ProGenEDA/ProGenEDA-DEV/proteus/experiments/runs/2026-07-17_executable_gate_overlay_trial/current_app_gate_bridge/ss/H02_8/H02_8_G_cold_open_2.png

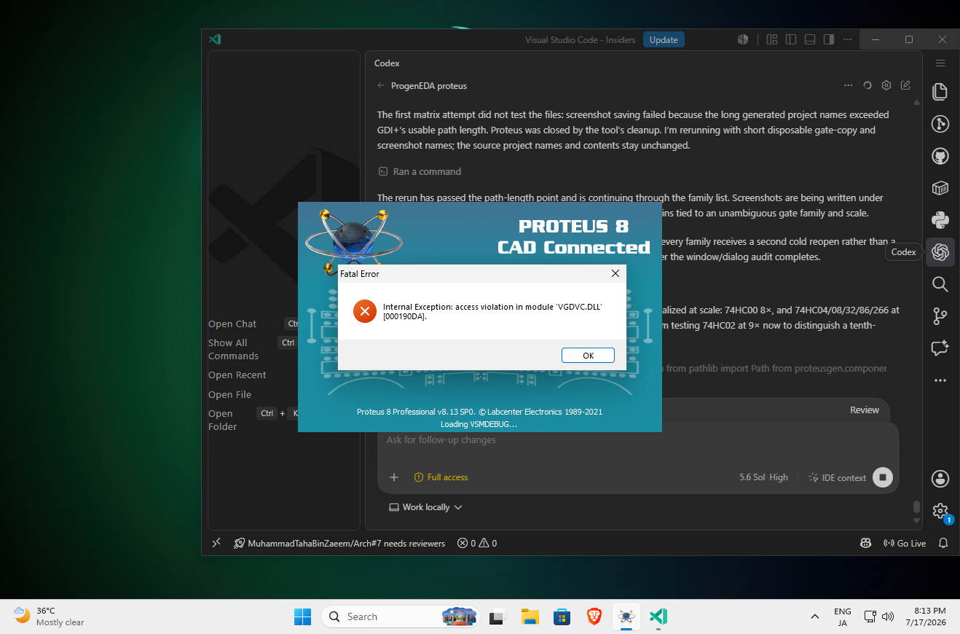
proteus/experiments/runs/2026-07-17_executable_gate_overlay_trial/current_app_gate_bridge/ss/H02_8/H02_8_G_cold_open_2.png
