ProGenEDA/ProGenEDA-DEV/showcase/EasyEDA_10_Most_Complex_2026_07_19/README.md

# EasyEDA Top 10 Complex Showcase

These are ten distinct, highest-complexity named application archetypes freshly
generated on 2026-07-19 through the latest portable `progen-easyeda` executable
from the EasyEDA website handoff, in `combination` routing mode. Every listed
native `.eprj` has a passing pipeline and independent validation report.

Open the linked `.eprj` directly in EasyEDA Pro. Each generated project folder
also keeps the fixed input, donor provenance, placement, routing, PCB decision,
and validation reports.

| Circuit | Components | Nets | Pins | Project |
| --- | ---: | ---: | ---: | --- |
| Multi-MCU Communications Bridge | 23 | 110 | 250 | [`Q11`](generated/2026_07_19_233505_339666_q11_dual_mcu_bridge_validation_v10/q11_dual_mcu_bridge_validation_v10.eprj) |
| Combinational and Sequential Logic Trainer | 23 | 81 | 186 | [`Q30`](generated/2026_07_19_233523_208561_q30_digital_logic_trainer_validation_v10/q30_digital_logic_trainer_validation_v10.eprj) |
| ESP32 Multi-channel PWM Controller | 20 | 80 | 187 | [`Q05`](generated/2026_07_19_233525_353656_q05_esp32_pwm_controller_validation_v10/q05_esp32_pwm_controller_validation_v10.eprj) |
| STM32 Precision Data Acquisition Unit | 19 | 73 | 169 | [`Q10`](generated/2026_07_19_233529_347101_q10_stm32_data_acquisition_validation_v10/q10_stm32_data_acquisition_validation_v10.eprj) |
| ATmega Logic Sequencer | 19 | 63 | 152 | [`Q07`](generated/2026_07_19_233537_870979_q07_atmega_logic_sequencer_validation_v10/q07_atmega_logic_sequencer_validation_v10.eprj) |
| ESP32 Environmental Data Logger | 19 | 63 | 148 | [`Q01`](generated/2026_07_19_233541_072041_q01_esp32_environment_logger_validation_v10/q01_esp32_environment_logger_validation_v10.eprj) |
| Shift Register LED Display Driver | 19 | 52 | 128 | [`Q23`](generated/2026_07_19_233546_585906_q23_shift_register_display_validation_v10/q23_shift_register_display_validation_v10.eprj) |
| ESP32 OLED Control Panel | 18 | 64 | 141 | [`Q04`](generated/2026_07_19_233548_034172_q04_esp32_oled_panel_validation_v10/q04_esp32_oled_panel_validation_v10.eprj) |
| STM32 CAN Control Node | 18 | 57 | 138 | [`Q08`](generated/2026_07_19_233553_642171_q08_stm32_can_controller_validation_v10/q08_stm32_can_controller_validation_v10.eprj) |
| ATmega USB Serial Controller | 17 | 59 | 140 | [`Q06`](generated/2026_07_19_233601_752383_q06_atmega_usb_controller_validation_v10/q06_atmega_usb_controller_validation_v10.eprj) |
