ProGenEDA/ProGenEDA-DEV/showcase/KiCad_10_Most_Complex_2026_07_19/README.md

# KiCad Top 10 Complex Showcase

These are ten distinct, high-complexity production-validation circuits freshly
generated on 2026-07-19 through the final
`progen-kicad-portable-2026_07_17_kq26_clearance_v1` executable in
`combination` routing mode. Each listed project has a passing
`final_validation_report.json`; PCB output is present only where the bounded
physical stage accepted it.

Open the listed `.kicad_pro` project file. Every project also retains its input,
placement/routing data, expected-net report, final report, and internal output
artifacts beside it.

| Circuit | Components | Nets | Pins | Project |
| --- | ---: | ---: | ---: | --- |
| Maker Logic and Display Console | 89 | 56 | 275 | [`KQ34V10`](final_individual_runs/progen_kicad_executable_run_2026_07_19_233002_kq34v10_top10_showcase_v1/generation/projects/kq34v10/OPEN_THIS_PROJECT__kq34v10__COMBINATION.kicad_pro) |
| Maker Audio Instrument | 85 | 48 | 217 | [`KQ33V10`](final_individual_runs/progen_kicad_executable_run_2026_07_19_232851_kq33_top10_showcase_v1/generation/projects/kq33v10/OPEN_THIS_PROJECT__kq33v10__COMBINATION.kicad_pro) |
| IoT Sensor and Display Controller | 80 | 54 | 275 | [`KQ39V10`](final_individual_runs/progen_kicad_executable_run_2026_07_19_233049_kq39v10_top10_showcase_v1/generation/projects/kq39v10/OPEN_THIS_PROJECT__kq39v10__COMBINATION.kicad_pro) |
| Maker CAN and RS485 Field Gateway | 80 | 47 | 217 | [`KQ32V10`](final_individual_runs/progen_kicad_executable_run_2026_07_19_233056_kq32v10_top10_showcase_v1/generation/projects/kq32v10/OPEN_THIS_PROJECT__kq32v10__COMBINATION.kicad_pro) |
| ESP32 Sensor and Actuator Controller | 75 | 45 | 211 | [`KQ35V10`](final_individual_runs/progen_kicad_executable_run_2026_07_19_233220_kq35v10_top10_showcase_v1/generation/projects/kq35v10/OPEN_THIS_PROJECT__kq35v10__COMBINATION.kicad_pro) |
| Powered Maker Development Platform | 69 | 35 | 171 | [`KQ31V10`](final_individual_runs/progen_kicad_executable_run_2026_07_19_233228_kq31v10_top10_showcase_v1/generation/projects/kq31v10/OPEN_THIS_PROJECT__kq31v10__COMBINATION.kicad_pro) |
| Industrial Sensor Communications Gateway | 66 | 41 | 200 | [`KQ37V10`](final_individual_runs/progen_kicad_executable_run_2026_07_19_233311_kq37v10_top10_showcase_v1/generation/projects/kq37v10/OPEN_THIS_PROJECT__kq37v10__COMBINATION.kicad_pro) |
| Arduino Field Motion Controller | 63 | 50 | 182 | [`KQ10V10`](final_individual_runs/progen_kicad_executable_run_2026_07_19_233331_kq10v10_top10_showcase_v1/generation/projects/kq10v10/OPEN_THIS_PROJECT__kq10v10__COMBINATION.kicad_pro) |
| Industrial Power and Motion Controller | 62 | 39 | 161 | [`KQ40V10`](final_individual_runs/progen_kicad_executable_run_2026_07_19_233348_kq40v10_top10_showcase_v1/generation/projects/kq40v10/OPEN_THIS_PROJECT__kq40v10__COMBINATION.kicad_pro) |
| Sensor Hub with Logic Display | 58 | 36 | 202 | [`KQ21V10`](final_individual_runs/progen_kicad_executable_run_2026_07_19_233353_kq21v10_top10_showcase_v1/generation/projects/kq21v10/OPEN_THIS_PROJECT__kq21v10__COMBINATION.kicad_pro) |

`final_individual_runs/` is the curated current set. `generated/` preserves an
earlier partial batch attempt and is not part of the showcase selection.
