ProGenEDA/ProGenEDA-DEV/kicad/examples/schematic_terminal_visual_run_2026_07_12_071500_final_complex20_v19/README.md

# Final JSON To KiCad Terminal Project Run

This folder is an immutable generated record. It takes connected final JSON files, runs the arrangement decider, beautifier, routing/terminal planner, and KiCad backend emitter, then writes openable KiCad projects with real embedded symbols plus wire objects. Terminal/local-label objects are only valid when the run is generated in terminal or combination mode.

The wire planner is fed exact KiCad source-symbol pin points through `routing_inputs/` when those pins can be resolved. The wire maker uses the same source-backed KiCad pin geometry when possible. Any unresolved pin aliases, unroutable nets, strict-wire connectivity violations, local expected-net comparison failures, wire crossings, and wire/component body contacts are recorded in each project manifest.

Each project also has a two-artifact output boundary under `outputs/<circuit_id>/`: `user_project/PROGEN_KICAD_PROJECT.zip` is the only user-downloadable export, while `internal/internal_bundle.zip` is backend-only metadata containing the main input JSON, all generated stage JSON, validation reports, and retained arrangement variants with the accepted variant marked.
