ProGenEDA/ProGenEDA-DEV/proteus/active/docs/README.md

# Proteus Active Documentation

> **Current implementation.** This folder is the active Proteus documentation index
> for the repaired component placer, shared terminal route, grid-attached wire
> contract, automated validation workflow, value/properties editor, and
> portable executable.

Updated: 2026-07-16

Start with [`../README.md`](../README.md) for commands, support boundaries, the
runtime donor policy, release executable, and links to experiments/archive.

## Current operational documents

- [`progen_eda_canonical_pipeline.md`](progen_eda_canonical_pipeline.md) —
  owner-defined stage order and implementation map.
- [`architecture.md`](architecture.md) — replaceable stage contracts, catalogue
  policy, and current architecture decisions.
- [`component_placer_pipeline.md`](component_placer_pipeline.md) — the
  donor-backed placement contract.
- [`beautifier.md`](beautifier.md) — coordinate/arrangement stage contract.
- [`validator_design.md`](validator_design.md) — cumulative validation stages.
- [`generator_design.md`](generator_design.md) — generator responsibilities.
- [`current_limitations_bridges_costs_and_roadmap.md`](current_limitations_bridges_costs_and_roadmap.md)
  — promoted boundaries and next work.
- [`prompts/planner_prompt.md`](prompts/planner_prompt.md) — current prompt
  planning input.

## Active evidence and validation

- [`../knowledge/component_catalog_v0.json`](../knowledge/component_catalog_v0.json)
  — current catalogue/profile source.
- [`../knowledge/terminal_placement_preflight_checklist.md`](../knowledge/terminal_placement_preflight_checklist.md)
  — required donor/loader checklist before terminal changes.
- [`../knowledge/value_and_properties_editor_preflight_2026_07_16.md`](../knowledge/value_and_properties_editor_preflight_2026_07_16.md)
  — value editor evidence.
- [`../evidence/registry/active_donor_closure.json`](../evidence/registry/active_donor_closure.json)
  — deterministic runtime/test donor closure.
- [`../REPOSITORY_MAP.md`](../REPOSITORY_MAP.md) — active/experiment/archive map
  and generated hashes.

Historical reports, older handoffs, and donor-learning notes were deliberately
preserved unchanged under [`../../archive/docs`](../../archive/docs), while
dated generated packs and their runners live under
[`../../experiments`](../../experiments).
