ProGenEDA/ProGenEDA-DEV/proteus/active/release/README.md

# ProgenProteus.exe

> **Current implementation.** The active Proteus system includes repaired component placement, unified terminal placement, grid-attached short-wire behavior, automated local Proteus validation, the value/properties editor, the portable executable, and consolidated active documentation.
>
> **Active-location update — 2026-07-16.** This is current Proteus material. Pre-consolidation root-relative paths translate as follows: `src/`, `knowledge/`, `fixtures/`, `schemas/`, `examples/`, and active `tools/` are below `proteus/active/`; `experiments/` is below `proteus/experiments/runs/`; and `proteus_ic/{donors,registry}` is now `proteus/active/evidence/{donors,registry}`. For current commands, support boundaries, and limitations, start at `proteus/active/README.md`.

`ProgenProteus.exe` is the portable Windows console application for the
implemented Proteus pipeline:

`component placement -> beautification -> shared terminal placement -> optional post-terminal value/properties edit`

It bundles the locked mega donor, terminal templates, and the metadata needed
by the shared placer. It does not bundle or call any KiCad code.

## Run

```powershell
.\ProgenProteus.exe generate ..\examples\progen_proteus_r_c_value_edit.json --output .\r_c_terminalized.pdsprj
```

Other commands:

```powershell
.\ProgenProteus.exe --help
.\ProgenProteus.exe inspect .\r_c_terminalized.pdsprj
.\ProgenProteus.exe edit-values .\r_c_terminalized.pdsprj --edits edits.json --output .\edited.pdsprj
```

The executable refuses physical-net requests because the shared Proteus Wire
Maker has not yet been implemented. It also rejects unsafe zero-length
terminal-to-pin wires and, by default, any request that would silently leave a
family unterminated. Use `--allow-unterminalized` only for an intentional
mixed control project.

`NPN` is included in this build's locked non-IC terminal route. Its fresh
executable evidence covers solo `1x`, `9x`, and `15x`, asymmetric native mixes,
existing catalogue-backed non-IC mixes, and a `15x` NPN/diode/resistor/capacitor
stress mix. Each emitted NPN terminal has a grid-aligned, nonzero short WIRE
to its exact pin. IC/display mixtures remain on their independently verified
routes and are not widened by this NPN promotion.

`PNP` is included in this build's locked non-IC terminal route too. Its
`BASE`/`COLLECTOR`/`EMITTER` pin attachments passed fresh `1x`, `9x`, `15x`,
asymmetric, heterogeneous, and latest-executable `15x` stress gates. The
portable executable also uses a bounded temporary work-directory prefix, so a
descriptive output filename cannot consume the Windows path budget before
placement and terminalization begin.

`NMOSFET` is included in this build's locked non-IC terminal route. Its
donor-proven `DRAIN`/`SOURCE` right-side and `GATE` left-side attachment units
passed the full staged loader proof, `1x`/`9x`/`15x` solo gates, a ratio mix,
a heterogeneous non-IC mix, and a dense 15x stress mix. Every emitted NMOSFET
terminal has a grid-aligned contact and a nonzero short WIRE to its exact pin.

`2N3904` is included in the same locked non-IC terminal route. Its accepted
combined donor proves that its `EMITTER`/`COLLECTOR`/`BASE` attachment tail
must follow the complete placed component stream. Fresh `1x`/`9x`/`15x` solos,
asymmetric and heterogeneous mixes, a dense 15-per-family mix, and a fresh
portable-executable ratio mix all passed normal open and cold reopen with
grid-aligned, nonzero terminal-to-pin WIREs.

`2N4401` is included in this build through the same shared route. Its
independent accepted donor proves its `COLLECTOR`/`EMITTER`/`BASE` tail follows
the whole placed stream. The staged 1x proof, 9x/15x solos, additive and
asymmetric ratios, a heterogeneous 24-component mix, and a dense 15-per-family
mix passed the local two-open Proteus gate. The rebuilt executable itself is
gated below before this release note is finalized.

For a canonical placement control, optional `terminal_label_projection`
metadata assigns source-circuit node names to the exposed terminals before
they are serialized. This changes labels (for example `VIN`, `G0`, `VOUT`),
not physical routing: arbitrary `nets`, `wires`, `connections`, and `netlist`
requests remain rejected until the shared Wire Maker is accepted.

Build: 2026-07-18 (2N4401 terminal-route promotion)

SHA-256: `D32D06E4935EAAC1E8439807472871E1A706F299AE4A1DF7839CBC4E8534FEAD`

## Screenshot-proven gate bridge

The current executable can terminalize one gate family per project through the
current locked-mega component placer and the shared catalogue terminal route;
it does not use the historic E001 IC envelope. Supply
`terminal_label_projection` in the ordinary circuit JSON to name the exposed
pins semantically. Screenshot-backed cold-open and cold-reopen tests prove the
following current ceilings: `74HC00=8`, `74HC02=4`, and
`74HC04/74HC08/74HC32/74HC86/74HC266=10` component groups. Requests above
those ceilings, multiple gate families, or gates mixed with another family are
rejected rather than returning a project whose devices may silently disappear.

The exact executable 74HC08 10x evidence and cold-open screenshots are in
`proteus/experiments/runs/2026-07-17_executable_gate_overlay_trial/`.
