ProGenEDA/ProGenEDA-DEV/kicad/examples/progen_kicad_executable_run_2026_07_13_002708_pcb_near_complete_rescue_2026_07_13_group_a/README.md

# ProGenEDA KiCad Executable Run

This immutable folder was produced by the single executable wrapper. It first validates/fixes input JSON into canonical main JSON, then runs the KiCad combination/terminal/wire project pipeline. The generated project run contains user-project zips and internal-only bundles.
