ProGenEDA/ProGenEDA-DEV/kicad/examples/placer_run_2026_07_02_proteus_style_aliases_v2/README.md

# KiCad Component Placer Run

Run label: `proteus_style_aliases_v2`

This folder was generated by `kicad.pipeline.kicad_component_placer`.
Generated project subfolders are immutable records; create a new run for any changed output.

## Purpose

This is the fixed rerun for the 2026-07-02 Proteus-style alias expansion. It
uses the same input set as v1 and keeps the generated v1 project untouched as a
failed evidence record.

## Change From v1

`74HC266` is mapped to `4xxx:4077`, a real CMOS quad XNOR KiCad symbol with a
separate power unit. This replaced the first substitute, `74xx_IEEE:74LS266`,
which produced placement-only ERC `different_unit_net` violations because of
repeated power pins across gate units.

## Result

- Input: `inputs/proteus_style_component_kind_smoke.json`
- Project: `projects/proteus_style_component_kind_smoke`
- Open: `projects/proteus_style_component_kind_smoke/OPEN_THIS_PROJECT__proteus_style_component_kind_smoke__PLACER.kicad_pro`
- Component count: 55
- Symbol instance count: 92
- Pipeline status: passed
- KiCad quality check: passed
- Netlist export: passed

The symbol instance count is higher than the component count because several
real KiCad logic symbols are multi-unit parts. Generated schematic symbols are
real flattened KiCad library symbols; no `ProgenPlace` placeholder symbols are
expected in this run.

## Validation

Command:

```bash
python -m kicad.automation.quality_check kicad/examples/placer_run_2026_07_02_proteus_style_aliases_v2 --kicad-cli kicad/.local/bin/kicad-cli --export-netlist
```

Result:

- Static schematic check: passed
- KiCad ERC load: passed
- Blocking ERC violations: 0
- Placement-only tolerated ERC violations: 675
- Netlist export: passed, 217564 bytes
