ProGenEDA/ProGenEDA-DEV/kicad/examples/placer_pack/README.md

# Historical Placer Input Pack

This folder is an older active 20-circuit input pack. It is kept as a record and
must not be regenerated in place.

Superseded by:

```text
kicad/examples/placer_run_2026_07_01_baseline_c11_spacing_fix_v2/inputs
```

Reason: the newer run uses the same v0.2 partial CircuitIR input shape, but was
generated through the immutable run-folder workflow and paired with the C11
spacing fix.
