ProGenEDA/ProGenEDA-DEV/kicad/examples/placer_projects/README.md

# Historical Placer Project Pack

This folder is an older active 20-circuit project pack. The user opened these
projects and reported that the real symbols appeared correctly, except C11 had
the Micro USB connector and protection IC too close together.

Do not overwrite this folder. It is kept as the record of that result.

Superseded by:

```text
kicad/examples/placer_run_2026_07_01_baseline_c11_spacing_fix_v2/projects
```

The newer run widens the placer spacing and keeps C11's nearby components apart.
