ProGenEDA/ProGenEDA-DEV/kicad/examples/placer_run_2026_07_01_stress_limit_suite_v2/README.md

# Stress And Limit Suite V2

Date: 2026-07-01

## What Was Tested

Generated the requested stress and limit suite with the widened real-symbol
spacing heuristic:

- Test 1 through Test 10.
- Limit A through Limit D.
- Limit E at 25, 50, 75, 100, 150, 200, 300, and 400 components.

## Outcome

Passed KiCad CLI quality:

- 22 schematics generated.
- 2747 requested components.
- 22 schematics checked.
- 22 passed.
- 0 failed.

ERC still reports tolerated placement-stage unconnected/undriven pins because
this is still placer-only. There are no blocking ERC failures in this run.

## Next

Use this as the current placer stress baseline.
