ProGenEDA/ProGenEDA-DEV/kicad/examples/final_json_wired_project_run_2026_07_05_144934_node_spec_n07_no_unrouted_probe_v1/INTERRUPTED_ATTEMPT.md

# Interrupted Attempt

This folder records an interrupted N07-only routing probe from 2026-07-05.

The run was stopped before `run_manifest.json` and project files were written.
It was superseded by:

- `final_json_wired_project_run_2026_07_05_145925_node_spec_n07_no_unrouted_probe_v2`, which completed N07 with zero unrouted and zero partial wire nets.
- `final_json_wired_project_run_2026_07_05_zeroroute_v8_pin_escape_motion`, which completed all 11 node-spec circuits with zero unrouted and zero partial wire nets.

Keep this folder as a record only; do not use it as a validation source.
