ProGenEDA/ProGenEDA-DEV/kicad/examples/pcb_release_evidence_run_2026_07_11_230157_pcb_600_combination_v4/mj001/drill_report.txt

Drill report for OPEN_THIS_PROJECT__mj001__COMBINATION.kicad_pcb
Created on 2026-07-11T23:01:59

Copper Layer Stackup:
    =============================================================
    L1 :  F.Cu                      front
    L2 :  B.Cu                      back

Drill file 'OPEN_THIS_PROJECT__mj001__COMBINATION.drl' contains
    plated through holes:
    =============================================================
    T1  0.400mm  0.0157"  (23 holes))
    T2  0.800mm  0.0315"  (58 holes))
    T3  0.900mm  0.0354"  (10 holes))
    T4  1.000mm  0.0394"  (42 holes))

    Total plated holes count 133

Not plated through holes are merged with plated holes
    unplated through holes:
    =============================================================

    Total unplated holes count 0
