ProGenEDA/ProGenEDA-DEV/kicad/examples/pcb_release_evidence_run_2026_07_11_230157_pcb_600_combination_v4/mj002/drill_report.txt

Drill report for OPEN_THIS_PROJECT__mj002__COMBINATION.kicad_pcb
Created on 2026-07-11T23:02:02

Copper Layer Stackup:
    =============================================================
    L1 :  F.Cu                      front
    L2 :  B.Cu                      back

Drill file 'OPEN_THIS_PROJECT__mj002__COMBINATION.drl' contains
    plated through holes:
    =============================================================
    T1  0.400mm  0.0157"  (8 holes))
    T2  0.800mm  0.0315"  (84 holes))
    T3  0.900mm  0.0354"  (18 holes))
    T4  1.100mm  0.0433"  (5 holes))
    T5  1.300mm  0.0512"  (2 holes))

    Total plated holes count 117

Not plated through holes are merged with plated holes
    unplated through holes:
    =============================================================

    Total unplated holes count 0
