ProGenEDA/ProGenEDA-DEV/kicad/examples/pcb_release_evidence_run_2026_07_11_230157_pcb_600_combination_v4/n01/drill_report.txt

Drill report for OPEN_THIS_PROJECT__n01__COMBINATION.kicad_pcb
Created on 2026-07-11T23:02:05

Copper Layer Stackup:
    =============================================================
    L1 :  F.Cu                      front
    L2 :  B.Cu                      back

Drill file 'OPEN_THIS_PROJECT__n01__COMBINATION.drl' contains
    plated through holes:
    =============================================================
    T1  0.200mm  0.0079"  (12 holes))
    T2  0.400mm  0.0157"  (26 holes))
    T3  0.800mm  0.0315"  (32 holes))
    T4  0.900mm  0.0354"  (4 holes))
    T5  1.000mm  0.0394"  (4 holes))

    Total plated holes count 78

Not plated through holes are merged with plated holes
    unplated through holes:
    =============================================================

    Total unplated holes count 0
