ProGenEDA/ProGenEDA-DEV/kicad/examples/pcb_release_evidence_run_2026_07_11_230157_pcb_600_combination_v4/n02/drill_report.txt

Drill report for OPEN_THIS_PROJECT__n02__COMBINATION.kicad_pcb
Created on 2026-07-11T23:02:09

Copper Layer Stackup:
    =============================================================
    L1 :  F.Cu                      front
    L2 :  B.Cu                      back

Drill file 'OPEN_THIS_PROJECT__n02__COMBINATION.drl' contains
    plated through holes:
    =============================================================
    T1  0.400mm  0.0157"  (20 holes))
    T2  0.750mm  0.0295"  (9 holes))
    T3  0.800mm  0.0315"  (34 holes))
    T4  0.900mm  0.0354"  (2 holes))
    T5  1.000mm  0.0394"  (41 holes))
    T6  1.100mm  0.0433"  (11 holes))
    T7  1.300mm  0.0512"  (12 holes))

    Total plated holes count 129

Not plated through holes are merged with plated holes
    unplated through holes:
    =============================================================

    Total unplated holes count 0
