ProGenEDA/ProGenEDA-DEV/proteus/experiments/runs/mixed_ic_catalogue_compatible_1x_v1_temp_2026_07_15/diagnostics/mixed_tail_hypothesis/04_local_proteus_gate/M04_7447_PLUS_RC_MIXED_TAIL_DISPATCH_NORMAL.png

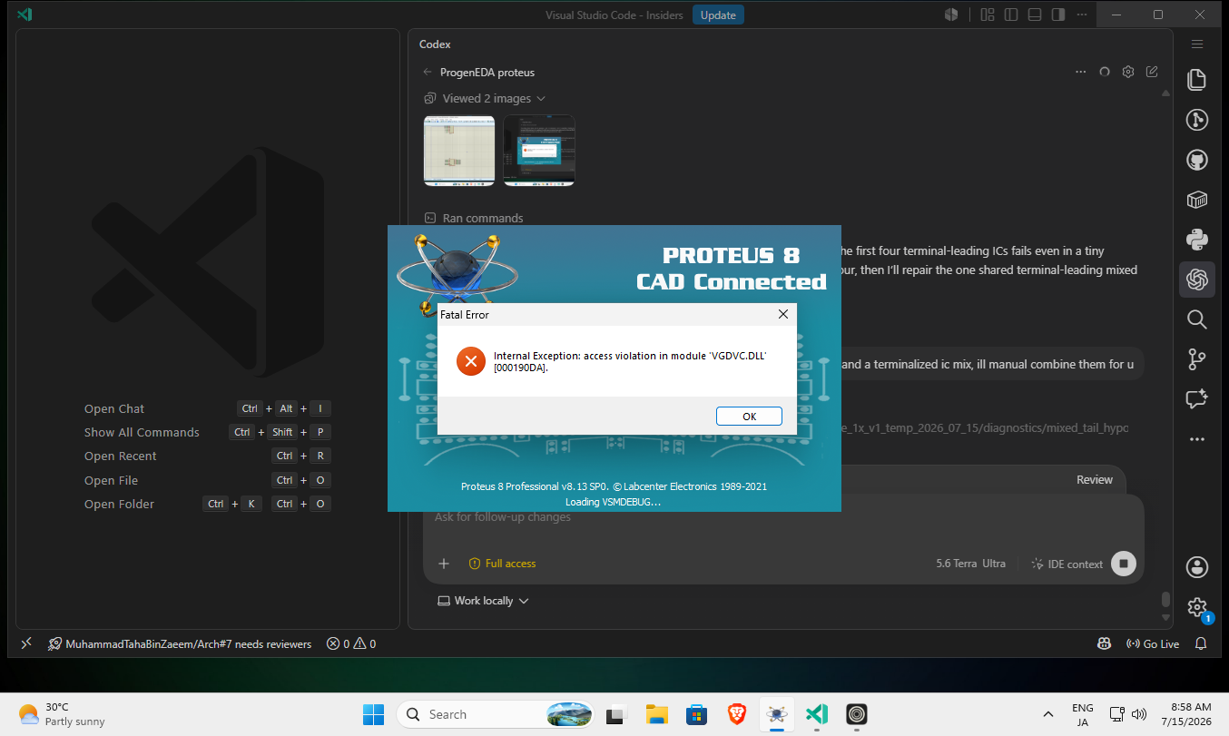
proteus/experiments/runs/mixed_ic_catalogue_compatible_1x_v1_temp_2026_07_15/diagnostics/mixed_tail_hypothesis/04_local_proteus_gate/M04_7447_PLUS_RC_MIXED_TAIL_DISPATCH_NORMAL.png
