ProGenEDA/ProGenEDA-DEV/artifacts/proteus_v9_recovery/files/R21_E001_B02_ORDER_FIXED_GENERATION__README_TEST_FIRST.txt

B02-order fixed generation pack.

E001 is the project base. B02 is used as schema/reference for terminal-resistor-wire ordering and 2-character terminal label records.

Test order:
1 CONTROL_E001_EMPTY_BASE.pdsprj
2 TEST_B02_ORDER_R1_TERMINAL_RESISTOR_TERMINAL.pdsprj
3 TEST_B02_ORDER_R2_SERIES_TERMINALS.pdsprj
4 FINAL_B02_ORDER_R21_7PAR7_PLUS_7SERIES_TERMINALS.pdsprj
