ProGenEDA/ProGenEDA-DEV/artifacts/proteus_v9_recovery/files/R21_E001_E019_GROUP_ORDER_GENERATION__README_TEST_FIRST.txt

E019 group-order generation pack.

These are E001-based projects. E019 is used only as the one-resistor terminal--resistor--terminal record schema donor.

Test order:
1. CONTROL_E001_EMPTY_BASE.pdsprj
2. TEST_E019_ORDER_R1_TERMINAL_RESISTOR_TERMINAL.pdsprj
3. TEST_E019_ORDER_R2_SERIES_TERMINALS.pdsprj
4. FINAL_E019_ORDER_R21_7PAR7_PLUS_7SERIES_TERMINALS.pdsprj

The final topology is two 7-resistor series branches in parallel, followed by seven more resistors in series.
