ProGenEDA/ProGenEDA-DEV/proteus/experiments/runs/bidirectional_v3_prelock_temp_2026_06_07/README_TEST_ORDER.txt

BIDIRECTIONAL V3 PRE-LOCK REGRESSION PACK

T01 20-resistor mesh with power/ground
T02 six-component resistor/capacitor network
T03 four-branch capacitor network
T04 four-branch inductor network
T05 mixed RCL Wheatstone bridge
T06 corrected 21-component RCL topology
T07 DC-current source with parallel RCL/RC loads
T08 AC-voltage source with RC/LC/R branches
T09 one clean DCV source driving an RCL bridge
T10 two clean DCV sources driving a larger shared-return network
T11 three clean DCV sources sharing D0

Report for each case: opens without warnings, visual direction, and simulation result.
