ProGenEDA/ProGenEDA-DEV/proteus/experiments/runs/bidirectional_v2_orientation_dcv_temp_2026_06_07/README_TEST_ORDER.txt

BIDIRECTIONAL V2 ORIENTATION + CLEAN DCV TEST PACK

T00A: exact manual 1DCV donor control
T00B: exact manual 2DCV donor control
T01: resistor with a true 180-degree bidirectional input and 0-degree output
T02: one donor-native DCV source plus RCL load; corrected source CDB pin map
T03: two donor-native DCV sources on disconnected negative nets (diagnostic)
T04: two donor-native DCV sources sharing negative net D0 (expected simulation-safe topology)

For every case report: opens without bad-object warning, visual direction, and simulation result.
T03 may still report a singular matrix because it intentionally contains two disconnected islands.
