ProGenEDA/ProGenEDA-DEV/proteus/experiments/runs/beautifier_v1_temp_2026_06_06/README_TEST_ORDER.txt

BEAUTIFIER V1 REPRESENTATIVE TEST PACK

For each T01-T11 folder, open LEGACY first and then BEAUTIFY.
Confirm both projects open and simulate the same circuit.
Judge only placement: branch separation, source proximity, component overlap, and sheet fit.
This pack does not add standalone buses, junctions, or routed wires.

Recommended order:
T01 multi-step divider
T02 parallel/current divider
T03 series-parallel
T04 delta
T05 star
T06 Wheatstone
T07 R-2R ladder
T08 corrected 21-component circuit
T09 single DC voltage source
T10 mixed DC voltage/current sources
T11 single AC voltage source
