ProGenEDA/ProGenEDA-DEV/proteus/experiments/runs/capacitor_v11_networks_temp_2026_05_31/README_TEST_ORDER.txt

Capacitor V11 network diagnostics.

Open in order:

1. CAP_V11_T01_6C_SAME_TOPOLOGY_AS_6R/CAP_V11_T01_6C_SAME_TOPOLOGY_AS_6R.pdsprj
2. CAP_V11_T02_21C_SAME_TOPOLOGY_AS_R21/CAP_V11_T02_21C_SAME_TOPOLOGY_AS_R21.pdsprj

Report whether each opens, whether all capacitors are visible, and any exact Proteus error text.
