ProGenEDA/ProGenEDA-DEV/proteus/experiments/runs/capacitor_v12_requested15_temp_2026_05_31/README_TEST_ORDER.txt

Capacitor V12 requested 15 network diagnostics.

Open in order:

01. 01_SIMPLE_LOOP/01_SIMPLE_LOOP.pdsprj
02. 02_SERIES_CIRCUIT/02_SERIES_CIRCUIT.pdsprj
03. 03_PARALLEL_CIRCUIT/03_PARALLEL_CIRCUIT.pdsprj
04. 04_SERIES_PARALLEL_COMBO/04_SERIES_PARALLEL_COMBO.pdsprj
05. 05_BASIC_VOLTAGE_DIVIDER/05_BASIC_VOLTAGE_DIVIDER.pdsprj
06. 06_MULTI_STEP_VOLTAGE_DIVIDER/06_MULTI_STEP_VOLTAGE_DIVIDER.pdsprj
07. 07_CURRENT_DIVIDER/07_CURRENT_DIVIDER.pdsprj
08. 08_DELTA_NETWORK/08_DELTA_NETWORK.pdsprj
09. 09_STAR_Y_NETWORK/09_STAR_Y_NETWORK.pdsprj
10. 10_DELTA_TO_STAR_SETUP/10_DELTA_TO_STAR_SETUP.pdsprj
11. 11_WHEATSTONE_BRIDGE/11_WHEATSTONE_BRIDGE.pdsprj
12. 12_BALANCED_WHEATSTONE_BRIDGE/12_BALANCED_WHEATSTONE_BRIDGE.pdsprj
13. 13_UNBALANCED_WHEATSTONE_BRIDGE/13_UNBALANCED_WHEATSTONE_BRIDGE.pdsprj
14. 14_H_BRIDGE_RESISTOR_VERSION/14_H_BRIDGE_RESISTOR_VERSION.pdsprj
15. 15_R_2R_LADDER_NETWORK/15_R_2R_LADDER_NETWORK.pdsprj

Report the first failure, any exact Proteus error text, and whether the visible capacitor count matches each case.
