ProGenEDA/ProGenEDA-DEV/proteus/experiments/runs/capacitor_v4_temp_2026_05_30/README_TEST_ORDER.txt

Capacitor V4 temporary diagnostics.

Open in this order and stop at the first failure:

1. CAP_V4_T01_EXACT_T01_SINGLE_CAP/CAP_V4_T01_EXACT_T01_SINGLE_CAP.pdsprj
2. CAP_V4_T02_EXACT_T02_TERMINAL_CAP_TERMINAL/CAP_V4_T02_EXACT_T02_TERMINAL_CAP_TERMINAL.pdsprj
3. CAP_V4_T03_PATCHED_C2_SAME_POSITION/CAP_V4_T03_PATCHED_C2_SAME_POSITION.pdsprj
4. CAP_V4_T04_TRANSLATED_T02_GROUP/CAP_V4_T04_TRANSLATED_T02_GROUP.pdsprj
5. CAP_V4_T05_TWO_ISOLATED_CAPS/CAP_V4_T05_TWO_ISOLATED_CAPS.pdsprj

Report the first failing case and the exact Proteus error.
