ProGenEDA/ProGenEDA-DEV/proteus/experiments/runs/capacitor_v5_cap3_temp_2026_05_30/README_TEST_ORDER.txt

Capacitor V5 cap3 temporary diagnostics.

Open in order. T03/T04 are paired; if T03 fails, still test T04.

1. CAP_V5_T01_EXACT_CAP3_TRANSPLANT/CAP_V5_T01_EXACT_CAP3_TRANSPLANT.pdsprj
2. CAP_V5_T02_REGENERATED_CAP3_EXACT/CAP_V5_T02_REGENERATED_CAP3_EXACT.pdsprj
3. CAP_V5_T03_TWO_FREE_CAPS_ZERO_FLAGS/CAP_V5_T03_TWO_FREE_CAPS_ZERO_FLAGS.pdsprj
4. CAP_V5_T04_TWO_FREE_CAPS_DONOR_FLAG/CAP_V5_T04_TWO_FREE_CAPS_DONOR_FLAG.pdsprj
5. CAP_V5_T05_THREE_FREE_CAPS_TRANSLATED/CAP_V5_T05_THREE_FREE_CAPS_TRANSLATED.pdsprj
6. CAP_V5_T06_THREE_FREE_CAPS_RENAMED/CAP_V5_T06_THREE_FREE_CAPS_RENAMED.pdsprj

Report which cases open, which case first errors, and the exact Proteus error text.
