ProGenEDA/ProGenEDA-DEV/proteus/experiments/runs/capacitor_v8_terminal_order_temp_2026_05_31/README_TEST_ORDER.txt

Capacitor V8 terminal order diagnostics.

Open in order. T01 should reproduce a case you already saw working. For T02-T06, report whether the file opens and whether it shows two capacitors with N1/N2 and N3/N4 terminals.

1. CAP_V8_T01_V7_T05_REPRO_FREE_FIRST_TERMINAL_LAST/CAP_V8_T01_V7_T05_REPRO_FREE_FIRST_TERMINAL_LAST.pdsprj
2. CAP_V8_T02_TWO_TERMINAL_RES_SUFFIX_V9_ORDER_ZERO_FLAGS/CAP_V8_T02_TWO_TERMINAL_RES_SUFFIX_V9_ORDER_ZERO_FLAGS.pdsprj
3. CAP_V8_T03_TWO_TERMINAL_RES_SUFFIX_V9_ORDER_DONOR_FLAG/CAP_V8_T03_TWO_TERMINAL_RES_SUFFIX_V9_ORDER_DONOR_FLAG.pdsprj
4. CAP_V8_T04_TWO_TERMINAL_CAP_SUFFIX_V9_ORDER_ZERO_FLAGS/CAP_V8_T04_TWO_TERMINAL_CAP_SUFFIX_V9_ORDER_ZERO_FLAGS.pdsprj
5. CAP_V8_T05_TWO_TERMINAL_CAP_SUFFIX_V9_ORDER_DONOR_FLAG/CAP_V8_T05_TWO_TERMINAL_CAP_SUFFIX_V9_ORDER_DONOR_FLAG.pdsprj
6. CAP_V8_T06_TWO_TERMINAL_RES_SUFFIX_V9_ORDER_VERTICAL_STAGGER/CAP_V8_T06_TWO_TERMINAL_RES_SUFFIX_V9_ORDER_VERTICAL_STAGGER.pdsprj
