ProGenEDA/ProGenEDA-DEV/proteus/experiments/runs/dc_mixed_sources_v7_all3_records_temp_2026_06_04/README_TEST_ORDER.txt

DC_MIXED_SOURCES_V7_ALL3_RECORDS_TEMP_2026_06_04

Open in order:
1. DCMS_V7_T00_ALL3_DONOR_COPY.pdsprj
2. DCMS_V7_T01_ALL3_TRANSPLANT_E001.pdsprj
3. DCMS_V7_T02_SOURCE_ONLY_PASSIVE_CDB.pdsprj
4. DCMS_V7_T03_SOURCE_ONLY_SOURCEPIN_CDB.pdsprj
5. DCMS_V7_T04_REQUESTED1_PASSIVE_CDB.pdsprj
6. DCMS_V7_T05_REQUESTED1_SOURCEPIN_CDB.pdsprj
7. DCMS_V7_T06_REQUESTED2_SOURCEPIN_CDB.pdsprj
8. DCMS_V7_T07_REQUESTED3_SOURCEPIN_CDB.pdsprj
9. DCMS_V7_T08_REQUESTED4_SOURCEPIN_CDB.pdsprj
10. DCMS_V7_T09_REQUESTED5_SOURCEPIN_CDB.pdsprj

T02/T03 isolate all-source donor VSOURCE/CSOURCE records without R/C/L. T04/T05 test requested circuit 1 with passive vs source-pin CDB rows. T06-T09 are requested circuits 2-5 using source-pin CDB rows.
