ProGenEDA/ProGenEDA-DEV/proteus/experiments/runs/inductor_v4_power_ground_temp_2026_05_31/README_TEST_ORDER.txt

Inductor V4 power/ground lock-candidate diagnostic pack.

Open in this order:

1. IND_V4_T01_SINGLE_V0_G0_GENERATED/IND_V4_T01_SINGLE_V0_G0_GENERATED.pdsprj
2. IND_V4_T02_SERIES2_V0_G0_GENERATED/IND_V4_T02_SERIES2_V0_G0_GENERATED.pdsprj
3. IND_V4_T03_SERIES3_V0_G0_GENERATED/IND_V4_T03_SERIES3_V0_G0_GENERATED.pdsprj
4. IND_V4_T04_PARALLEL3_V0_G0_GENERATED/IND_V4_T04_PARALLEL3_V0_G0_GENERATED.pdsprj
5. IND_V4_T05_T_NETWORK_POWER_GROUND_GENERATED/IND_V4_T05_T_NETWORK_POWER_GROUND_GENERATED.pdsprj
