ProGenEDA/ProGenEDA-DEV/proteus/experiments/runs/mixed_rcl_v19_correct_21_temp_2026_06_02/README_TEST_ORDER.txt

Mixed R/C/L V19 corrected 21-circuit test pack.

Open and run netlist/simulation:
1. RCL_V19_T01_CORRECT_21_RULE_TOPOLOGY/RCL_V19_T01_CORRECT_21_RULE_TOPOLOGY.pdsprj

This is only the corrected 21 case. Do not lock the full R/C/L generator until the user confirms this case.
