ProGenEDA/ProGenEDA-DEV/proteus/experiments/runs/mixed_rcl_v4_resistor_boundary_temp_2026_06_01/README_TEST_ORDER.txt

Mixed R/C/L V4 resistor-boundary pack.

Open in order:
1. RCL_V4_T01_RL_INTERNAL_NO_POWER_FULL_CDB/RCL_V4_T01_RL_INTERNAL_NO_POWER_FULL_CDB.pdsprj
2. RCL_V4_T02_RL_POWER_NO_BRIDGE_FULL_CDB/RCL_V4_T02_RL_POWER_NO_BRIDGE_FULL_CDB.pdsprj
3. RCL_V4_T03_RL_POWER_FULL_CDB/RCL_V4_T03_RL_POWER_FULL_CDB.pdsprj
4. RCL_V4_T04_RL_POWER_E001_CDB/RCL_V4_T04_RL_POWER_E001_CDB.pdsprj
5. RCL_V4_T05_RL_POWER_RES_ONLY_CDB/RCL_V4_T05_RL_POWER_RES_ONLY_CDB.pdsprj
6. RCL_V4_T06_RL_POWER_IND_ONLY_CDB/RCL_V4_T06_RL_POWER_IND_ONLY_CDB.pdsprj
7. RCL_V4_T07_RL_POWER_IND_THEN_RES_E001_CDB/RCL_V4_T07_RL_POWER_IND_THEN_RES_E001_CDB.pdsprj
8. RCL_V4_T08_RCL_RES_THEN_CAPIND_JOINED_FULL_CDB/RCL_V4_T08_RCL_RES_THEN_CAPIND_JOINED_FULL_CDB.pdsprj
9. RCL_V4_T09_RCL_RES_THEN_CAPIND_JOINED_CAP_IND_CDB/RCL_V4_T09_RCL_RES_THEN_CAPIND_JOINED_CAP_IND_CDB.pdsprj
10. RCL_V4_T10_RCL_RESCAP_THEN_IND_RESCAP_CDB/RCL_V4_T10_RCL_RESCAP_THEN_IND_RESCAP_CDB.pdsprj

Report which cases work. T01-T07 are the most important resistor/inductor boundary probes.
