ProGenEDA/ProGenEDA-DEV/proteus/experiments/runs/mixed_rcl_v6_terminal_boundary_temp_2026_06_01/README_TEST_ORDER.txt

MIXED_RCL_V6_TERMINAL_BOUNDARY_TEMP_2026_06_01

Test in order:
1. T01 first; it should behave like the worked donor controls.
2. T02-T04: one terminal-attached family at a time with the other two as exact free donor records.
3. T05-T07: two terminal-attached families with the third as exact free donor record.
4. T08-T09: all terminal-attached with disconnected vs connected labels, resistor header.
5. T13-T14 only if T08/T09 fail; they repeat all-terminal cases with the RLC donor header.
