ProGenEDA/ProGenEDA-DEV/proteus/experiments/runs/mixed_rcl_v8_r_last_terminal_power_temp_2026_06_01/README_TEST_ORDER.txt

MIXED_RCL_V8_R_LAST_TERMINAL_POWER_TEMP_2026_06_01

Open in order:
1. T01 should reproduce the V7 passing control.
2. T02-T04 test all-terminal no-power C/L-before-R-final variants.
3. T05-T06 add the V0 power bridge and G0 endpoint to the small series case.
4. T07-T08 are the 6-component and 21-component mixed R/C/L cycle candidates.

Report the first failing case, exact error text, and whether any opened file has missing components or wrong labels.
