ProGenEDA/ProGenEDA-DEV/proteus/experiments/runs/mixed_res_cap_v1_6r_21r_temp_2026_05_31/README_TEST_ORDER.txt

Mixed resistor/capacitor V1 diagnostics.

Odd-numbered components are resistors; even-numbered components are capacitors. Both use one $TERPOWER -> $TEROUTPUT(V0) bridge and $TERGROUND(G0) right endpoints.

Open in order:

1. MIXED_V1_T01_6_COMPONENTS_ODD_R_EVEN_C/MIXED_V1_T01_6_COMPONENTS_ODD_R_EVEN_C.pdsprj
2. MIXED_V1_T02_21_COMPONENTS_ODD_R_EVEN_C/MIXED_V1_T02_21_COMPONENTS_ODD_R_EVEN_C.pdsprj

Report the first failure, any exact Proteus error text, and whether the visible odd/even R/C counts match each case.
