ProGenEDA/ProGenEDA-DEV/proteus/experiments/runs/dc_mixed_sources_v13_v0_source_geometry_temp_2026_06_05/README_TEST_ORDER.txt

DC_MIXED_SOURCES_V13_V0_SOURCE_GEOMETRY_TEMP_2026_06_05

Open in order:
1. DCMS_V13_T00_DONOR_COPY.pdsprj
2. DCMS_V13_T01_DONOR_OBJECT_GENERATED_CDB/DCMS_V13_T01_DONOR_OBJECT_GENERATED_CDB.pdsprj
3. DCMS_V13_T02_GROUP9_SUFFIXMAP_SAFE_CONTROL/DCMS_V13_T02_GROUP9_SUFFIXMAP_SAFE_CONTROL.pdsprj
4. DCMS_V13_T03_GROUP9_SOURCES_AND_V0_LOCAL/DCMS_V13_T03_GROUP9_SOURCES_AND_V0_LOCAL.pdsprj
5. DCMS_V13_T04_GROUP7_SOURCES_AND_V0_LOCAL/DCMS_V13_T04_GROUP7_SOURCES_AND_V0_LOCAL.pdsprj
6. DCMS_V13_T05_GROUP4_SOURCES_AND_V0_LOCAL/DCMS_V13_T05_GROUP4_SOURCES_AND_V0_LOCAL.pdsprj

T00/T01 are controls. T02 repeats the suffix-map boundary with WIRE-safe suffix replacement but no coordinate relocation. T03/T04/T05 move both source blocks and place the leading V0 terminal beside the voltage source.
