ProGenEDA/ProGenEDA-DEV/proteus/experiments/runs/dc_mixed_sources_v8_spliced_devices_temp_2026_06_04/README_TEST_ORDER.txt

DC_MIXED_SOURCES_V8_SPLICED_DEVICES_TEMP_2026_06_04

Open in order:
1. DCMS_V8_T00_RCL_ONLY_SPLICED_DEVICES_A/DCMS_V8_T00_RCL_ONLY_SPLICED_DEVICES_A.pdsprj
2. DCMS_V8_T01_SOURCE_ONLY_ACTUAL_SPLICED_DEVICES_A/DCMS_V8_T01_SOURCE_ONLY_ACTUAL_SPLICED_DEVICES_A.pdsprj
3. DCMS_V8_T02_SOURCE_ONLY_STRICT_SPLICED_DEVICES_A/DCMS_V8_T02_SOURCE_ONLY_STRICT_SPLICED_DEVICES_A.pdsprj
4. DCMS_V8_T03_REQUESTED1_ACTUAL_CDB_LAST_DEVICES_A/DCMS_V8_T03_REQUESTED1_ACTUAL_CDB_LAST_DEVICES_A.pdsprj
5. DCMS_V8_T04_REQUESTED1_STRICT_CDB_LAST_DEVICES_A/DCMS_V8_T04_REQUESTED1_STRICT_CDB_LAST_DEVICES_A.pdsprj
6. DCMS_V8_T05_REQUESTED1_STRICT_CDB_FIRST_DEVICES_A/DCMS_V8_T05_REQUESTED1_STRICT_CDB_FIRST_DEVICES_A.pdsprj
7. DCMS_V8_T06_REQUESTED1_STRICT_CDB_LAST_DEVICES_B/DCMS_V8_T06_REQUESTED1_STRICT_CDB_LAST_DEVICES_B.pdsprj
8. DCMS_V8_T07_REQUESTED2_STRICT_CDB_LAST_DEVICES_A/DCMS_V8_T07_REQUESTED2_STRICT_CDB_LAST_DEVICES_A.pdsprj
9. DCMS_V8_T08_REQUESTED3_STRICT_CDB_LAST_DEVICES_A/DCMS_V8_T08_REQUESTED3_STRICT_CDB_LAST_DEVICES_A.pdsprj
10. DCMS_V8_T09_REQUESTED4_STRICT_CDB_LAST_DEVICES_A/DCMS_V8_T09_REQUESTED4_STRICT_CDB_LAST_DEVICES_A.pdsprj
11. DCMS_V8_T10_REQUESTED5_STRICT_CDB_LAST_DEVICES_A/DCMS_V8_T10_REQUESTED5_STRICT_CDB_LAST_DEVICES_A.pdsprj

T00 isolates the spliced device section with only R/C/L records. T01/T02 isolate source-only records. T03-T06 compare current identity, CDB order, and device-entry order on requested circuit 1. T07-T10 are requested circuits 2-5 using the strict current identity if T04/T06 open.
