ProGenEDA/ProGenEDA-DEV/proteus/experiments/runs/ac_voltage_v1_source_diagnostics_temp_2026_06_04/ACV_V1_SOURCE_DIAGNOSTICS_TEST_BATCH/README_TEST_ORDER.txt

AC voltage V1 source diagnostics.

Open in order:
1. ACV_V1_T00_EXACT_DEFAULT_COPY/ACV_V1_T00_EXACT_DEFAULT_COPY.pdsprj
2. ACV_V1_T01_DEFAULT_TRANSPLANT_E001/ACV_V1_T01_DEFAULT_TRANSPLANT_E001.pdsprj
3. ACV_V1_T02_VARIANT_TRANSPLANT_E001/ACV_V1_T02_VARIANT_TRANSPLANT_E001.pdsprj
4. ACV_V1_T03_TWO_SOURCE_TRANSPLANT_E001/ACV_V1_T03_TWO_SOURCE_TRANSPLANT_E001.pdsprj
5. ACV_V1_T04_RCL_AV_A0_NO_SOURCE_CONTROL/ACV_V1_T04_RCL_AV_A0_NO_SOURCE_CONTROL.pdsprj
6. ACV_V1_T05_SIMPLE_LOOP_SOURCE_FIRST/ACV_V1_T05_SIMPLE_LOOP_SOURCE_FIRST.pdsprj
7. ACV_V1_T06_SIX_COMPONENT_SOURCE_FIRST/ACV_V1_T06_SIX_COMPONENT_SOURCE_FIRST.pdsprj
8. ACV_V1_T07_SIX_COMPONENT_SOURCE_LAST_LOAD_BLOCK/ACV_V1_T07_SIX_COMPONENT_SOURCE_LAST_LOAD_BLOCK.pdsprj
9. ACV_V1_T08_21_RULE_SOURCE_FIRST/ACV_V1_T08_21_RULE_SOURCE_FIRST.pdsprj
10. ACV_V1_T09_21_RULE_SOURCE_LAST_LOAD_BLOCK/ACV_V1_T09_21_RULE_SOURCE_LAST_LOAD_BLOCK.pdsprj

T05/T06/T08 test source-first VSINE insertion. T07/T09 test source-last insertion from the load donor.
