ProGenEDA/ProGenEDA-DEV/proteus/experiments/runs/beautifier_v2_source_node_temp_2026_06_07/README_TEST_ORDER.txt

BEAUTIFIER V2 SOURCE AND NODE TEST PACK

Open LEGACY first and then BEAUTIFY in each folder.
T01: confirm the two DC sources no longer overlap.
T02: confirm the AC source body, terminals, and short wires stay together.
T03: confirm repeated series node labels follow one horizontal lane.
T04: confirm the delta closure uses a separate understandable lane.
T05: confirm Wheatstone branches and shared labels are easy to follow.
All projects must still open and simulate as before.
