ProGenEDA/ProGenEDA-DEV/proteus/experiments/runs/capacitor_v10_manual_donor_temp_2026_05_31/README_TEST_ORDER.txt

Capacitor V10 manual-donor diagnostics.

Open in order:

1. CAP_V10_T01_EXACT_MANUAL_DONOR_TRANSPLANT/CAP_V10_T01_EXACT_MANUAL_DONOR_TRANSPLANT.pdsprj
2. CAP_V10_T02_REBUILT_MANUAL_EXACT/CAP_V10_T02_REBUILT_MANUAL_EXACT.pdsprj
3. CAP_V10_T03_TRANSLATED_MANUAL_ORDER/CAP_V10_T03_TRANSLATED_MANUAL_ORDER.pdsprj
4. CAP_V10_T04_RENAMED_VALUE_MANUAL_ORDER/CAP_V10_T04_RENAMED_VALUE_MANUAL_ORDER.pdsprj
5. CAP_V10_T05_THREE_TERMINAL_CAPS_MANUAL_ORDER/CAP_V10_T05_THREE_TERMINAL_CAPS_MANUAL_ORDER.pdsprj

Report which cases open and any exact Proteus error text.
