ProGenEDA/ProGenEDA-DEV/proteus/experiments/runs/capacitor_v6_terminal_reintro_temp_2026_05_30/README_TEST_ORDER.txt

Capacitor V6 terminal reintroduction diagnostics.

Open in order. If T01/T02 fail, stop and report. For T03-T06, report each case that opens or errors.

1. CAP_V6_T01_ONE_TERMINAL_CAP_PLUS_FREE_CAP/CAP_V6_T01_ONE_TERMINAL_CAP_PLUS_FREE_CAP.pdsprj
2. CAP_V6_T02_ONE_TERMINAL_CAP_PLUS_TWO_FREE_CAPS/CAP_V6_T02_ONE_TERMINAL_CAP_PLUS_TWO_FREE_CAPS.pdsprj
3. CAP_V6_T03_TWO_TERMINAL_CAPS_RES_SUFFIX_SEQUENTIAL/CAP_V6_T03_TWO_TERMINAL_CAPS_RES_SUFFIX_SEQUENTIAL.pdsprj
4. CAP_V6_T04_TWO_TERMINAL_CAPS_CAP_SUFFIX_TERMS_FIRST/CAP_V6_T04_TWO_TERMINAL_CAPS_CAP_SUFFIX_TERMS_FIRST.pdsprj
5. CAP_V6_T05_TWO_TERMINAL_CAPS_RES_SUFFIX_TERMS_FIRST/CAP_V6_T05_TWO_TERMINAL_CAPS_RES_SUFFIX_TERMS_FIRST.pdsprj
6. CAP_V6_T06_TWO_TERMINAL_CAPS_RES_SUFFIX_CAPS_FIRST/CAP_V6_T06_TWO_TERMINAL_CAPS_RES_SUFFIX_CAPS_FIRST.pdsprj
