ProGenEDA/ProGenEDA-DEV/proteus/experiments/runs/capacitor_v7_terminal_isolation_temp_2026_05_31/README_TEST_ORDER.txt

Capacitor V7 terminal isolation diagnostics.

Open in order and stop at the first failure through T05. If T06 fails, still test T07.

1. CAP_V7_T01_V4_T04_REPRO_SANITY/CAP_V7_T01_V4_T04_REPRO_SANITY.pdsprj
2. CAP_V7_T02_SINGLE_TERMINAL_CAP_1NF/CAP_V7_T02_SINGLE_TERMINAL_CAP_1NF.pdsprj
3. CAP_V7_T03_SINGLE_TERMINAL_CAP_PLUS_EXTRA_CDB_ONLY/CAP_V7_T03_SINGLE_TERMINAL_CAP_PLUS_EXTRA_CDB_ONLY.pdsprj
4. CAP_V7_T04_SINGLE_TERMINAL_CAP_PLUS_FREE_1UF/CAP_V7_T04_SINGLE_TERMINAL_CAP_PLUS_FREE_1UF.pdsprj
5. CAP_V7_T05_FREE_1UF_BEFORE_SINGLE_TERMINAL_CAP/CAP_V7_T05_FREE_1UF_BEFORE_SINGLE_TERMINAL_CAP.pdsprj
6. CAP_V7_T06_TWO_TERMINAL_CAPS_1UF_CAP_SUFFIX/CAP_V7_T06_TWO_TERMINAL_CAPS_1UF_CAP_SUFFIX.pdsprj
7. CAP_V7_T07_TWO_TERMINAL_CAPS_1UF_RES_SUFFIX_TERMS_FIRST/CAP_V7_T07_TWO_TERMINAL_CAPS_1UF_RES_SUFFIX_TERMS_FIRST.pdsprj
