ProGenEDA/ProGenEDA-DEV/proteus/experiments/runs/capacitor_v9_unique_index_temp_2026_05_31/README_TEST_ORDER.txt

Capacitor V9 unique-index diagnostics.

Open in order. T01 should reproduce a working guard. If T02 works, still test T05. If T02 fails, test T03 and T04. T05 is only useful after T02 works.

1. CAP_V9_T01_V8_T01_REPRO_GUARD/CAP_V9_T01_V8_T01_REPRO_GUARD.pdsprj
2. CAP_V9_T02_TWO_TERMINAL_CAP_SUFFIX_SEQ_UNIQUE_INDEX/CAP_V9_T02_TWO_TERMINAL_CAP_SUFFIX_SEQ_UNIQUE_INDEX.pdsprj
3. CAP_V9_T03_TWO_TERMINAL_RES_SUFFIX_TERMS_FIRST_UNIQUE_INDEX/CAP_V9_T03_TWO_TERMINAL_RES_SUFFIX_TERMS_FIRST_UNIQUE_INDEX.pdsprj
4. CAP_V9_T04_TWO_TERMINAL_RES_SUFFIX_V9_ORDER_UNIQUE_INDEX/CAP_V9_T04_TWO_TERMINAL_RES_SUFFIX_V9_ORDER_UNIQUE_INDEX.pdsprj
5. CAP_V9_T05_THREE_TERMINAL_CAP_SUFFIX_SEQ_UNIQUE_INDEX/CAP_V9_T05_THREE_TERMINAL_CAP_SUFFIX_SEQ_UNIQUE_INDEX.pdsprj
