ProGenEDA/ProGenEDA-DEV/proteus/experiments/runs/inductor_v1_terminal_temp_2026_05_31/README_TEST_ORDER.txt

Inductor V1 terminal diagnostic pack.

Open in this order:

1. IND_V1_T01_SINGLE_N1_N2/IND_V1_T01_SINGLE_N1_N2.pdsprj
2. IND_V1_T02_RENAMED_TRANSLATED/IND_V1_T02_RENAMED_TRANSLATED.pdsprj
3. IND_V1_T03_THREE_TERMINAL_INDUCTORS/IND_V1_T03_THREE_TERMINAL_INDUCTORS.pdsprj
4. IND_V1_T04_POWER_GROUND_LOCKED_V0_G0/IND_V1_T04_POWER_GROUND_LOCKED_V0_G0.pdsprj
5. IND_V1_T05_SERIES_POWER_GROUND_TWO_L/IND_V1_T05_SERIES_POWER_GROUND_TWO_L.pdsprj
