ProGenEDA/ProGenEDA-DEV/proteus/experiments/runs/inductor_v2_suffix_temp_2026_05_31/README_TEST_ORDER.txt

Inductor V2 suffix-preservation diagnostic pack.

Open in this order:

1. IND_V2_T01_DONOR02_REPACK_EXACT/IND_V2_T01_DONOR02_REPACK_EXACT.pdsprj
2. IND_V2_T02_E001_DONOR02_EXACT_CHUNK/IND_V2_T02_E001_DONOR02_EXACT_CHUNK.pdsprj
3. IND_V2_T03_SUFFIX_PRESERVED_SINGLE/IND_V2_T03_SUFFIX_PRESERVED_SINGLE.pdsprj
4. IND_V2_T04_SUFFIX_PRESERVED_RENAMED/IND_V2_T04_SUFFIX_PRESERVED_RENAMED.pdsprj
5. IND_V2_T05_DONOR03_REPACK_EXACT/IND_V2_T05_DONOR03_REPACK_EXACT.pdsprj
6. IND_V2_T06_E001_DONOR03_EXACT_CHUNK/IND_V2_T06_E001_DONOR03_EXACT_CHUNK.pdsprj
7. IND_V2_T07_SUFFIX_PRESERVED_THREE/IND_V2_T07_SUFFIX_PRESERVED_THREE.pdsprj
8. IND_V2_T08_DONOR04_REPACK_EXACT/IND_V2_T08_DONOR04_REPACK_EXACT.pdsprj
9. IND_V2_T09_E001_DONOR04_EXACT_CHUNK/IND_V2_T09_E001_DONOR04_EXACT_CHUNK.pdsprj
