ProGenEDA/ProGenEDA-DEV/proteus/experiments/runs/inductor_v3_multi_temp_2026_05_31/README_TEST_ORDER.txt

Inductor V3 multi-inductor diagnostic pack.

Open in this order:

1. IND_V3_T01_REBUILD_DONOR03_PER_INDEX_EXACT/IND_V3_T01_REBUILD_DONOR03_PER_INDEX_EXACT.pdsprj
2. IND_V3_T02_THREE_RENAMED_DONOR_GEOMETRY/IND_V3_T02_THREE_RENAMED_DONOR_GEOMETRY.pdsprj
3. IND_V3_T03_THREE_RIGID_TRANSLATED_DONOR_GEOMETRY/IND_V3_T03_THREE_RIGID_TRANSLATED_DONOR_GEOMETRY.pdsprj
4. IND_V3_T04_THREE_RENAMED_RIGID_TRANSLATED/IND_V3_T04_THREE_RENAMED_RIGID_TRANSLATED.pdsprj
5. IND_V3_T05_FORMULA_COORDS_FIXED_INDEX_SUFFIX/IND_V3_T05_FORMULA_COORDS_FIXED_INDEX_SUFFIX.pdsprj
