ProGenEDA/ProGenEDA-DEV/proteus/experiments/runs/inductor_v5_donor04_order_temp_2026_05_31/README_TEST_ORDER.txt

Inductor V5 donor04-order diagnostic pack.

Open in this order:

1. IND_V5_T01_E001_DONOR04_EXACT_CHUNK_CONTROL/IND_V5_T01_E001_DONOR04_EXACT_CHUNK_CONTROL.pdsprj
2. IND_V5_T02_REBUILD_DONOR04_SLICES_EXACT/IND_V5_T02_REBUILD_DONOR04_SLICES_EXACT.pdsprj
3. IND_V5_T03_GENERATED_SAME_DONOR04_ORDER/IND_V5_T03_GENERATED_SAME_DONOR04_ORDER.pdsprj
4. IND_V5_T04_RENAMED_REF_DONOR04_ORDER/IND_V5_T04_RENAMED_REF_DONOR04_ORDER.pdsprj
5. IND_V5_T05_RENAMED_VALUE_DONOR04_ORDER/IND_V5_T05_RENAMED_VALUE_DONOR04_ORDER.pdsprj
