ProGenEDA/ProGenEDA-DEV/proteus/experiments/runs/inductor_v6_6_21_temp_2026_06_01/README_TEST_ORDER.txt

Inductor V6 6/21 diagnostic pack.

Open in this exact order and stop at the first fatal Proteus error unless you want to continue diagnostics:

1. IND_V6_T01_6L_TERMINAL_ONLY_REPEAT_SUFFIX/IND_V6_T01_6L_TERMINAL_ONLY_REPEAT_SUFFIX.pdsprj
2. IND_V6_T02_6L_TERMINAL_ONLY_EXTENDED_SUFFIX/IND_V6_T02_6L_TERMINAL_ONLY_EXTENDED_SUFFIX.pdsprj
3. IND_V6_T03_21L_TERMINAL_ONLY_EXTENDED_SUFFIX/IND_V6_T03_21L_TERMINAL_ONLY_EXTENDED_SUFFIX.pdsprj
4. IND_V6_T04_6L_POWER_GROUND_DONOR04_BRIDGE_HEADER/IND_V6_T04_6L_POWER_GROUND_DONOR04_BRIDGE_HEADER.pdsprj
5. IND_V6_T05_6L_POWER_GROUND_DONOR04_AFTER_FIRST_LEFT_WIRE/IND_V6_T05_6L_POWER_GROUND_DONOR04_AFTER_FIRST_LEFT_WIRE.pdsprj
6. IND_V6_T06_21L_POWER_GROUND_DONOR04_AFTER_FIRST_LEFT_WIRE/IND_V6_T06_21L_POWER_GROUND_DONOR04_AFTER_FIRST_LEFT_WIRE.pdsprj

Report which files open, exact error text, and whether component count/labels look correct.
