ProGenEDA/ProGenEDA-DEV/proteus/experiments/runs/inductor_v7_requested15_temp_2026_06_01/README_TEST_ORDER.txt

Inductor V7 requested-15 topology pack.

Test this only after V6 T05 and T06 open correctly.

Open in order:
1. IND_V7_01_SIMPLE_LOOP/IND_V7_01_SIMPLE_LOOP.pdsprj
2. IND_V7_02_SERIES_CIRCUIT/IND_V7_02_SERIES_CIRCUIT.pdsprj
3. IND_V7_03_PARALLEL_CIRCUIT/IND_V7_03_PARALLEL_CIRCUIT.pdsprj
4. IND_V7_04_SERIES_PARALLEL_COMBO/IND_V7_04_SERIES_PARALLEL_COMBO.pdsprj
5. IND_V7_05_BASIC_VOLTAGE_DIVIDER/IND_V7_05_BASIC_VOLTAGE_DIVIDER.pdsprj
6. IND_V7_06_MULTI_STEP_VOLTAGE_DIVIDER/IND_V7_06_MULTI_STEP_VOLTAGE_DIVIDER.pdsprj
7. IND_V7_07_CURRENT_DIVIDER/IND_V7_07_CURRENT_DIVIDER.pdsprj
8. IND_V7_08_DELTA_NETWORK/IND_V7_08_DELTA_NETWORK.pdsprj
9. IND_V7_09_STAR_Y_NETWORK/IND_V7_09_STAR_Y_NETWORK.pdsprj
10. IND_V7_10_DELTA_TO_STAR_SETUP/IND_V7_10_DELTA_TO_STAR_SETUP.pdsprj
11. IND_V7_11_WHEATSTONE_BRIDGE/IND_V7_11_WHEATSTONE_BRIDGE.pdsprj
12. IND_V7_12_BALANCED_WHEATSTONE_BRIDGE/IND_V7_12_BALANCED_WHEATSTONE_BRIDGE.pdsprj
13. IND_V7_13_UNBALANCED_WHEATSTONE_BRIDGE/IND_V7_13_UNBALANCED_WHEATSTONE_BRIDGE.pdsprj
14. IND_V7_14_H_BRIDGE_RESISTOR_VERSION/IND_V7_14_H_BRIDGE_RESISTOR_VERSION.pdsprj
15. IND_V7_15_R_2R_LADDER_NETWORK/IND_V7_15_R_2R_LADDER_NETWORK.pdsprj

Report open errors, bad-object records, missing labels, overlap, or wrong component count.
