ProGenEDA/ProGenEDA-DEV/proteus/experiments/runs/inductor_v8_six_donor_temp_2026_06_01/README_TEST_ORDER.txt

Inductor V8 six-donor diagnostic pack.

Open in this exact order and stop at the first fatal Proteus error unless collecting diagnostics:

1. IND_V8_T01_E001_DONOR05_EXACT_CHUNK/IND_V8_T01_E001_DONOR05_EXACT_CHUNK.pdsprj
2. IND_V8_T02_REBUILD_DONOR05_SEQUENTIAL_EXACT/IND_V8_T02_REBUILD_DONOR05_SEQUENTIAL_EXACT.pdsprj
3. IND_V8_T03_6L_SEQUENTIAL_EXTENDED_SUFFIX/IND_V8_T03_6L_SEQUENTIAL_EXTENDED_SUFFIX.pdsprj
4. IND_V8_T04_21L_SEQUENTIAL_EXTENDED_SUFFIX/IND_V8_T04_21L_SEQUENTIAL_EXTENDED_SUFFIX.pdsprj
5. IND_V8_T05_6L_CAP_STYLE_OUTPUTS_FIRST/IND_V8_T05_6L_CAP_STYLE_OUTPUTS_FIRST.pdsprj
6. IND_V8_T06_6L_POWER_GROUND_CAP_BRIDGE_SEQUENTIAL/IND_V8_T06_6L_POWER_GROUND_CAP_BRIDGE_SEQUENTIAL.pdsprj

Report which files open, exact error text, and whether component count/labels look correct.
