ProGenEDA/ProGenEDA-DEV/proteus/experiments/runs/inductor_v9_requested15_power_ground_temp_2026_06_01/README_TEST_ORDER.txt

Inductor V9 requested-15 power/ground pack.

Open in order:
1. IND_V9_01_SIMPLE_LOOP/IND_V9_01_SIMPLE_LOOP.pdsprj
2. IND_V9_02_SERIES_CIRCUIT/IND_V9_02_SERIES_CIRCUIT.pdsprj
3. IND_V9_03_PARALLEL_CIRCUIT/IND_V9_03_PARALLEL_CIRCUIT.pdsprj
4. IND_V9_04_SERIES_PARALLEL_COMBO/IND_V9_04_SERIES_PARALLEL_COMBO.pdsprj
5. IND_V9_05_BASIC_VOLTAGE_DIVIDER/IND_V9_05_BASIC_VOLTAGE_DIVIDER.pdsprj
6. IND_V9_06_MULTI_STEP_VOLTAGE_DIVIDER/IND_V9_06_MULTI_STEP_VOLTAGE_DIVIDER.pdsprj
7. IND_V9_07_CURRENT_DIVIDER/IND_V9_07_CURRENT_DIVIDER.pdsprj
8. IND_V9_08_DELTA_NETWORK/IND_V9_08_DELTA_NETWORK.pdsprj
9. IND_V9_09_STAR_Y_NETWORK/IND_V9_09_STAR_Y_NETWORK.pdsprj
10. IND_V9_10_DELTA_TO_STAR_SETUP/IND_V9_10_DELTA_TO_STAR_SETUP.pdsprj
11. IND_V9_11_WHEATSTONE_BRIDGE/IND_V9_11_WHEATSTONE_BRIDGE.pdsprj
12. IND_V9_12_BALANCED_WHEATSTONE_BRIDGE/IND_V9_12_BALANCED_WHEATSTONE_BRIDGE.pdsprj
13. IND_V9_13_UNBALANCED_WHEATSTONE_BRIDGE/IND_V9_13_UNBALANCED_WHEATSTONE_BRIDGE.pdsprj
14. IND_V9_14_H_BRIDGE_RESISTOR_VERSION/IND_V9_14_H_BRIDGE_RESISTOR_VERSION.pdsprj
15. IND_V9_15_R_2R_LADDER_NETWORK/IND_V9_15_R_2R_LADDER_NETWORK.pdsprj

Report open errors, bad-object records, missing labels, overlap, or wrong component count.
