ProGenEDA/ProGenEDA-DEV/proteus/experiments/runs/mixed_rcl_v10_terminal_rl_donor_temp_2026_06_01/README_TEST_ORDER.txt

Open in this order and report the first case that errors or renders wrong:

1. RCL_V10_T01_EXACT_DISCONNECTED_REPACK/RCL_V10_T01_EXACT_DISCONNECTED_REPACK.pdsprj
2. RCL_V10_T02_DISCONNECTED_CHUNK_IN_E001/RCL_V10_T02_DISCONNECTED_CHUNK_IN_E001.pdsprj
3. RCL_V10_T03_EXACT_SERIES_REPACK/RCL_V10_T03_EXACT_SERIES_REPACK.pdsprj
4. RCL_V10_T04_SERIES_CHUNK_IN_E001/RCL_V10_T04_SERIES_CHUNK_IN_E001.pdsprj
5. RCL_V10_T05_NATIVE_REBUILD_SAME_LABELS/RCL_V10_T05_NATIVE_REBUILD_SAME_LABELS.pdsprj
6. RCL_V10_T06_NATIVE_CONNECTED_LABELS/RCL_V10_T06_NATIVE_CONNECTED_LABELS.pdsprj
7. RCL_V10_T07_NATIVE_TRANSLATED_DISCONNECTED/RCL_V10_T07_NATIVE_TRANSLATED_DISCONNECTED.pdsprj
8. RCL_V10_T08_NATIVE_POWER_GROUND_SERIES/RCL_V10_T08_NATIVE_POWER_GROUND_SERIES.pdsprj

If T01-T04 fail, the donor/control import is bad. If T05 fails, the donor-native mutation is still wrong. If T05 works, T06-T08 identify connected labels, translation, and V0/G0 behavior.
