ProGenEDA/ProGenEDA-DEV/proteus/experiments/runs/mixed_rcl_v14_repeated_unit_temp_2026_06_02/README_TEST_ORDER.txt

Mixed R/C/L V14 repeated-unit diagnostic pack.

Open and run netlist/simulation in order:
1. RCL_V14_T00_EXACT_4X_DONOR_REPACK/RCL_V14_T00_EXACT_4X_DONOR_REPACK.pdsprj
2. RCL_V14_T00B_4X_DONOR_CHUNK_IN_E001/RCL_V14_T00B_4X_DONOR_CHUNK_IN_E001.pdsprj
3. RCL_V14_T01_1X_UNIT_CONTIGUOUS_IDS/RCL_V14_T01_1X_UNIT_CONTIGUOUS_IDS.pdsprj
4. RCL_V14_T02_2X_UNIT_CONTIGUOUS_IDS/RCL_V14_T02_2X_UNIT_CONTIGUOUS_IDS.pdsprj
5. RCL_V14_T03_3X_UNIT_CONTIGUOUS_IDS/RCL_V14_T03_3X_UNIT_CONTIGUOUS_IDS.pdsprj
6. RCL_V14_T04_4X_UNIT_CONTIGUOUS_IDS/RCL_V14_T04_4X_UNIT_CONTIGUOUS_IDS.pdsprj
7. RCL_V14_T05_4X_UNIT_SUPPLIED_ID_GAPS/RCL_V14_T05_4X_UNIT_SUPPLIED_ID_GAPS.pdsprj
8. RCL_V14_T06_6X_UNIT_CONTIGUOUS_IDS/RCL_V14_T06_6X_UNIT_CONTIGUOUS_IDS.pdsprj
9. RCL_V14_T07_7X_UNIT_CONTIGUOUS_IDS/RCL_V14_T07_7X_UNIT_CONTIGUOUS_IDS.pdsprj
10. RCL_V14_T08_21X_UNIT_CONTIGUOUS_IDS/RCL_V14_T08_21X_UNIT_CONTIGUOUS_IDS.pdsprj

T00 and T00B are controls. If those fail, report that before testing generated cases.
If T01-T05 pass but T06 or later fails, the remaining issue is extrapolation beyond the observed 4x donor.
