ProGenEDA/ProGenEDA-DEV/proteus/experiments/runs/mixed_rcl_v15_mutation_isolation_temp_2026_06_02/README_TEST_ORDER.txt

Mixed R/C/L V15 mutation-isolation diagnostic pack.

Open in order and stop at the first Bad Object Record or corrupt pink-wire render:
1. RCL_V15_T00_4X_DONOR_CHUNK_IN_E001_CONTROL/RCL_V15_T00_4X_DONOR_CHUNK_IN_E001_CONTROL.pdsprj
2. RCL_V15_T01_LABEL_ONLY_UNIT1_A1_B1/RCL_V15_T01_LABEL_ONLY_UNIT1_A1_B1.pdsprj
3. RCL_V15_T02_LABEL_ONLY_ALL_UNIQUE_A_B/RCL_V15_T02_LABEL_ONLY_ALL_UNIQUE_A_B.pdsprj
4. RCL_V15_T03_LABEL_ONLY_ALL_SAME_N1_N2/RCL_V15_T03_LABEL_ONLY_ALL_SAME_N1_N2.pdsprj
5. RCL_V15_T04_V14_T05_WITH_DONOR_LABELS/RCL_V15_T04_V14_T05_WITH_DONOR_LABELS.pdsprj
6. RCL_V15_T05_1X_EXACT_UNIT1_50B_FINAL_3CDB/RCL_V15_T05_1X_EXACT_UNIT1_50B_FINAL_3CDB.pdsprj
7. RCL_V15_T06_1X_EXACT_UNIT1_50B_FINAL_FULL_CDB/RCL_V15_T06_1X_EXACT_UNIT1_50B_FINAL_FULL_CDB.pdsprj
8. RCL_V15_T07_1X_EXACT_UNIT1_51B_FINAL_3CDB/RCL_V15_T07_1X_EXACT_UNIT1_51B_FINAL_3CDB.pdsprj

Report which cases work and which first fails. T01-T03 isolate terminal labels; T04 isolates generated coordinate/component mutation; T05-T07 isolate whether a one-unit subset is valid.
