ProGenEDA/ProGenEDA-DEV/proteus/experiments/runs/mixed_rcl_v16_wire_offset_fix_temp_2026_06_02/README_TEST_ORDER.txt

Mixed R/C/L V16 wire-offset-fix diagnostic pack.

Open and run netlist/simulation in order:
1. RCL_V16_T00_EXACT_4X_DONOR_REPACK/RCL_V16_T00_EXACT_4X_DONOR_REPACK.pdsprj
2. RCL_V16_T00B_4X_DONOR_CHUNK_IN_E001/RCL_V16_T00B_4X_DONOR_CHUNK_IN_E001.pdsprj
3. RCL_V16_T01_1X_UNIT_CONTIGUOUS_IDS/RCL_V16_T01_1X_UNIT_CONTIGUOUS_IDS.pdsprj
4. RCL_V16_T02_2X_UNIT_CONTIGUOUS_IDS/RCL_V16_T02_2X_UNIT_CONTIGUOUS_IDS.pdsprj
5. RCL_V16_T03_3X_UNIT_CONTIGUOUS_IDS/RCL_V16_T03_3X_UNIT_CONTIGUOUS_IDS.pdsprj
6. RCL_V16_T04_4X_UNIT_CONTIGUOUS_IDS/RCL_V16_T04_4X_UNIT_CONTIGUOUS_IDS.pdsprj
7. RCL_V16_T05_4X_UNIT_SUPPLIED_ID_GAPS/RCL_V16_T05_4X_UNIT_SUPPLIED_ID_GAPS.pdsprj
8. RCL_V16_T06_6X_UNIT_CONTIGUOUS_IDS/RCL_V16_T06_6X_UNIT_CONTIGUOUS_IDS.pdsprj
9. RCL_V16_T07_7X_UNIT_CONTIGUOUS_IDS/RCL_V16_T07_7X_UNIT_CONTIGUOUS_IDS.pdsprj
10. RCL_V16_T08_21X_UNIT_CONTIGUOUS_IDS/RCL_V16_T08_21X_UNIT_CONTIGUOUS_IDS.pdsprj

T00 and T00B are controls. If those fail, report that before testing generated cases.
T01-T05 test the corrected wire coordinate offset within the observed 4x donor scale. T06-T08 test extrapolation beyond the observed 4x donor.
