ProGenEDA/ProGenEDA-DEV/proteus/experiments/runs/mixed_rcl_v17_component_removal_temp_2026_06_02/README_TEST_ORDER.txt

Mixed R/C/L V17 component-removal diagnostic pack.

Open and run netlist/simulation in order:
1. RCL_V17_T00_1X_FULL_RCL_CONTROL/RCL_V17_T00_1X_FULL_RCL_CONTROL.pdsprj
2. RCL_V17_T01_1X_RC_REMOVE_L/RCL_V17_T01_1X_RC_REMOVE_L.pdsprj
3. RCL_V17_T02_1X_LC_REMOVE_R/RCL_V17_T02_1X_LC_REMOVE_R.pdsprj
4. RCL_V17_T03_1X_RL_REMOVE_C/RCL_V17_T03_1X_RL_REMOVE_C.pdsprj
5. RCL_V17_T04_1X_C_ONLY_REMOVE_RL/RCL_V17_T04_1X_C_ONLY_REMOVE_RL.pdsprj
6. RCL_V17_T05_REQUESTED_3R_4C_1L/RCL_V17_T05_REQUESTED_3R_4C_1L.pdsprj

T05 is the requested 3R/4C/1L circuit. T01-T04 isolate RC, LC, RL, and C-only removal before that target.
