ProGenEDA/ProGenEDA-DEV/proteus/experiments/runs/mixed_rcl_v1_temp_2026_06_01/README_TEST_ORDER.txt

Mixed R/C/L V1 diagnostic pack.

Open in this order and stop at the first fatal Proteus error unless collecting extra diagnostics:

1. RCL_V1_T01_6_COMPONENTS_GROUPED_ORDER/RCL_V1_T01_6_COMPONENTS_GROUPED_ORDER.pdsprj
2. RCL_V1_T02_6_COMPONENTS_INDUCTOR_V3_FIRST/RCL_V1_T02_6_COMPONENTS_INDUCTOR_V3_FIRST.pdsprj
3. RCL_V1_T03_21_COMPONENTS_INDUCTOR_V3_FIRST/RCL_V1_T03_21_COMPONENTS_INDUCTOR_V3_FIRST.pdsprj
4. RCL_V1_T04_01_SIMPLE_LOOP/RCL_V1_T04_01_SIMPLE_LOOP.pdsprj
5. RCL_V1_T05_02_SERIES_CIRCUIT/RCL_V1_T05_02_SERIES_CIRCUIT.pdsprj
6. RCL_V1_T06_03_PARALLEL_CIRCUIT/RCL_V1_T06_03_PARALLEL_CIRCUIT.pdsprj
7. RCL_V1_T07_04_SERIES_PARALLEL_COMBO/RCL_V1_T07_04_SERIES_PARALLEL_COMBO.pdsprj
8. RCL_V1_T08_05_BASIC_VOLTAGE_DIVIDER/RCL_V1_T08_05_BASIC_VOLTAGE_DIVIDER.pdsprj
9. RCL_V1_T09_06_MULTI_STEP_VOLTAGE_DIVIDER/RCL_V1_T09_06_MULTI_STEP_VOLTAGE_DIVIDER.pdsprj
10. RCL_V1_T10_07_CURRENT_DIVIDER/RCL_V1_T10_07_CURRENT_DIVIDER.pdsprj
11. RCL_V1_T11_08_DELTA_NETWORK/RCL_V1_T11_08_DELTA_NETWORK.pdsprj
12. RCL_V1_T12_09_STAR_Y_NETWORK/RCL_V1_T12_09_STAR_Y_NETWORK.pdsprj
13. RCL_V1_T13_10_DELTA_TO_STAR_SETUP/RCL_V1_T13_10_DELTA_TO_STAR_SETUP.pdsprj
14. RCL_V1_T14_11_WHEATSTONE_BRIDGE/RCL_V1_T14_11_WHEATSTONE_BRIDGE.pdsprj
15. RCL_V1_T15_12_BALANCED_WHEATSTONE_BRIDGE/RCL_V1_T15_12_BALANCED_WHEATSTONE_BRIDGE.pdsprj
16. RCL_V1_T16_13_UNBALANCED_WHEATSTONE_BRIDGE/RCL_V1_T16_13_UNBALANCED_WHEATSTONE_BRIDGE.pdsprj
17. RCL_V1_T17_14_H_BRIDGE_RESISTOR_VERSION/RCL_V1_T17_14_H_BRIDGE_RESISTOR_VERSION.pdsprj
18. RCL_V1_T18_15_R_2R_LADDER_NETWORK/RCL_V1_T18_15_R_2R_LADDER_NETWORK.pdsprj

Report exact errors, missing component types, wrong labels, overlap, or bad-object records.
