ProGenEDA/ProGenEDA-DEV/proteus/experiments/runs/mixed_rcl_v2_v8_temp_2026_06_01/README_TEST_ORDER.txt

Mixed R/C/L V2 diagnostic pack using accepted V8 inductors.

Open in this order:
1. RCL_V2_T01_6_COMPONENTS_RCL_CYCLE/RCL_V2_T01_6_COMPONENTS_RCL_CYCLE.pdsprj
2. RCL_V2_T02_21_COMPONENTS_RCL_CYCLE/RCL_V2_T02_21_COMPONENTS_RCL_CYCLE.pdsprj
3. RCL_V2_T03_01_SIMPLE_LOOP/RCL_V2_T03_01_SIMPLE_LOOP.pdsprj
4. RCL_V2_T04_02_SERIES_CIRCUIT/RCL_V2_T04_02_SERIES_CIRCUIT.pdsprj
5. RCL_V2_T05_03_PARALLEL_CIRCUIT/RCL_V2_T05_03_PARALLEL_CIRCUIT.pdsprj
6. RCL_V2_T06_04_SERIES_PARALLEL_COMBO/RCL_V2_T06_04_SERIES_PARALLEL_COMBO.pdsprj
7. RCL_V2_T07_05_BASIC_VOLTAGE_DIVIDER/RCL_V2_T07_05_BASIC_VOLTAGE_DIVIDER.pdsprj
8. RCL_V2_T08_06_MULTI_STEP_VOLTAGE_DIVIDER/RCL_V2_T08_06_MULTI_STEP_VOLTAGE_DIVIDER.pdsprj
9. RCL_V2_T09_07_CURRENT_DIVIDER/RCL_V2_T09_07_CURRENT_DIVIDER.pdsprj
10. RCL_V2_T10_08_DELTA_NETWORK/RCL_V2_T10_08_DELTA_NETWORK.pdsprj
11. RCL_V2_T11_09_STAR_Y_NETWORK/RCL_V2_T11_09_STAR_Y_NETWORK.pdsprj
12. RCL_V2_T12_10_DELTA_TO_STAR_SETUP/RCL_V2_T12_10_DELTA_TO_STAR_SETUP.pdsprj
13. RCL_V2_T13_11_WHEATSTONE_BRIDGE/RCL_V2_T13_11_WHEATSTONE_BRIDGE.pdsprj
14. RCL_V2_T14_12_BALANCED_WHEATSTONE_BRIDGE/RCL_V2_T14_12_BALANCED_WHEATSTONE_BRIDGE.pdsprj
15. RCL_V2_T15_13_UNBALANCED_WHEATSTONE_BRIDGE/RCL_V2_T15_13_UNBALANCED_WHEATSTONE_BRIDGE.pdsprj
16. RCL_V2_T16_14_H_BRIDGE_RESISTOR_VERSION/RCL_V2_T16_14_H_BRIDGE_RESISTOR_VERSION.pdsprj
17. RCL_V2_T17_15_R_2R_LADDER_NETWORK/RCL_V2_T17_15_R_2R_LADDER_NETWORK.pdsprj

Report exact errors, missing component types, wrong labels, overlap, or bad-object records.
