ProGenEDA/ProGenEDA-DEV/proteus/experiments/runs/mixed_rcl_v3_isolation_temp_2026_06_01/README_TEST_ORDER.txt

Mixed R/C/L V3 isolation pack.

Open in order:
1. RCL_V3_T01_RL_RES_THEN_IND/RCL_V3_T01_RL_RES_THEN_IND.pdsprj
2. RCL_V3_T02_RL_IND_THEN_RES/RCL_V3_T02_RL_IND_THEN_RES.pdsprj
3. RCL_V3_T03_CL_CAP_THEN_IND/RCL_V3_T03_CL_CAP_THEN_IND.pdsprj
4. RCL_V3_T04_CL_IND_THEN_CAP/RCL_V3_T04_CL_IND_THEN_CAP.pdsprj
5. RCL_V3_T05_CL_OUTPUTS_FIRST_JOINED/RCL_V3_T05_CL_OUTPUTS_FIRST_JOINED.pdsprj
6. RCL_V3_T06_RCL_V2_CURRENT_MINIMAL/RCL_V3_T06_RCL_V2_CURRENT_MINIMAL.pdsprj
7. RCL_V3_T07_RCL_IND_FIRST/RCL_V3_T07_RCL_IND_FIRST.pdsprj
8. RCL_V3_T08_RCL_CAP_IND_OUTPUTS_THEN_RES/RCL_V3_T08_RCL_CAP_IND_OUTPUTS_THEN_RES.pdsprj
9. RCL_V3_T09_RCL_ALL_OUTPUTS_THEN_GROUPS/RCL_V3_T09_RCL_ALL_OUTPUTS_THEN_GROUPS.pdsprj

Report which pairwise cases work or fail before testing the full R/C/L cases.
