ProGenEDA/ProGenEDA-DEV/proteus/experiments/runs/mixed_rcl_v7_resistor_suffix_order_temp_2026_06_01/README_TEST_ORDER.txt

MIXED_RCL_V7_RESISTOR_SUFFIX_ORDER_TEMP_2026_06_01

Test in order:
1. T01 is the V6 T03 reproduction control and is expected to fail.
2. T02-T07 keep L and C as exact free donor records and put terminal R last with different ordinal/suffix policies.
3. T08-T10 use the known-good terminal C+L block, then terminal R last with different suffix policies.
4. T11-T12 repeat all-terminal cases with the manual RLC donor header.
