ProGenEDA/ProGenEDA-DEV/proteus/experiments/runs/dc_mixed_sources_v15_requested5_after_v9_acceptance_temp_2026_06_05/README_TEST_ORDER.txt

DC_MIXED_SOURCES_V15_REQUESTED5_AFTER_V9_ACCEPTANCE_TEMP_2026_06_05

Open in order:
1. DCMS_V15_T01_CIRCUIT_1_12V_2A/DCMS_V15_T01_CIRCUIT_1_12V_2A.pdsprj
2. DCMS_V15_T02_CIRCUIT_2_TWO_5V_1A/DCMS_V15_T02_CIRCUIT_2_TWO_5V_1A.pdsprj
3. DCMS_V15_T03_CIRCUIT_3_24V_TWO_0A5/DCMS_V15_T03_CIRCUIT_3_24V_TWO_0A5.pdsprj
4. DCMS_V15_T04_CIRCUIT_4_TWO_15V_TWO_3A/DCMS_V15_T04_CIRCUIT_4_TWO_15V_TWO_3A.pdsprj
5. DCMS_V15_T05_CIRCUIT_5_THREE_9V_1A5/DCMS_V15_T05_CIRCUIT_5_THREE_9V_1A5.pdsprj

These are the five requested mixed DC-source R/C/L circuits only.
