ProGenEDA/ProGenEDA-DEV/proteus/experiments/runs/dc_mixed_sources_v14_requested5_v13_method_temp_2026_06_05/README_TEST_ORDER.txt

DC_MIXED_SOURCES_V14_REQUESTED5_V13_METHOD_TEMP_2026_06_05

Open in order:
1. DCMS_V14_T00_V13_ACCEPTED_CONTROL.pdsprj
2. DCMS_V14_T01_CIRCUIT_1_12V_2A/DCMS_V14_T01_CIRCUIT_1_12V_2A.pdsprj
3. DCMS_V14_T02_CIRCUIT_2_TWO_5V_1A/DCMS_V14_T02_CIRCUIT_2_TWO_5V_1A.pdsprj
4. DCMS_V14_T03_CIRCUIT_3_24V_TWO_0A5/DCMS_V14_T03_CIRCUIT_3_24V_TWO_0A5.pdsprj
5. DCMS_V14_T04_CIRCUIT_4_TWO_15V_TWO_3A/DCMS_V14_T04_CIRCUIT_4_TWO_15V_TWO_3A.pdsprj
6. DCMS_V14_T05_CIRCUIT_5_THREE_9V_1A5/DCMS_V14_T05_CIRCUIT_5_THREE_9V_1A5.pdsprj

T00 is the accepted V13 control. T01-T05 are the five requested mixed DC-source R/C/L circuits.
