ProGenEDA/ProGenEDA-DEV/proteus/experiments/runs/dc_mixed_sources_v12_suffixmap_coords_temp_2026_06_05/README_TEST_ORDER.txt

DC_MIXED_SOURCES_V12_SUFFIXMAP_COORDS_TEMP_2026_06_05

Open in order:
1. DCMS_V12_T00_DONOR_COPY.pdsprj
2. DCMS_V12_T01_DONOR_OBJECT_GENERATED_CDB/DCMS_V12_T01_DONOR_OBJECT_GENERATED_CDB.pdsprj
3. DCMS_V12_T02_GROUP9_SUFFIXMAP_CONTROL/DCMS_V12_T02_GROUP9_SUFFIXMAP_CONTROL.pdsprj
4. DCMS_V12_T03_GROUP9_SUFFIXMAP_VSOURCE_COORDS/DCMS_V12_T03_GROUP9_SUFFIXMAP_VSOURCE_COORDS.pdsprj
5. DCMS_V12_T04_GROUP9_SUFFIXMAP_BOTH_COORDS/DCMS_V12_T04_GROUP9_SUFFIXMAP_BOTH_COORDS.pdsprj
6. DCMS_V12_T05_GROUP7_SUFFIXMAP_BOTH_COORDS/DCMS_V12_T05_GROUP7_SUFFIXMAP_BOTH_COORDS.pdsprj
7. DCMS_V12_T06_GROUP4_SUFFIXMAP_BOTH_COORDS/DCMS_V12_T06_GROUP4_SUFFIXMAP_BOTH_COORDS.pdsprj

T00/T01 are controls. T02 repeats the known-open suffix-map boundary without coordinate changes. T03 moves only the voltage source. T04/T05/T06 keep suffix mapping and move both source blocks closer to their connected terminal clusters.
