ProGenEDA/ProGenEDA-DEV/proteus/experiments/runs/dc_mixed_sources_v11_group_boundary_temp_2026_06_05/README_TEST_ORDER.txt

DC_MIXED_SOURCES_V11_GROUP_BOUNDARY_TEMP_2026_06_05

Open in order:
1. DCMS_V11_T00_DONOR_COPY.pdsprj
2. DCMS_V11_T01_DONOR_OBJECT_GENERATED_CDB/DCMS_V11_T01_DONOR_OBJECT_GENERATED_CDB.pdsprj
3. DCMS_V11_T02_GENERATED_PREFIX_DONOR_GROUP9/DCMS_V11_T02_GENERATED_PREFIX_DONOR_GROUP9.pdsprj
4. DCMS_V11_T03_GENERATED_PREFIX_DONOR_GROUP9_SUFFIXMAP/DCMS_V11_T03_GENERATED_PREFIX_DONOR_GROUP9_SUFFIXMAP.pdsprj
5. DCMS_V11_T04_GENERATED_PREFIX_DONOR_GROUP7_TO_TAIL/DCMS_V11_T04_GENERATED_PREFIX_DONOR_GROUP7_TO_TAIL.pdsprj
6. DCMS_V11_T05_GENERATED_PREFIX_DONOR_GROUP7_SUFFIXMAP/DCMS_V11_T05_GENERATED_PREFIX_DONOR_GROUP7_SUFFIXMAP.pdsprj
7. DCMS_V11_T06_GENERATED_PREFIX_DONOR_GROUP4_TO_TAIL/DCMS_V11_T06_GENERATED_PREFIX_DONOR_GROUP4_TO_TAIL.pdsprj
8. DCMS_V11_T07_GENERATED_LEADING_V0_DONOR_REST/DCMS_V11_T07_GENERATED_LEADING_V0_DONOR_REST.pdsprj

T00/T01 are controls. T02/T03 test a full donor group-9 splice. T04/T05 test donor groups 7-9. T06 tests donor groups 4-9. T07 tests whether even the leading generated V0 output is unsafe.
