ProGenEDA/ProGenEDA-DEV/proteus/experiments/runs/dc_mixed_sources_v10_final_unit_temp_2026_06_05/README_TEST_ORDER.txt

DC_MIXED_SOURCES_V10_FINAL_UNIT_TEMP_2026_06_05

Open in order:
1. DCMS_V10_T00_DONOR_COPY.pdsprj
2. DCMS_V10_T01_DONOR_TRANSPLANT_E001/DCMS_V10_T01_DONOR_TRANSPLANT_E001.pdsprj
3. DCMS_V10_T02_DONOR_LABEL_DVO_TO_D0/DCMS_V10_T02_DONOR_LABEL_DVO_TO_D0.pdsprj
4. DCMS_V10_T03_DONOR_OBJECT_GENERATED_CDB/DCMS_V10_T03_DONOR_OBJECT_GENERATED_CDB.pdsprj
5. DCMS_V10_T04_DONOR_D0_GENERATED_CDB/DCMS_V10_T04_DONOR_D0_GENERATED_CDB.pdsprj
6. DCMS_V10_T05_GENERATED_21_DVO_LABEL/DCMS_V10_T05_GENERATED_21_DVO_LABEL.pdsprj
7. DCMS_V10_T06_GENERATED_PREFIX_DONOR_FINAL_UNIT/DCMS_V10_T06_GENERATED_PREFIX_DONOR_FINAL_UNIT.pdsprj
8. DCMS_V10_T07_GENERATED_PREFIX_DONOR_FINAL_UNIT_D0/DCMS_V10_T07_GENERATED_PREFIX_DONOR_FINAL_UNIT_D0.pdsprj
9. DCMS_V10_T08_GENERATED_PREFIX_DONOR_FINAL_UNIT_D0_GENERATED_CDB/DCMS_V10_T08_GENERATED_PREFIX_DONOR_FINAL_UNIT_D0_GENERATED_CDB.pdsprj

T00-T02 repeat the V9 passing boundary. T03/T04 test the generated CDB on donor-safe objects. T05 tests whether label matching alone fixes generated body failure. T06-T08 test the generated prefix with the donor final RL unit restored.
