ProGenEDA/ProGenEDA-DEV/proteus/experiments/runs/dc_mixed_sources_v9_donor_tail_temp_2026_06_05/README_TEST_ORDER.txt

DC_MIXED_SOURCES_V9_DONOR_TAIL_TEMP_2026_06_05

Open in order:
1. DCMS_V9_T00_DONOR_COPY.pdsprj
2. DCMS_V9_T01_DONOR_TRANSPLANT_E001/DCMS_V9_T01_DONOR_TRANSPLANT_E001.pdsprj
3. DCMS_V9_T02_DONOR_LABEL_DVO_TO_D0/DCMS_V9_T02_DONOR_LABEL_DVO_TO_D0.pdsprj
4. DCMS_V9_T03_GENERATED_21_DONOR_TAIL_EXACT_LABELS/DCMS_V9_T03_GENERATED_21_DONOR_TAIL_EXACT_LABELS.pdsprj
5. DCMS_V9_T04_GENERATED_21_DONOR_TAIL_D0_LABEL/DCMS_V9_T04_GENERATED_21_DONOR_TAIL_D0_LABEL.pdsprj
6. DCMS_V9_T05_GENERATED_21_DONOR_TAIL_D0_GENERATED_CDB/DCMS_V9_T05_GENERATED_21_DONOR_TAIL_D0_GENERATED_CDB.pdsprj

T00/T01 prove the donor and transplant path. T02 tests whether terminal names can be changed safely. T03/T04 test generated 21 R/C/L bodies with the donor source tail. T05 tests the generated CDB writer against the donor-tail object structure.
