ProGenEDA/ProGenEDA-DEV/proteus/experiments/runs/dc_sources_v2_cdb_fix_temp_2026_06_03/DC_SOURCES_V2_CDB_FIX_TEST_BATCH/README_TEST_ORDER.txt

1. DCS_V2_T01_DCV_6_COMPONENTS/DCS_V2_T01_DCV_6_COMPONENTS.pdsprj
2. DCS_V2_T02_DCV_21_COMPONENTS/DCS_V2_T02_DCV_21_COMPONENTS.pdsprj
3. DCS_V2_T03_DCI_6_COMPONENTS/DCS_V2_T03_DCI_6_COMPONENTS.pdsprj
4. DCS_V2_T04_DCI_21_COMPONENTS/DCS_V2_T04_DCI_21_COMPONENTS.pdsprj
5. DCS_V2_T05_COMPLEX_RLC_01/DCS_V2_T05_COMPLEX_RLC_01.pdsprj
6. DCS_V2_T06_COMPLEX_RLC_02/DCS_V2_T06_COMPLEX_RLC_02.pdsprj
7. DCS_V2_T07_COMPLEX_RLC_03/DCS_V2_T07_COMPLEX_RLC_03.pdsprj
8. DCS_V2_T08_COMPLEX_RLC_04/DCS_V2_T08_COMPLEX_RLC_04.pdsprj
9. DCS_V2_T09_COMPLEX_RLC_05/DCS_V2_T09_COMPLEX_RLC_05.pdsprj
