ProGenEDA/ProGenEDA-DEV/proteus/experiments/runs/dc_sources_v3_object_order_temp_2026_06_03/DC_SOURCES_V3_OBJECT_ORDER_TEST_BATCH/README_TEST_ORDER.txt

1. DCS_V3_T00A_DCV_EXACT_DONOR_REPACK/DCS_V3_T00A_DCV_EXACT_DONOR_REPACK.pdsprj
2. DCS_V3_T00B_DCV_DONOR_CHUNK_IN_E001/DCS_V3_T00B_DCV_DONOR_CHUNK_IN_E001.pdsprj
3. DCS_V3_T00C_DCI_EXACT_DONOR_REPACK/DCS_V3_T00C_DCI_EXACT_DONOR_REPACK.pdsprj
4. DCS_V3_T00D_DCI_DONOR_CHUNK_IN_E001/DCS_V3_T00D_DCI_DONOR_CHUNK_IN_E001.pdsprj
5. DCS_V3_T00E_DCV_RLOAD_EXACT_DONOR_REPACK/DCS_V3_T00E_DCV_RLOAD_EXACT_DONOR_REPACK.pdsprj
6. DCS_V3_T00F_DCV_RLOAD_DONOR_CHUNK_IN_E001/DCS_V3_T00F_DCV_RLOAD_DONOR_CHUNK_IN_E001.pdsprj
7. DCS_V3_T00G_DCI_RLOAD_EXACT_DONOR_REPACK/DCS_V3_T00G_DCI_RLOAD_EXACT_DONOR_REPACK.pdsprj
8. DCS_V3_T00H_DCI_RLOAD_DONOR_CHUNK_IN_E001/DCS_V3_T00H_DCI_RLOAD_DONOR_CHUNK_IN_E001.pdsprj
9. DCS_V3_T01_DCV_6_COMPONENTS/DCS_V3_T01_DCV_6_COMPONENTS.pdsprj
10. DCS_V3_T02_DCV_21_COMPONENTS/DCS_V3_T02_DCV_21_COMPONENTS.pdsprj
11. DCS_V3_T03_DCI_6_COMPONENTS/DCS_V3_T03_DCI_6_COMPONENTS.pdsprj
12. DCS_V3_T04_DCI_21_COMPONENTS/DCS_V3_T04_DCI_21_COMPONENTS.pdsprj
13. DCS_V3_T05_COMPLEX_RLC_01/DCS_V3_T05_COMPLEX_RLC_01.pdsprj
14. DCS_V3_T06_COMPLEX_RLC_02/DCS_V3_T06_COMPLEX_RLC_02.pdsprj
15. DCS_V3_T07_COMPLEX_RLC_03/DCS_V3_T07_COMPLEX_RLC_03.pdsprj
16. DCS_V3_T08_COMPLEX_RLC_04/DCS_V3_T08_COMPLEX_RLC_04.pdsprj
17. DCS_V3_T09_COMPLEX_RLC_05/DCS_V3_T09_COMPLEX_RLC_05.pdsprj
