ProGenEDA/ProGenEDA-DEV/proteus/experiments/runs/dc_sources_v4_add_to_normal_rcl_temp_2026_06_03/DC_SOURCES_V4_ADD_TO_NORMAL_RCL_TEST_BATCH/README_TEST_ORDER.txt

1. DCS_V4_T00A_NORMAL_RCL_6_BASELINE/DCS_V4_T00A_NORMAL_RCL_6_BASELINE.pdsprj
2. DCS_V4_T00B_DCV_EXACT_DONOR_REPACK/DCS_V4_T00B_DCV_EXACT_DONOR_REPACK.pdsprj
3. DCS_V4_T00C_DCI_EXACT_DONOR_REPACK/DCS_V4_T00C_DCI_EXACT_DONOR_REPACK.pdsprj
4. DCS_V4_T01_DCV_6_RCL_FIRST_KEEP_POWER_GROUND/DCS_V4_T01_DCV_6_RCL_FIRST_KEEP_POWER_GROUND.pdsprj
5. DCS_V4_T02_DCV_6_SOURCE_FIRST_KEEP_POWER_GROUND/DCS_V4_T02_DCV_6_SOURCE_FIRST_KEEP_POWER_GROUND.pdsprj
6. DCS_V4_T03_DCV_6_RCL_FIRST_REPLACE_POWER/DCS_V4_T03_DCV_6_RCL_FIRST_REPLACE_POWER.pdsprj
7. DCS_V4_T04_DCV_6_SOURCE_FIRST_REPLACE_POWER/DCS_V4_T04_DCV_6_SOURCE_FIRST_REPLACE_POWER.pdsprj
8. DCS_V4_T05_DCI_6_RCL_FIRST_REPLACE_POWER/DCS_V4_T05_DCI_6_RCL_FIRST_REPLACE_POWER.pdsprj
9. DCS_V4_T06_DCI_6_SOURCE_FIRST_REPLACE_POWER/DCS_V4_T06_DCI_6_SOURCE_FIRST_REPLACE_POWER.pdsprj
10. DCS_V4_T07_DCV_21_RCL_FIRST_REPLACE_POWER/DCS_V4_T07_DCV_21_RCL_FIRST_REPLACE_POWER.pdsprj
11. DCS_V4_T08_DCI_21_RCL_FIRST_REPLACE_POWER/DCS_V4_T08_DCI_21_RCL_FIRST_REPLACE_POWER.pdsprj
