ProGenEDA/ProGenEDA-DEV/proteus/experiments/runs/ac_voltage_v2_nonfinal_source_unit_temp_2026_06_04/ACV_V2_NONFINAL_SOURCE_UNIT_TEST_BATCH/README_TEST_ORDER.txt

AC voltage V2 non-final source-unit diagnostics.

Open in order:
1. ACV_V2_T00_TWO_SOURCE_TRANSPLANT_CONTROL/ACV_V2_T00_TWO_SOURCE_TRANSPLANT_CONTROL.pdsprj
2. ACV_V2_T01_RCL_AV_A0_NO_SOURCE_CONTROL/ACV_V2_T01_RCL_AV_A0_NO_SOURCE_CONTROL.pdsprj
3. ACV_V2_T02_SIMPLE_LOOP_TWO_SOURCE_NONFINAL/ACV_V2_T02_SIMPLE_LOOP_TWO_SOURCE_NONFINAL.pdsprj
4. ACV_V2_T03_SIX_COMPONENT_TWO_SOURCE_NONFINAL/ACV_V2_T03_SIX_COMPONENT_TWO_SOURCE_NONFINAL.pdsprj
5. ACV_V2_T04_21_RULE_TWO_SOURCE_NONFINAL/ACV_V2_T04_21_RULE_TWO_SOURCE_NONFINAL.pdsprj
6. ACV_V2_T05_SIMPLE_LOOP_STANDALONE_TRIMMED/ACV_V2_T05_SIMPLE_LOOP_STANDALONE_TRIMMED.pdsprj
7. ACV_V2_T06_SIX_COMPONENT_STANDALONE_TRIMMED/ACV_V2_T06_SIX_COMPONENT_STANDALONE_TRIMMED.pdsprj

T02-T04 are the primary candidates: exact non-final AV/A0 source unit from the two-source donor.
T05-T06 isolate whether length trimming alone is sufficient with standalone suffixes.
