ProGenEDA/ProGenEDA-DEV/proteus/experiments/runs/frozen_43_family_mix_matrix_v1_temp_2026_07_16/02_original_order_full_pointer_3x/diagnostics/ctrl_s_after_error/02_after_ok.png

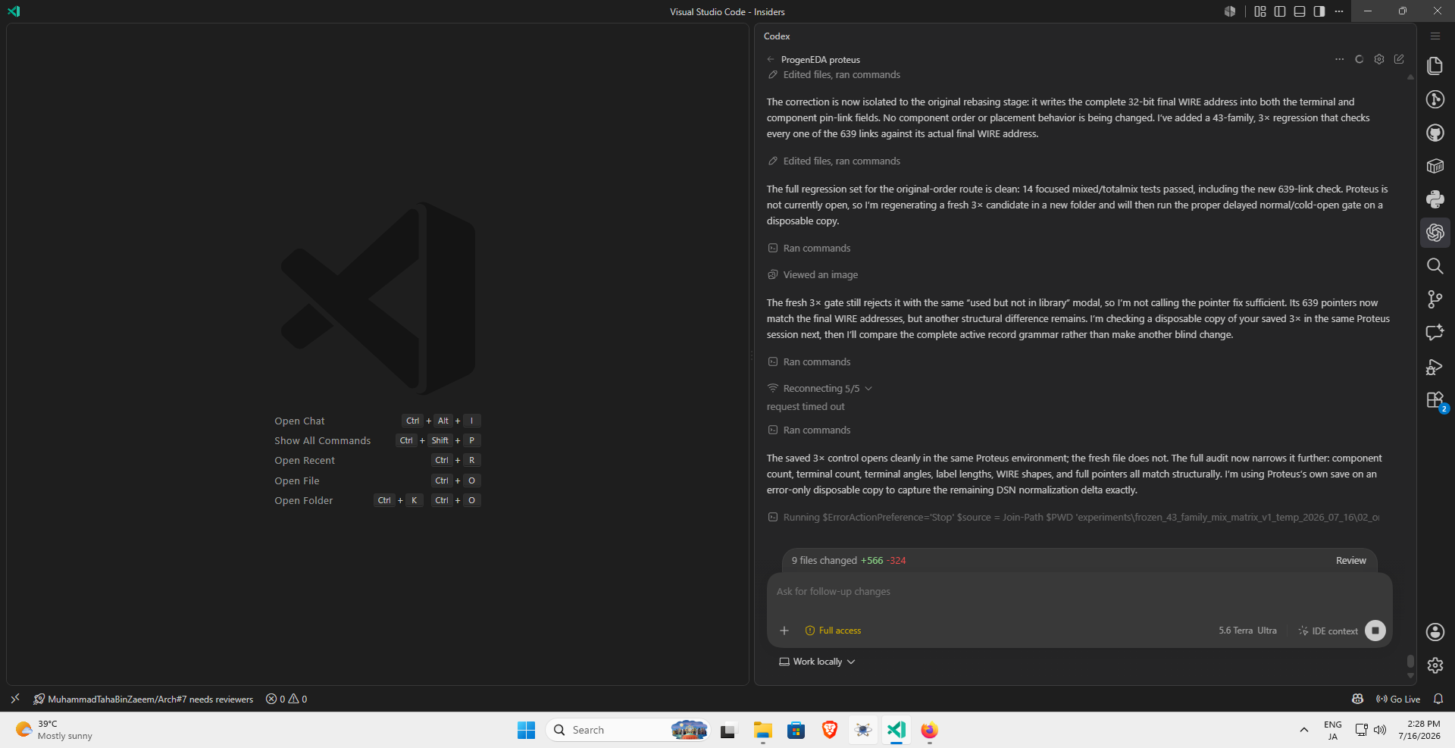
proteus/experiments/runs/frozen_43_family_mix_matrix_v1_temp_2026_07_16/02_original_order_full_pointer_3x/diagnostics/ctrl_s_after_error/02_after_ok.png
