ProGenEDA/ProGenEDA-DEV/proteus/experiments/runs/frozen_43_family_mix_matrix_v1_temp_2026_07_16/02_original_order_full_pointer_3x/diagnostics/family_domain_isolation_v2/local_proteus_gate/D01_native_plus_pot_normal.png

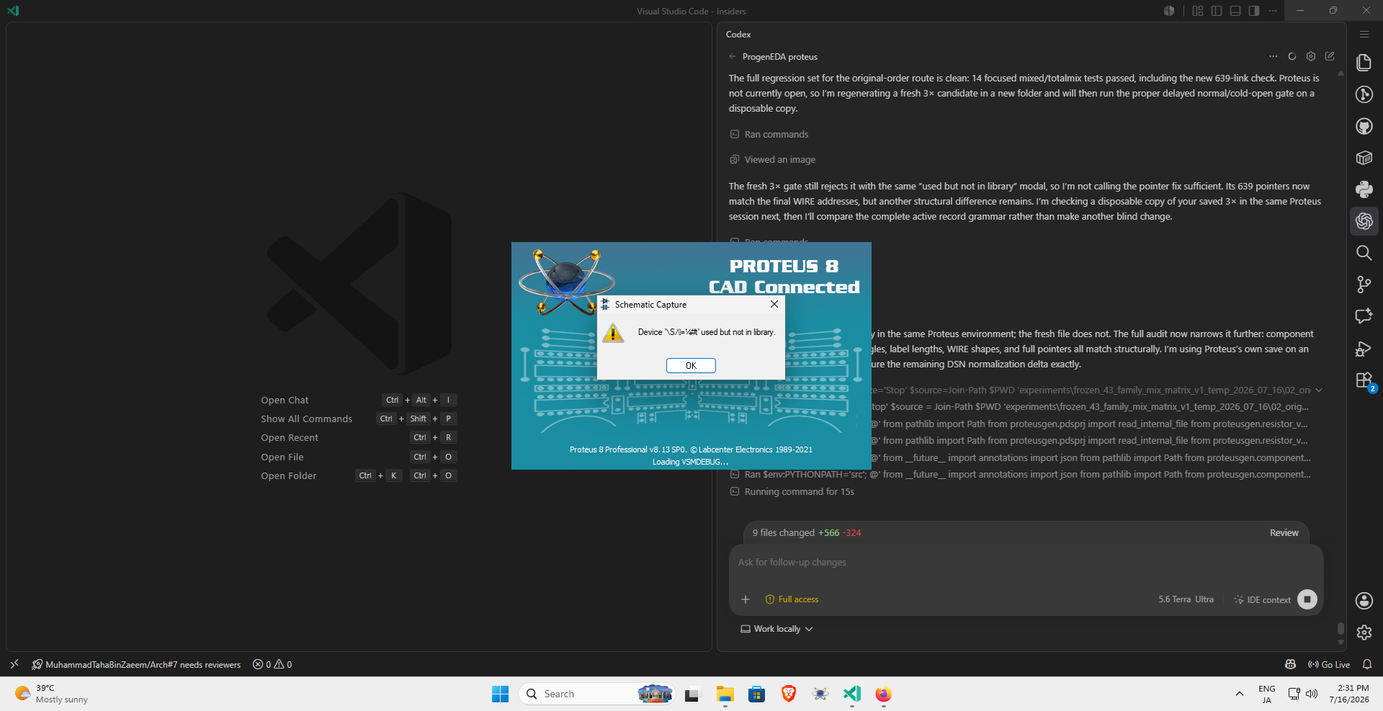
proteus/experiments/runs/frozen_43_family_mix_matrix_v1_temp_2026_07_16/02_original_order_full_pointer_3x/diagnostics/family_domain_isolation_v2/local_proteus_gate/D01_native_plus_pot_normal.png
