ProGenEDA/ProGenEDA-DEV/proteus/experiments/runs/three_pin_bjt_proteus_opened_1x_v41_temp_2026_07_11/03_live_proteus_visual_audit/T001_NPN_printwindow.png

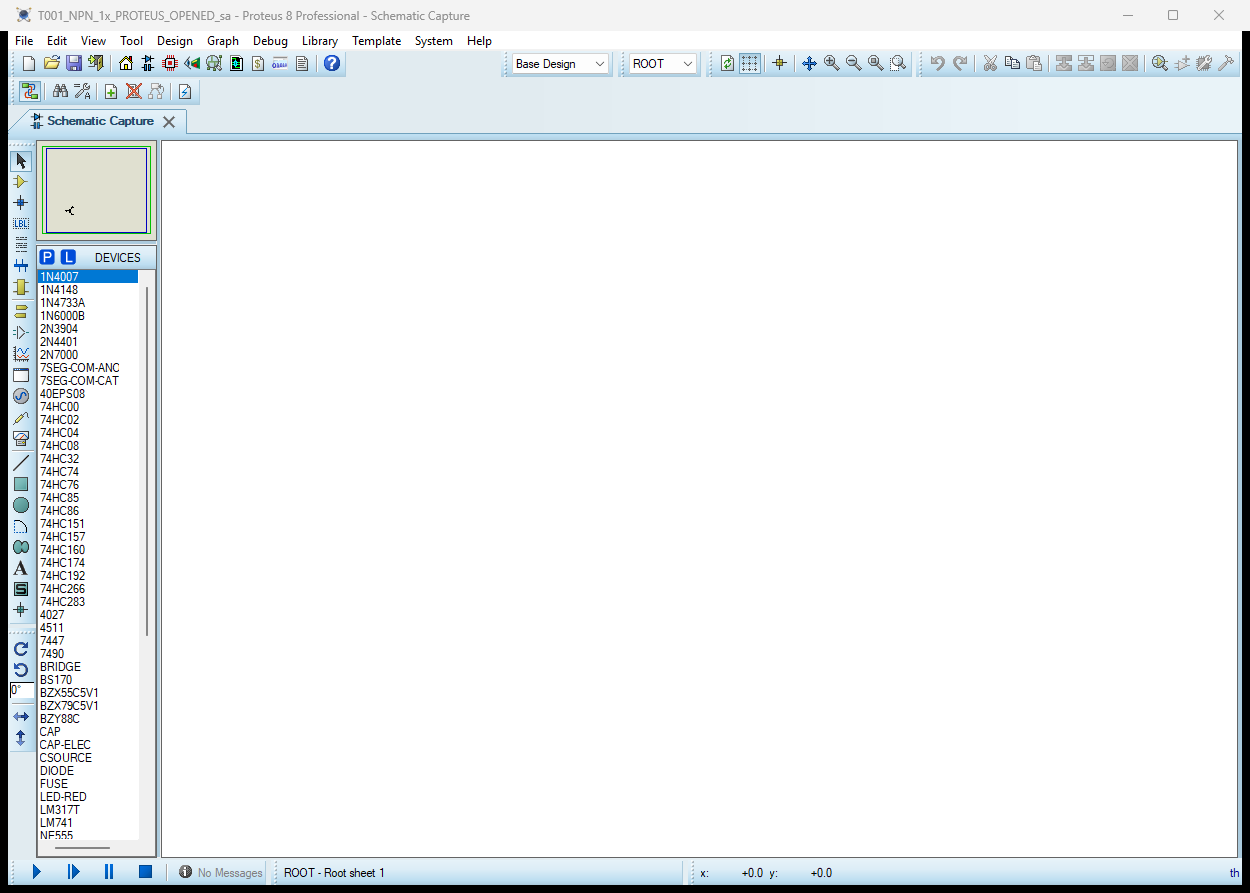
proteus/experiments/runs/three_pin_bjt_proteus_opened_1x_v41_temp_2026_07_11/03_live_proteus_visual_audit/T001_NPN_printwindow.png
