ProGenEDA/ProGenEDA-DEV/proteus/experiments/runs/dil16_decoder_7447_terminal_v3_temp_2026_07_15/README.md

# 7447 terminal revalidation - 2026-07-15

Placement uses the locked mega donor
`proteus_ic/donors/manual_downloads_20260618/new_component_mega/new_components_5x_mega.pdsprj`.
Terminal evidence is
`proteus_ic/donors/terminalized_catalogue_evidence/dil16_decoder_driver/7447/7447_terminalized_primary.pdsprj`.

All files use the shared component/terminal placers. `01_solo_1x` contains the
control, native/grid diagnostics and complete 1x; `03_scale_9x_15x` contains
controls and complete 9x/15x files. The final routes have 14/126/210
grid-aligned nonzero terminal-to-pin WIREs.

Every 1x diagnostic and complete 1x/9x/15x final passed normal/cold local
Proteus gates with unchanged disposable copies. The 15x capture is
`03_scale_9x_15x/S15_7447_15X_COMPLETE_GATE_INITIAL_before_close.png`.
