ProGenEDA/ProGenEDA-DEV/proteus/experiments/runs/dil16_decoder_driver_4511_terminal_v2_temp_2026_07_14/README.md

# 4511 fresh terminal-route revalidation

This evidence pack regenerates the 4511 profile through the locked mega and
the existing unified shared terminal placer. It adds no family-specific script.

- `01_staged_1x/` contains a control and all three 1x stages.
- `03_scale_9x_15x/` contains controls and complete 9x/15x outputs.
- Gate folders contain screenshots; disposable `_COPY.pdsprj` files are not
  source artifacts.

All stages and both scales normal-opened/cold-reopened without a modal error
or save. The active outputs contain 14/126/210 grid-aligned nonzero
terminal/WIRE units at 1x/9x/15x. Full donor evidence is in
`knowledge/dil16_decoder_driver_4511_donor_revalidation_preflight_2026_07_14.md`.
