ProGenEDA/ProGenEDA-DEV/proteus/experiments/runs/dil16_dual_jk_ff_terminal_v2_temp_2026_07_13/README.md

# DIL16 dual JK terminal v2 — 2026-07-13

## S02 4027 1x

`S02_4027_1X_NO_TERMINAL.pdsprj` is a component-placer plus beautifier
control. `S02_4027_1X_CATALOGUE_TERMINAL_sa.pdsprj` is emitted only through
the shared `component_terminal_placer.py` and the 4027 catalogue profile.

The requested `terminal_grid_alignment` layout option keeps native 4027 pin
frames on the Proteus 254000-unit terminal grid before terminal placement. The
terminal stream has 14 donor-labelled bidirectional terminals and 14
donor-shaped zero-length native WIRE units; both physical subparts are present.

Static DSN validation passed. Local Proteus cold-open/cold-reopen remains
pending because the user's existing Proteus window was deliberately not closed
or interrupted. A normal open will not be saved; only a dismissed Bad Object
Record would trigger a disposable-copy save-and-compare check.

## Staged loader proof

`00_staged_loader_diagnostics/` contains the same locked-mega 1× placement
through the required shared-terminal sequence:

1. `S02_4027_STAGE0_NO_TERMINAL.pdsprj` — component-placer/beautifier control.
2. `S02_4027_STAGE1_NATIVE_PIN_CONTACT.pdsprj` — fourteen inactive terminals
   at their native contacts, with no WIRE or active links.
3. `S02_4027_STAGE2_GRID_CONTACT.pdsprj` — the grid-contact loader gate. It is
   byte-identical to stage 1 because the opt-in beautifier already moved the
   native 4027 pin frame by whole grid increments.
4. `S02_4027_STAGE3_ACTIVE_LINK.pdsprj` — fourteen donor-shaped active WIRE and
   link units. Its `ROOT.DSN` is byte-identical to the S02 final candidate.

Stages 1–3 are DSN-only terminal-stream variants: the terminal stage does not
read, normalize, compare, or write `ROOT.CDB`.
