ProGenEDA/ProGenEDA-DEV/proteus/experiments/runs/p2_level1_e001_ics_7seg_big_leap.md

# Project 2 Level 1 - E001 IC + 7SEG Big-Leap Pack

Status: **withdrawn / superseded**.

This file previously documented a speculative post-CEP trial pack. That pack caused repeated ISIS issues and was not reliable enough to remain in active memory.

## Current rule

Do not use this pack or its assumptions as active generation strategy.

## Reason for withdrawal

- The tests still produced the same ISIS issue.
- The source selection likely included an incompatible project family.
- The generator direction was too speculative for the available validated template data.

## Replacement direction

Use the known-good E001 base and build only from validated, isolated template groups.

Future attempts should be staged in smaller verified steps:

1. E001 repack control.
2. One validated template group on E001.
3. Two validated template groups on E001.
4. Full circuit only after the first three pass.

This placeholder remains only to preserve history and prevent broken references.
