ProGenEDA/ProGenEDA-DEV/proteus/experiments/runs/e001_cdb_written_r7_r12_test_results_success.md

# E001 CDB-Written R7/R12 Test Results: Success

## User test result

The user tested the pack:

```text
E001_CDB_WRITTEN_R7_R12_GENERATION_SHOT.zip
```

Reported result:

```text
All 4 tests worked.
All 4 tests simulated as well.
```

This confirms that the E001-based generation attempt succeeded for isolated resistor circuits with generated CDB and rebuilt DSN.

## Important distinction: copied vs generated

This attempt was not a full R4 project copy.

Used from E001:

```text
PROJECT.XML
SCRIPTS/PWRRAILS.DAT
blank/root project shell
```

Generated:

```text
ROOT.CDB for N resistors
ROOT.DSN resistor placement records for N resistors
section offsets/pointers around ISIS CIRCUIT FILE / OBJECT DATA
component refs/values/positions
```

Used from real R4 only as structural donor/reference:

```text
resistor device-definition block in ROOT.DSN
known-good 346-byte visible resistor record schema
R4 CDB as validation target for build_cdb(4)
```

The CDB writer was deterministic and validated by:

```text
build_cdb(4) == real R4 ROOT.CDB
```

So the breakthrough is:

```text
The generator can emit a coherent ROOT.CDB and ROOT.DSN from E001 for isolated resistor banks.
```

## What this proves

1. ROOT.DSN-visible-only extension is enough for visual schematic display but not enough for simulation.
2. ROOT.CDB generation is required for model/netlist recognition.
3. The reconstructed CDBCORE stream order and resistor ELEMENT/PART records are correct enough for Proteus 8.13 to simulate generated resistor banks.
4. The earlier missing-model errors for R5+ were caused by missing/incoherent CDB records, not purely by DSN pointer mistakes.
5. The E001 base can now be used as a clean starting project for resistor generation, avoiding dependence on full R4 as project base.

## Current validated capability

Validated by user:

```text
E001 -> R7 resistor circuit: opens and simulates
E001 -> R12 resistor circuit: opens and simulates
```

The pack included both E0-tail and R4-tail variants. The user stated all four tests worked and simulated.

## Remaining limitations

The current resistor generator is still constrained by:

```text
fixed-width two-character ref/value patches for this phase
R10/R11/R12 represented temporarily as RA/RB/RC and Ak/Bk/Ck in some tests
only isolated unconnected resistors tested
wire/net generation not validated yet
terminal endpoint association not validated yet
other component families not validated yet
```

## Next milestone

The immediate next milestone should be:

```text
Generate a resistor circuit from E001 with wires and terminals, with CDB written coherently.
```

Suggested next tests:

```text
1. E001 -> 4 resistors with both ends connected to terminals.
2. E001 -> 7 resistors in a visually arranged grid, all CDB-backed.
3. E001 -> resistor series chain with wire records and terminals.
4. E001 -> resistor parallel network with wire records and terminals.
```

Do not jump to ICs until wire/net/terminal serialization is validated.
