ProGenEDA/ProGenEDA-DEV/proteus/experiments/runs/multi_pin_catalogue_terminal_solo_v6_temp_2026_07_04/README_TEST_FIRST.md

# Multi-pin catalogue terminal solo V6

Open the listed cases in Proteus. V6 specifically fixes 4027 subpart anchors, 74HC4060 body-marker movement, and 74HC192 pin 5/pin 9 separation.
