ProGenEDA/ProGenEDA-DEV/proteus/experiments/runs/multi_pin_missing_terminal_donor_bases_v1_temp_2026_07_04/README_TEST_FIRST.md

# Missing-terminal donor base pack

These are component-placer outputs with no terminal-placement stage. Add correct terminals/wires manually in Proteus, save, and return the saved projects as donor evidence. Cases marked static-invalid are included for triage, not acceptance.
