ProGenEDA/ProGenEDA-DEV/proteus/experiments/runs/capacitor_network_v3_diagnostic_attempts_2026-05-30/test_result_v3_failed_stop_codex_handoff.md

# Test Result: V3 Capacitor Diagnostic Failed — Stop Assistant Generation

## User test result

The user tested the V3 capacitor diagnostic pack:

```text
CAPACITOR_NETWORK_V3_DIAGNOSTIC_ATTEMPTS_2026_05_30.zip
```

Observed results:

```text
T02 gave a Proteus VGDVC error.
T04 gave a Proteus VGDVC error.
T03 first gave a Proteus loading dialog saying a device was used but not found in the library, then later also produced a VGDVC error.
```

## User decision

Stop further ChatGPT-generated capacitor attempts.

The next stage should be handled by Codex or a local agent with actual repository access, local execution, and repeatable binary diff tooling.

## Why V3 must not be locked

V3 correctly identified that V2 copied the resistor object-order assumption incorrectly, but V3 still failed in Proteus. This means the capacitor generator remains unresolved.

Likely unresolved areas:

```text
1. Capacitor CDB expansion for n greater than 1 may be invalid or incomplete.
2. Capacitor DSN visible object may contain hidden element/part binding keys that were not patched coherently.
3. Device-library fields such as CAP10/CAP may not be replicated correctly for generated multi-cap circuits.
4. The DSN visible component record may require exact per-component keys matching ROOT.CDB ELEMENT/PART entries.
5. Repeating the apparent CAP_T02 object group is not sufficient without understanding the CDBCORE binding layer.
```

## Files/results to treat as negative evidence

```text
experiments/capacitor_network_attempts_2026-05-29/
experiments/capacitor_network_v2_attempts_2026-05-30/
experiments/capacitor_network_v3_diagnostic_attempts_2026-05-30/
```

## Important known-good baseline before capacitor

The following remains locked and working:

```text
Resistor V9 terminal generator
Power terminal donor bridge
Ground terminal short-wire endpoint
Power bridge + ground short-wire combined method
```

Relevant docs:

```text
docs/generator_method/r21_resistor_terminal_generator_v9_canonical_method.md
experiments/v9_no_premature_terminators_note.md
final/power_terminal_output_bridge_method.md
final/ground_terminal_short_wire_method.md
final/power_bridge_ground_shortwire_method.md
```

## Next owner

Codex/local agent should take over and build a real capacitor generator using local binary diff, donor comparison, and Proteus test feedback.
