ProGenEDA/ProGenEDA-DEV/proteus/experiments/runs/power_bridge_ground_input_bridge_corrected_2026-05-29/test_result_only_terminals_no_resistors.md

# Test Result: Only Terminals / No Resistors

## User test result

The user tested:

```text
CORRECTED_T03_6R_GROUND_INPUT_BRIDGE_V9_TEMPLATES
```

Result from Proteus screenshot:

```text
Only the power bridge and ground bridge appeared.
No resistor network appeared.
The ground terminal bridge was also not visually connected correctly.
```

## Interpretation

This means the corrected T03/T04 approach was still wrong.

The likely cause is that the experimental ground bridge was inserted before the normal resistor object stream:

```text
00 + power_bridge + ground_bridge + normal_resistor_stream
```

Proteus displayed the bridge objects but did not continue into the resistor network properly. Therefore, the experimental ground bridge object sequence is still unsafe when placed before the generated resistor objects.

## Corrective action

A new attempt was created that preserves the working object order first:

```text
00 + exact working power bridge + normal resistor stream + experimental ground input bridge
```

This means the resistor network is parsed before the experimental ground bridge.

New experiment folder:

```text
experiments/power_bridge_ground_input_bridge_appended_2026-05-29/
```

## Locked fallback remains valid

The locked working method is still:

```text
Power = exact donor bridge
Ground = short-wire endpoint
```

Recorded at:

```text
final/power_bridge_ground_shortwire_method.md
```

If the appended ground bridge also fails, stop ground bridge work and keep the locked fallback only.
