ProGenEDA/ProGenEDA-DEV/proteus/experiments/runs/json_input_smoke_2026_05_30/README_TEST_FIRST.txt

SINGLE_R_POWER_GROUND

Open this generated project in Proteus 8.13 after checking the E001 base if needed.

Project: SINGLE_R_POWER_GROUND.pdsprj
Static validation issues: []

Current locked endpoint rules:
- V0/power nodes on component.nodes[0] become $TERPOWER endpoints.
- G0/ground nodes on component.nodes[1] become $TERGROUND endpoints.
- Other endpoints use V9 input/output terminal labels.
