ProGenEDA/ProGenEDA-DEV/proteus/experiments/runs/resistor_generator_locked_main_smoke_2026_05_30/generator_version.txt

proteusgen resistor_v9 locked method
base_fixture=e001_empty
donor_fixture=r21_v9_resistor_terminal_donor
power_bridge_fixture=power_terminal_bridge_donor
