ProGenEDA/ProGenEDA-DEV/proteus/experiments/runs/resistor_generator_locked_main_smoke_2026_05_30/README_TEST_FIRST.txt

SINGLE_R_POWER_GROUND

Open this generated project in Proteus 8.13 after checking the E001 base if needed.

Project: SINGLE_R_POWER_GROUND.pdsprj
Static validation issues: []

Current locked endpoint rules:
- V0/power nodes use one donor-derived $TERPOWER -> $TEROUTPUT(V0) bridge.
- Powered resistor endpoints remain normal $TERINPUT(V0) terminals.
- G0/ground nodes on component.nodes[1] become $TERGROUND endpoints.
- Other endpoints use V9 input/output terminal labels.
Production safety rules:
- Dense manual positions may be stretched to the safe V9 grid.
- Standalone layout.visual_wires are skipped until VGDVC-safe records are validated.
