ProGenEDA/ProGenEDA-DEV/proteus/experiments/runs/terminal_placer_grid_wire_v10_temp_2026_07_02/V10_01_RESISTOR_3X_NATIVE_ORACLE/TEST.txt

Case: V10_01_RESISTOR_3X_NATIVE_ORACLE
Components: 4
Terminals: 6
Wires: 6
Method: active terminal + matching component link + adjacent native WIRE
Check Bad Object Record, render, attachment, Ctrl+S persistence, and simulation.
