ProGenEDA/ProGenEDA-DEV/proteus/experiments/runs/terminal_placer_grid_wire_v10_temp_2026_07_02/V10_07_MIXED_ALL_1X_WITH_CONTROLS/TEST.txt

Case: V10_07_MIXED_ALL_1X_WITH_CONTROLS
Components: 10
Terminals: 12
Wires: 12
Method: active terminal + matching component link + adjacent native WIRE
Check Bad Object Record, render, attachment, Ctrl+S persistence, and simulation.
