ProGenEDA/ProGenEDA-DEV/proteus/experiments/runs/terminal_placer_grid_wire_v10_temp_2026_07_02/V10_09_MIXED_ALL_15X_WITH_CONTROLS/TEST.txt

Case: V10_09_MIXED_ALL_15X_WITH_CONTROLS
Components: 94
Terminals: 180
Wires: 180
Method: active terminal + matching component link + adjacent native WIRE
Check Bad Object Record, render, attachment, Ctrl+S persistence, and simulation.
