ProGenEDA/ProGenEDA-DEV/proteus/experiments/runs/terminal_placer_mixed_overlay_v3_temp_2026_07_01/T00_ALL_BARE_SEPARATED_BANDS/TEST.txt

Case: T00_ALL_BARE_SEPARATED_BANDS
Terminal families: NONE
Expected terminals: 0
Expected wires: 0
IC/non-IC clearance: 5080000
Open the project without _BASE in Proteus.
