ProGenEDA/ProGenEDA-DEV/proteus/experiments/runs/terminal_placer_mixed_overlay_v3_temp_2026_07_01/T01_APPENDED_TERMINALS_OPENING_ORDER/TEST.txt

Case: T01_APPENDED_TERMINALS_OPENING_ORDER
Terminal families: RESISTOR, CAP, REALIND, CAP-ELEC, VSOURCE, CSOURCE
Expected terminals: 12
Expected wires: 0
IC/non-IC clearance: 5080000
Open the project without _BASE in Proteus.
