ProGenEDA/ProGenEDA-DEV/proteus/experiments/runs/terminal_placer_mixed_overlay_v3_temp_2026_07_01/T02_FULL_ATTACHMENT_OVERLAY/TEST.txt

Case: T02_FULL_ATTACHMENT_OVERLAY
Terminal families: RESISTOR, CAP, REALIND, CAP-ELEC, VSOURCE, CSOURCE
Expected terminals: 12
Expected wires: 12
IC/non-IC clearance: 5080000
Open the project without _BASE in Proteus.
