ProGenEDA/ProGenEDA-DEV/proteus/experiments/runs/terminal_placer_mixed_overlay_v3_temp_2026_07_01/T03_PASSIVE_ATTACHMENT_OVERLAY/TEST.txt

Case: T03_PASSIVE_ATTACHMENT_OVERLAY
Terminal families: RESISTOR, CAP, REALIND, CAP-ELEC
Expected terminals: 8
Expected wires: 8
IC/non-IC clearance: 5080000
Open the project without _BASE in Proteus.
