ProGenEDA/ProGenEDA-DEV/proteus/experiments/runs/terminal_placer_mixed_overlay_v3_temp_2026_07_01/T04_SOURCE_ATTACHMENT_OVERLAY/TEST.txt

Case: T04_SOURCE_ATTACHMENT_OVERLAY
Terminal families: VSOURCE, CSOURCE
Expected terminals: 4
Expected wires: 4
IC/non-IC clearance: 5080000
Open the project without _BASE in Proteus.
