ProGenEDA/ProGenEDA-DEV/proteus/experiments/runs/terminal_placer_mixed_selective_v1_temp_2026_06_30/T01_ALL_ACCEPTED_1X_WITH_CONTROLS/TEST.txt

Case: T01_ALL_ACCEPTED_1X_WITH_CONTROLS
Accepted components: 6
Negative controls: 3
Expected terminals: 12
Expected short wires: 12
Open the project without _BASE for Proteus testing.
