ProGenEDA/ProGenEDA-DEV/proteus/experiments/runs/terminal_placer_mixed_selective_v1_temp_2026_06_30/T02_ALL_ACCEPTED_3X_WITH_CONTROLS/TEST.txt

Case: T02_ALL_ACCEPTED_3X_WITH_CONTROLS
Accepted components: 18
Negative controls: 7
Expected terminals: 36
Expected short wires: 36
Open the project without _BASE for Proteus testing.
