ProGenEDA/ProGenEDA-DEV/proteus/experiments/runs/terminal_placer_mixed_selective_v1_temp_2026_06_30/T03_NONTERMINAL_CONTROLS_ONLY/TEST.txt

Case: T03_NONTERMINAL_CONTROLS_ONLY
Accepted components: 0
Negative controls: 7
Expected terminals: 0
Expected short wires: 0
Open the project without _BASE for Proteus testing.
