ProGenEDA/ProGenEDA-DEV/proteus/experiments/runs/terminal_placer_short_wire_v6_temp_2026_07_01/T01_GENERATED_CTRL_S_EQUIVALENT/TEST.txt

Case: T01_GENERATED_CTRL_S_EQUIVALENT
Terminals: 2
Wires: 0
Connection method: short WIRE only
Check Bad Object Record, render, orientation, attachment, and simulation.
