ProGenEDA/ProGenEDA-DEV/proteus/experiments/runs/terminal_placer_short_wire_v6_temp_2026_07_01/T02_RESISTOR_1X_SHORT_WIRE/TEST.txt

Case: T02_RESISTOR_1X_SHORT_WIRE
Terminals: 2
Wires: 2
Connection method: short WIRE only
Check Bad Object Record, render, orientation, attachment, and simulation.
