ProGenEDA/ProGenEDA-DEV/proteus/experiments/runs/terminal_placer_short_wire_v6_temp_2026_07_01/T03_RESISTOR_3X_SHORT_WIRE/TEST.txt

Case: T03_RESISTOR_3X_SHORT_WIRE
Terminals: 6
Wires: 6
Connection method: short WIRE only
Check Bad Object Record, render, orientation, attachment, and simulation.
