ProGenEDA/ProGenEDA-DEV/proteus/experiments/runs/terminal_placer_short_wire_v6_temp_2026_07_01/T05_MIXED_1X_SHORT_WIRE/TEST.txt

Case: T05_MIXED_1X_SHORT_WIRE
Terminals: 12
Wires: 12
Connection method: short WIRE only
Check Bad Object Record, render, orientation, attachment, and simulation.
