ProGenEDA/ProGenEDA-DEV/proteus/experiments/runs/terminal_placer_short_wire_v6_temp_2026_07_01/T07_MIXED_15X_SHORT_WIRE/TEST.txt

Case: T07_MIXED_15X_SHORT_WIRE
Terminals: 180
Wires: 180
Connection method: short WIRE only
Check Bad Object Record, render, orientation, attachment, and simulation.
