ProGenEDA/ProGenEDA-DEV/proteus/experiments/runs/handdrawn_6r_2026-05-29/attempt_02_corrected_topology/record.md

# Attempt 02 Corrected Topology

## Status

Generated after user corrected the assistant's first circuit interpretation.

## Source

```text
source_image_filename: WhatsApp Image 2026-05-28 at 11.20.59 PM.jpeg
source_image_sha256: 8f8f1327b8efc71473b541b1f0198e4871e47b30e75059260ad5e8781ff0a0a4
```

## Corrected interpretation

```text
Left side is common node N0.
Top-right node is N1.
Middle-right node is N2.
Lower-middle node is N3.
Bottom-right node is N4.
```

## Generated topology

```text
R1: N0 - N1
R2: N1 - N2
R3: N0 - N2
R4: N2 - N3
R5: N3 - N4
R6: N0 - N4
```

## Loop reading

```text
Top loop:    N0 - R1 - N1 - R2 - N2 - R3 - N0
Bottom loop: N0 - R3 - N2 - R4 - N3 - R5 - N4 - R6 - N0
```

## Output

```text
project_file: HANDDRAWN_6R_CORRECTED_N0_N1_N2_N3_N4.pdsprj
project_file_sha256: 2f5eb8226c825736ca5ff15dd48177c3c5b9c52364f9eeea9f2bf9ba62018476
zip_file: HANDDRAWN_6R_CORRECTED_TOPOLOGY_GENERATION.zip
zip_size_bytes: 39449
zip_sha256: e54b7c0be48798635a6942b08b4237096e96408b57de87c15682451ac9784f7a
static_validation_issues: []
```

## Known limitation

The current validated V9 method emits horizontal linked terminal/resistor/wire groups. This corrected file is topology-correct by node labels, but R2, R4, and R5 are not physically rotated vertical symbols yet.

## Next validation

```text
1. Open the corrected project in Proteus 8.13.
2. Save-as/reopen and compare repaired ROOT.DSN / ROOT.CDB.
3. Record any netlist/simulation warnings.
4. Add real rotated resistor support later.
```
