ProGenEDA/ProGenEDA-DEV/proteus/experiments/runs/capacitor_v10_manual_donor_temp_2026_05_31/CAP_V10_T03_TRANSLATED_MANUAL_ORDER/README_TEST_FIRST.txt

CAP_V10_T03_TRANSLATED_MANUAL_ORDER

Two generated terminal-attached capacitors in manual order, translated to a safer vertical spacing.

Project: CAP_V10_T03_TRANSLATED_MANUAL_ORDER.pdsprj
Static validation issues: []
