ProGenEDA/ProGenEDA-DEV/proteus/experiments/runs/capacitor_v10_manual_donor_temp_2026_05_31/CAP_V10_T04_RENAMED_VALUE_MANUAL_ORDER/README_TEST_FIRST.txt

CAP_V10_T04_RENAMED_VALUE_MANUAL_ORDER

Two generated terminal-attached capacitors in manual order with new refs, terminal labels, and 1uF values.

Project: CAP_V10_T04_RENAMED_VALUE_MANUAL_ORDER.pdsprj
Static validation issues: []
