ProGenEDA/ProGenEDA-DEV/proteus/experiments/runs/capacitor_v10_manual_donor_temp_2026_05_31/CAP_V10_T05_THREE_TERMINAL_CAPS_MANUAL_ORDER/README_TEST_FIRST.txt

CAP_V10_T05_THREE_TERMINAL_CAPS_MANUAL_ORDER

Three generated terminal-attached capacitors using the same outputs-first manual order and extrapolated suffixes.

Project: CAP_V10_T05_THREE_TERMINAL_CAPS_MANUAL_ORDER.pdsprj
Static validation issues: []
