ProGenEDA/ProGenEDA-DEV/proteus/experiments/runs/capacitor_v11_networks_temp_2026_05_31/CAP_V11_T01_6C_SAME_TOPOLOGY_AS_6R/README_TEST_FIRST.txt

CAP_V11_T01_6C_SAME_TOPOLOGY_AS_6R

Six-capacitor version of the corrected hand-drawn 6R topology.

Project: CAP_V11_T01_6C_SAME_TOPOLOGY_AS_6R.pdsprj
Capacitors: 6
Static validation issues: []
