ProGenEDA/ProGenEDA-DEV/proteus/experiments/runs/capacitor_v11_networks_temp_2026_05_31/CAP_V11_T02_21C_SAME_TOPOLOGY_AS_R21/README_TEST_FIRST.txt

CAP_V11_T02_21C_SAME_TOPOLOGY_AS_R21

Twenty-one-capacitor version of the R21 7+7+7 topology.

Project: CAP_V11_T02_21C_SAME_TOPOLOGY_AS_R21.pdsprj
Capacitors: 21
Static validation issues: []
