ProGenEDA/ProGenEDA-DEV/proteus/experiments/runs/capacitor_v12_requested15_temp_2026_05_31/01_SIMPLE_LOOP/README_TEST_FIRST.txt

01_SIMPLE_LOOP

Capacitor version of the matching requested resistor circuit.

Project: 01_SIMPLE_LOOP.pdsprj
Capacitors: 1
Static validation issues: []
