ProGenEDA/ProGenEDA-DEV/proteus/experiments/runs/capacitor_v12_requested15_temp_2026_05_31/02_SERIES_CIRCUIT/README_TEST_FIRST.txt

02_SERIES_CIRCUIT

Capacitor version of the matching requested resistor circuit.

Project: 02_SERIES_CIRCUIT.pdsprj
Capacitors: 4
Static validation issues: []
