ProGenEDA/ProGenEDA-DEV/proteus/experiments/runs/capacitor_v12_requested15_temp_2026_05_31/04_SERIES_PARALLEL_COMBO/README_TEST_FIRST.txt

04_SERIES_PARALLEL_COMBO

Capacitor version of the matching requested resistor circuit.

Project: 04_SERIES_PARALLEL_COMBO.pdsprj
Capacitors: 4
Static validation issues: []
