ProGenEDA/ProGenEDA-DEV/proteus/experiments/runs/capacitor_v12_requested15_temp_2026_05_31/06_MULTI_STEP_VOLTAGE_DIVIDER/README_TEST_FIRST.txt

06_MULTI_STEP_VOLTAGE_DIVIDER

Capacitor version of the matching requested resistor circuit.

Project: 06_MULTI_STEP_VOLTAGE_DIVIDER.pdsprj
Capacitors: 5
Static validation issues: []
