ProGenEDA/ProGenEDA-DEV/proteus/experiments/runs/capacitor_v12_requested15_temp_2026_05_31/07_CURRENT_DIVIDER/README_TEST_FIRST.txt

07_CURRENT_DIVIDER

Capacitor version of the matching requested resistor circuit.

Project: 07_CURRENT_DIVIDER.pdsprj
Capacitors: 5
Static validation issues: []
