ProGenEDA/ProGenEDA-DEV/proteus/experiments/runs/capacitor_v12_requested15_temp_2026_05_31/08_DELTA_NETWORK/README_TEST_FIRST.txt

08_DELTA_NETWORK

Capacitor version of the matching requested resistor circuit.

Project: 08_DELTA_NETWORK.pdsprj
Capacitors: 3
Static validation issues: []
