ProGenEDA/ProGenEDA-DEV/proteus/experiments/runs/capacitor_v12_requested15_temp_2026_05_31/09_STAR_Y_NETWORK/README_TEST_FIRST.txt

09_STAR_Y_NETWORK

Capacitor version of the matching requested resistor circuit.

Project: 09_STAR_Y_NETWORK.pdsprj
Capacitors: 3
Static validation issues: []
