ProGenEDA/ProGenEDA-DEV/proteus/experiments/runs/capacitor_v12_requested15_temp_2026_05_31/10_DELTA_TO_STAR_SETUP/README_TEST_FIRST.txt

10_DELTA_TO_STAR_SETUP

Capacitor version of the matching requested resistor circuit.

Project: 10_DELTA_TO_STAR_SETUP.pdsprj
Capacitors: 6
Static validation issues: []
