ProGenEDA/ProGenEDA-DEV/proteus/experiments/runs/capacitor_v12_requested15_temp_2026_05_31/13_UNBALANCED_WHEATSTONE_BRIDGE/README_TEST_FIRST.txt

13_UNBALANCED_WHEATSTONE_BRIDGE

Capacitor version of the matching requested resistor circuit.

Project: 13_UNBALANCED_WHEATSTONE_BRIDGE.pdsprj
Capacitors: 5
Static validation issues: []
