ProGenEDA/ProGenEDA-DEV/proteus/experiments/runs/capacitor_v12_requested15_temp_2026_05_31/14_H_BRIDGE_RESISTOR_VERSION/README_TEST_FIRST.txt

14_H_BRIDGE_RESISTOR_VERSION

Capacitor version of the matching requested resistor circuit.

Project: 14_H_BRIDGE_RESISTOR_VERSION.pdsprj
Capacitors: 5
Static validation issues: []
