ProGenEDA/ProGenEDA-DEV/proteus/experiments/runs/capacitor_v12_requested15_temp_2026_05_31/15_R_2R_LADDER_NETWORK/README_TEST_FIRST.txt

15_R_2R_LADDER_NETWORK

Capacitor version of the matching requested resistor circuit.

Project: 15_R_2R_LADDER_NETWORK.pdsprj
Capacitors: 9
Static validation issues: []
