ProGenEDA/ProGenEDA-DEV/proteus/experiments/runs/capacitor_v13_power_ground_spacing_temp_2026_05_31/01_SIMPLE_LOOP/README_TEST_FIRST.txt

01_SIMPLE_LOOP

Capacitor version of the matching requested resistor circuit.

This V13 pack uses wider component spacing, one $TERPOWER -> $TEROUTPUT(V0) bridge, and $TERGROUND(G0) right endpoints.

Project: 01_SIMPLE_LOOP.pdsprj
Capacitors: 1
Static validation issues: []
