ProGenEDA/ProGenEDA-DEV/proteus/experiments/runs/capacitor_v4_temp_2026_05_30/CAP_V4_T02_EXACT_T02_TERMINAL_CAP_TERMINAL/README_TEST_FIRST.txt

CAP_V4_T02_EXACT_T02_TERMINAL_CAP_TERMINAL

Exact CAP_T02 terminal-capacitor-terminal object chunk plus exact generated C1 ROOT.CDB, rebuilt from E001.

Open this project in Proteus and stop at the first error in the ordered test list.

Project: CAP_V4_T02_EXACT_T02_TERMINAL_CAP_TERMINAL.pdsprj
Static validation issues: []
