ProGenEDA/ProGenEDA-DEV/proteus/experiments/runs/capacitor_v4_temp_2026_05_30/CAP_V4_T05_TWO_ISOLATED_CAPS/README_TEST_FIRST.txt

CAP_V4_T05_TWO_ISOLATED_CAPS

Two generated CAP_T02-style groups with generated two-cap ROOT.CDB. This is expected to be the first risky case.

Open this project in Proteus and stop at the first error in the ordered test list.

Project: CAP_V4_T05_TWO_ISOLATED_CAPS.pdsprj
Static validation issues: []
