ProGenEDA/ProGenEDA-DEV/proteus/experiments/runs/capacitor_v5_cap3_temp_2026_05_30/CAP_V5_T03_TWO_FREE_CAPS_ZERO_FLAGS/README_TEST_FIRST.txt

CAP_V5_T03_TWO_FREE_CAPS_ZERO_FLAGS

Two generated free capacitor records with all component-table flags set to zero.

Project: CAP_V5_T03_TWO_FREE_CAPS_ZERO_FLAGS.pdsprj
Static validation issues: []
