ProGenEDA/ProGenEDA-DEV/proteus/experiments/runs/capacitor_v5_cap3_temp_2026_05_30/CAP_V5_T04_TWO_FREE_CAPS_DONOR_FLAG/README_TEST_FIRST.txt

CAP_V5_T04_TWO_FREE_CAPS_DONOR_FLAG

Two generated free capacitor records with the second component-table flag matching cap3's FFFFFFFF value.

Project: CAP_V5_T04_TWO_FREE_CAPS_DONOR_FLAG.pdsprj
Static validation issues: []
