ProGenEDA/ProGenEDA-DEV/proteus/experiments/runs/capacitor_v5_cap3_temp_2026_05_30/CAP_V5_T05_THREE_FREE_CAPS_TRANSLATED/README_TEST_FIRST.txt

CAP_V5_T05_THREE_FREE_CAPS_TRANSLATED

Three generated free capacitor records translated onto one safe horizontal row.

Project: CAP_V5_T05_THREE_FREE_CAPS_TRANSLATED.pdsprj
Static validation issues: []
