ProGenEDA/ProGenEDA-DEV/proteus/experiments/runs/capacitor_v5_cap3_temp_2026_05_30/CAP_V5_T06_THREE_FREE_CAPS_RENAMED/README_TEST_FIRST.txt

CAP_V5_T06_THREE_FREE_CAPS_RENAMED

Three generated free capacitor records translated and renamed C4/C5/C6.

Project: CAP_V5_T06_THREE_FREE_CAPS_RENAMED.pdsprj
Static validation issues: []
