ProGenEDA/ProGenEDA-DEV/proteus/experiments/runs/capacitor_v6_terminal_reintro_temp_2026_05_30/CAP_V6_T01_ONE_TERMINAL_CAP_PLUS_FREE_CAP/README_TEST_FIRST.txt

CAP_V6_T01_ONE_TERMINAL_CAP_PLUS_FREE_CAP

One terminal-attached capacitor plus one free capacitor; tests safe coexistence before duplicated terminal groups.

Project: CAP_V6_T01_ONE_TERMINAL_CAP_PLUS_FREE_CAP.pdsprj
Static validation issues: []
