ProGenEDA/ProGenEDA-DEV/Altium/experiments/README.md

# Altium Experiments

Every native-format, converter, or desktop-open experiment belongs in a new
dated subdirectory. Preserve the normalized input, source provenance,
generated artifacts, validation reports, screenshots where useful, and a
short outcome note. Never overwrite an accepted or rejected prior run.
