ProGenEDA/ProGenEDA-DEV/proteus/experiments/runs/beautifier_mixed_base135_allfamilies_3_15_25_v1_temp_2026_06_24/README.md

# Beautifier Mixed Component Family Counts

Generated on 2026-06-24.

This pack combines every family that passed the 2026-06-24 base135 component-family tests.
It uses the actual component placer plus the shared parsed-coordinate beautifier path.

## Donor

- `proteus_ic\donors\manual_downloads_20260618\new_component_mega\new_components_5x_mega.pdsprj`

## Families

- `REALIND`: donor inventory `100`
- `CAP-ELEC`: donor inventory `105`
- `DIODE`: donor inventory `100`
- `NPN`: donor inventory `100`
- `PNP`: donor inventory `100`
- `FUSE`: donor inventory `145`
- `1N4007`: donor inventory `105`
- `1N4148`: donor inventory `100`
- `1N4733A`: donor inventory `130`
- `1N6000B`: donor inventory `100`
- `40EPS08`: donor inventory `160`
- `BZX55C5V1`: donor inventory `100`
- `BZX79C5V1`: donor inventory `105`
- `BZY88C`: donor inventory `125`
- `LED-RED`: donor inventory `130`
- `2N3904`: donor inventory `95`
- `2N4401`: donor inventory `80`
- `2N7000`: donor inventory `70`
- `BS170`: donor inventory `75`
- `NMOSFET`: donor inventory `120`

## Cases

- `01_MIX_03X/MIX03X_ALL_BASE135.pdsprj`: 3 each, total `60`.
- `02_MIX_15X/MIX15X_ALL_BASE135.pdsprj`: 15 each, total `300`.
- `03_MIX_25X/MIX25X_ALL_BASE135.pdsprj`: 25 each, total `500`.

## User Results

Pending.

## Observation

Static generation and manifest validation passed:

- `MIX03X_ALL_BASE135`: 60 placements, 60 translated, 20 families
- `MIX15X_ALL_BASE135`: 300 placements, 300 translated, 20 families
- `MIX25X_ALL_BASE135`: 500 placements, 500 translated, 20 families
- No donor cap was hit; every case uses the requested count exactly.
