ProGenEDA/ProGenEDA-DEV/proteus/experiments/runs/catalogue_terminal_main_donor_v10_temp_2026_07_07/README.md

# Catalogue terminal main-donor V10 - 2026-07-07

Generated through the shared component placer and `src/proteusgen/component_terminal_placer.py`.

Terminalized cases:

- `S01_4511_1X_CATALOGUE_TERMINAL`: `4511` x1, terminals=14, valid=True
- `S01_4511_9X_CATALOGUE_TERMINAL`: `4511` x9, terminals=126, valid=True
- `S01_4511_15X_CATALOGUE_TERMINAL`: `4511` x15, terminals=210, valid=True
- `S01_4511_23X_CATALOGUE_TERMINAL`: `4511` x23, terminals=322, valid=True
- `S02_74HC00_1X_CATALOGUE_TERMINAL`: `74HC00` x1, terminals=12, valid=True
- `S02_74HC00_9X_CATALOGUE_TERMINAL`: `74HC00` x9, terminals=108, valid=True
- `S02_74HC00_15X_CATALOGUE_TERMINAL`: `74HC00` x15, terminals=180, valid=True
- `S02_74HC00_23X_CATALOGUE_TERMINAL`: `74HC00` x23, terminals=276, valid=True
- `S03_74HC02_1X_CATALOGUE_TERMINAL`: `74HC02` x1, terminals=12, valid=True
- `S03_74HC02_9X_CATALOGUE_TERMINAL`: `74HC02` x9, terminals=108, valid=True
- `S03_74HC02_15X_CATALOGUE_TERMINAL`: `74HC02` x15, terminals=180, valid=True
- `S03_74HC02_23X_CATALOGUE_TERMINAL`: `74HC02` x23, terminals=276, valid=True
- `S04_74HC04_1X_CATALOGUE_TERMINAL`: `74HC04` x1, terminals=12, valid=True
- `S04_74HC04_9X_CATALOGUE_TERMINAL`: `74HC04` x9, terminals=108, valid=True
- `S04_74HC04_15X_CATALOGUE_TERMINAL`: `74HC04` x15, terminals=180, valid=True
- `S04_74HC04_23X_CATALOGUE_TERMINAL`: `74HC04` x23, terminals=276, valid=True
- `S05_74HC08_1X_CATALOGUE_TERMINAL`: `74HC08` x1, terminals=12, valid=True
- `S05_74HC08_9X_CATALOGUE_TERMINAL`: `74HC08` x9, terminals=108, valid=True
- `S05_74HC08_15X_CATALOGUE_TERMINAL`: `74HC08` x15, terminals=180, valid=True
- `S05_74HC08_23X_CATALOGUE_TERMINAL`: `74HC08` x23, terminals=276, valid=True
- `S06_74HC151_1X_CATALOGUE_TERMINAL`: `74HC151` x1, terminals=14, valid=True
- `S06_74HC151_9X_CATALOGUE_TERMINAL`: `74HC151` x9, terminals=126, valid=True
- `S06_74HC151_15X_CATALOGUE_TERMINAL`: `74HC151` x15, terminals=210, valid=True
- `S06_74HC151_23X_CATALOGUE_TERMINAL`: `74HC151` x23, terminals=322, valid=True
- `S07_74HC266_1X_CATALOGUE_TERMINAL`: `74HC266` x1, terminals=12, valid=True
- `S07_74HC266_9X_CATALOGUE_TERMINAL`: `74HC266` x9, terminals=108, valid=True
- `S07_74HC266_15X_CATALOGUE_TERMINAL`: `74HC266` x15, terminals=180, valid=True
- `S07_74HC266_23X_CATALOGUE_TERMINAL`: `74HC266` x23, terminals=276, valid=True
- `S08_74HC32_1X_CATALOGUE_TERMINAL`: `74HC32` x1, terminals=12, valid=True
- `S08_74HC32_9X_CATALOGUE_TERMINAL`: `74HC32` x9, terminals=108, valid=True
- `S08_74HC32_15X_CATALOGUE_TERMINAL`: `74HC32` x15, terminals=180, valid=True
- `S08_74HC32_23X_CATALOGUE_TERMINAL`: `74HC32` x23, terminals=276, valid=True
- `S09_74HC86_1X_CATALOGUE_TERMINAL`: `74HC86` x1, terminals=12, valid=True
- `S09_74HC86_9X_CATALOGUE_TERMINAL`: `74HC86` x9, terminals=108, valid=True
- `S09_74HC86_15X_CATALOGUE_TERMINAL`: `74HC86` x15, terminals=180, valid=True
- `S09_74HC86_23X_CATALOGUE_TERMINAL`: `74HC86` x23, terminals=276, valid=True
- `S10_7SEG-COM-AN-BLUE_1X_CATALOGUE_TERMINAL`: `7SEG-COM-AN-BLUE` x1, terminals=8, valid=True
- `S10_7SEG-COM-AN-BLUE_9X_CATALOGUE_TERMINAL`: `7SEG-COM-AN-BLUE` x9, terminals=72, valid=True
- `S10_7SEG-COM-AN-BLUE_15X_CATALOGUE_TERMINAL`: `7SEG-COM-AN-BLUE` x15, terminals=120, valid=True
- `S10_7SEG-COM-AN-BLUE_23X_CATALOGUE_TERMINAL`: `7SEG-COM-AN-BLUE` x23, terminals=184, valid=True
- `S11_7SEG-COM-CAT-BLUE_1X_CATALOGUE_TERMINAL`: `7SEG-COM-CAT-BLUE` x1, terminals=8, valid=True
- `S11_7SEG-COM-CAT-BLUE_9X_CATALOGUE_TERMINAL`: `7SEG-COM-CAT-BLUE` x9, terminals=72, valid=True
- `S11_7SEG-COM-CAT-BLUE_15X_CATALOGUE_TERMINAL`: `7SEG-COM-CAT-BLUE` x15, terminals=120, valid=True
- `S11_7SEG-COM-CAT-BLUE_23X_CATALOGUE_TERMINAL`: `7SEG-COM-CAT-BLUE` x23, terminals=184, valid=True
- `S12_BRIDGE_1X_CATALOGUE_TERMINAL`: `BRIDGE` x1, terminals=4, valid=True
- `S12_BRIDGE_9X_CATALOGUE_TERMINAL`: `BRIDGE` x9, terminals=36, valid=True
- `S12_BRIDGE_15X_CATALOGUE_TERMINAL`: `BRIDGE` x15, terminals=60, valid=True
- `S12_BRIDGE_23X_CATALOGUE_TERMINAL`: `BRIDGE` x23, terminals=92, valid=True
- `S13_LM317T_1X_CATALOGUE_TERMINAL`: `LM317T` x1, terminals=3, valid=True
- `S13_LM317T_9X_CATALOGUE_TERMINAL`: `LM317T` x9, terminals=27, valid=True
- `S13_LM317T_15X_CATALOGUE_TERMINAL`: `LM317T` x15, terminals=45, valid=True
- `S13_LM317T_23X_CATALOGUE_TERMINAL`: `LM317T` x23, terminals=69, valid=True
- `S14_NMOSFET_1X_CATALOGUE_TERMINAL`: `NMOSFET` x1, terminals=3, valid=True
- `S14_NMOSFET_9X_CATALOGUE_TERMINAL`: `NMOSFET` x9, terminals=27, valid=True
- `S14_NMOSFET_15X_CATALOGUE_TERMINAL`: `NMOSFET` x15, terminals=45, valid=True
- `S14_NMOSFET_23X_CATALOGUE_TERMINAL`: `NMOSFET` x23, terminals=69, valid=True
- `S15_OPAMP_1X_CATALOGUE_TERMINAL`: `OPAMP` x1, terminals=3, valid=True
- `S15_OPAMP_9X_CATALOGUE_TERMINAL`: `OPAMP` x9, terminals=27, valid=True
- `S15_OPAMP_15X_CATALOGUE_TERMINAL`: `OPAMP` x15, terminals=45, valid=True
- `S15_OPAMP_23X_CATALOGUE_TERMINAL`: `OPAMP` x23, terminals=69, valid=True
- `S16_POT-HG_1X_CATALOGUE_TERMINAL`: `POT-HG` x1, terminals=3, valid=True
- `S16_POT-HG_9X_CATALOGUE_TERMINAL`: `POT-HG` x9, terminals=27, valid=True
- `S16_POT-HG_15X_CATALOGUE_TERMINAL`: `POT-HG` x15, terminals=45, valid=True
- `S16_POT-HG_23X_CATALOGUE_TERMINAL`: `POT-HG` x23, terminals=69, valid=True
- `S17_TRAN-2P2S_1X_CATALOGUE_TERMINAL`: `TRAN-2P2S` x1, terminals=4, valid=True
- `S17_TRAN-2P2S_9X_CATALOGUE_TERMINAL`: `TRAN-2P2S` x9, terminals=36, valid=True
- `S17_TRAN-2P2S_15X_CATALOGUE_TERMINAL`: `TRAN-2P2S` x15, terminals=60, valid=True
- `S17_TRAN-2P2S_23X_CATALOGUE_TERMINAL`: `TRAN-2P2S` x23, terminals=92, valid=True

Mixed 3x:

- `MIXED_3X_ALL_PROMOTED_CATALOGUE_TERMINAL`: status=generated, valid=True

No-terminal controls are in the `E##_..._NO_TERMINAL_CONTROL` folders.

Known not promoted:

- `4518`: user requested ignore until better evidence; no accepted terminal catalogue profile
- `74HC4520`: user requested ignore until better evidence; no accepted terminal catalogue profile
