ProGenEDA/ProGenEDA-DEV/proteus/experiments/runs/dil16_arithmetic_74hc283_terminal_v3_temp_2026_07_15/README.md

# 74HC283 terminal revalidation - 2026-07-15

Placement uses the locked mega donor
`proteus_ic/donors/manual_downloads_20260618/new_component_mega/new_components_5x_mega.pdsprj`.
Terminal evidence is
`proteus_ic/donors/terminalized_catalogue_evidence/dil16_arithmetic_compare/74HC283/74HC283_terminalized_primary.pdsprj`.

All files use the shared component placer and
`src/proteusgen/component_terminal_placer.py`. `01_solo_1x` contains the
control, native/grid diagnostics, and complete 1x; `03_scale_9x_15x` contains
controls and complete 9x/15x files. Final routes contain 14/126/210
grid-aligned nonzero terminal-to-exact-pin WIREs respectively.

Every 1x diagnostic and complete 1x/9x/15x final passed normal/cold local
Proteus gates with unchanged disposable copies. The 15x capture is
`03_scale_9x_15x/S15_74HC283_15X_COMPLETE_GATE_INITIAL_before_close.png`.
