ProGenEDA/ProGenEDA-DEV/proteus/experiments/runs/2026-07-17_executable_gate_overlay_trial/current_app_gate_bridge/exact_executable_matrix/screenshots/h04/h04_cold_open_1.png

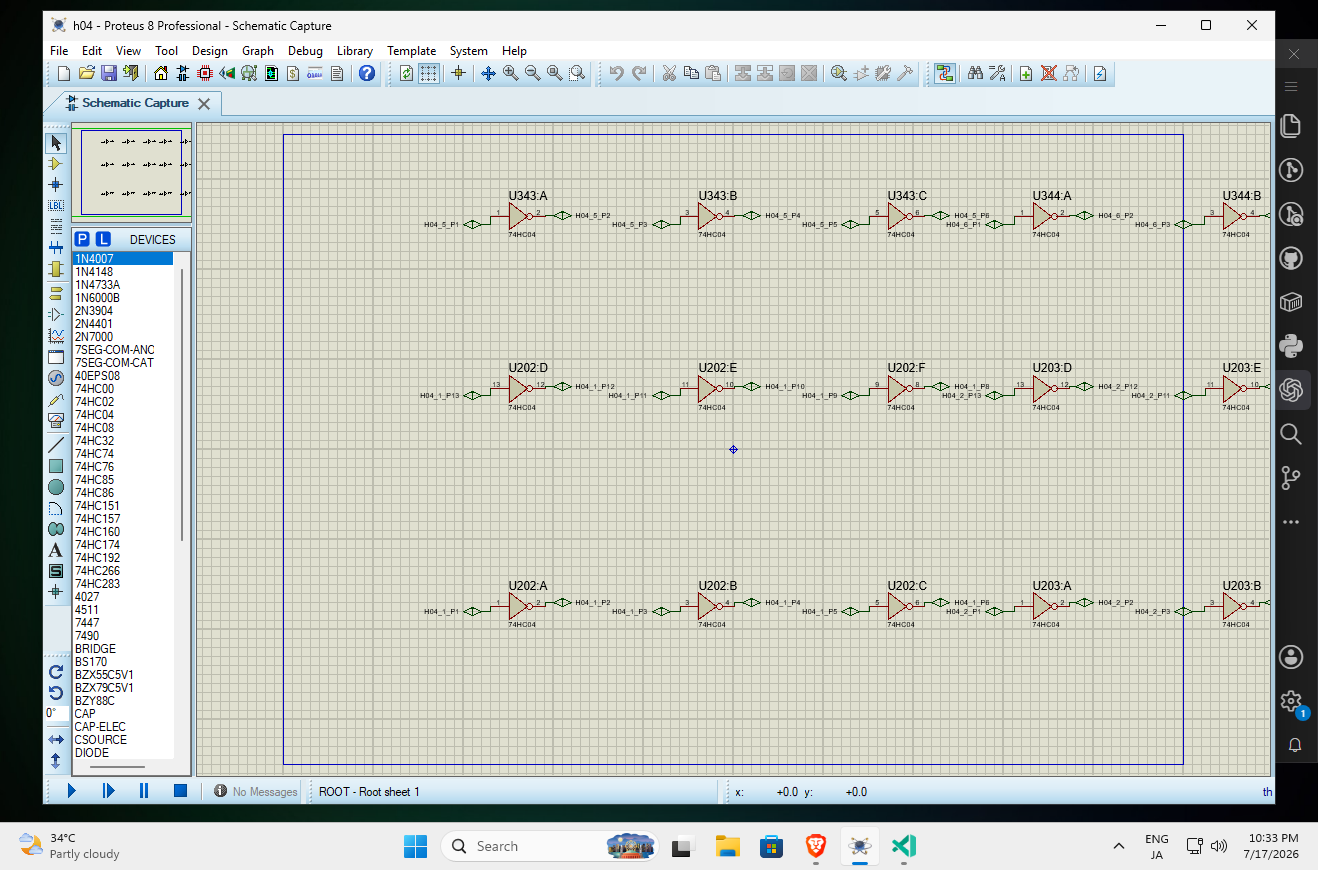
proteus/experiments/runs/2026-07-17_executable_gate_overlay_trial/current_app_gate_bridge/exact_executable_matrix/screenshots/h04/h04_cold_open_1.png
