ProGenEDA/ProGenEDA-DEV/proteus/experiments/runs/2026-07-17_executable_gate_overlay_trial/screenshots/mix_1x_each_compact/GATE_MIX_1X_EACH_COMPACT_GATE_cold_open_2.png

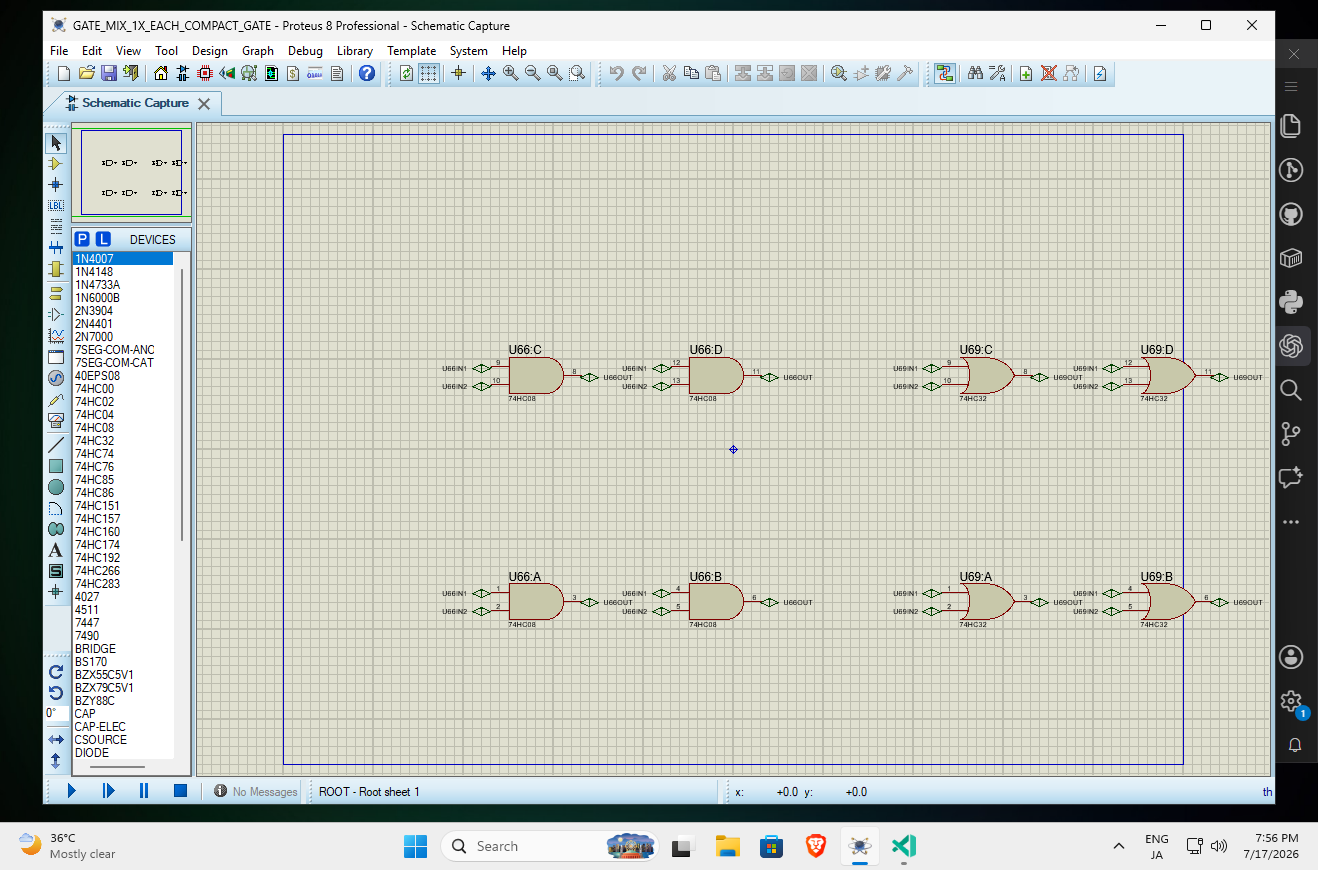
proteus/experiments/runs/2026-07-17_executable_gate_overlay_trial/screenshots/mix_1x_each_compact/GATE_MIX_1X_EACH_COMPACT_GATE_cold_open_2.png
