ProGenEDA/ProGenEDA-DEV/proteus/experiments/runs/2026-07-17_pdf_200_circuit_placement_controls/10_most_impressive_terminalized_current_executable/screenshots/c139/c139_cold_open_1.png

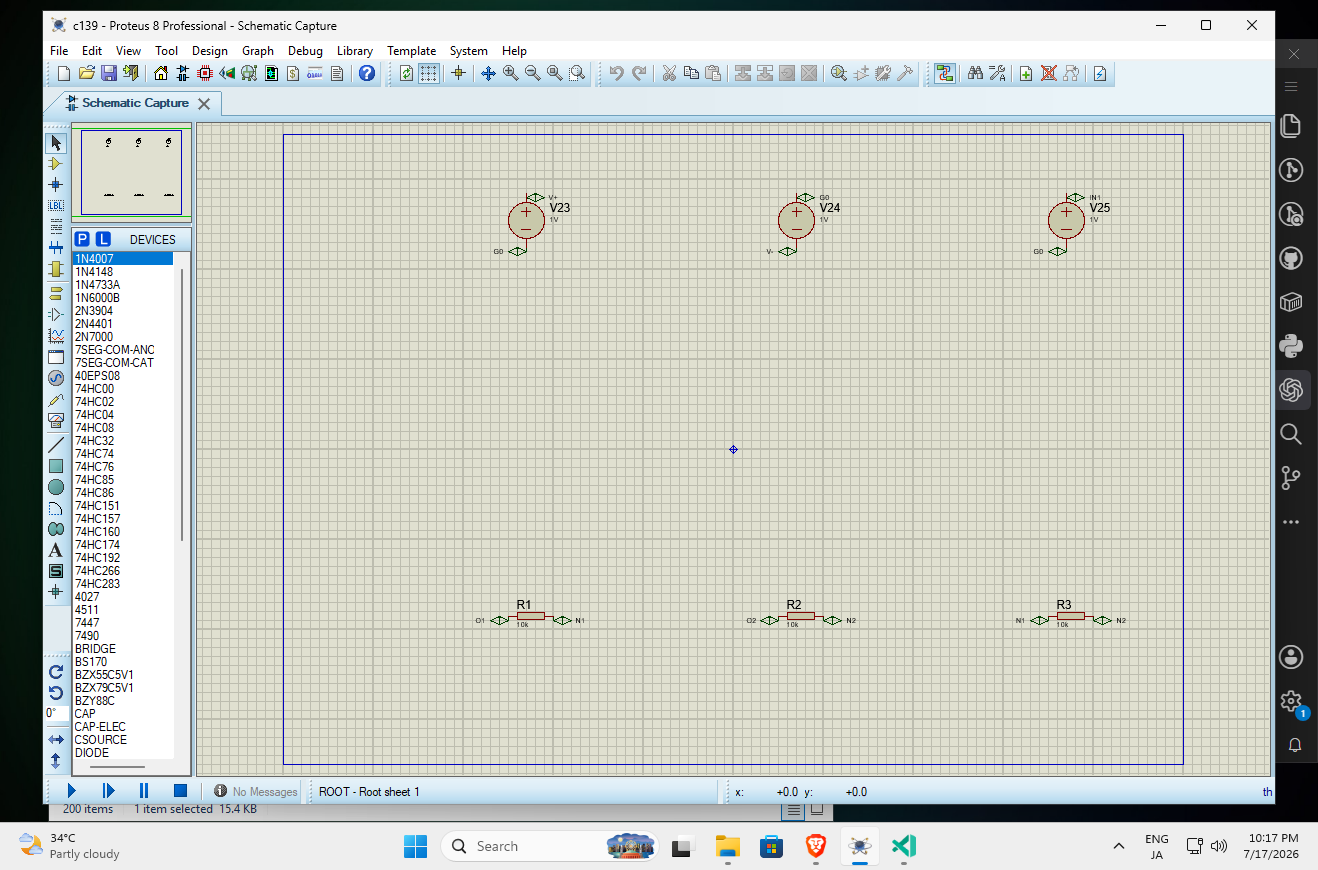
proteus/experiments/runs/2026-07-17_pdf_200_circuit_placement_controls/10_most_impressive_terminalized_current_executable/screenshots/c139/c139_cold_open_1.png
