ProGenEDA/ProGenEDA-DEV/proteus/experiments/runs/2026-07-18_2n3904_terminal_promotion_matrix/D03_beautified_control/screenshots/D03A/D03A_GATE_cold_open_2.png

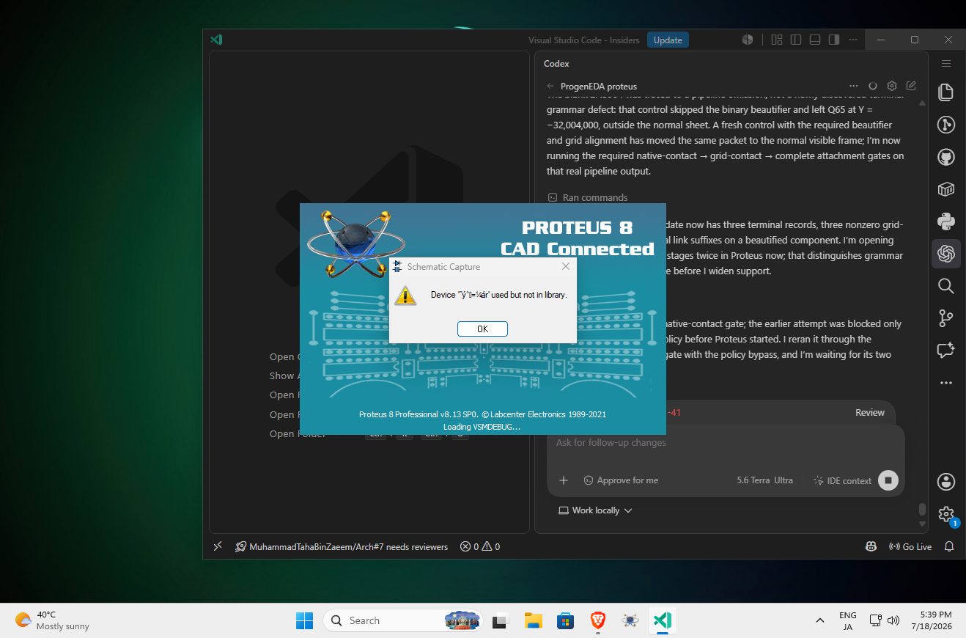
proteus/experiments/runs/2026-07-18_2n3904_terminal_promotion_matrix/D03_beautified_control/screenshots/D03A/D03A_GATE_cold_open_2.png
