ProGenEDA/ProGenEDA-DEV/proteus/experiments/runs/2026-07-18_npn_terminal_promotion_matrix/C01_NATIVE_ASYMMETRIC_NO_NPN/screenshots/C01_NATIVE_ASYMMETRIC_NO_NPN_GATE_cold_open_2.png

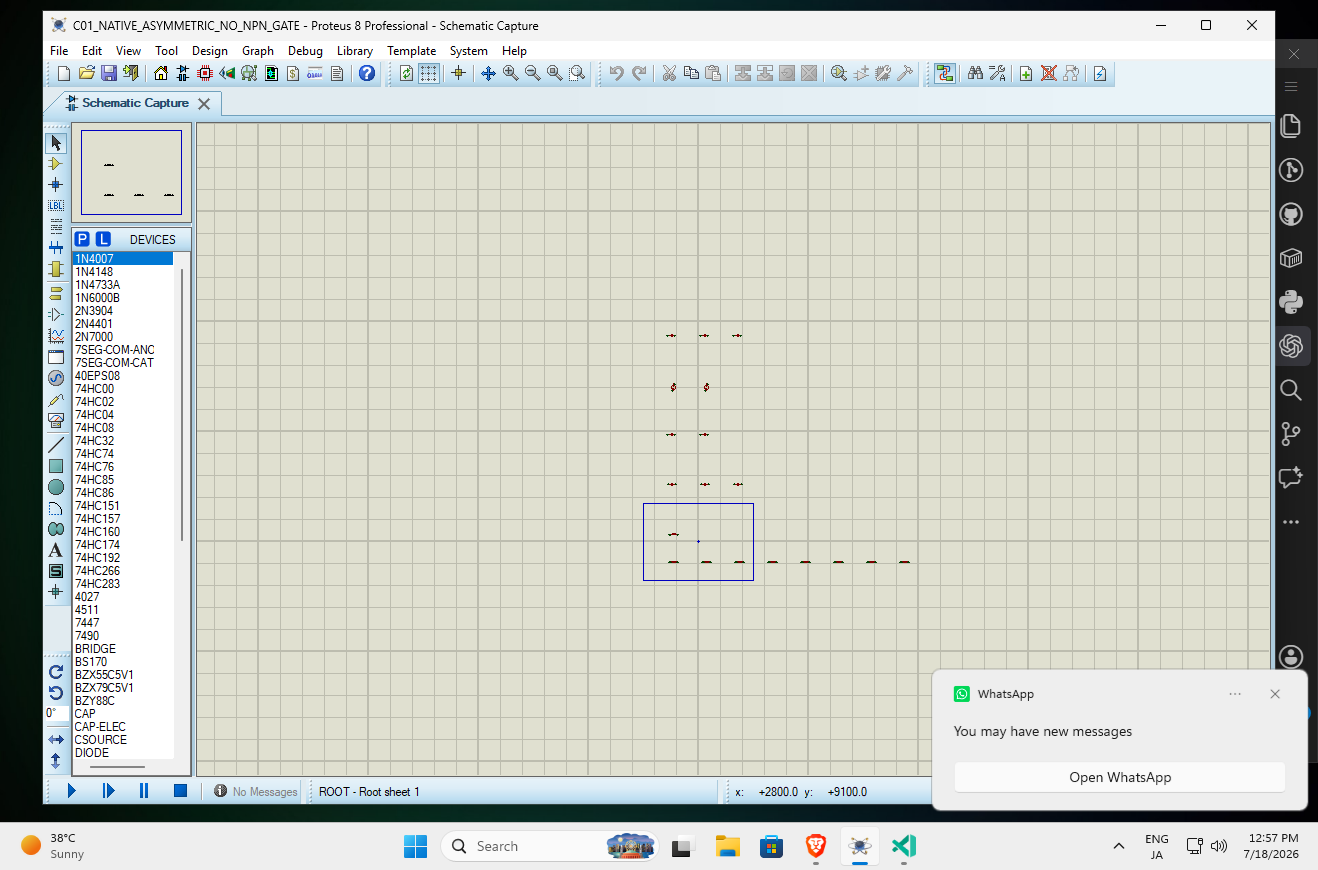
proteus/experiments/runs/2026-07-18_npn_terminal_promotion_matrix/C01_NATIVE_ASYMMETRIC_NO_NPN/screenshots/C01_NATIVE_ASYMMETRIC_NO_NPN_GATE_cold_open_2.png
