ProGenEDA/ProGenEDA-DEV/proteus/experiments/runs/2026-07-18_npn_terminal_promotion_matrix/M03_NPN_CURRENT_CATALOGUE_NATIVE_1X/screenshots/M03_NPN_CURRENT_CATALOGUE_NATIVE_1X_GATE_cold_open_2.png

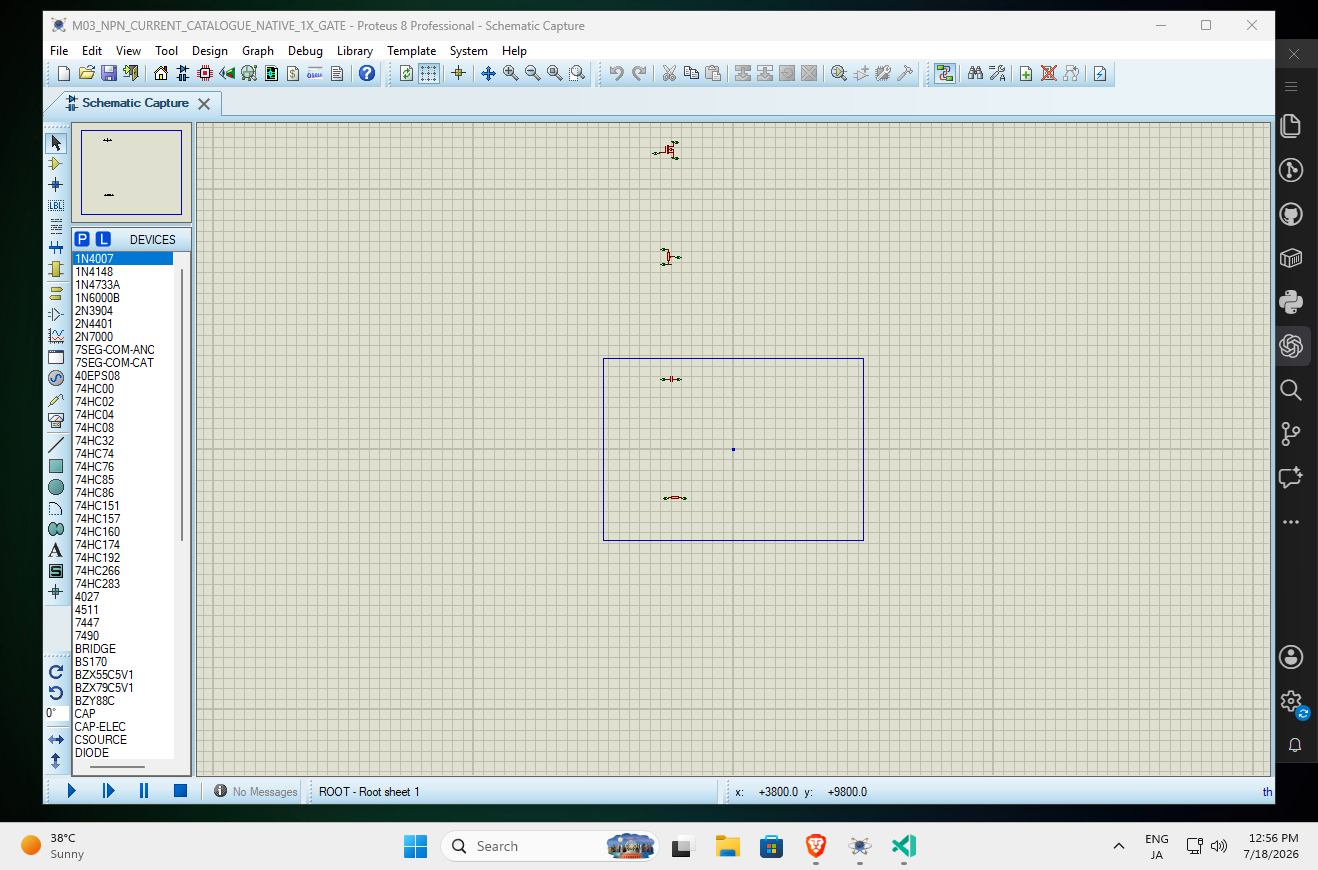
proteus/experiments/runs/2026-07-18_npn_terminal_promotion_matrix/M03_NPN_CURRENT_CATALOGUE_NATIVE_1X/screenshots/M03_NPN_CURRENT_CATALOGUE_NATIVE_1X_GATE_cold_open_2.png
