ProGenEDA/ProGenEDA-DEV/proteus/experiments/runs/2026-07-18_npn_terminal_promotion_matrix_v2/EXE_M05_NPN_DIODE_15X/screenshots/EXE_M05_NPN_DIODE_15X_GATE_cold_open_2.png

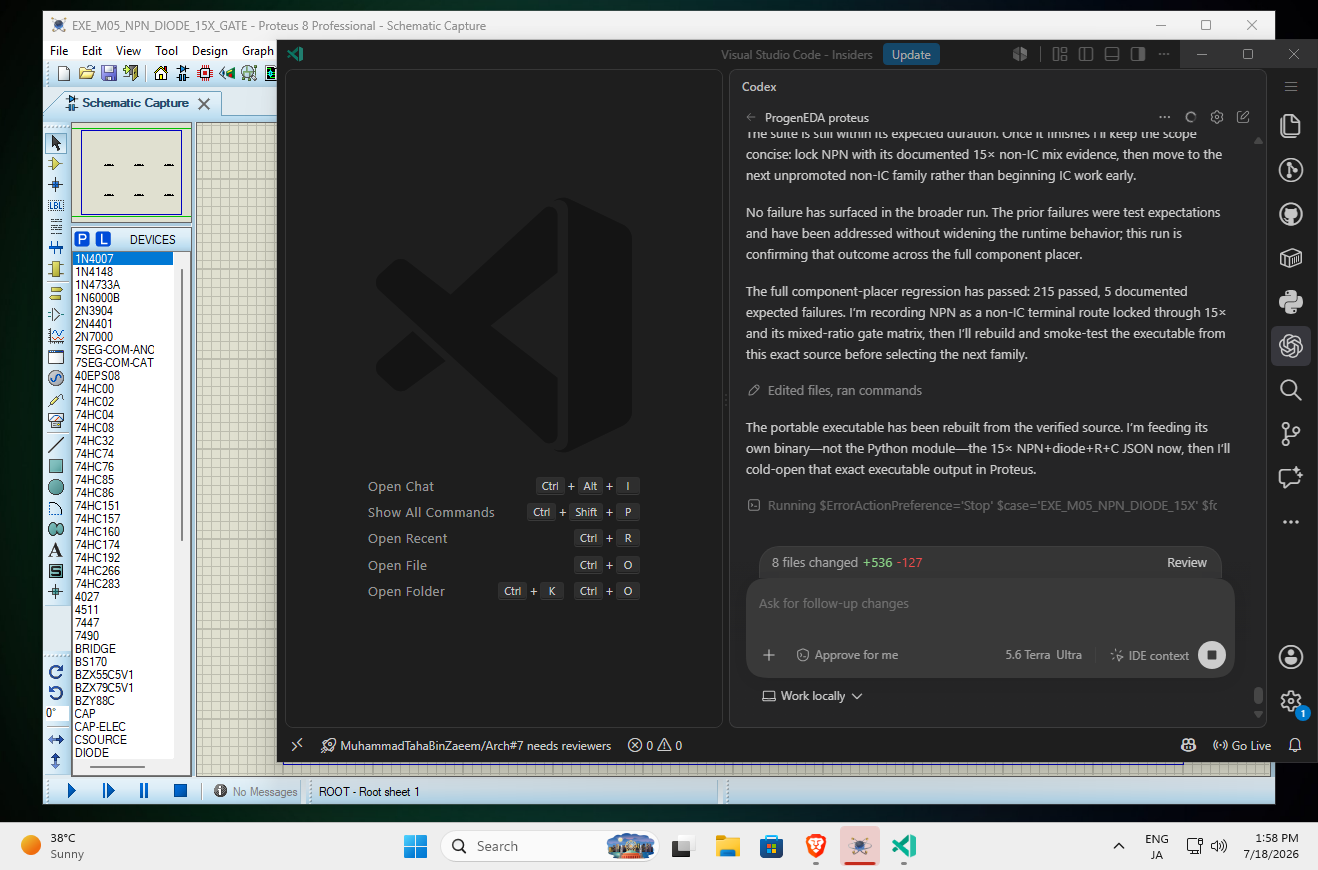
proteus/experiments/runs/2026-07-18_npn_terminal_promotion_matrix_v2/EXE_M05_NPN_DIODE_15X/screenshots/EXE_M05_NPN_DIODE_15X_GATE_cold_open_2.png
