ProGenEDA/ProGenEDA-DEV/proteus/experiments/runs/2026-07-18_pnp_terminal_promotion_matrix/M04_PNP_DIODE_RESISTOR_CAP_15X/screenshots/M04_PNP_DIODE_RESISTOR_CAP_15X_GATE_COPY_cold_open_1.png

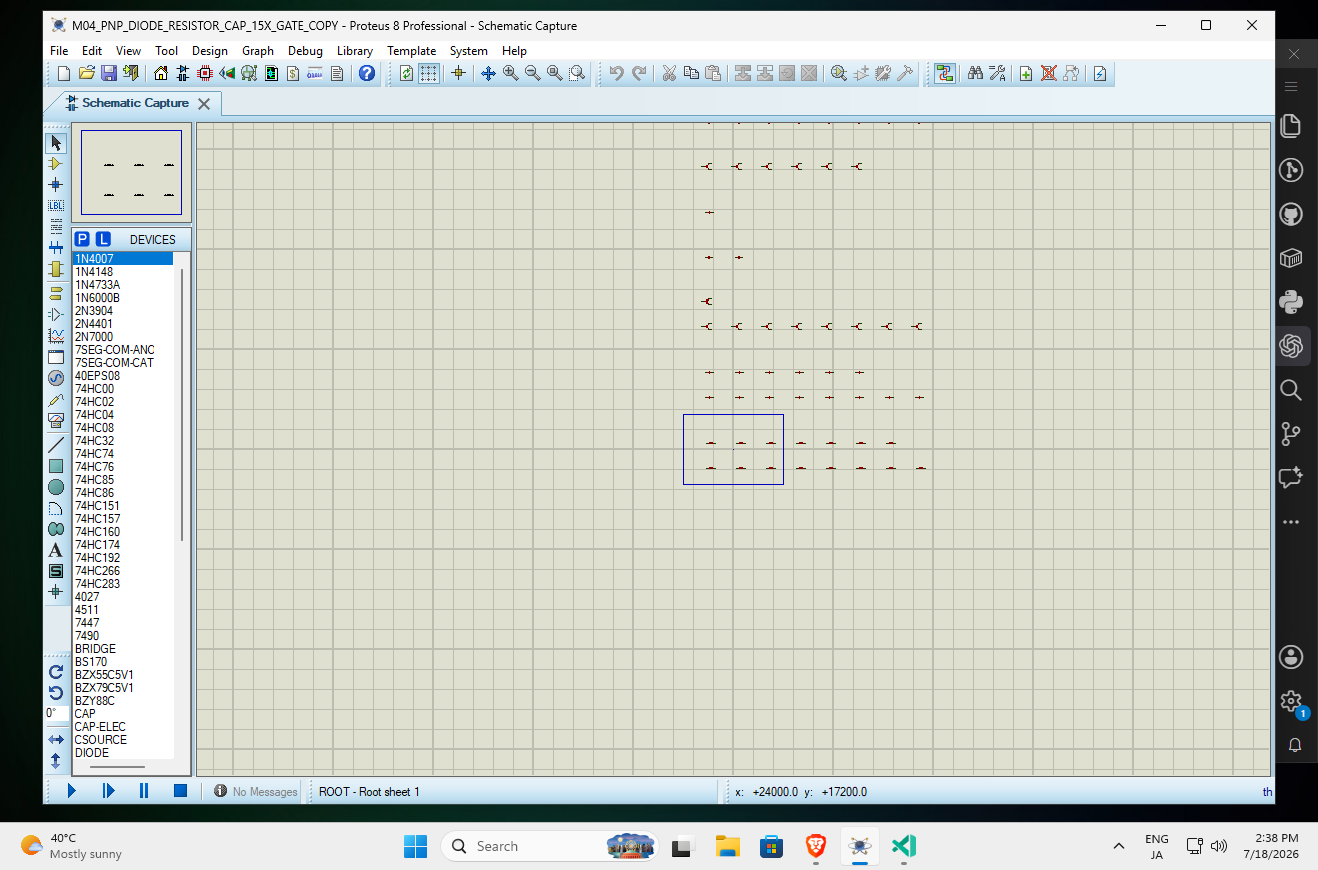
proteus/experiments/runs/2026-07-18_pnp_terminal_promotion_matrix/M04_PNP_DIODE_RESISTOR_CAP_15X/screenshots/M04_PNP_DIODE_RESISTOR_CAP_15X_GATE_COPY_cold_open_1.png
