ProGenEDA/ProGenEDA-DEV/proteus/experiments/runs/dil8_analog_ne555_terminal_v3_temp_2026_07_15/03_scale_9x_15x/S15_NE555_15X_COMPLETE_GATE_INITIAL_before_close.png

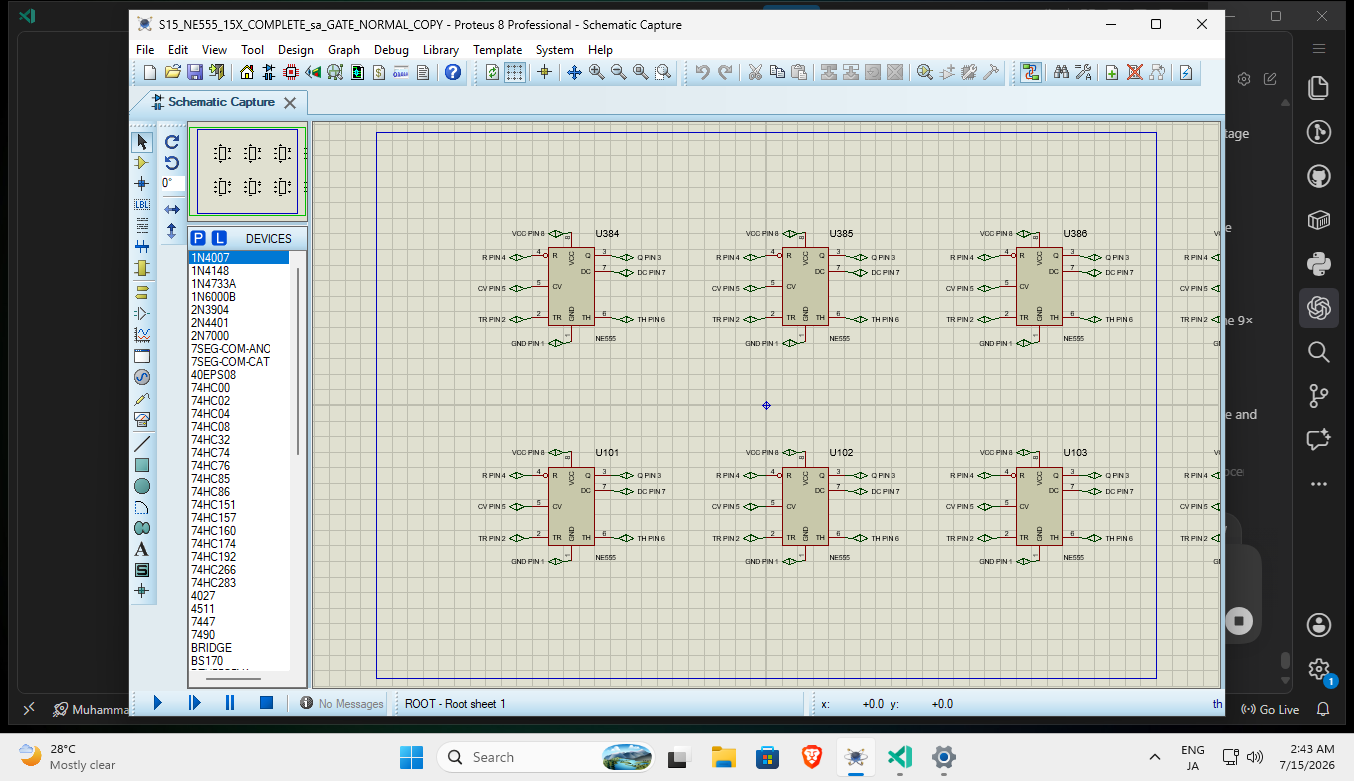
proteus/experiments/runs/dil8_analog_ne555_terminal_v3_temp_2026_07_15/03_scale_9x_15x/S15_NE555_15X_COMPLETE_GATE_INITIAL_before_close.png
