ProGenEDA/ProGenEDA-DEV/proteus/experiments/runs/dil8_analog_terminal_v1_temp_2026_07_14/02_local_proteus_gate/F01_LM741_NATIVE_FATAL_before_close.png

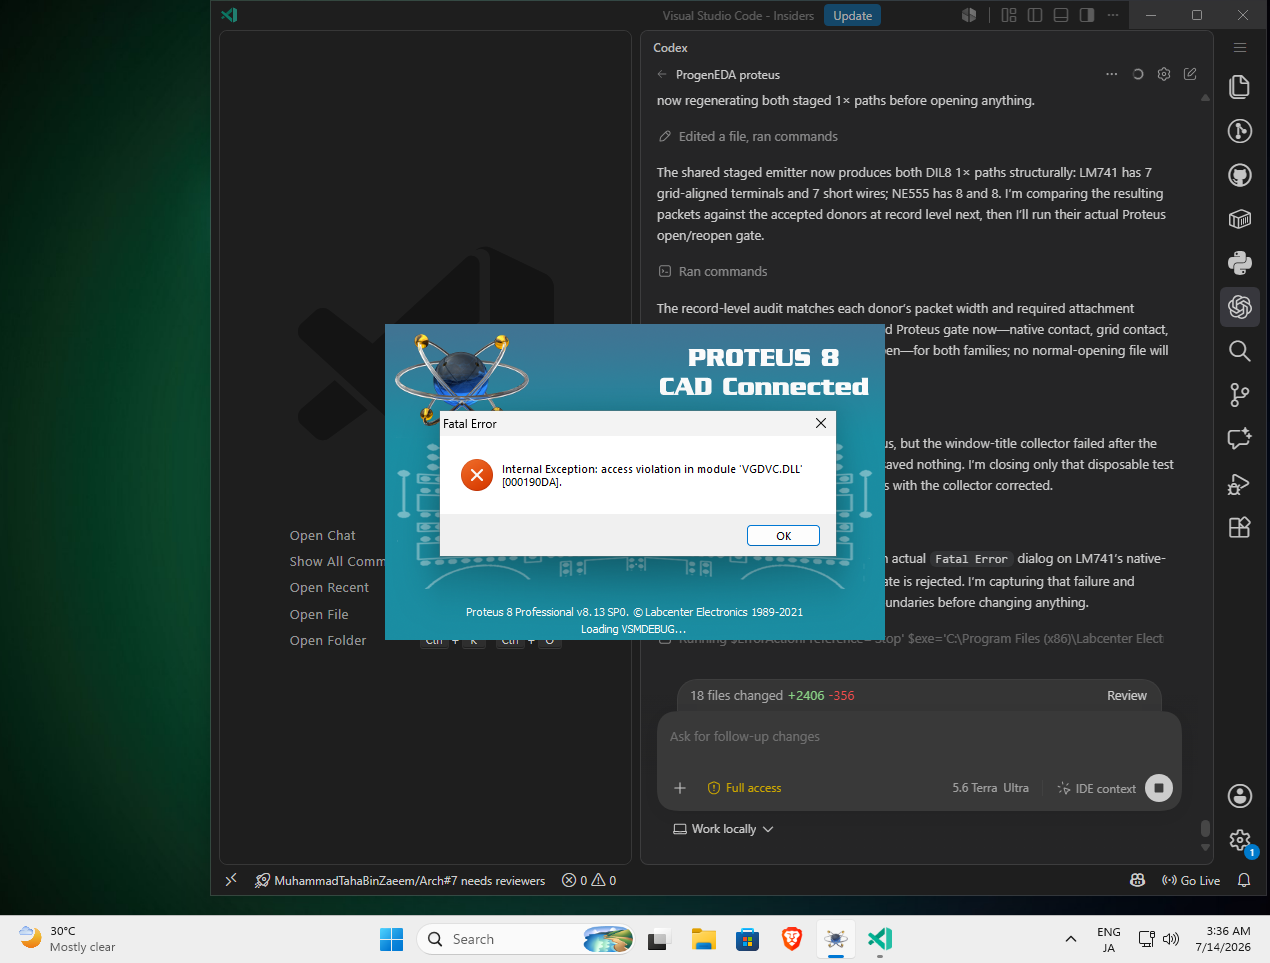
proteus/experiments/runs/dil8_analog_terminal_v1_temp_2026_07_14/02_local_proteus_gate/F01_LM741_NATIVE_FATAL_before_close.png
