ProGenEDA/ProGenEDA-DEV/proteus/experiments/runs/dil8_analog_terminal_v1_temp_2026_07_14/02_local_proteus_gate/G16_NE555_15X_before_close.png

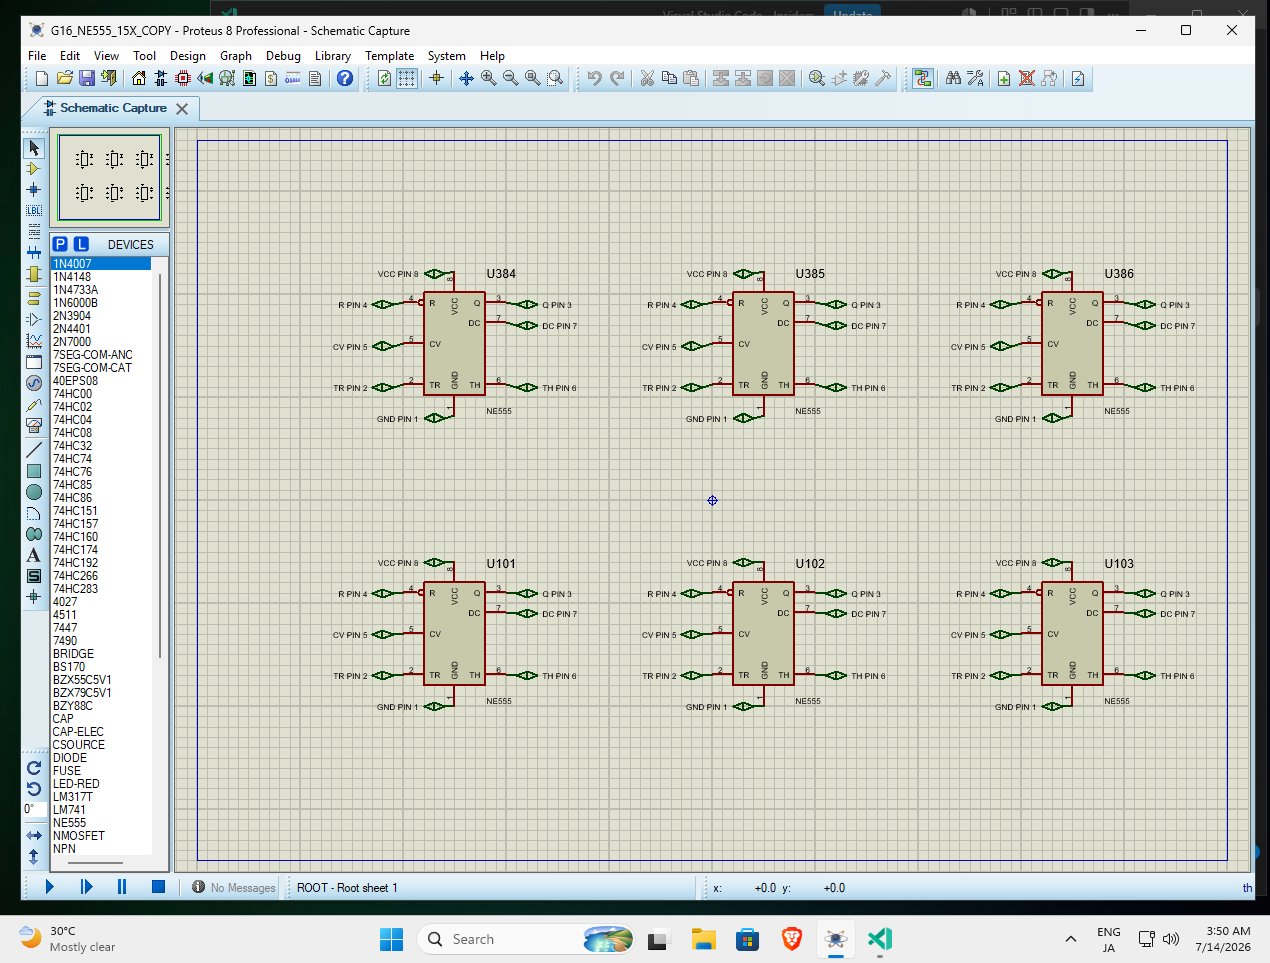
proteus/experiments/runs/dil8_analog_terminal_v1_temp_2026_07_14/02_local_proteus_gate/G16_NE555_15X_before_close.png
