ProGenEDA/ProGenEDA-DEV/proteus/experiments/runs/dil14_hex_inverter_terminal_v1_temp_2026_07_13/05_local_proteus_gate/screenshots/S01_74HC04_15X_12s_loader_check.png

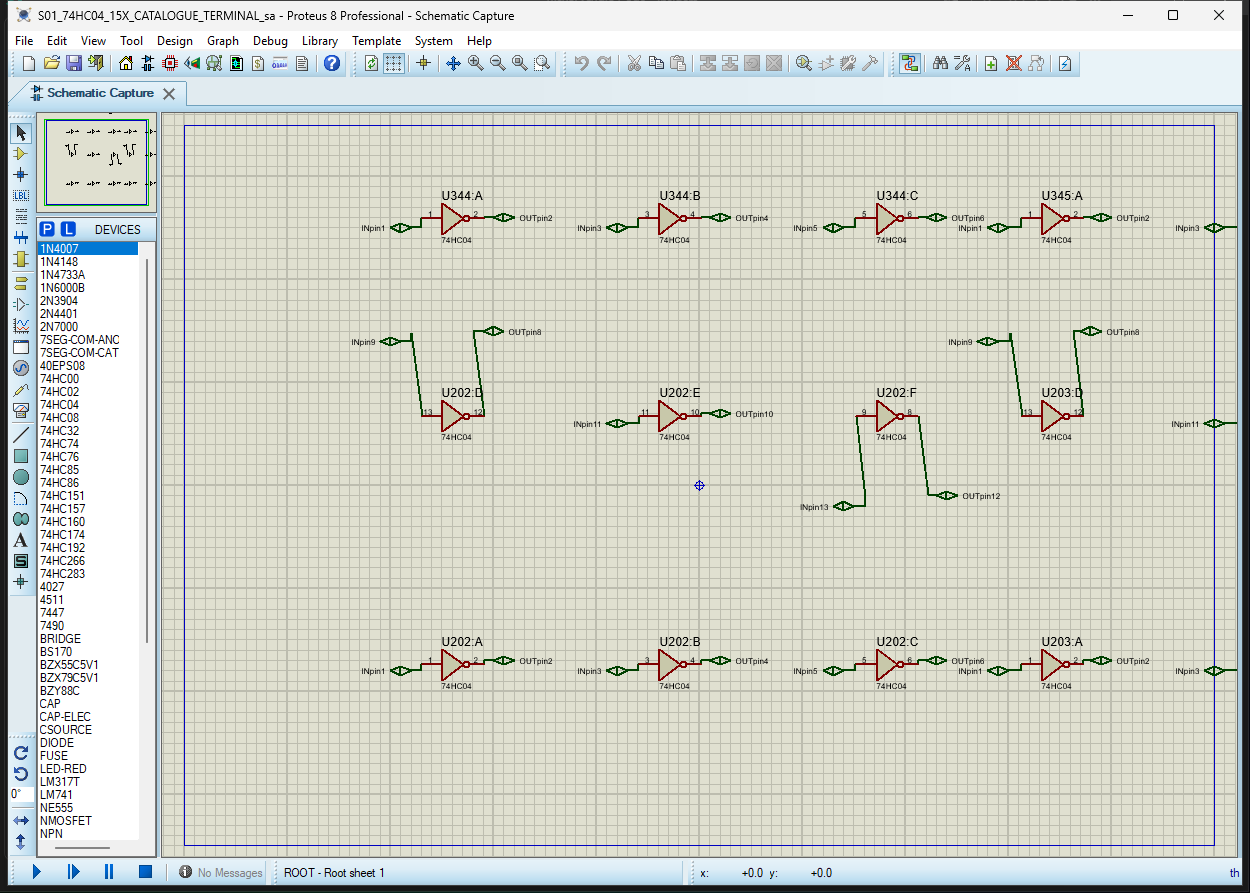
proteus/experiments/runs/dil14_hex_inverter_terminal_v1_temp_2026_07_13/05_local_proteus_gate/screenshots/S01_74HC04_15X_12s_loader_check.png
