ProGenEDA/ProGenEDA-DEV/proteus/experiments/runs/dil14_quad_2input_logic_74hc00_terminal_v2_temp_2026_07_14/02_local_proteus_gate/G03_C03_74HC00_GRID_CONTACT.png

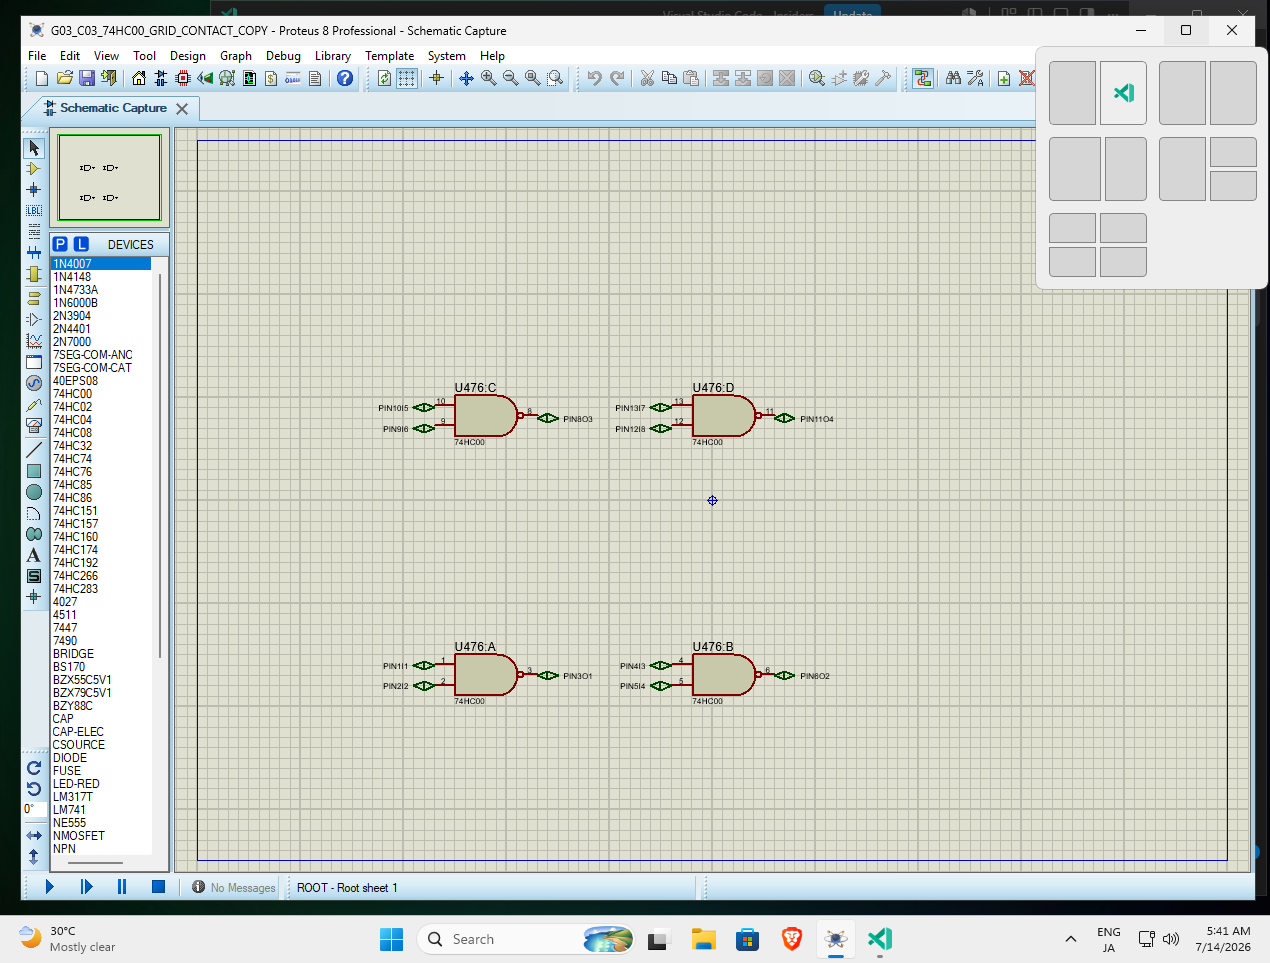
proteus/experiments/runs/dil14_quad_2input_logic_74hc00_terminal_v2_temp_2026_07_14/02_local_proteus_gate/G03_C03_74HC00_GRID_CONTACT.png
