ProGenEDA/ProGenEDA-DEV/proteus/experiments/runs/dil14_quad_2input_logic_74hc02_terminal_v2_temp_2026_07_14/04_local_proteus_scale_gate/G07_S01_74HC02_9X_COMPLETE.png

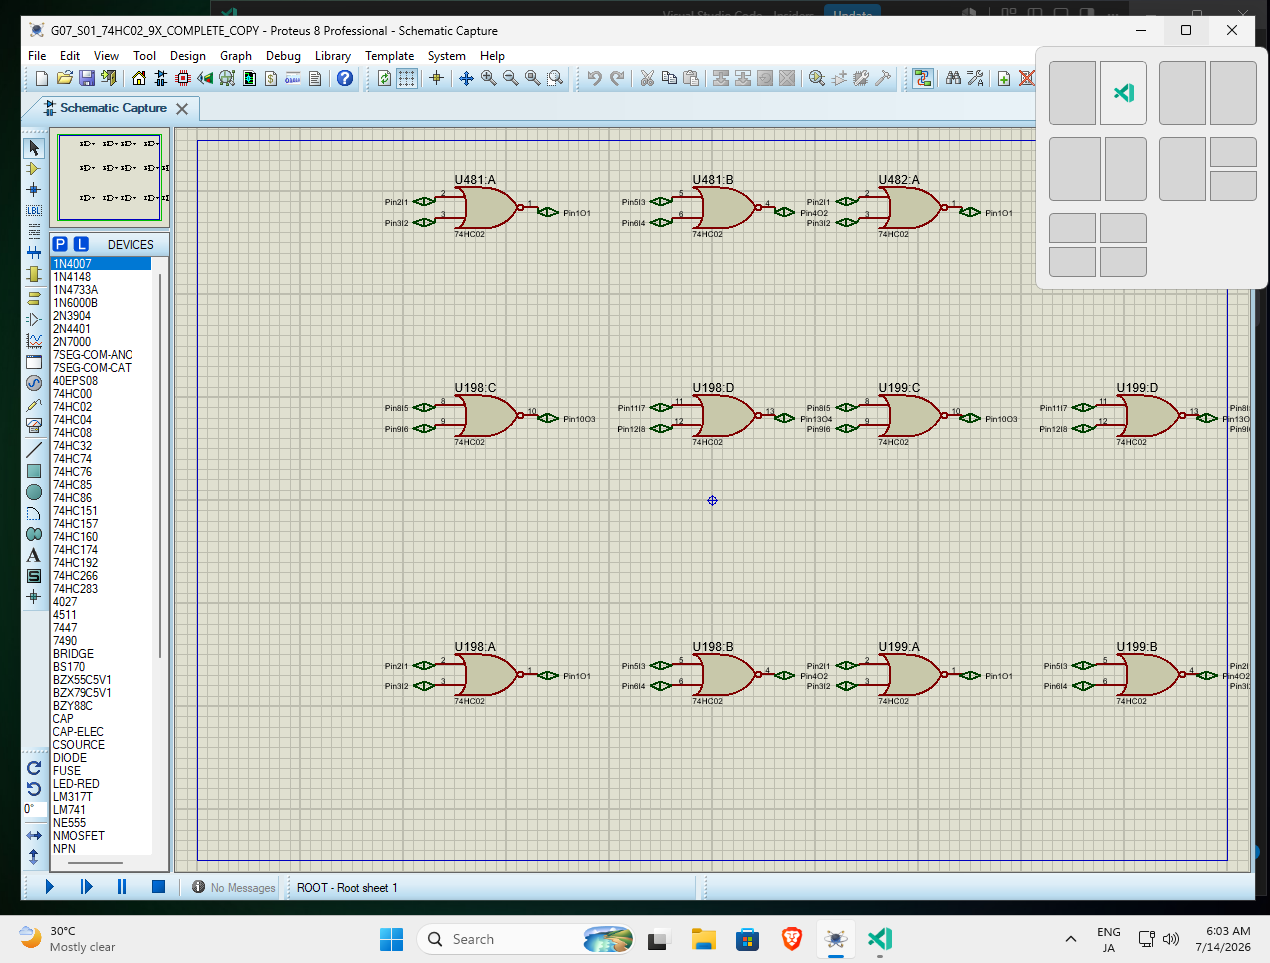
proteus/experiments/runs/dil14_quad_2input_logic_74hc02_terminal_v2_temp_2026_07_14/04_local_proteus_scale_gate/G07_S01_74HC02_9X_COMPLETE.png
