ProGenEDA/ProGenEDA-DEV/proteus/experiments/runs/dil14_quad_2input_logic_74hc08_terminal_v2_temp_2026_07_14/02_local_proteus_gate/G04_C04_74HC08_COMPLETE.png

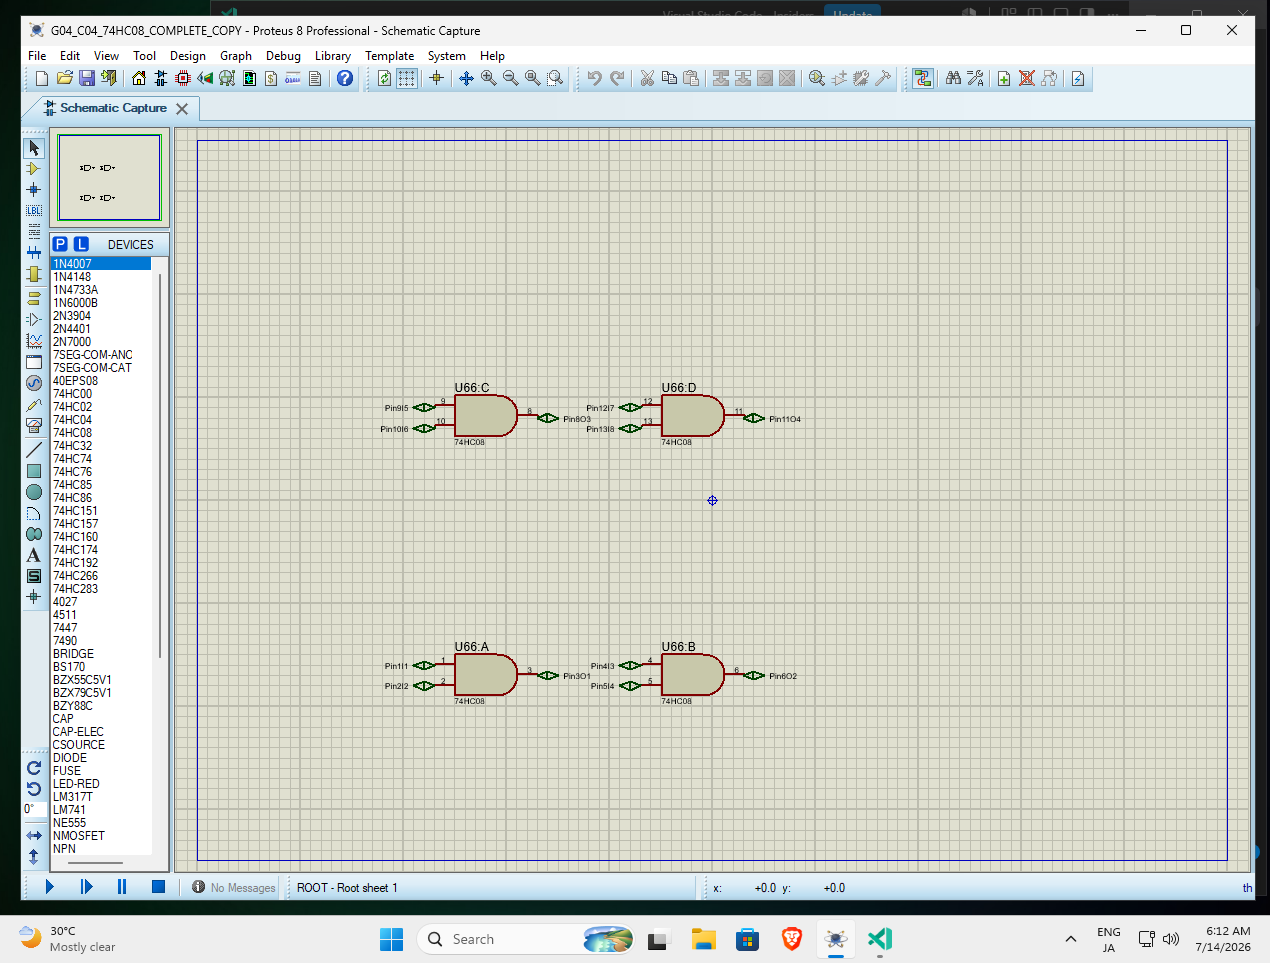
proteus/experiments/runs/dil14_quad_2input_logic_74hc08_terminal_v2_temp_2026_07_14/02_local_proteus_gate/G04_C04_74HC08_COMPLETE.png
