ProGenEDA/ProGenEDA-DEV/proteus/experiments/runs/dil14_quad_2input_logic_74hc266_terminal_v2_temp_2026_07_14/04_local_proteus_scale_gate/G03_S15_74HC266_15X_COMPLETE_before_close.png

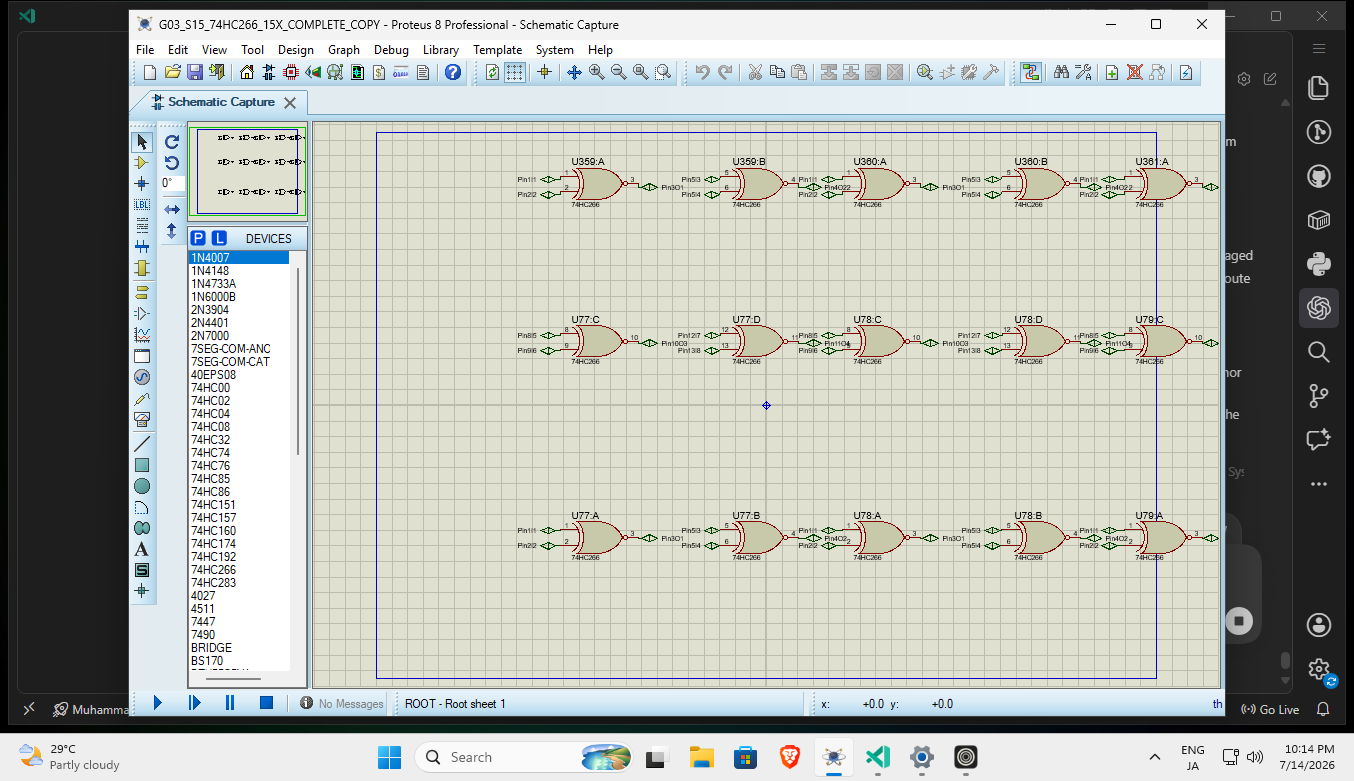
proteus/experiments/runs/dil14_quad_2input_logic_74hc266_terminal_v2_temp_2026_07_14/04_local_proteus_scale_gate/G03_S15_74HC266_15X_COMPLETE_before_close.png
