ProGenEDA/ProGenEDA-DEV/proteus/experiments/runs/dil14_quad_2input_logic_terminal_v1_temp_2026_07_13/05_local_proteus_gate/screenshots/HC266_15X_FULL_before_save.png

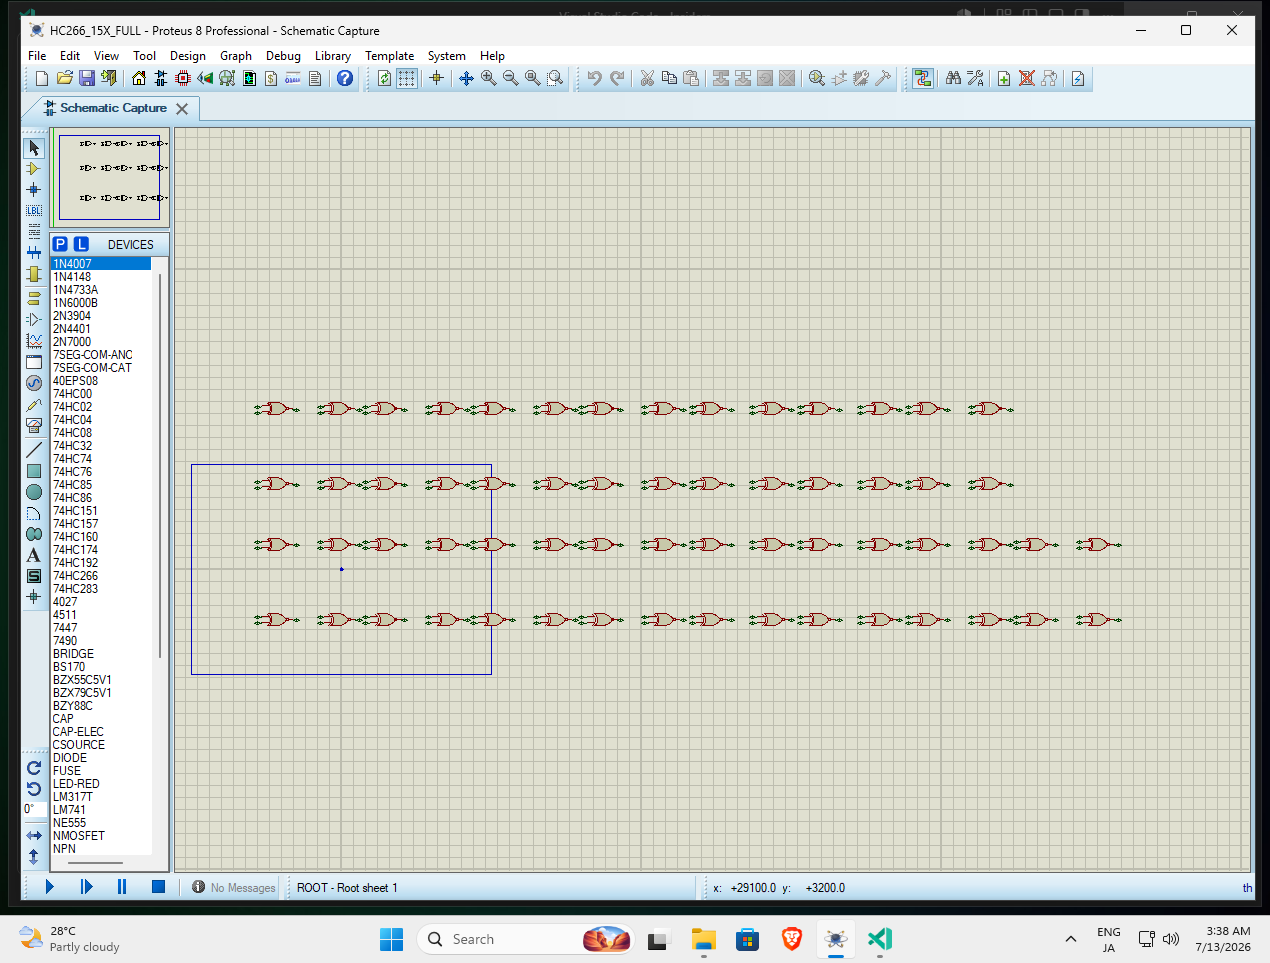
proteus/experiments/runs/dil14_quad_2input_logic_terminal_v1_temp_2026_07_13/05_local_proteus_gate/screenshots/HC266_15X_FULL_before_save.png
