ProGenEDA/ProGenEDA-DEV/proteus/experiments/runs/dil14_quad_2input_logic_terminal_v1_temp_2026_07_13/local_proteus_gate/G09_HC266_PIN6_CORRECTION.png

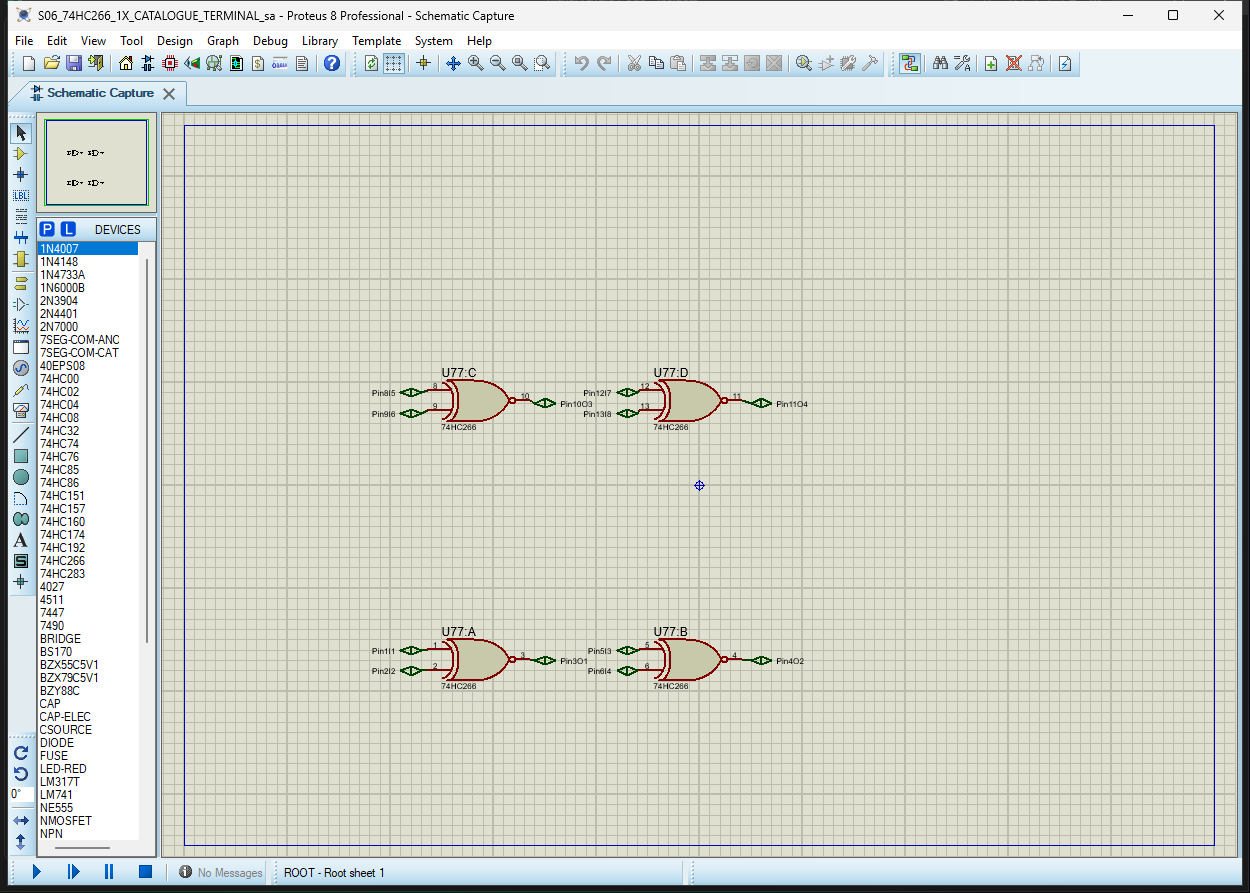
proteus/experiments/runs/dil14_quad_2input_logic_terminal_v1_temp_2026_07_13/local_proteus_gate/G09_HC266_PIN6_CORRECTION.png
