ProGenEDA/ProGenEDA-DEV/proteus/experiments/runs/dil16_counter_74hc192_terminal_v3_temp_2026_07_15/01_solo_1x/C04_74HC192_1X_COMPLETE_GATE_INITIAL_before_close.png

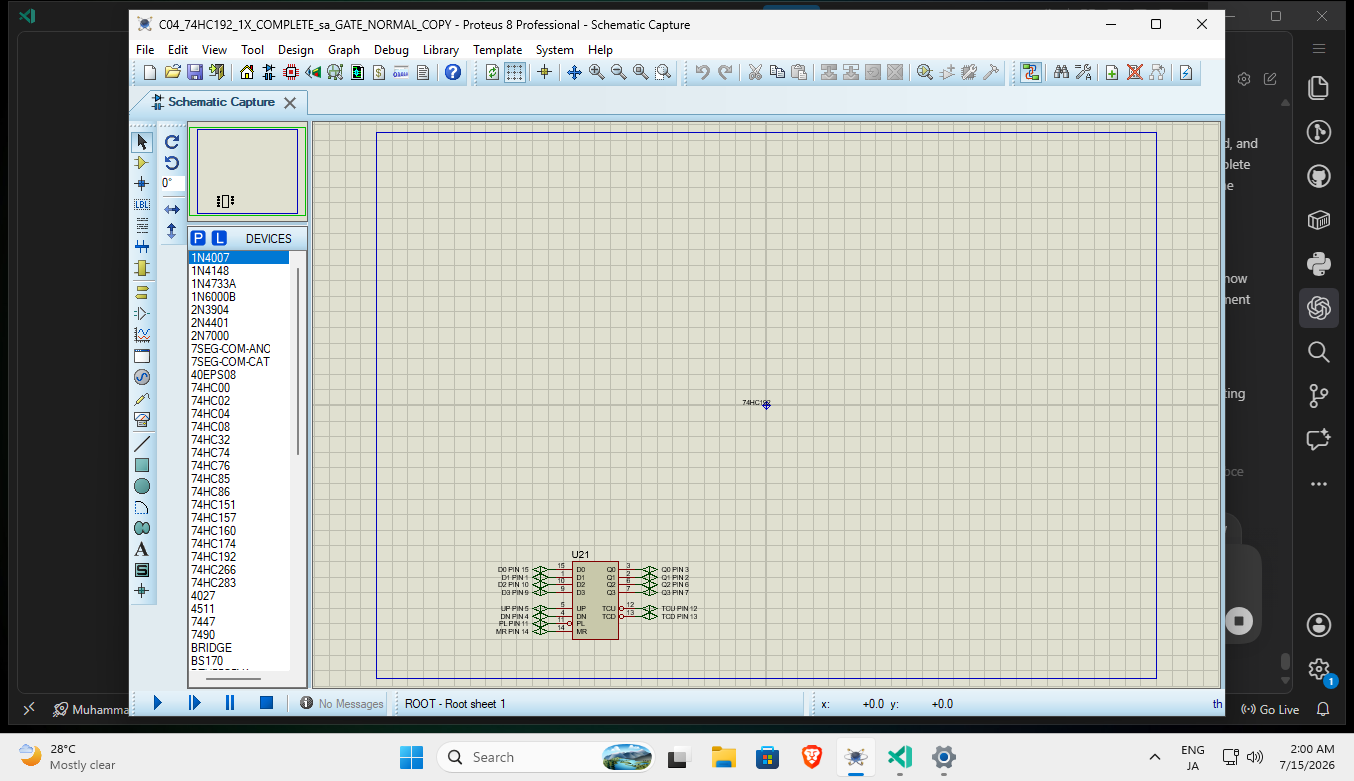
proteus/experiments/runs/dil16_counter_74hc192_terminal_v3_temp_2026_07_15/01_solo_1x/C04_74HC192_1X_COMPLETE_GATE_INITIAL_before_close.png
