ProGenEDA/ProGenEDA-DEV/proteus/experiments/runs/dil16_counter_74hc192_terminal_v3_temp_2026_07_15/03_scale_9x_15x/S15_74HC192_15X_COMPLETE_GATE_INITIAL_before_close.png

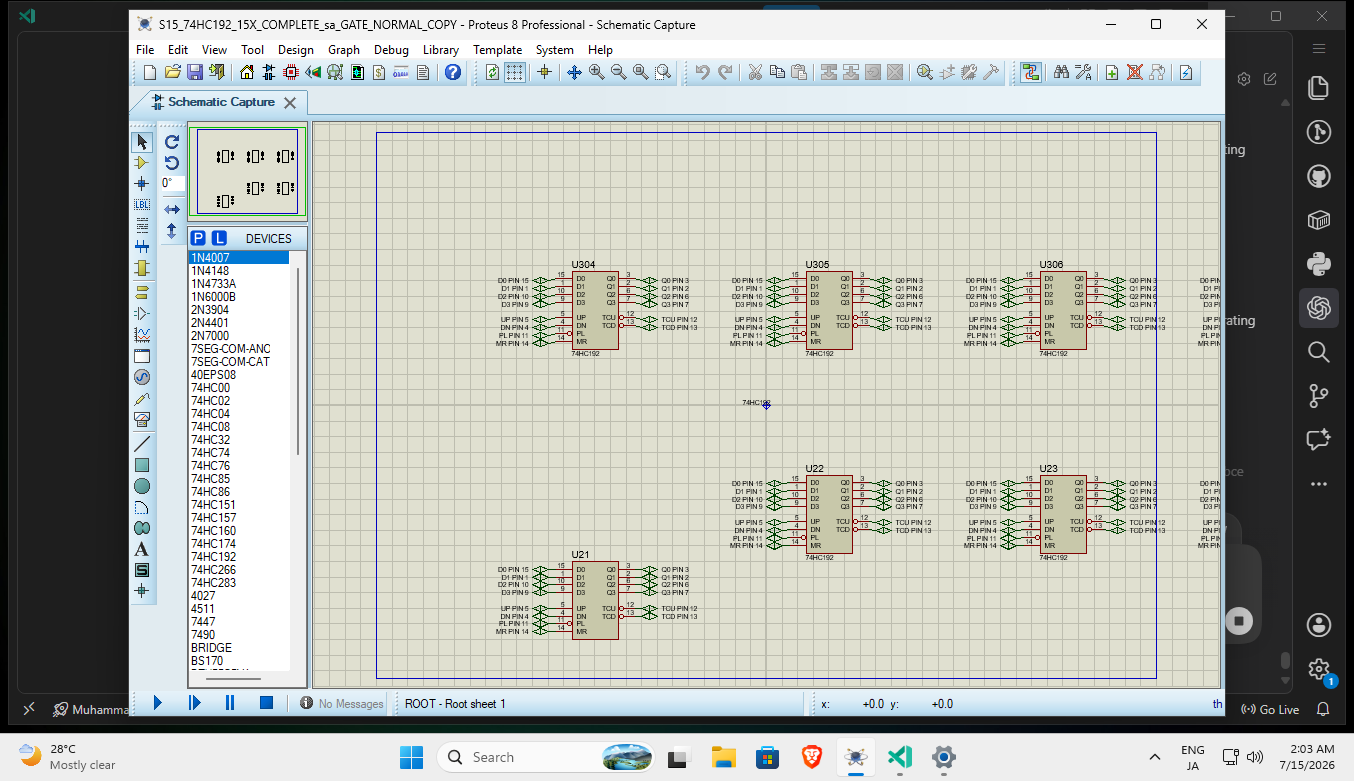
proteus/experiments/runs/dil16_counter_74hc192_terminal_v3_temp_2026_07_15/03_scale_9x_15x/S15_74HC192_15X_COMPLETE_GATE_INITIAL_before_close.png
