ProGenEDA/ProGenEDA-DEV/proteus/experiments/runs/dil16_counter_terminal_v1_temp_2026_07_14/01_staged_1x/S02_74HC192_1X/local_proteus_gate/G03_74HC192_COMPLETE_ACTIVE_before_close.png

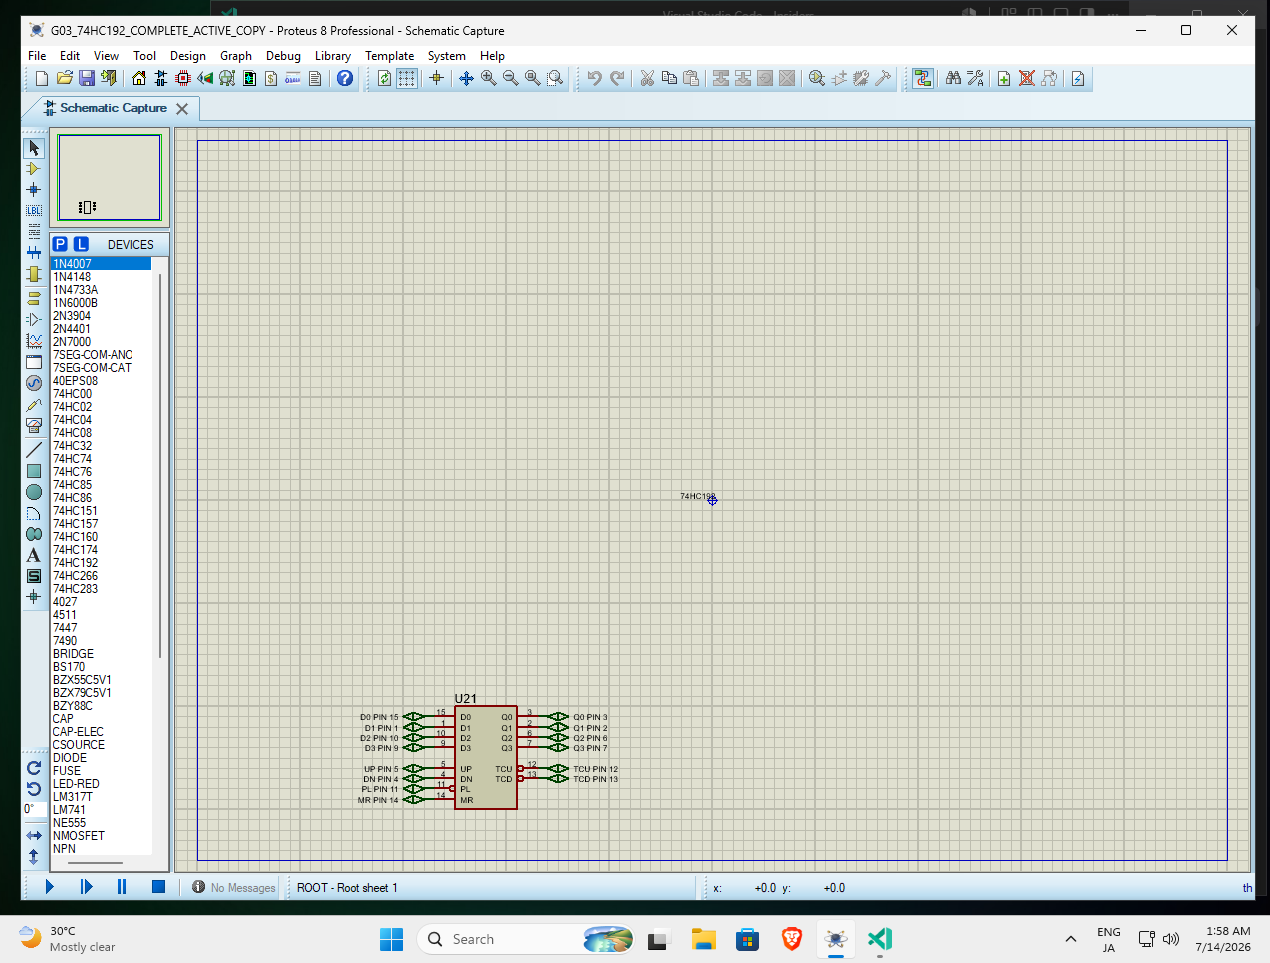
proteus/experiments/runs/dil16_counter_terminal_v1_temp_2026_07_14/01_staged_1x/S02_74HC192_1X/local_proteus_gate/G03_74HC192_COMPLETE_ACTIVE_before_close.png
