ProGenEDA/ProGenEDA-DEV/proteus/experiments/runs/dil16_counter_terminal_v1_temp_2026_07_14/02_scale_9x_15x/local_proteus_gate_74HC192/G07_74HC192_15X_before_close.png

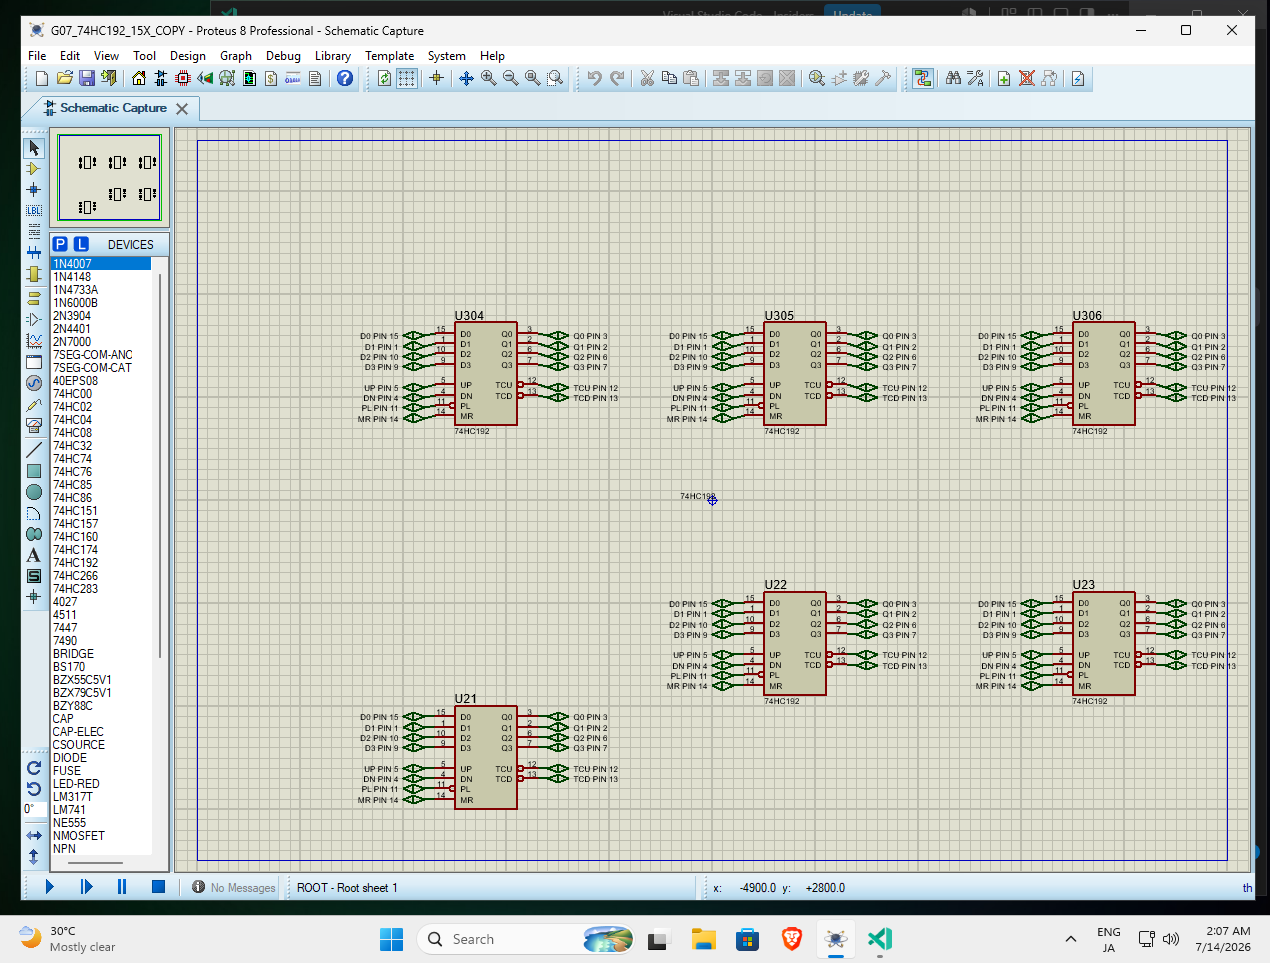
proteus/experiments/runs/dil16_counter_terminal_v1_temp_2026_07_14/02_scale_9x_15x/local_proteus_gate_74HC192/G07_74HC192_15X_before_close.png
