ProGenEDA/ProGenEDA-DEV/proteus/experiments/runs/dil16_decoder_driver_terminal_v1_temp_2026_07_13/03_7447_staged_1x/local_proteus_gate/G01_7447_NATIVE_CONTACT_STAGE_before_close.png

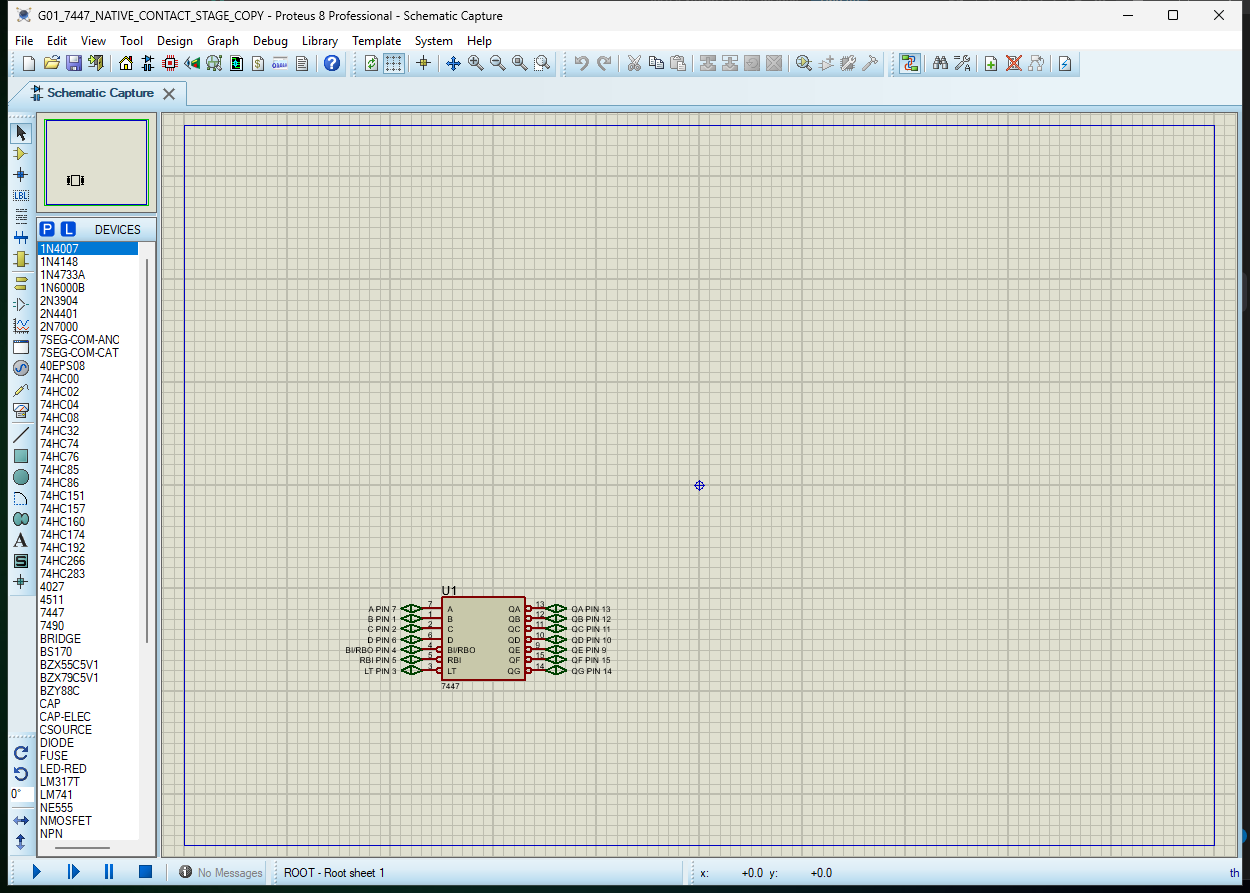
proteus/experiments/runs/dil16_decoder_driver_terminal_v1_temp_2026_07_13/03_7447_staged_1x/local_proteus_gate/G01_7447_NATIVE_CONTACT_STAGE_before_close.png
