ProGenEDA/ProGenEDA-DEV/proteus/experiments/runs/dil16_decoder_driver_terminal_v1_temp_2026_07_13/04_7447_scale_9x_15x/local_proteus_gate/G05_7447_15X_cold_reopen_before_close.png

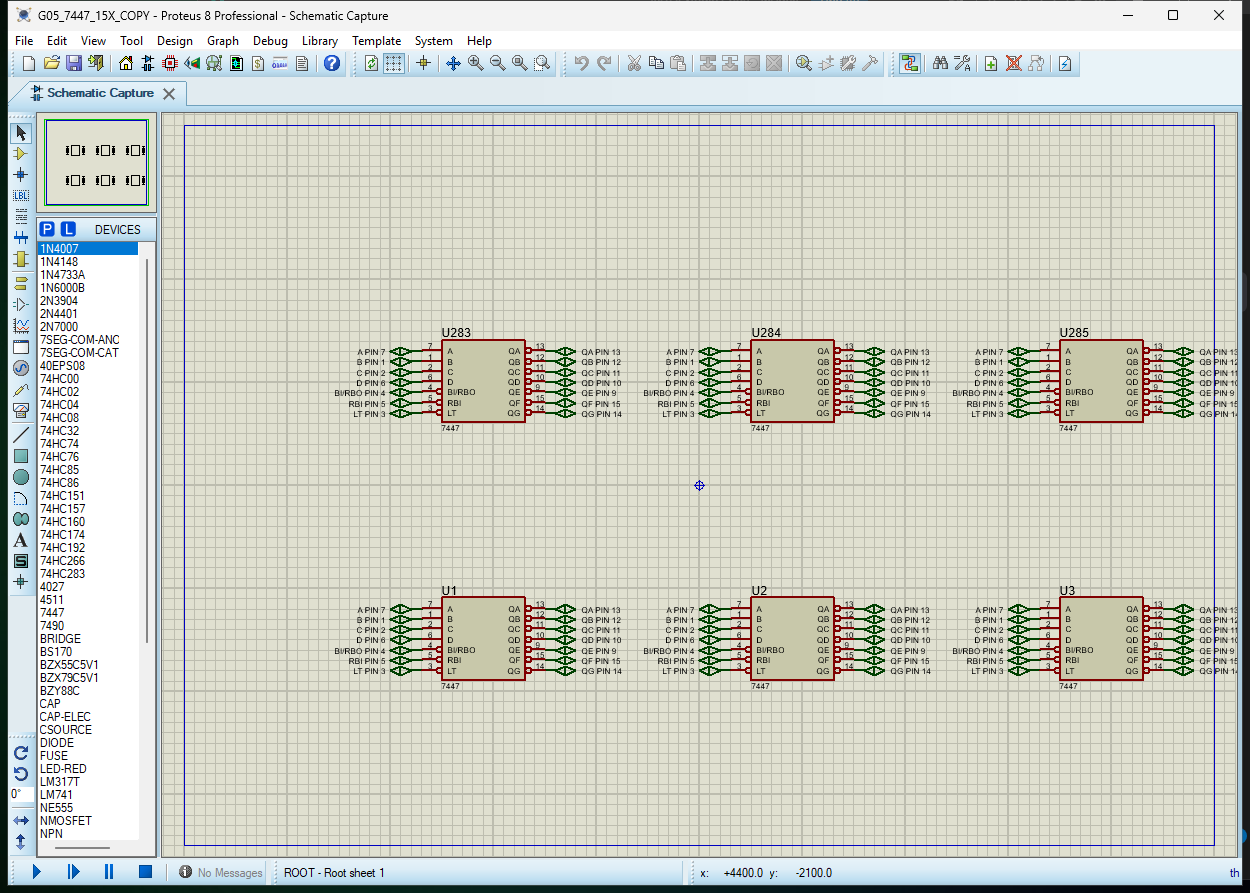
proteus/experiments/runs/dil16_decoder_driver_terminal_v1_temp_2026_07_13/04_7447_scale_9x_15x/local_proteus_gate/G05_7447_15X_cold_reopen_before_close.png
