ProGenEDA/ProGenEDA-DEV/proteus/experiments/runs/dil16_dual_jk_ff_74hc76_terminal_v3_temp_2026_07_14/04_local_proteus_gate/G03_74HC76_15X_before_close.png

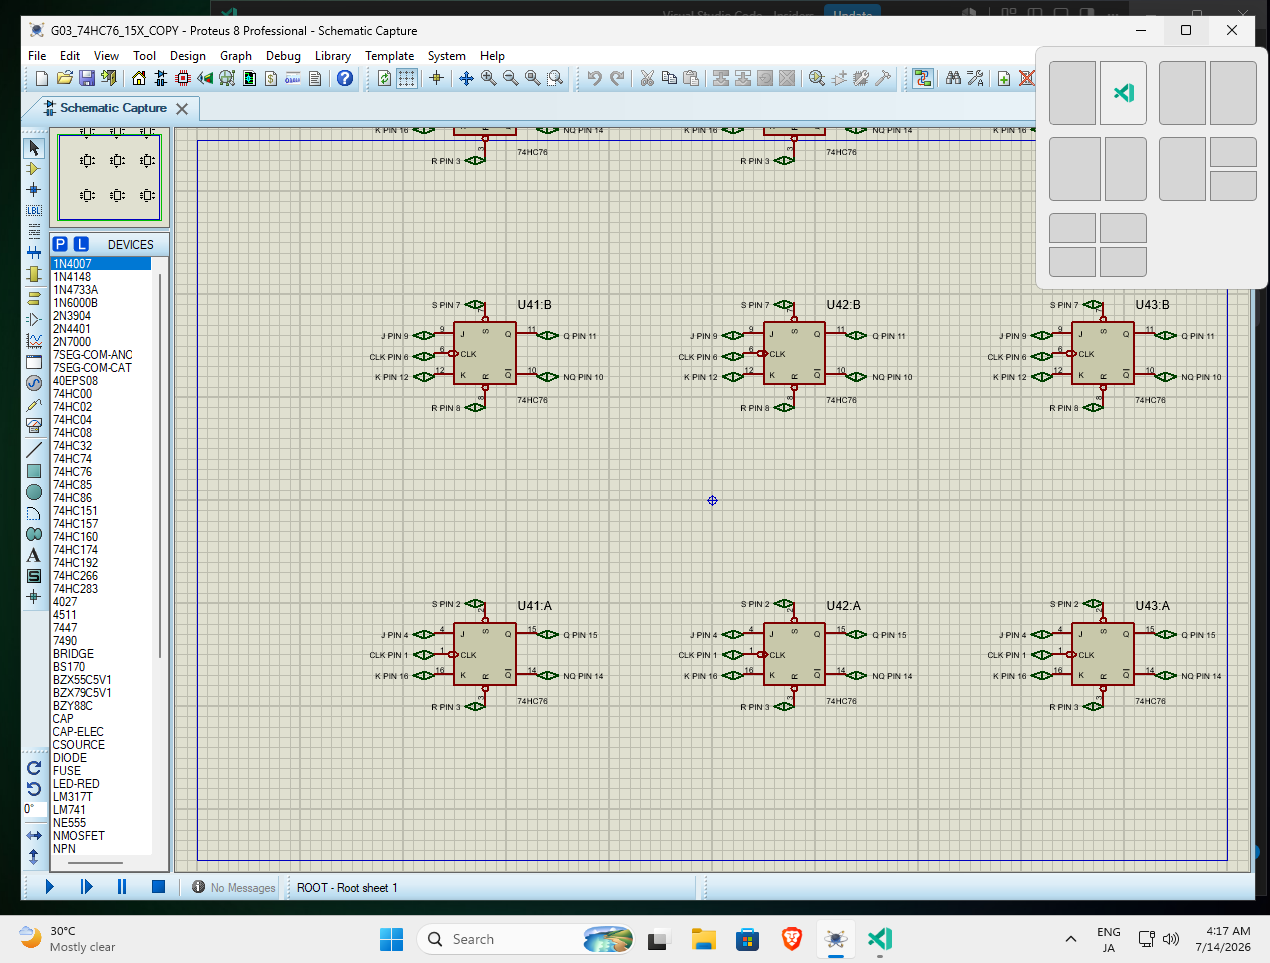
proteus/experiments/runs/dil16_dual_jk_ff_74hc76_terminal_v3_temp_2026_07_14/04_local_proteus_gate/G03_74HC76_15X_before_close.png
