ProGenEDA/ProGenEDA-DEV/proteus/experiments/runs/dil16_dual_jk_ff_terminal_v2_temp_2026_07_13/06_local_proteus_gate/G07_4027_ACCEPTED_DONOR_VISIBLE_BEFORE_CLOSE.png

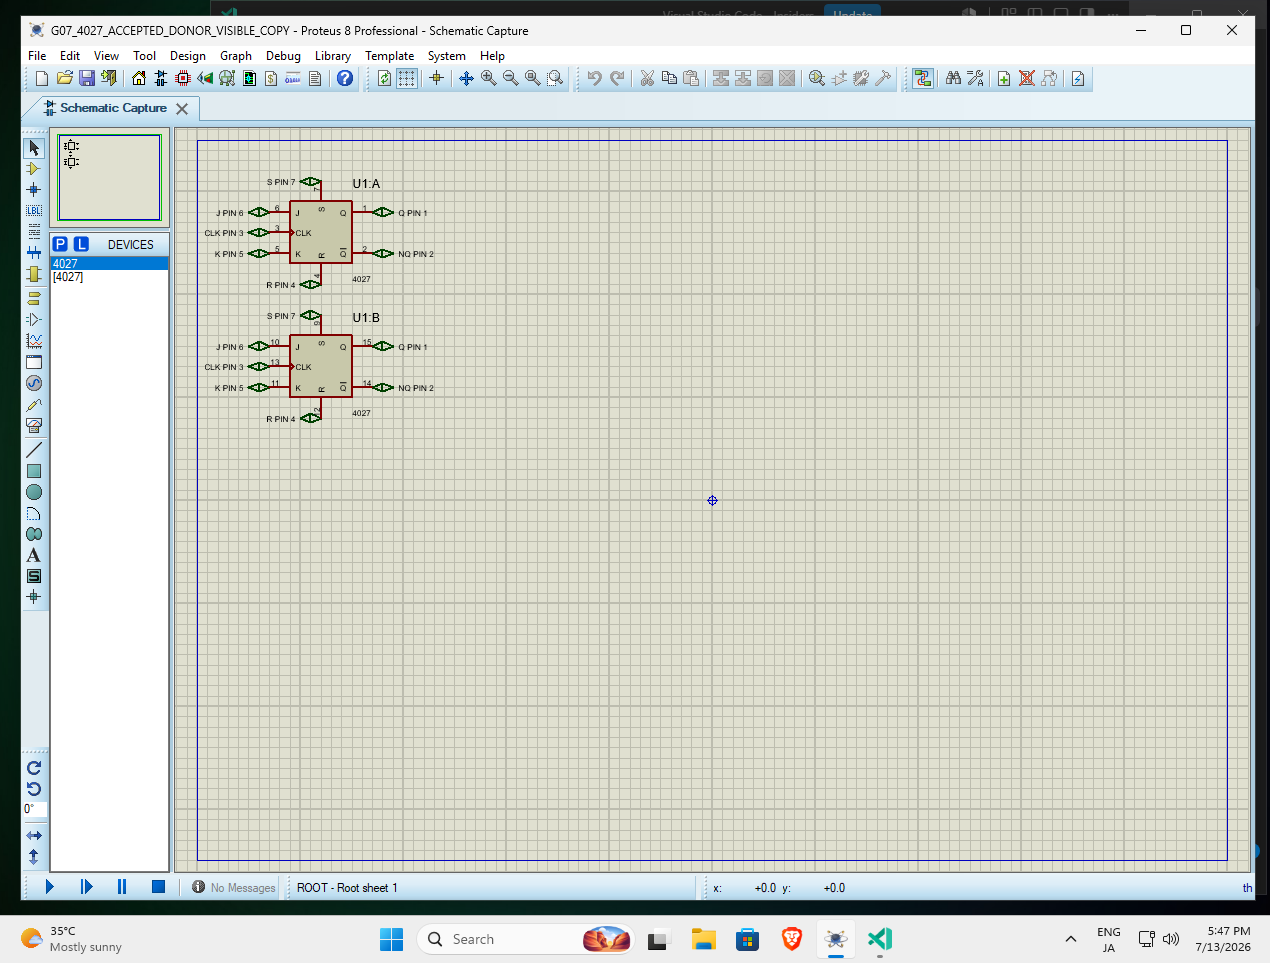
proteus/experiments/runs/dil16_dual_jk_ff_terminal_v2_temp_2026_07_13/06_local_proteus_gate/G07_4027_ACCEPTED_DONOR_VISIBLE_BEFORE_CLOSE.png
