ProGenEDA/ProGenEDA-DEV/proteus/experiments/runs/dil16_mux_74hc151_terminal_v3_temp_2026_07_15/01_solo_1x/C04_74HC151_1X_COMPLETE_INITIAL_before_close.png

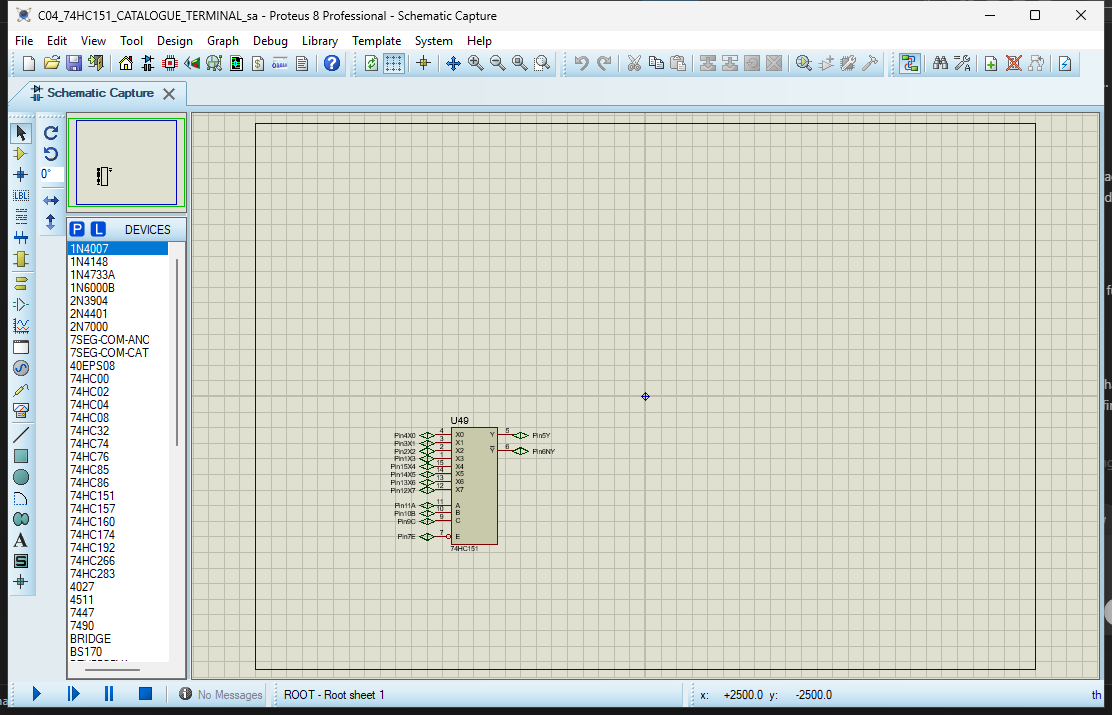
proteus/experiments/runs/dil16_mux_74hc151_terminal_v3_temp_2026_07_15/01_solo_1x/C04_74HC151_1X_COMPLETE_INITIAL_before_close.png
