ProGenEDA/ProGenEDA-DEV/proteus/experiments/runs/frozen_43_family_mix_matrix_v1_temp_2026_07_16/01_uniform_3x/02_proteus_gate.png

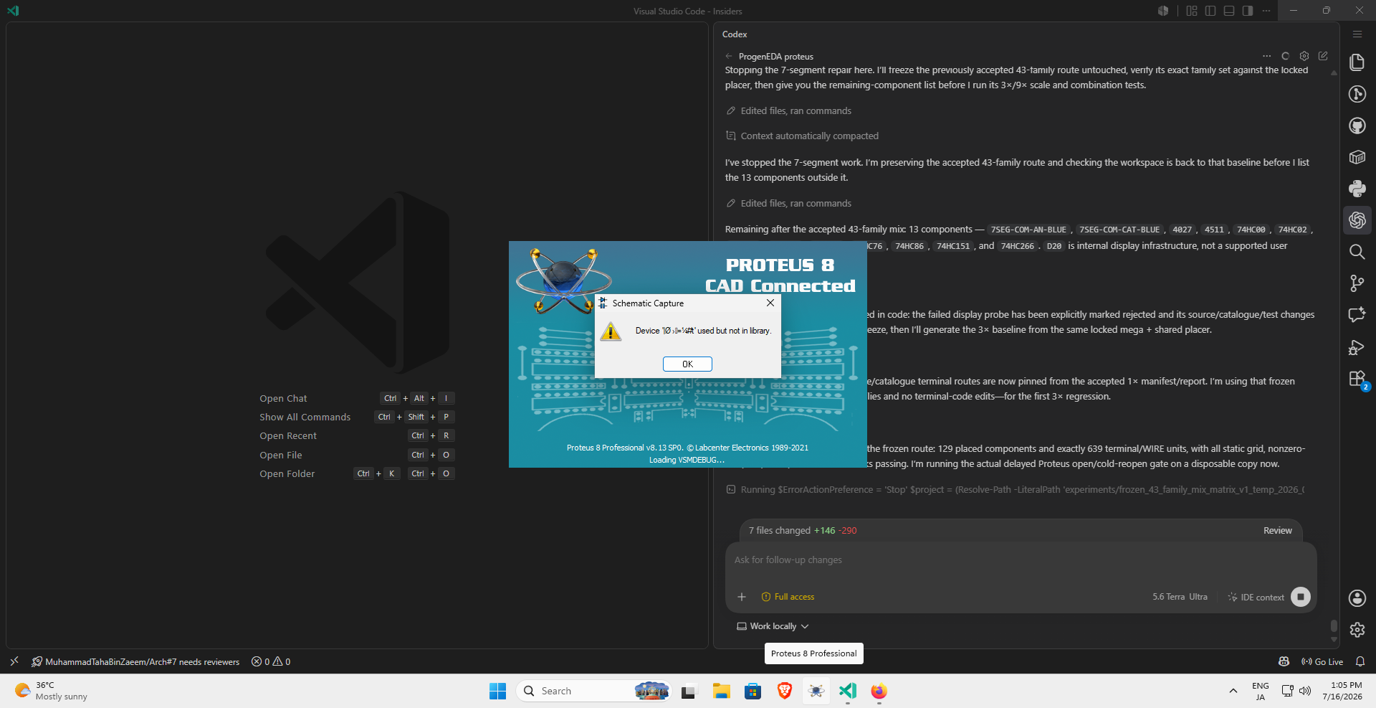
proteus/experiments/runs/frozen_43_family_mix_matrix_v1_temp_2026_07_16/01_uniform_3x/02_proteus_gate.png
