ProGenEDA/ProGenEDA-DEV/proteus/experiments/runs/frozen_43_family_mix_matrix_v1_temp_2026_07_16/17_switch_bare_full_mix/U19_43F_SWITCH_BARE_3X_U107_CANVAS.png

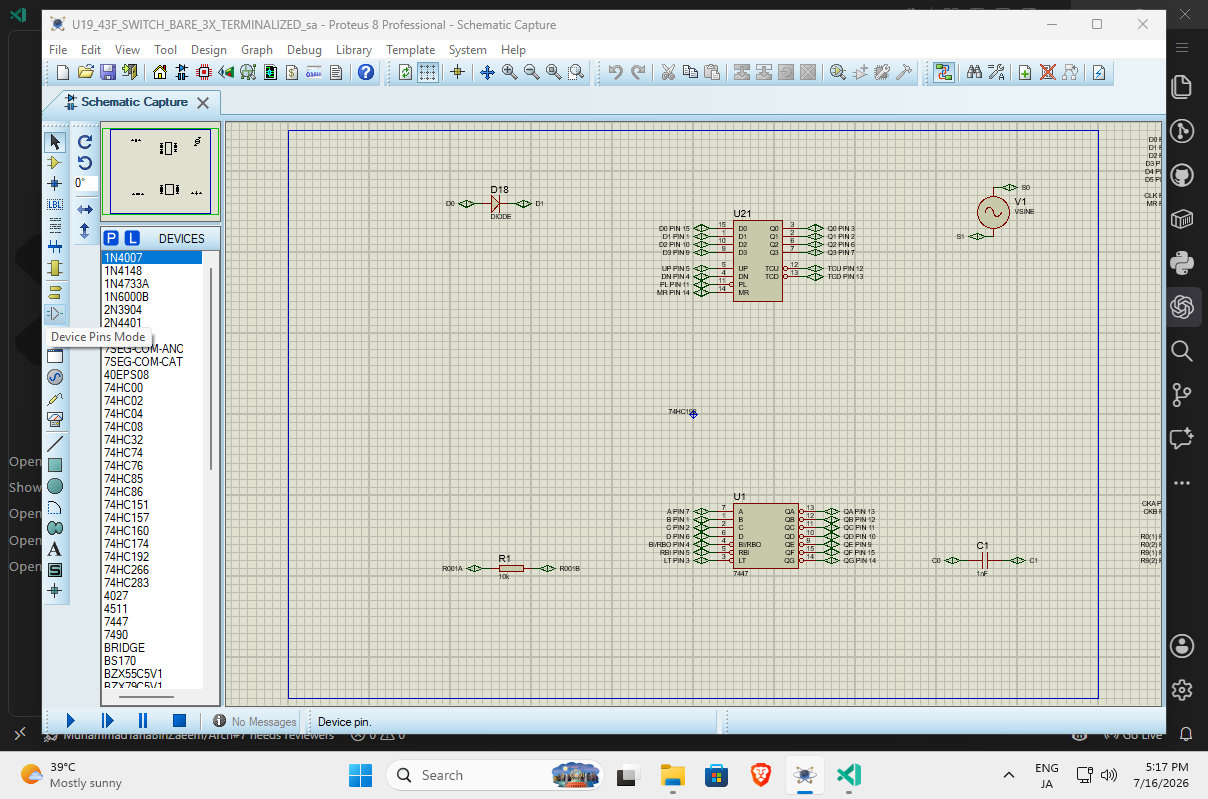
proteus/experiments/runs/frozen_43_family_mix_matrix_v1_temp_2026_07_16/17_switch_bare_full_mix/U19_43F_SWITCH_BARE_3X_U107_CANVAS.png
