ProGenEDA/ProGenEDA-DEV/proteus/experiments/runs/mixed_all_supported_totalmix_v1_temp_2026_07_15/cumulative_ladder_v1/S00_totalmix_fresh/01_S00_BARE_VIEW_ENTIRE_SHEET.png

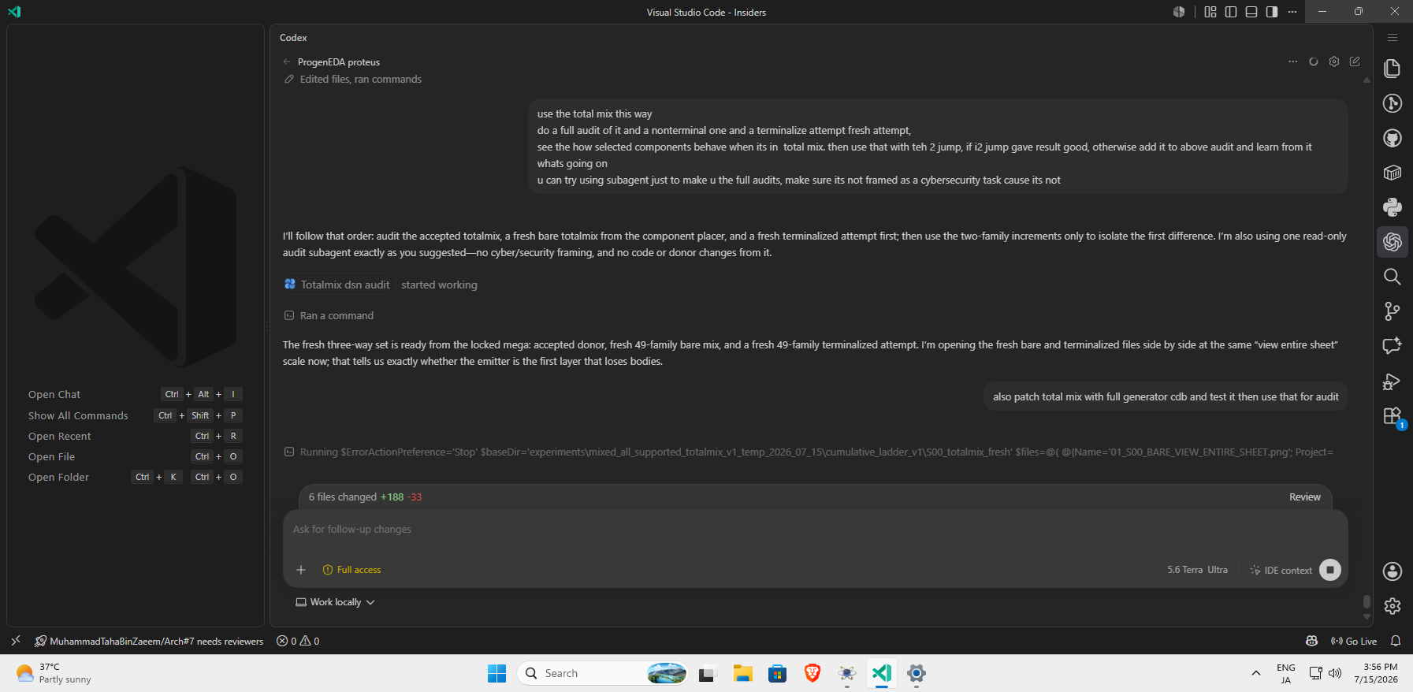
proteus/experiments/runs/mixed_all_supported_totalmix_v1_temp_2026_07_15/cumulative_ladder_v1/S00_totalmix_fresh/01_S00_BARE_VIEW_ENTIRE_SHEET.png
