ProGenEDA/ProGenEDA-DEV/proteus/experiments/runs/mixed_all_supported_totalmix_v1_temp_2026_07_15/cumulative_ladder_v1/S00_totalmix_fresh/06_S00_FRESH_TERMINAL_FULL_GENERATOR_CDB_30S_RETRY.png

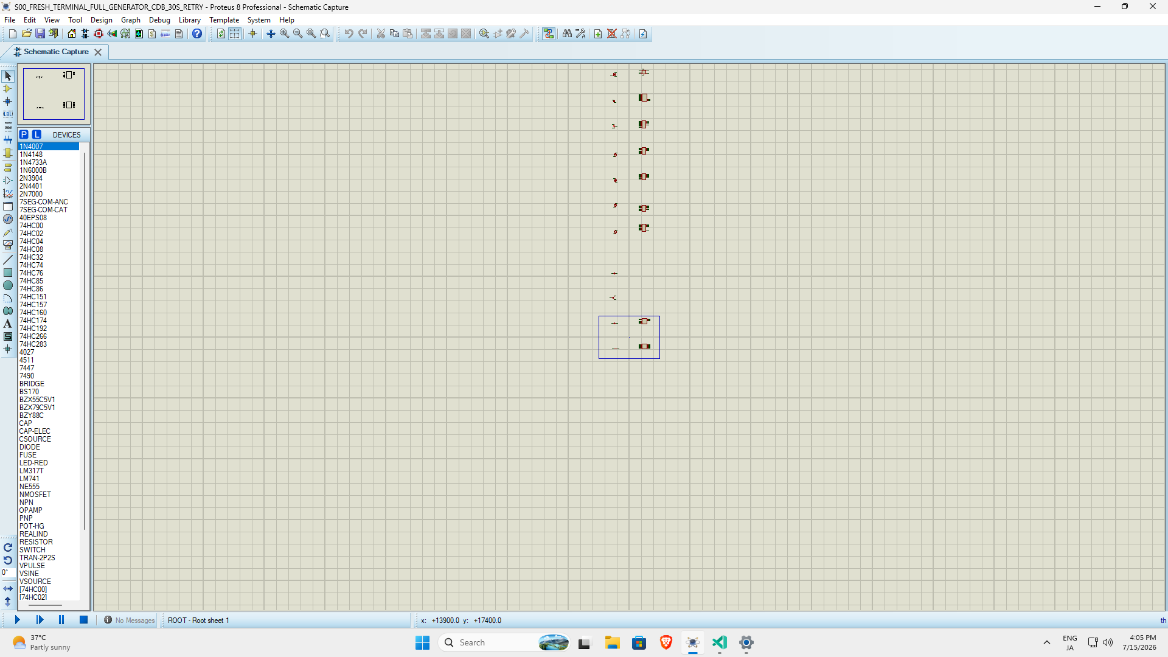
proteus/experiments/runs/mixed_all_supported_totalmix_v1_temp_2026_07_15/cumulative_ladder_v1/S00_totalmix_fresh/06_S00_FRESH_TERMINAL_FULL_GENERATOR_CDB_30S_RETRY.png
