ProGenEDA/ProGenEDA-DEV/proteus/experiments/runs/mixed_all_supported_totalmix_v1_temp_2026_07_15/diagnostic_prefixes/P02_PLUS_TERMINAL_LEADING/P02_CAPTURE.png

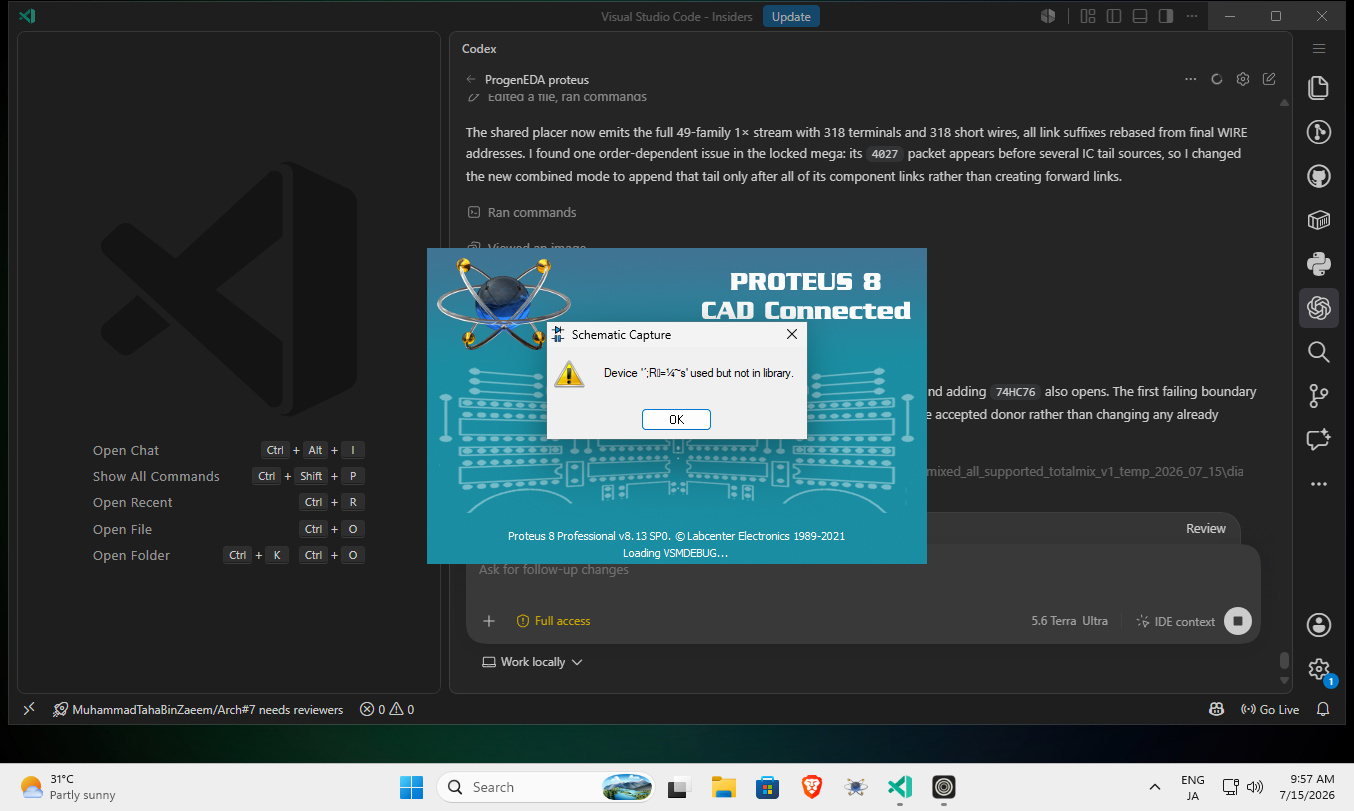
proteus/experiments/runs/mixed_all_supported_totalmix_v1_temp_2026_07_15/diagnostic_prefixes/P02_PLUS_TERMINAL_LEADING/P02_CAPTURE.png
