ProGenEDA/ProGenEDA-DEV/proteus/experiments/runs/mixed_all_supported_totalmix_v1_temp_2026_07_15/MF2/01_MF2_TERMINAL_NORMAL_OPEN.png

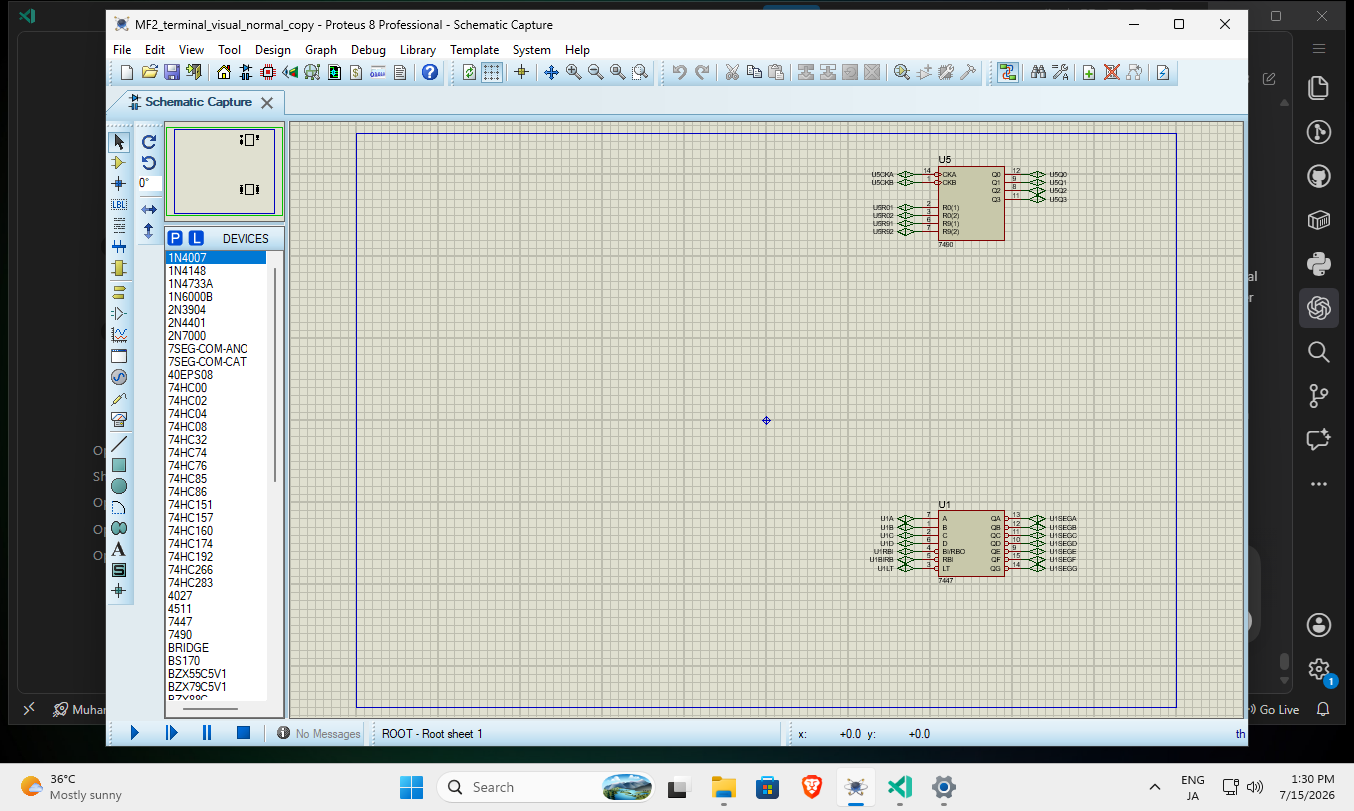
proteus/experiments/runs/mixed_all_supported_totalmix_v1_temp_2026_07_15/MF2/01_MF2_TERMINAL_NORMAL_OPEN.png
