ProGenEDA/ProGenEDA-DEV/proteus/experiments/runs/mixed_all_supported_totalmix_v1_temp_2026_07_15/MF4/04_MF4_VIEW_MENU.png

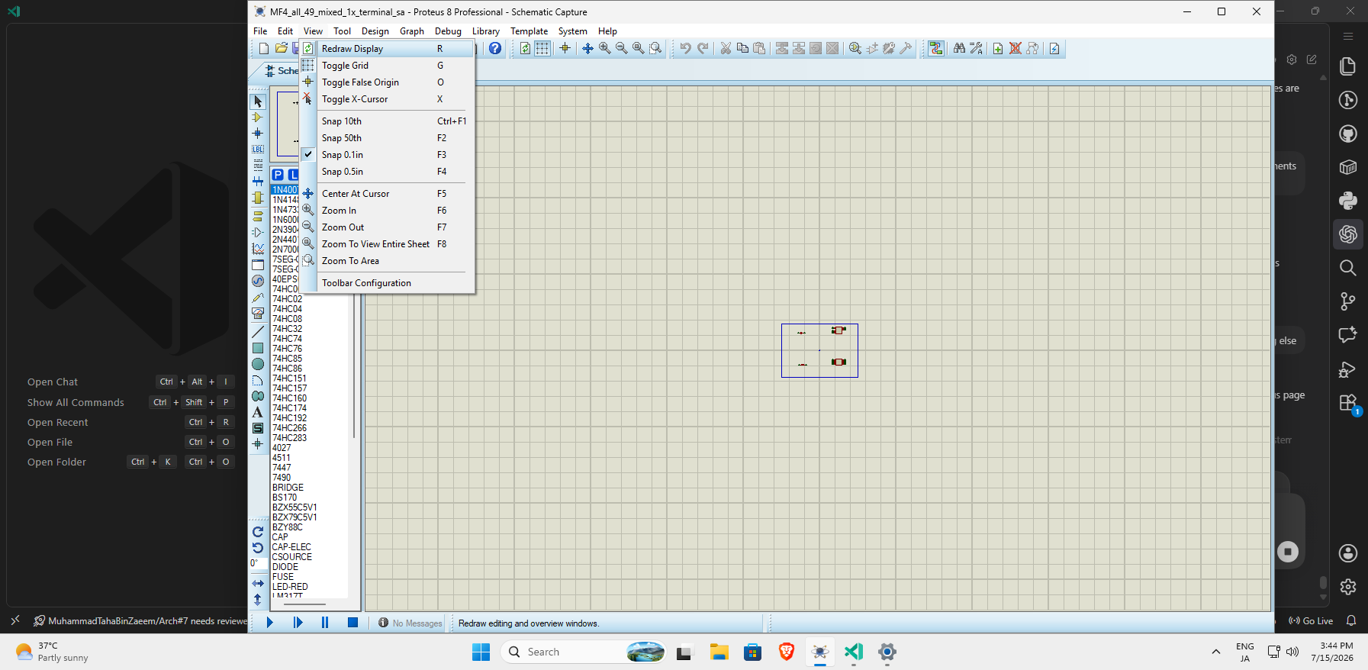
proteus/experiments/runs/mixed_all_supported_totalmix_v1_temp_2026_07_15/MF4/04_MF4_VIEW_MENU.png
