ProGenEDA/ProGenEDA-DEV/proteus/experiments/runs/mixed_all_supported_totalmix_v1_temp_2026_07_15/MF4/05_ACCEPTED_TOTALMIX_VIEW_ENTIRE_SHEET.png

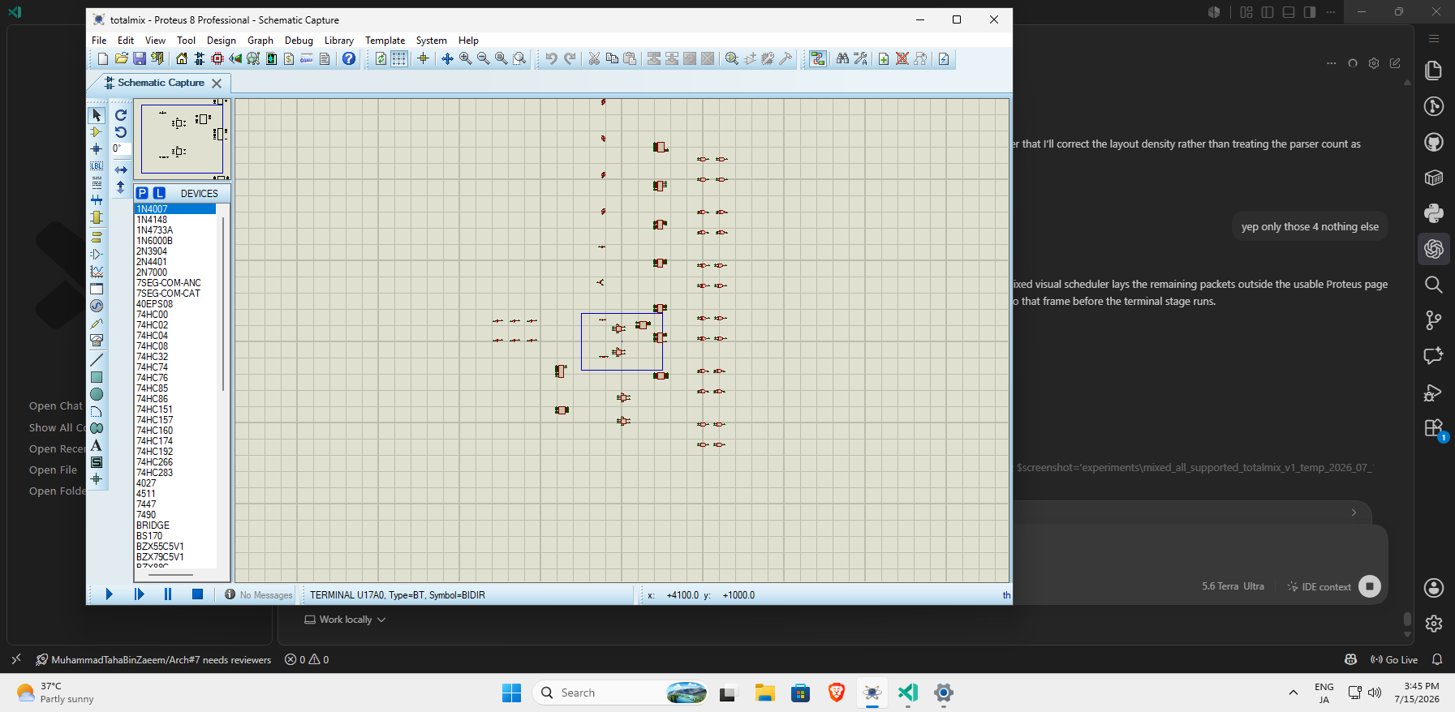
proteus/experiments/runs/mixed_all_supported_totalmix_v1_temp_2026_07_15/MF4/05_ACCEPTED_TOTALMIX_VIEW_ENTIRE_SHEET.png
