ProGenEDA/ProGenEDA-DEV/proteus/experiments/runs/mixed_current_accepted_1x_v2_temp_2026_07_15/04_local_proteus_gate/FIRST_OPEN_before_close.png

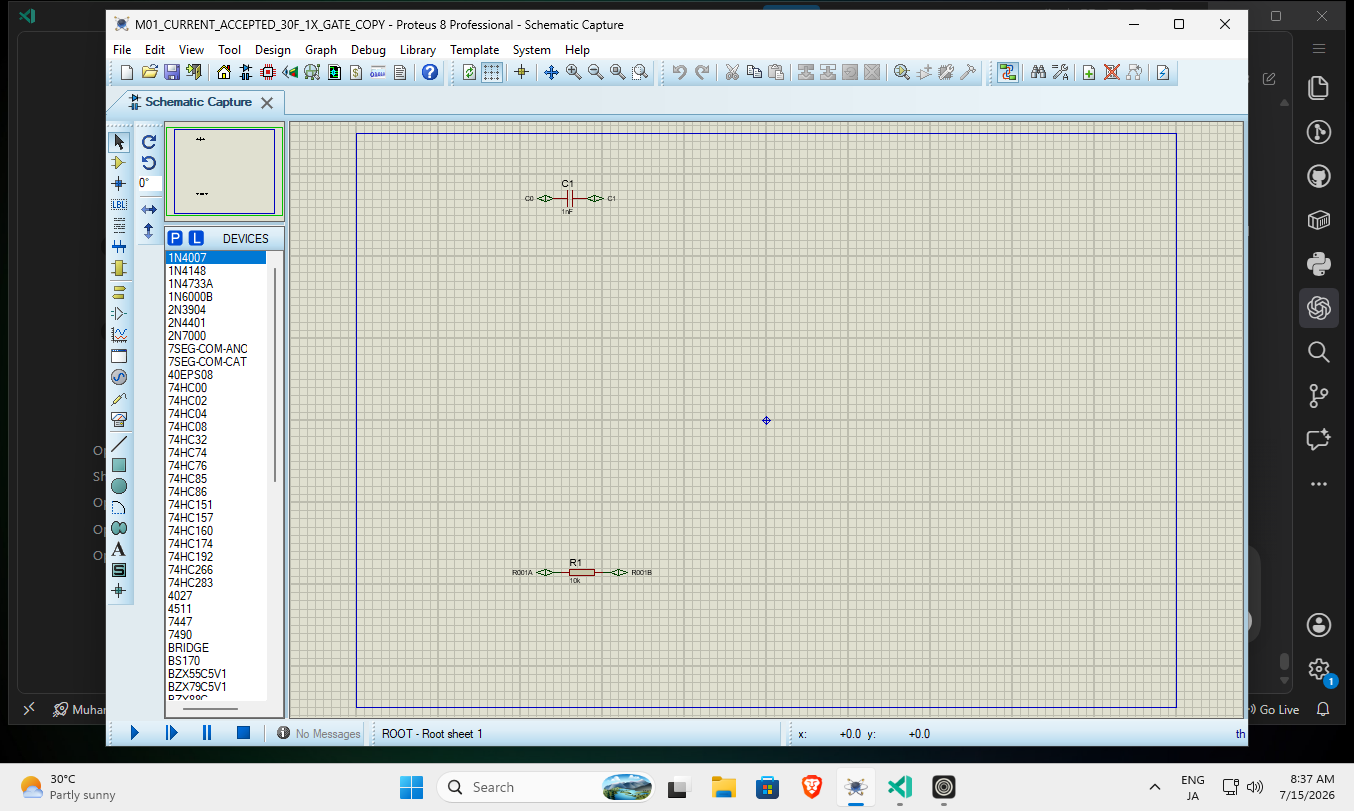
proteus/experiments/runs/mixed_current_accepted_1x_v2_temp_2026_07_15/04_local_proteus_gate/FIRST_OPEN_before_close.png
