ProGenEDA/ProGenEDA-DEV/proteus/experiments/runs/mixed_current_accepted_1x_v2_temp_2026_07_15/totalmix_open_layout_audit.png

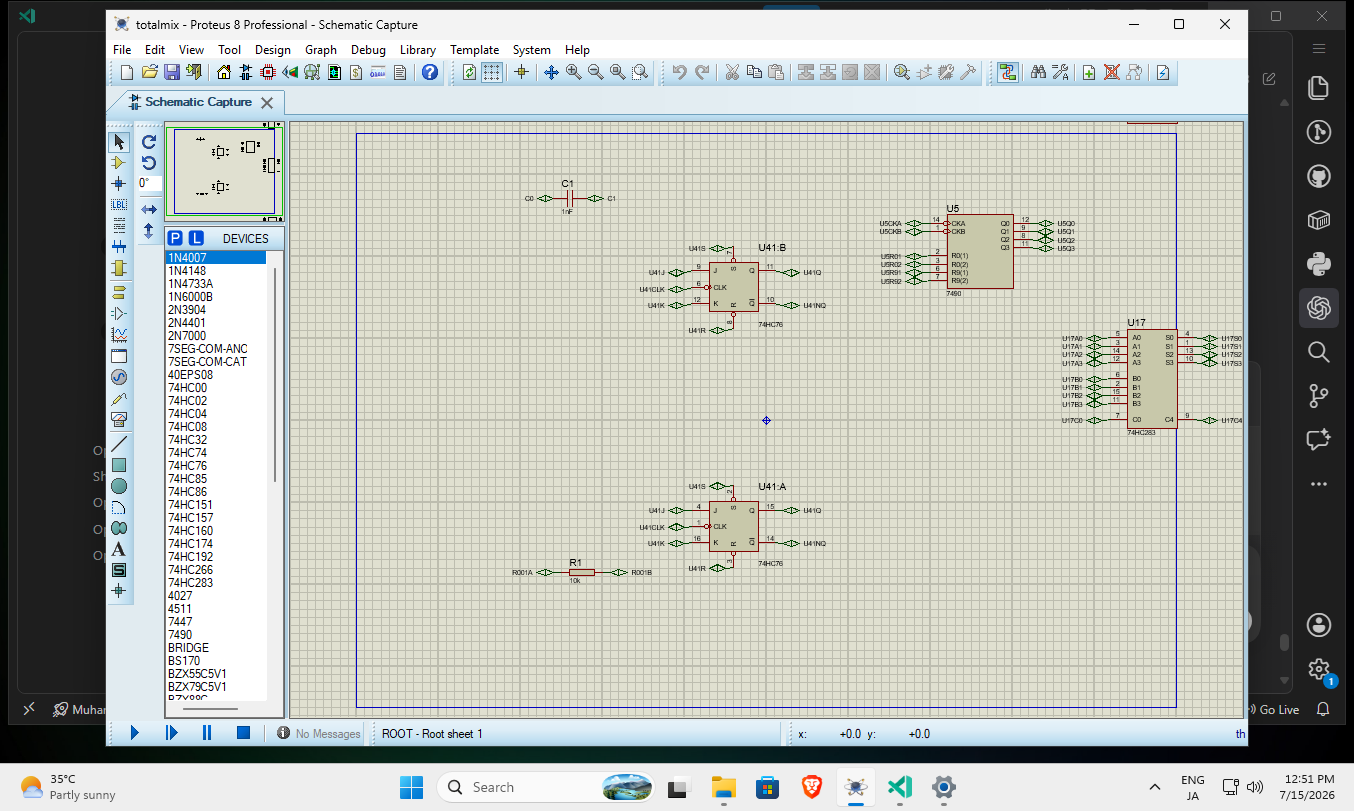
proteus/experiments/runs/mixed_current_accepted_1x_v2_temp_2026_07_15/totalmix_open_layout_audit.png
