ProGenEDA/ProGenEDA-DEV/proteus/experiments/runs/terminal_pending_fast_solo_v1_temp_2026_07_15/S01_IRDIODE_1X/04_local_proteus_gate/FIRST_OPEN_before_close.png

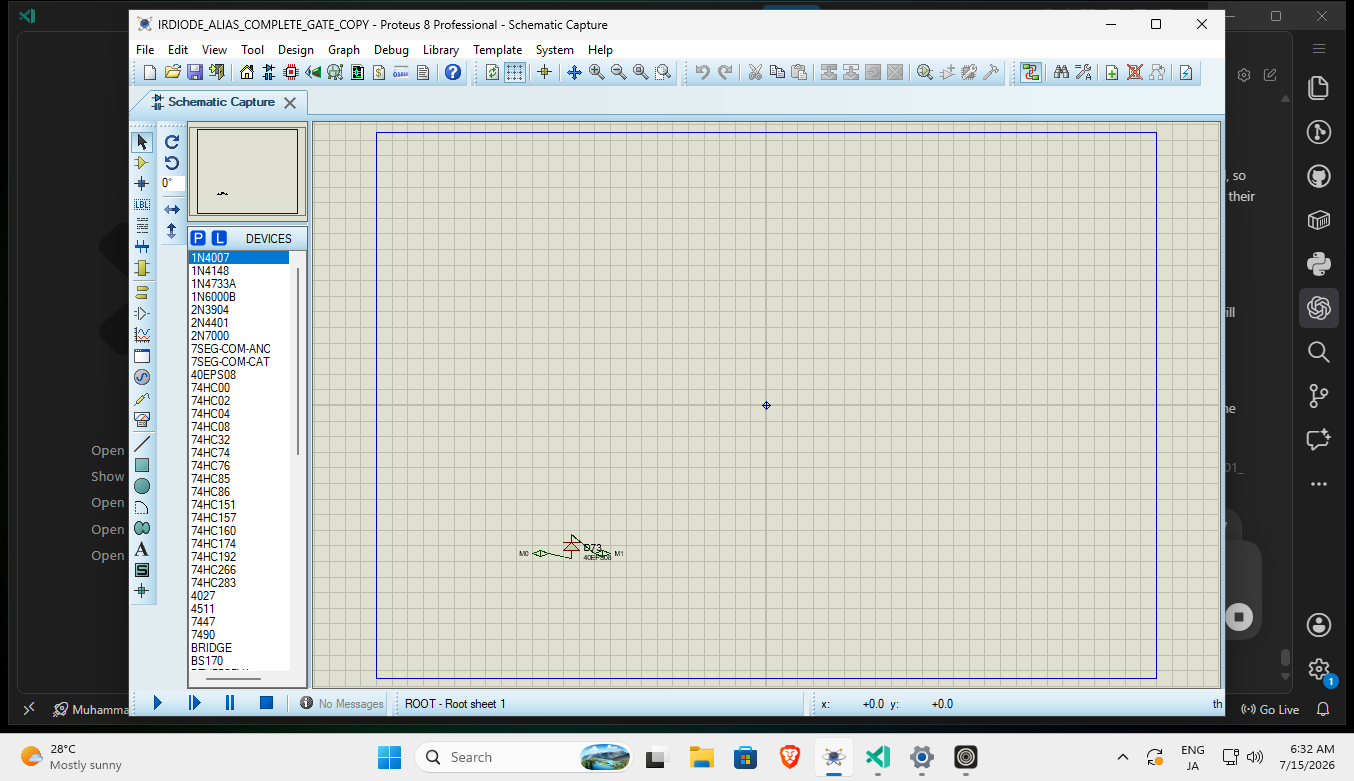
proteus/experiments/runs/terminal_pending_fast_solo_v1_temp_2026_07_15/S01_IRDIODE_1X/04_local_proteus_gate/FIRST_OPEN_before_close.png
