ProGenEDA/ProGenEDA-DEV/proteus/experiments/runs/terminalized_ic_grammar_packs_v1_temp_2026_07_15/04_local_proteus_gate/I01_APPEND_TAIL_4511_74HC151_1X_NORMAL.png

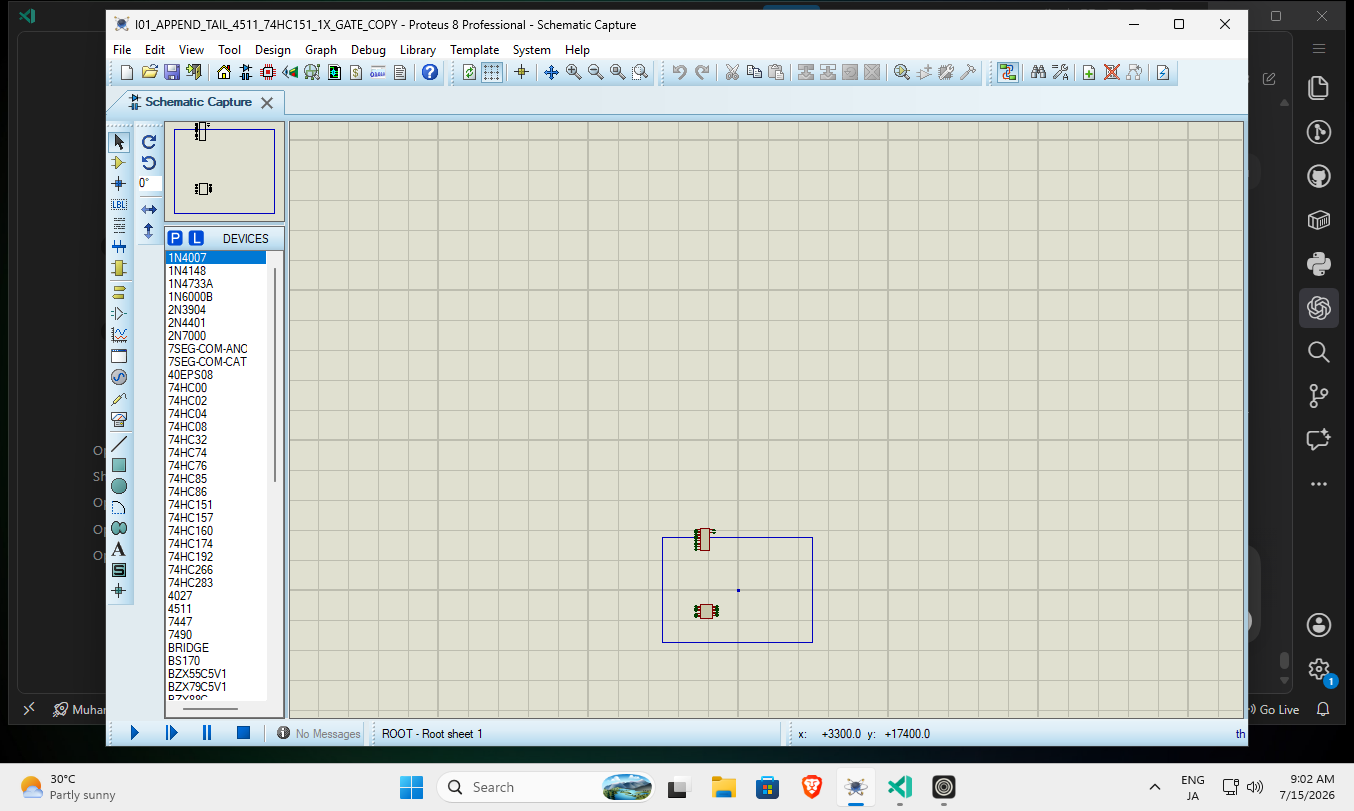
proteus/experiments/runs/terminalized_ic_grammar_packs_v1_temp_2026_07_15/04_local_proteus_gate/I01_APPEND_TAIL_4511_74HC151_1X_NORMAL.png
