ProGenEDA/ProGenEDA-DEV/proteus/experiments/runs/terminalized_ic_grammar_packs_v1_temp_2026_07_15/04_local_proteus_gate/I02B_SINGLE_FF_QUAD_LOGIC_1X_NORMAL.png

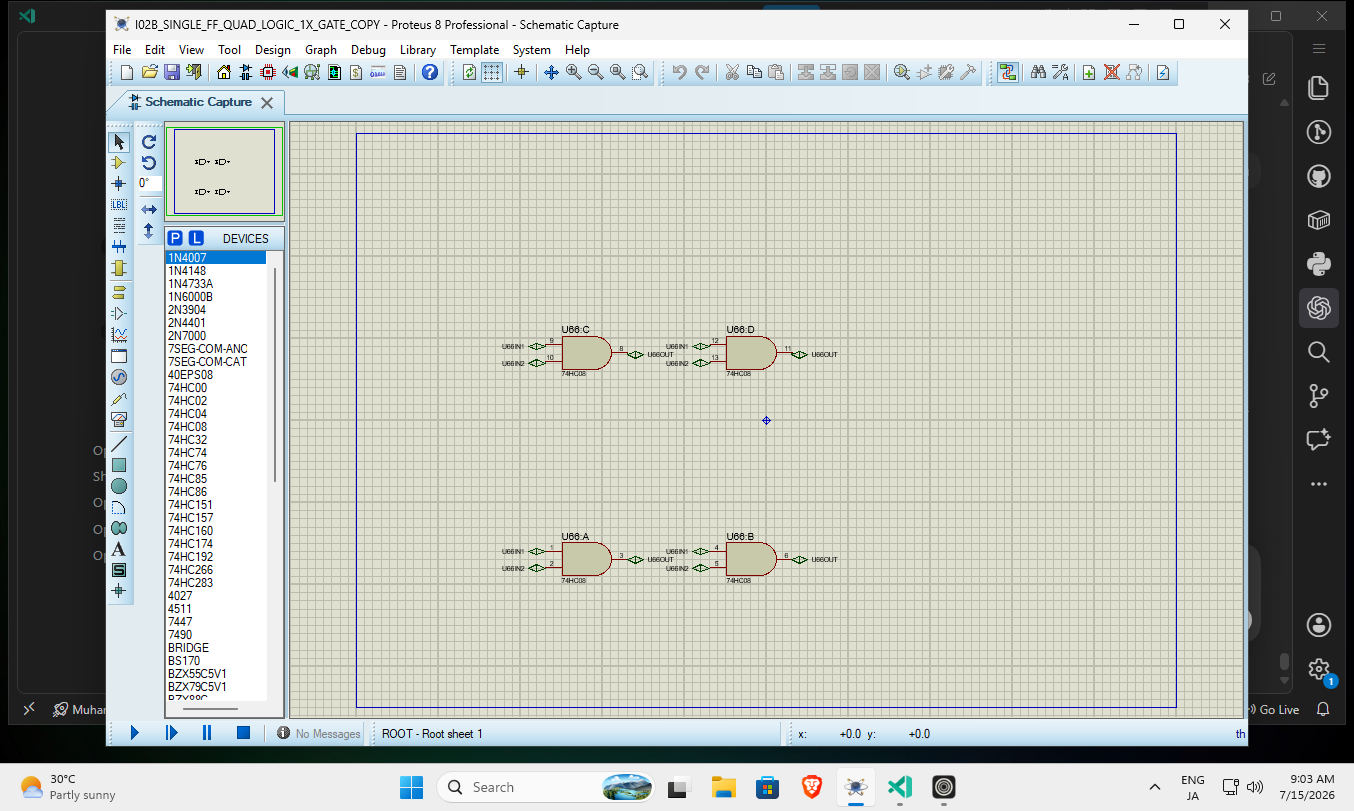
proteus/experiments/runs/terminalized_ic_grammar_packs_v1_temp_2026_07_15/04_local_proteus_gate/I02B_SINGLE_FF_QUAD_LOGIC_1X_NORMAL.png
