ProGenEDA/ProGenEDA-DEV/proteus/experiments/runs/totalmix_38_growth_missing7_v1_temp_2026_07_15/01_ne555_39f/02_local_proteus_gate/02_COLD_REOPEN_15S.png

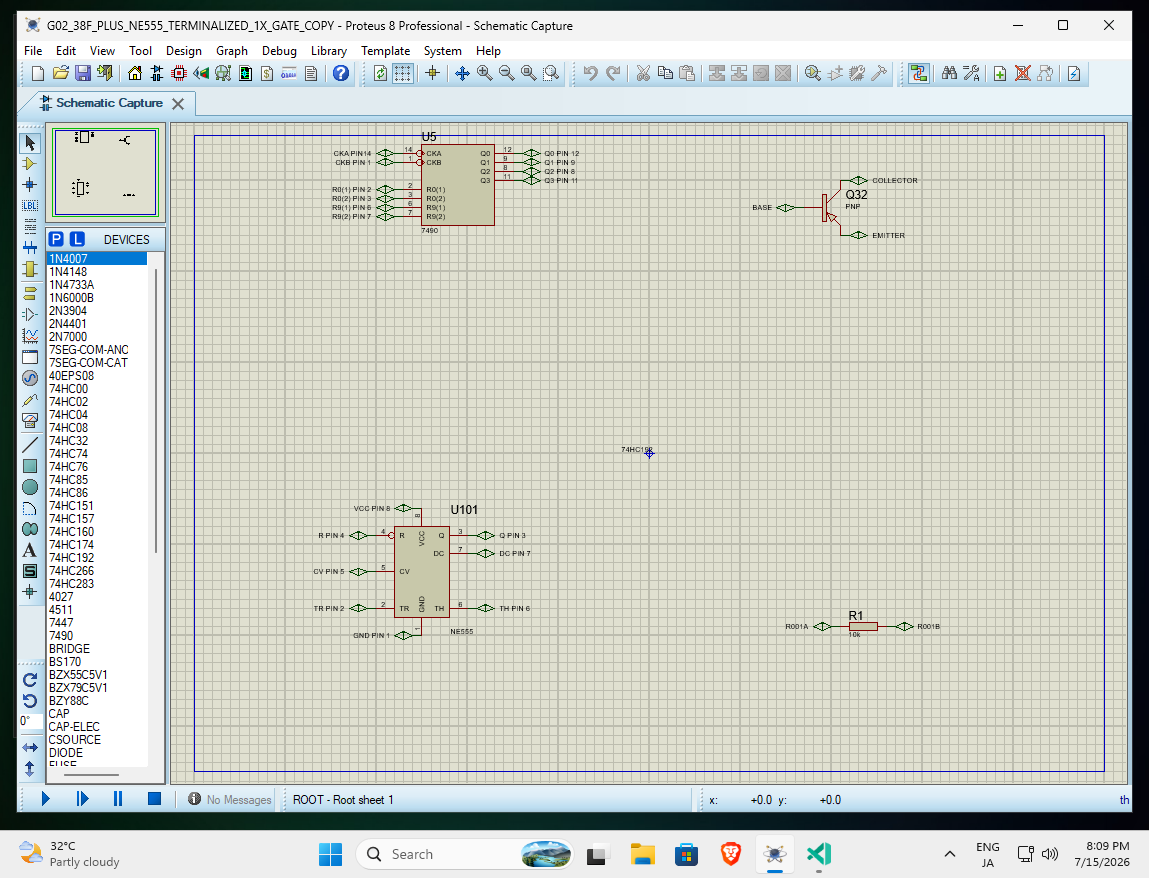
proteus/experiments/runs/totalmix_38_growth_missing7_v1_temp_2026_07_15/01_ne555_39f/02_local_proteus_gate/02_COLD_REOPEN_15S.png
