ProGenEDA/ProGenEDA-DEV/proteus/experiments/runs/totalmix_38_growth_missing7_v1_temp_2026_07_15/02_lm741_40f/02_local_proteus_gate/01_NORMAL_OPEN_15S.png

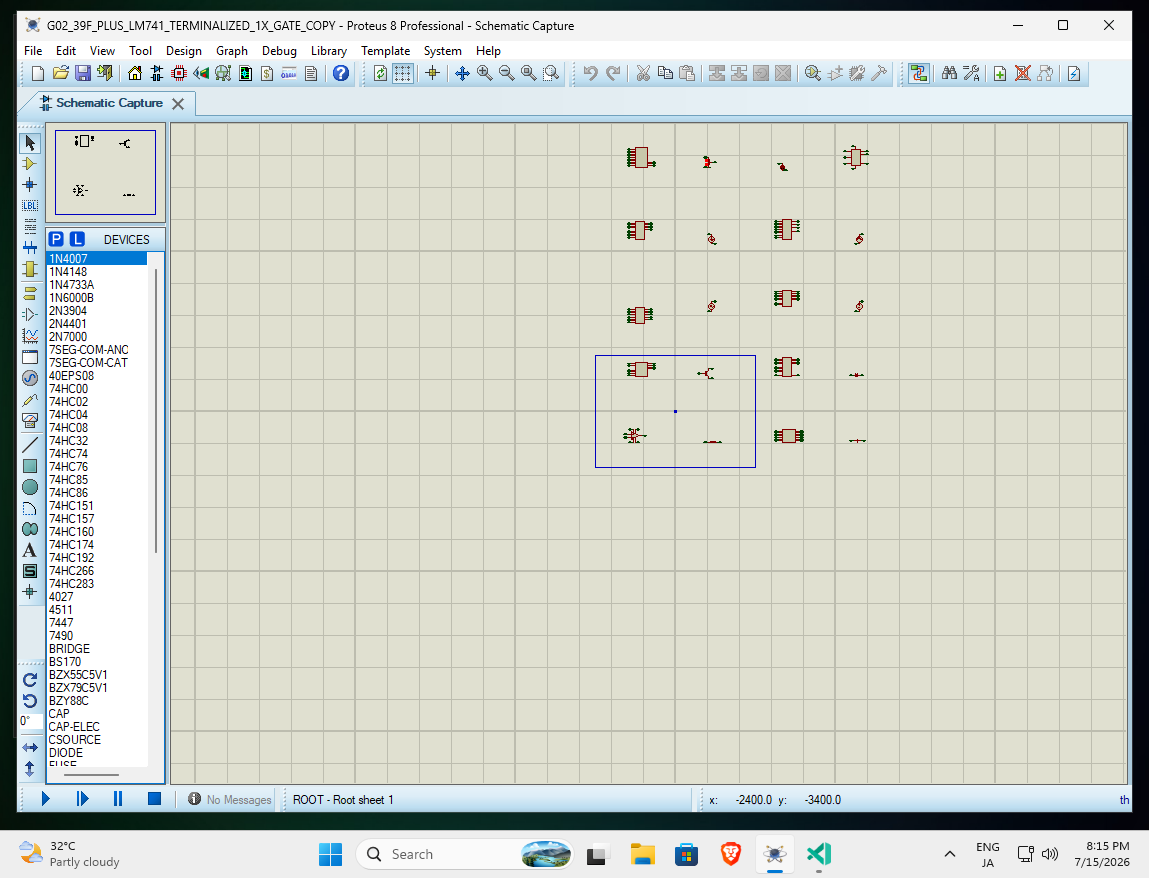
proteus/experiments/runs/totalmix_38_growth_missing7_v1_temp_2026_07_15/02_lm741_40f/02_local_proteus_gate/01_NORMAL_OPEN_15S.png
