ProGenEDA/ProGenEDA-DEV/proteus/experiments/runs/totalmix_38_growth_missing7_v1_temp_2026_07_15/05_tran_2p2s_43f/02_local_proteus_gate/02_cold_reopen_screenshot.png

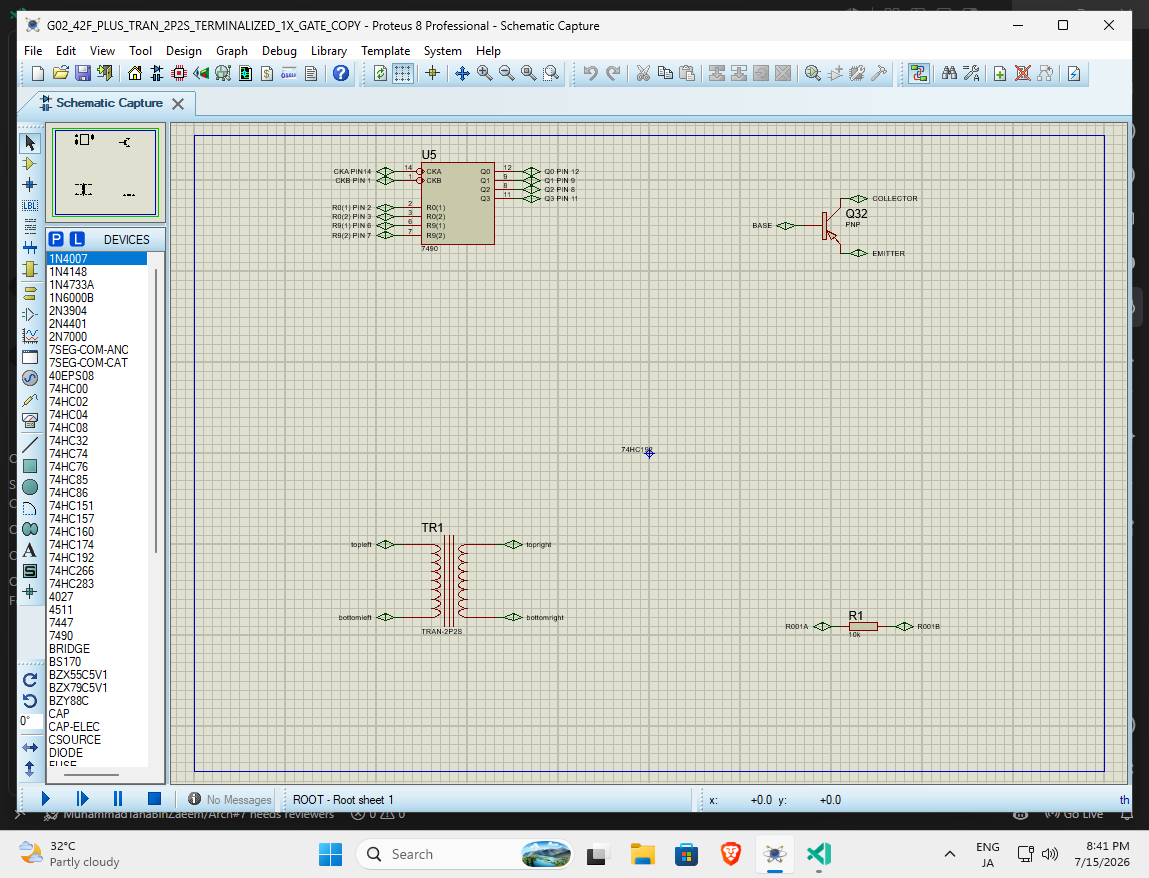
proteus/experiments/runs/totalmix_38_growth_missing7_v1_temp_2026_07_15/05_tran_2p2s_43f/02_local_proteus_gate/02_cold_reopen_screenshot.png
