ProGenEDA/ProGenEDA-DEV/proteus/experiments/runs/totalmix_38_growth_missing7_v1_temp_2026_07_15/06_display_anode_44f/00_solo_stages/01_grid_body_contact_trials/02_local_proteus_gate/S04_NATIVE_COLD.png

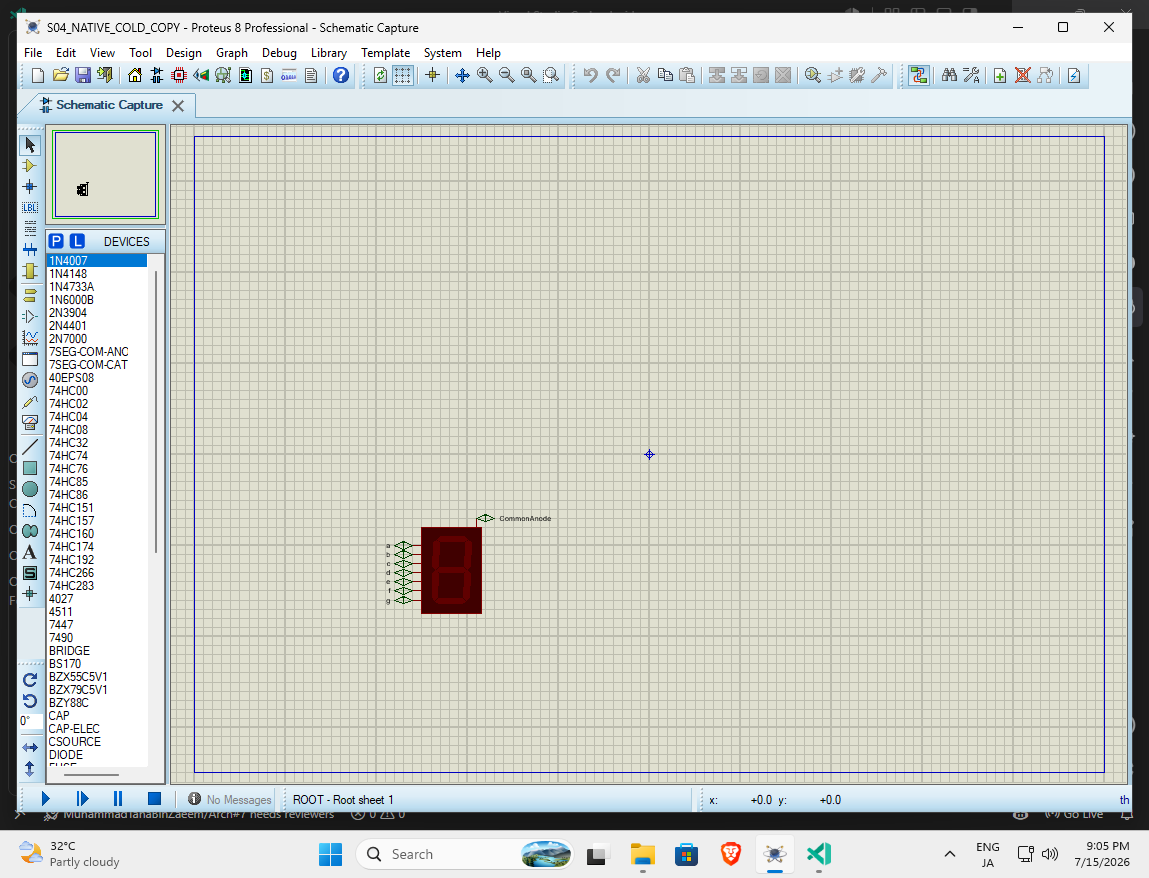
proteus/experiments/runs/totalmix_38_growth_missing7_v1_temp_2026_07_15/06_display_anode_44f/00_solo_stages/01_grid_body_contact_trials/02_local_proteus_gate/S04_NATIVE_COLD.png
