ProGenEDA/ProGenEDA-DEV/proteus/experiments/runs/totalmix_38_growth_missing7_v1_temp_2026_07_15/06_display_anode_44f/03_cumulative_44f/02_local_proteus_gate/G02_NORMAL_OPEN.png

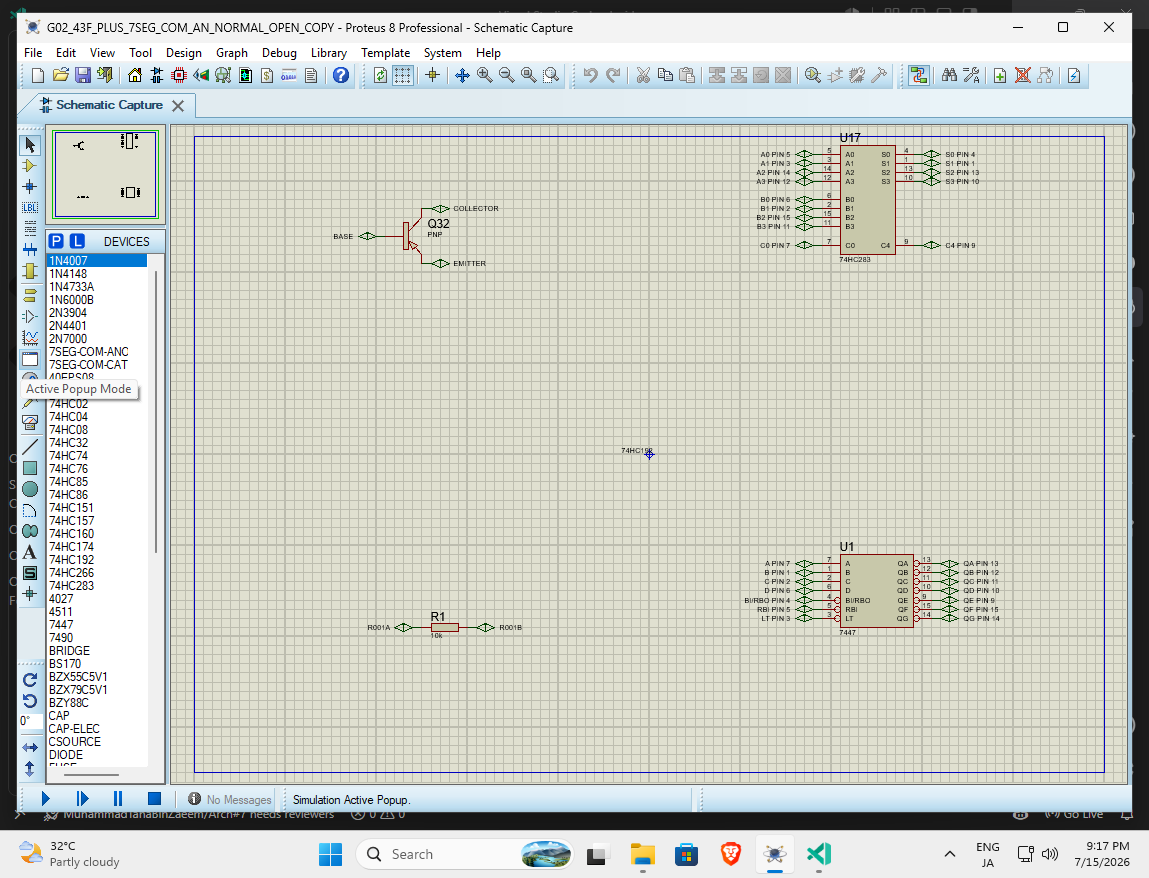
proteus/experiments/runs/totalmix_38_growth_missing7_v1_temp_2026_07_15/06_display_anode_44f/03_cumulative_44f/02_local_proteus_gate/G02_NORMAL_OPEN.png
