ProGenEDA/ProGenEDA-DEV/proteus/experiments/runs/totalmix_all_bare_boundary_isolation_v1_temp_2026_07_15/05_proteus_ctrl_s_diagnostics/B04_ALL49_BODIES_TWO_PIN_ONLY_TERMINALIZED.png

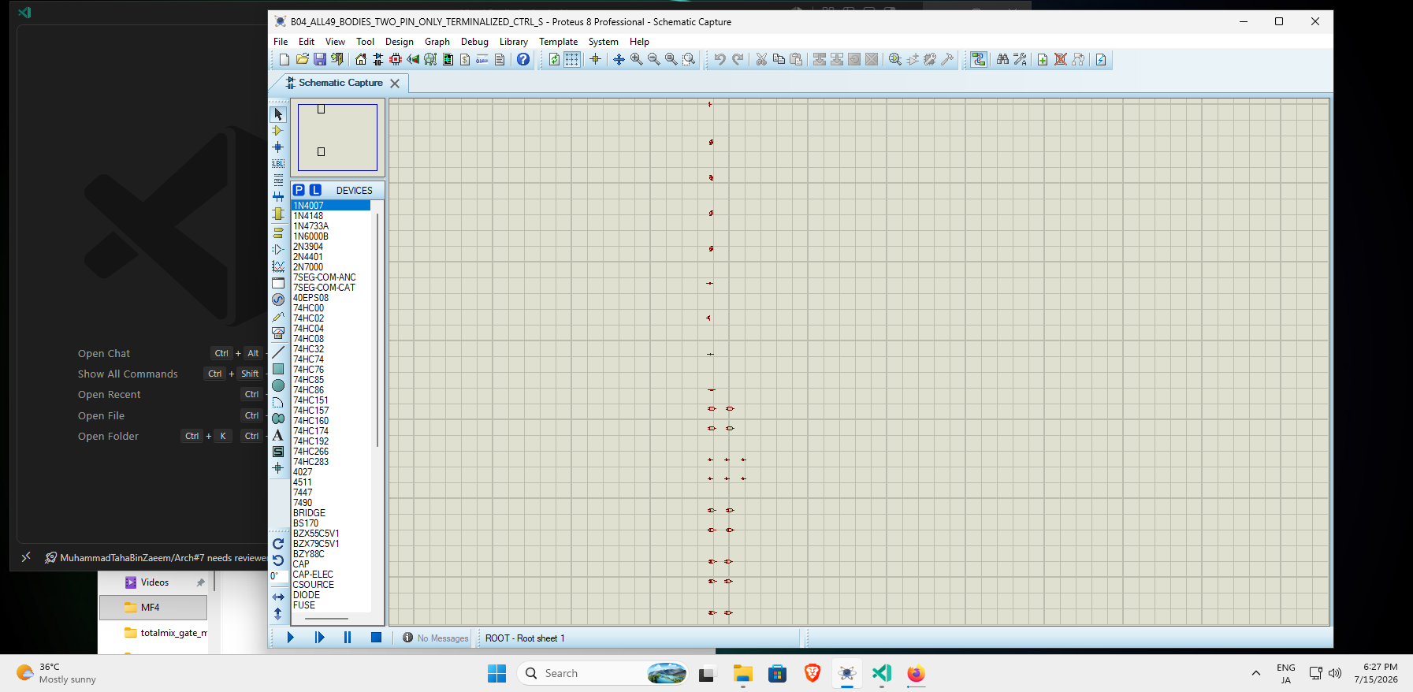
proteus/experiments/runs/totalmix_all_bare_boundary_isolation_v1_temp_2026_07_15/05_proteus_ctrl_s_diagnostics/B04_ALL49_BODIES_TWO_PIN_ONLY_TERMINALIZED.png
