ProGenEDA/ProGenEDA-DEV/proteus/experiments/runs/totalmix_cdb_isolation_v1_temp_2026_07_15/fresh_regeneration_01/SS_02_GENERATED_ALL49_TERMINALIZED_NORMALIZED_CDB.png

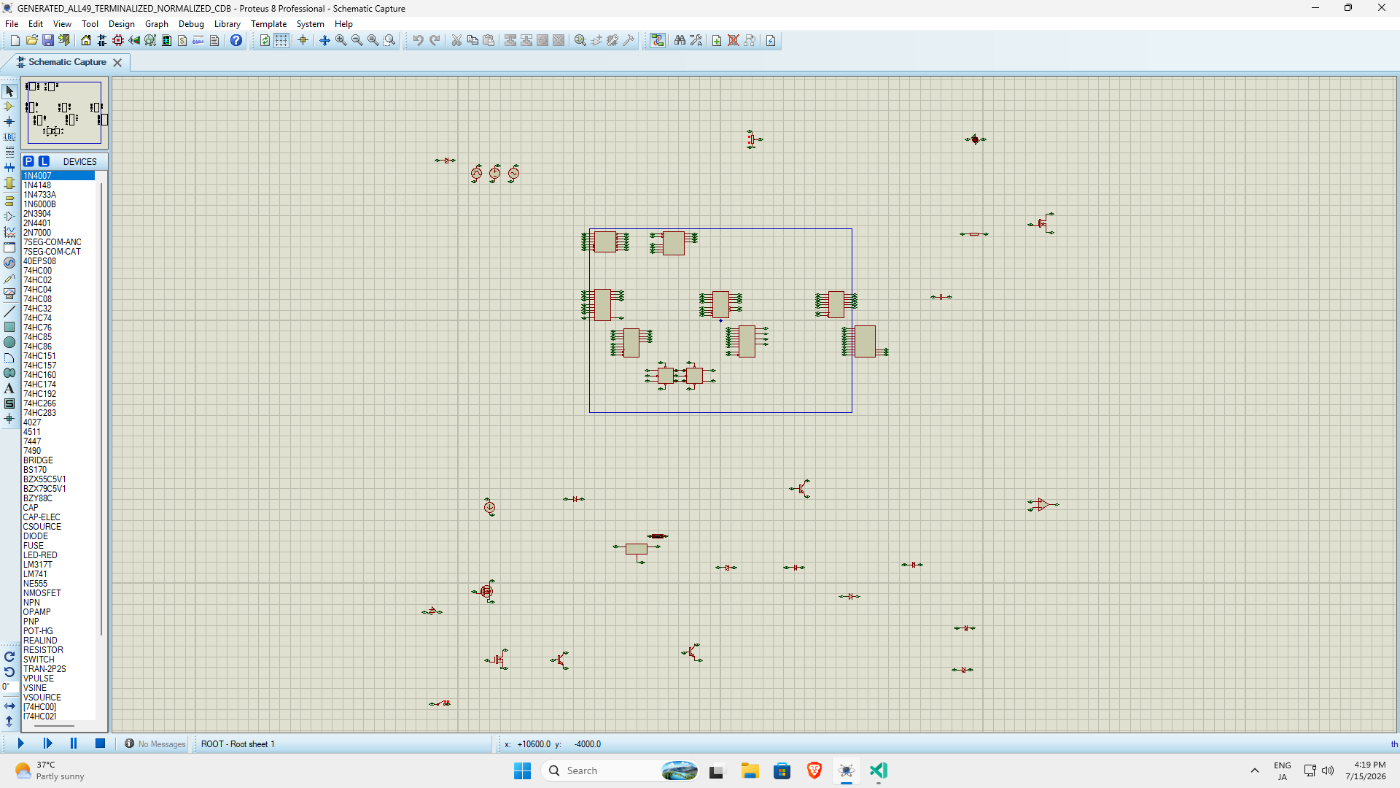
proteus/experiments/runs/totalmix_cdb_isolation_v1_temp_2026_07_15/fresh_regeneration_01/SS_02_GENERATED_ALL49_TERMINALIZED_NORMALIZED_CDB.png
