ProGenEDA/ProGenEDA-DEV/proteus/experiments/runs/totalmix_cdb_isolation_v1_temp_2026_07_15/grid_contact_regeneration_02/SS_02_GENERATED_ALL49_TERMINALIZED_GRID_CONTACTS_NORMALIZED_CDB_FOREGROUND.png

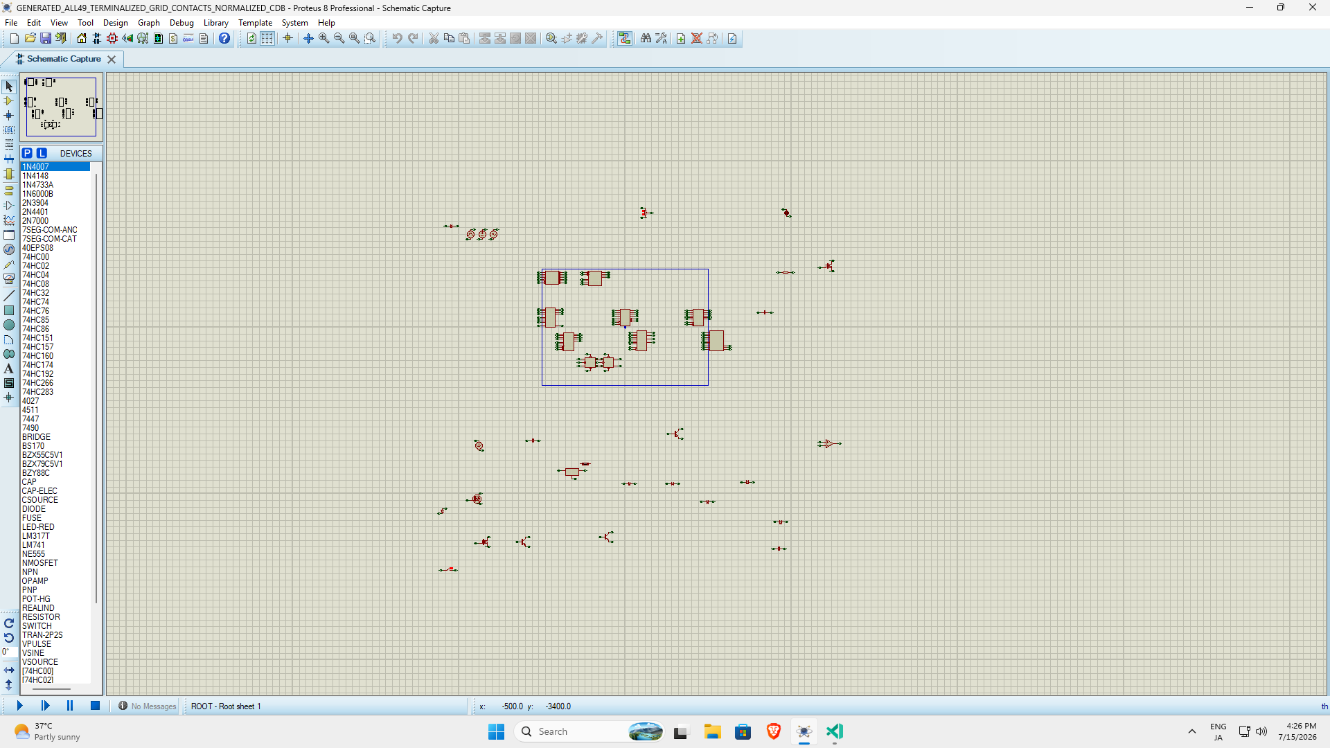
proteus/experiments/runs/totalmix_cdb_isolation_v1_temp_2026_07_15/grid_contact_regeneration_02/SS_02_GENERATED_ALL49_TERMINALIZED_GRID_CONTACTS_NORMALIZED_CDB_FOREGROUND.png
