ProGenEDA/ProGenEDA-DEV/proteus/experiments/runs/totalmix_disappearing_isolation_v2_temp_2026_07_15/01_compact_74hc76_free_baseline/03_bad_object_save_audit/I15_AFTER_BAD_OBJECT_DISMISS_BEFORE_SAVE.png

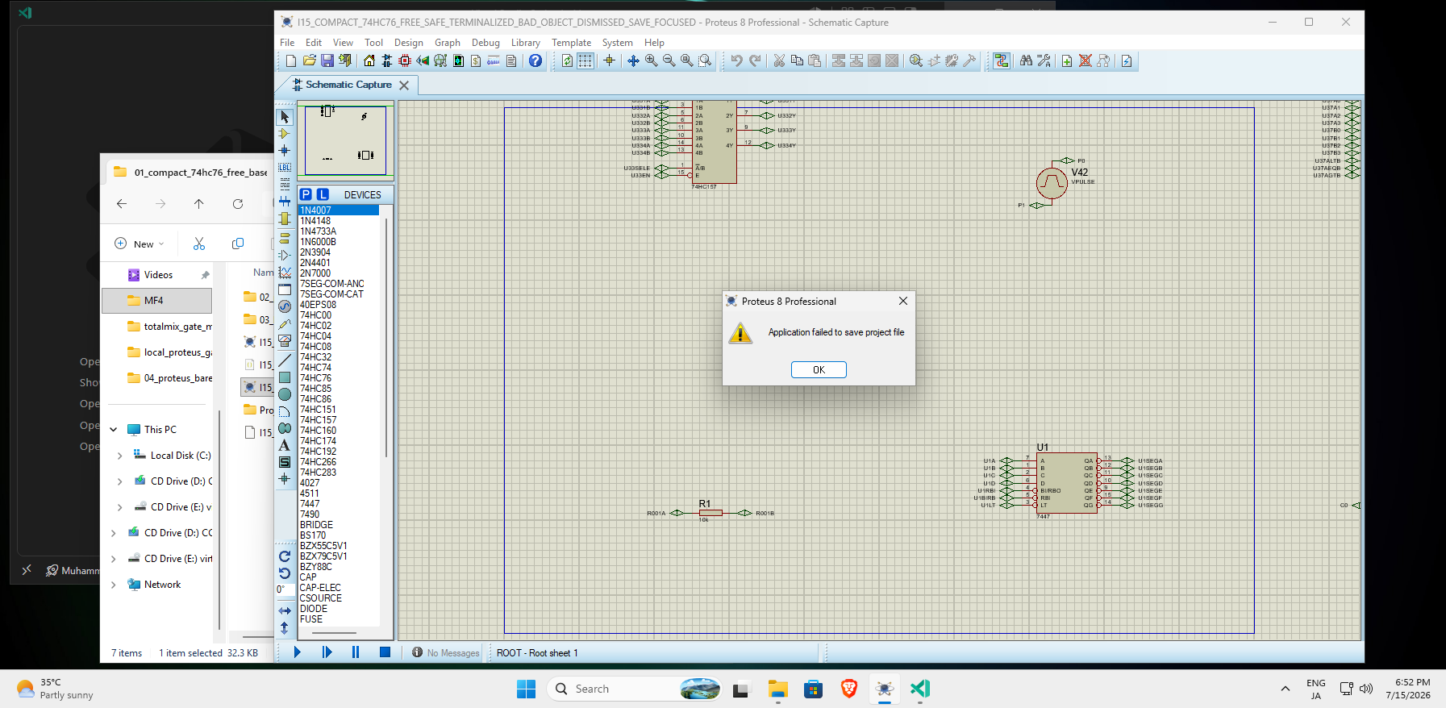
proteus/experiments/runs/totalmix_disappearing_isolation_v2_temp_2026_07_15/01_compact_74hc76_free_baseline/03_bad_object_save_audit/I15_AFTER_BAD_OBJECT_DISMISS_BEFORE_SAVE.png
