ProGenEDA/ProGenEDA-DEV/proteus/experiments/runs/totalmix_disappearing_isolation_v2_temp_2026_07_15/01_compact_74hc76_free_baseline/04_bare_proteus_gate/I15_COMPACT_74HC76_FREE_SAFE_BARE_1X_OPEN_15S.png

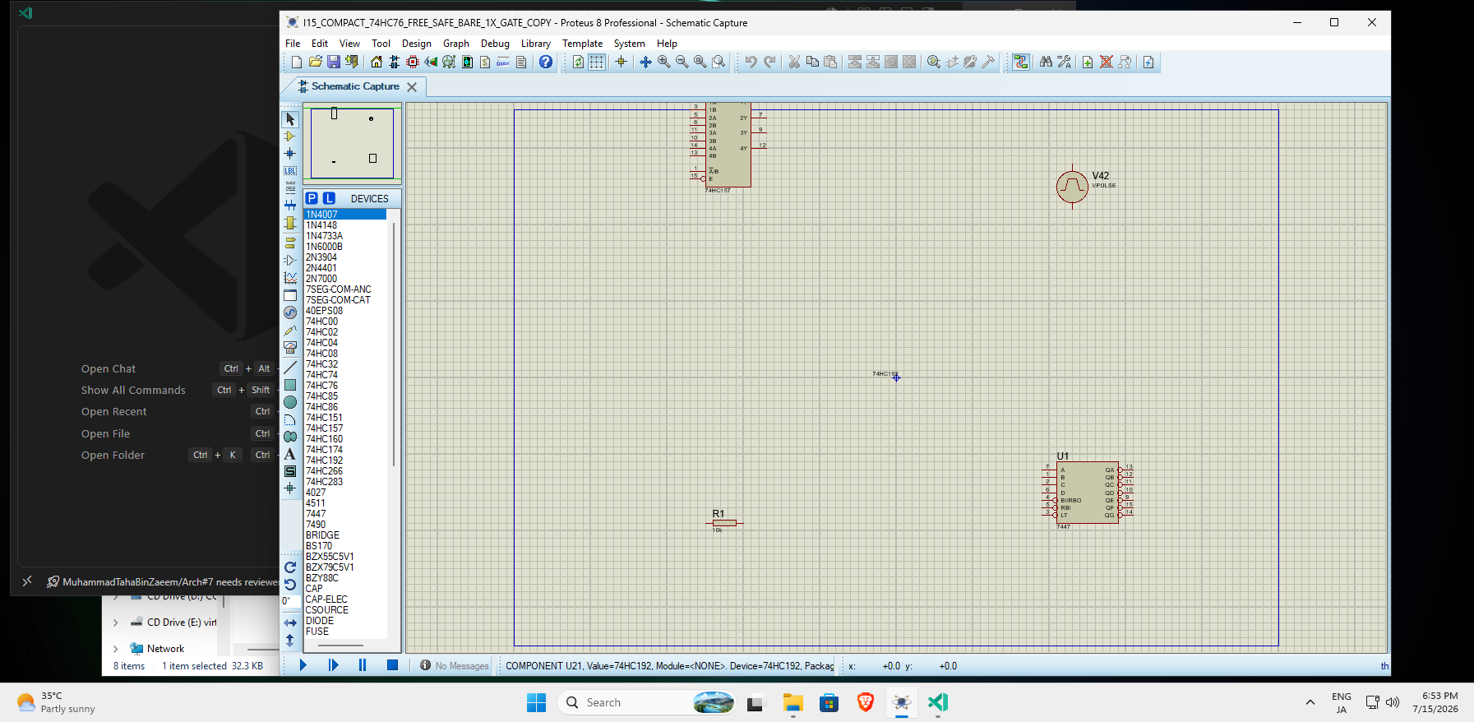
proteus/experiments/runs/totalmix_disappearing_isolation_v2_temp_2026_07_15/01_compact_74hc76_free_baseline/04_bare_proteus_gate/I15_COMPACT_74HC76_FREE_SAFE_BARE_1X_OPEN_15S.png
