ProGenEDA/ProGenEDA-DEV/proteus/experiments/runs/totalmix_disappearing_isolation_v2_temp_2026_07_15/05_native_terminalized_catalogue_bare_control/06_proteus_gate/I16_COMPACT_NATIVE_TERMINALIZED_CATALOGUE_BARE_1X_OPEN_15S.png

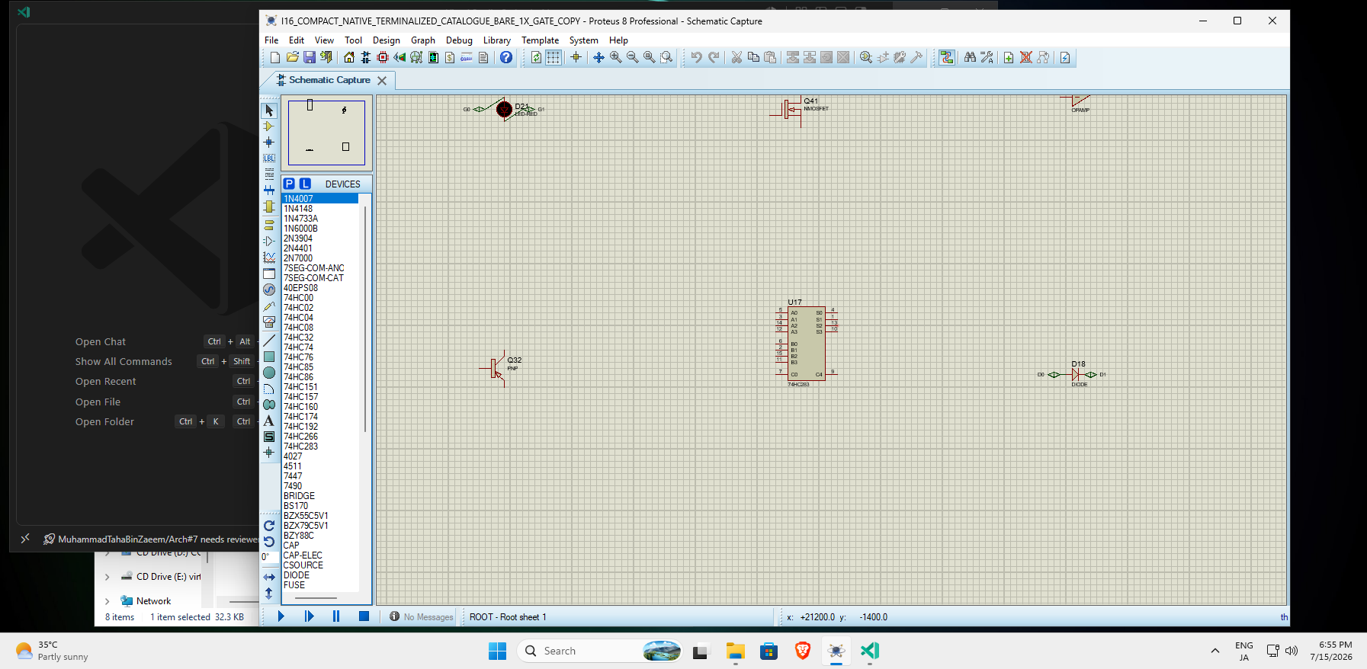
proteus/experiments/runs/totalmix_disappearing_isolation_v2_temp_2026_07_15/05_native_terminalized_catalogue_bare_control/06_proteus_gate/I16_COMPACT_NATIVE_TERMINALIZED_CATALOGUE_BARE_1X_OPEN_15S.png
