ProGenEDA/ProGenEDA-DEV/proteus/experiments/runs/totalmix_disappearing_isolation_v2_temp_2026_07_15/11_local_proteus_gate/I18_POST_CTRL_S_PROFILE_TERMINALIZED_1X_NORMAL_OPEN_15S.png

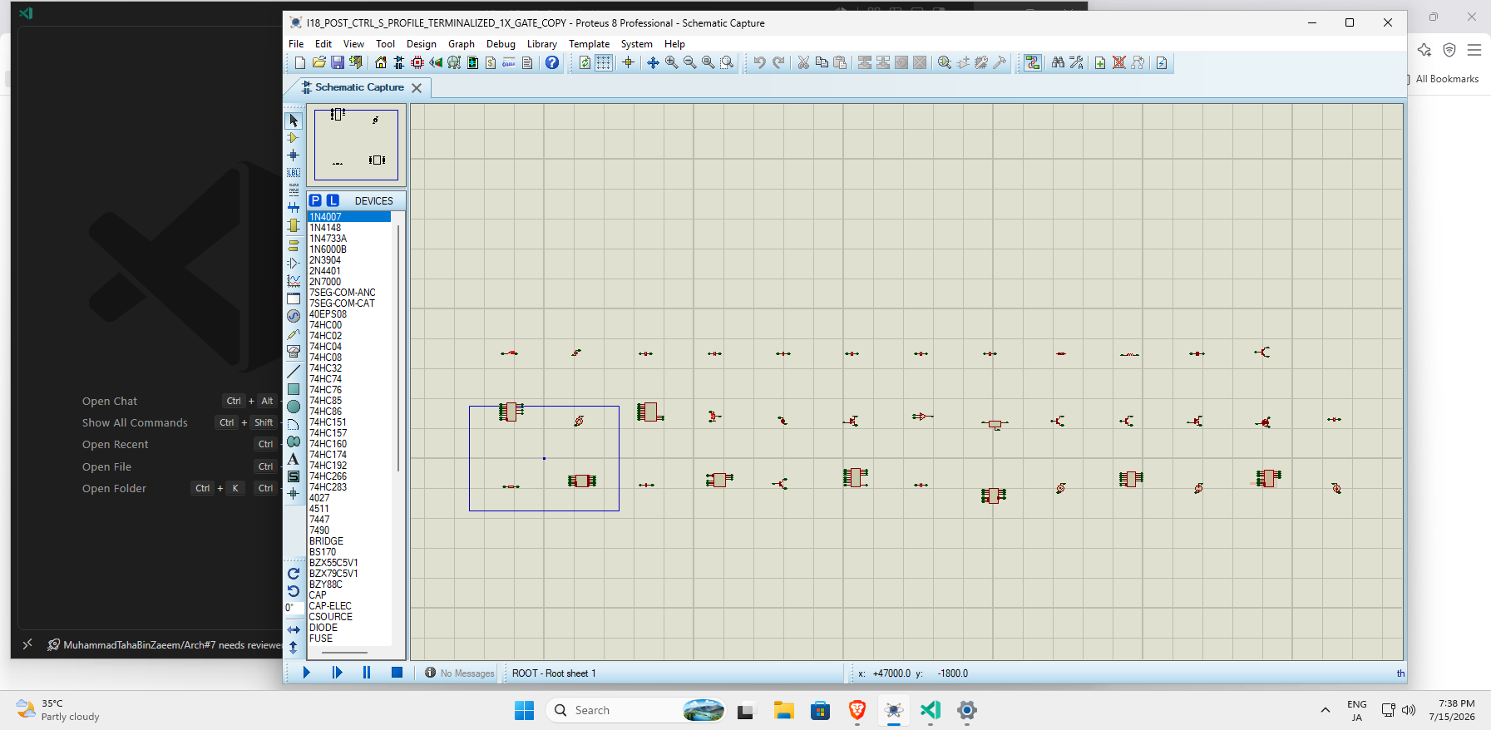
proteus/experiments/runs/totalmix_disappearing_isolation_v2_temp_2026_07_15/11_local_proteus_gate/I18_POST_CTRL_S_PROFILE_TERMINALIZED_1X_NORMAL_OPEN_15S.png
