ProGenEDA/ProGenEDA-DEV/proteus/experiments/runs/dil16_dual_jk_ff_terminal_v2_temp_2026_07_13/07_reference_width_repair/G09_4027_1X_REFERENCE_WIDTH_BEFORE_CLOSE.png

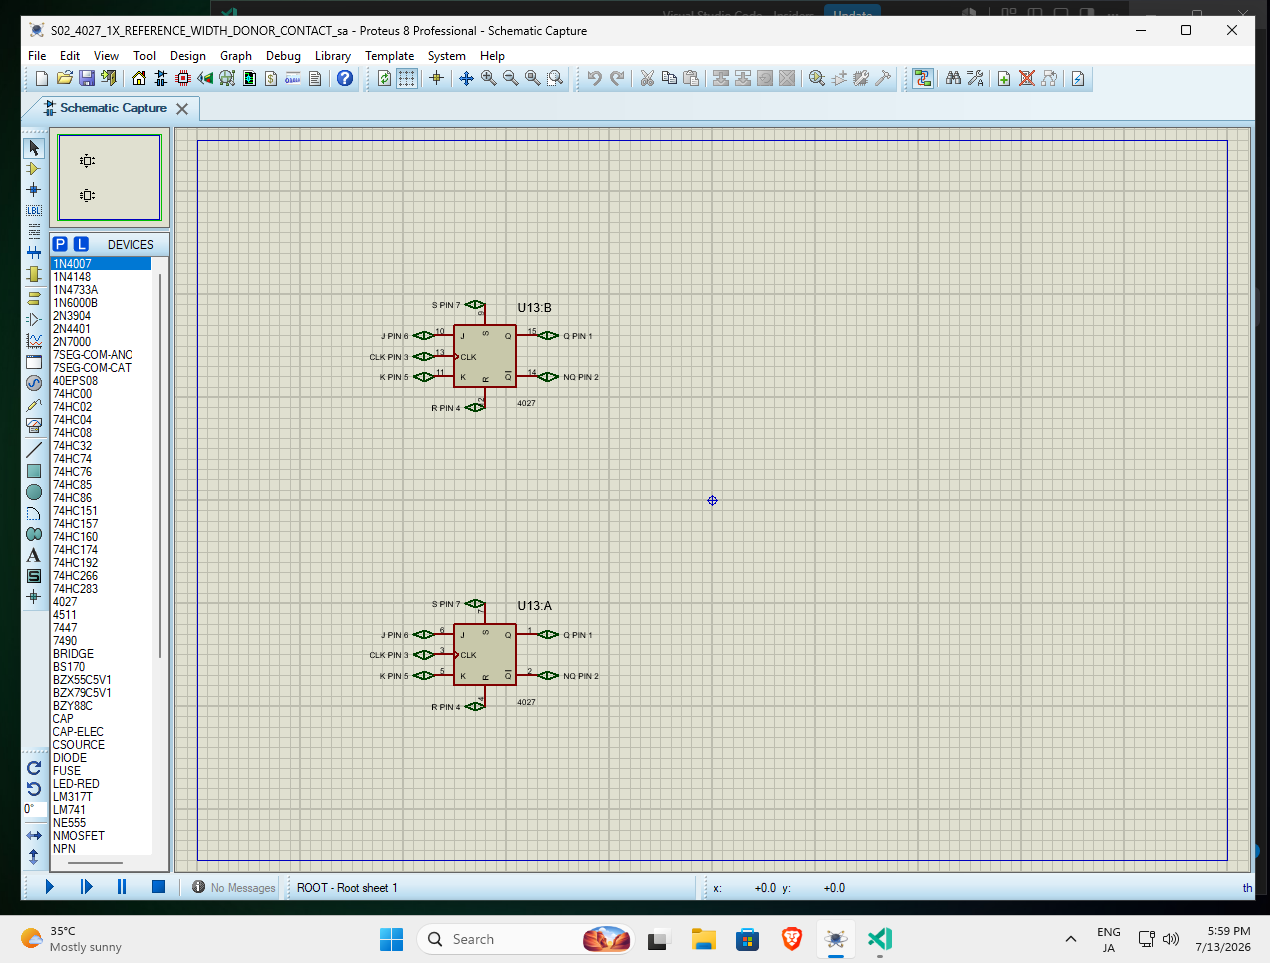
proteus/experiments/runs/dil16_dual_jk_ff_terminal_v2_temp_2026_07_13/07_reference_width_repair/G09_4027_1X_REFERENCE_WIDTH_BEFORE_CLOSE.png
