ProGenEDA/ProGenEDA-DEV/proteus/experiments/runs/mixed_all_supported_totalmix_v1_temp_2026_07_15/dsn_audit_repair_scales/03_all_49_mixed_9x_hc00_8x/local_proteus_gate/01_NORMAL_OPEN_SCREEN.png

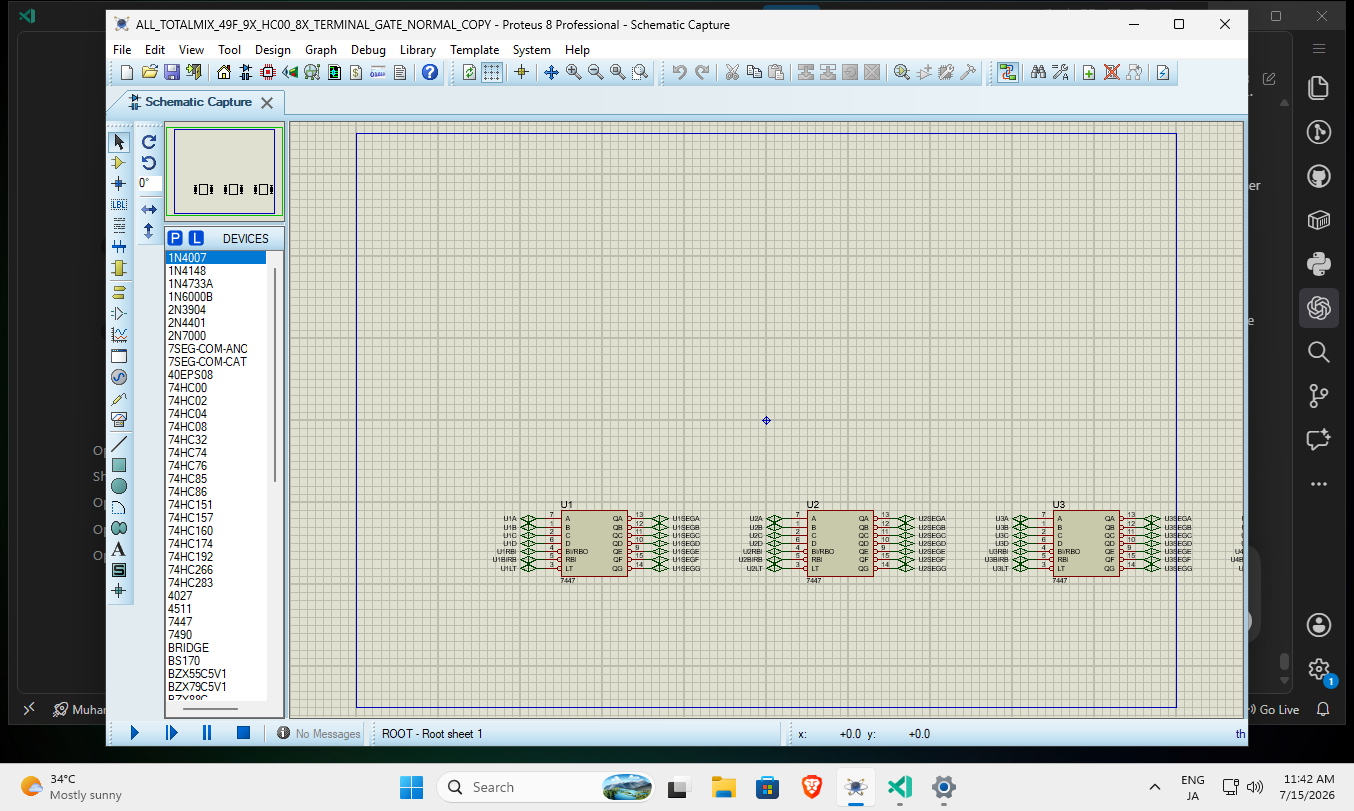
proteus/experiments/runs/mixed_all_supported_totalmix_v1_temp_2026_07_15/dsn_audit_repair_scales/03_all_49_mixed_9x_hc00_8x/local_proteus_gate/01_NORMAL_OPEN_SCREEN.png
