ProGenEDA/ProGenEDA-DEV/proteus/experiments/runs/mixed_all_supported_totalmix_v1_temp_2026_07_15/interleaved_layout_repair_1x_temp_2026_07_15/local_proteus_visual_gate/01_NORMAL_OPEN_LAYOUT.png

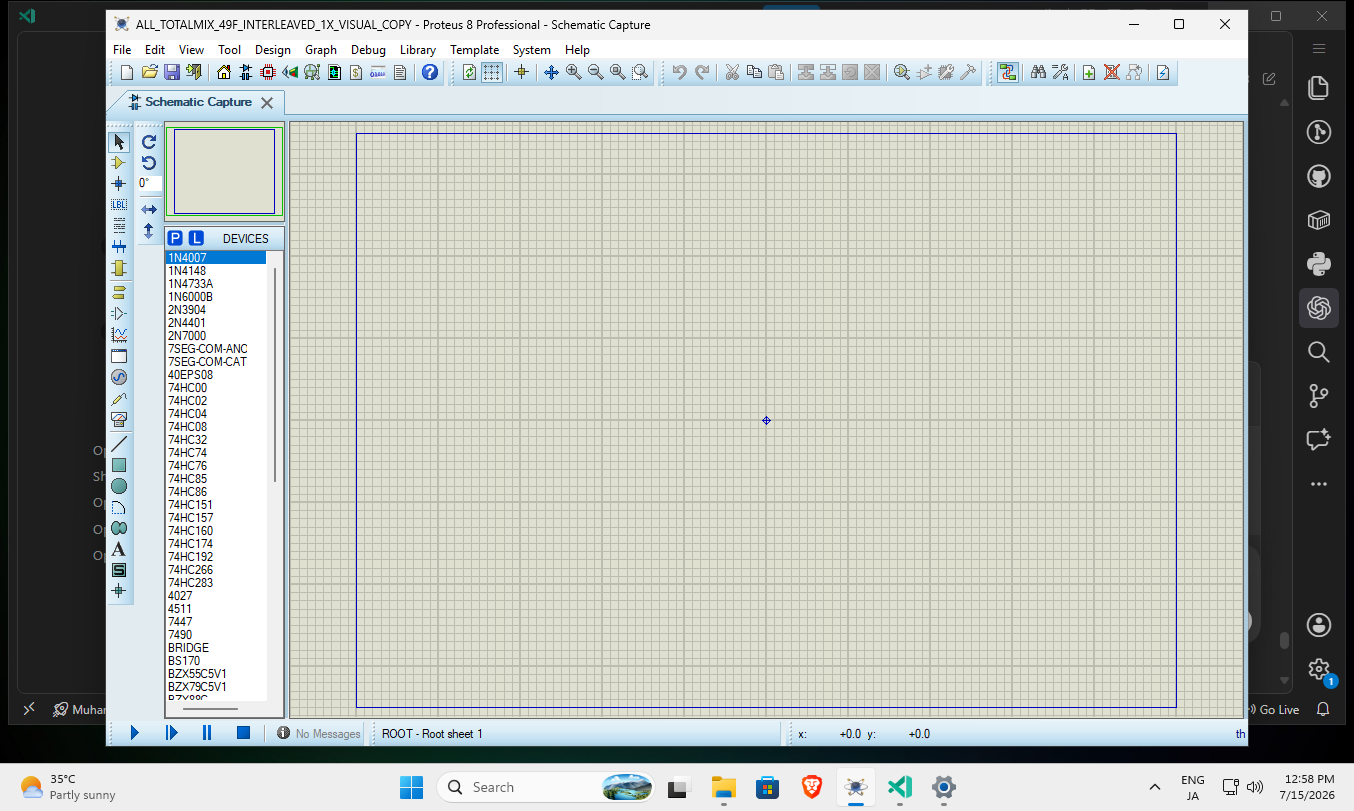
proteus/experiments/runs/mixed_all_supported_totalmix_v1_temp_2026_07_15/interleaved_layout_repair_1x_temp_2026_07_15/local_proteus_visual_gate/01_NORMAL_OPEN_LAYOUT.png
