ProGenEDA/ProGenEDA-DEV/proteus/experiments/runs/totalmix_38_growth_missing7_v1_temp_2026_07_15/07_display_cathode_45f/04_visual_layout_repair/USER_TOTALMIX_ZOOMOUT.png

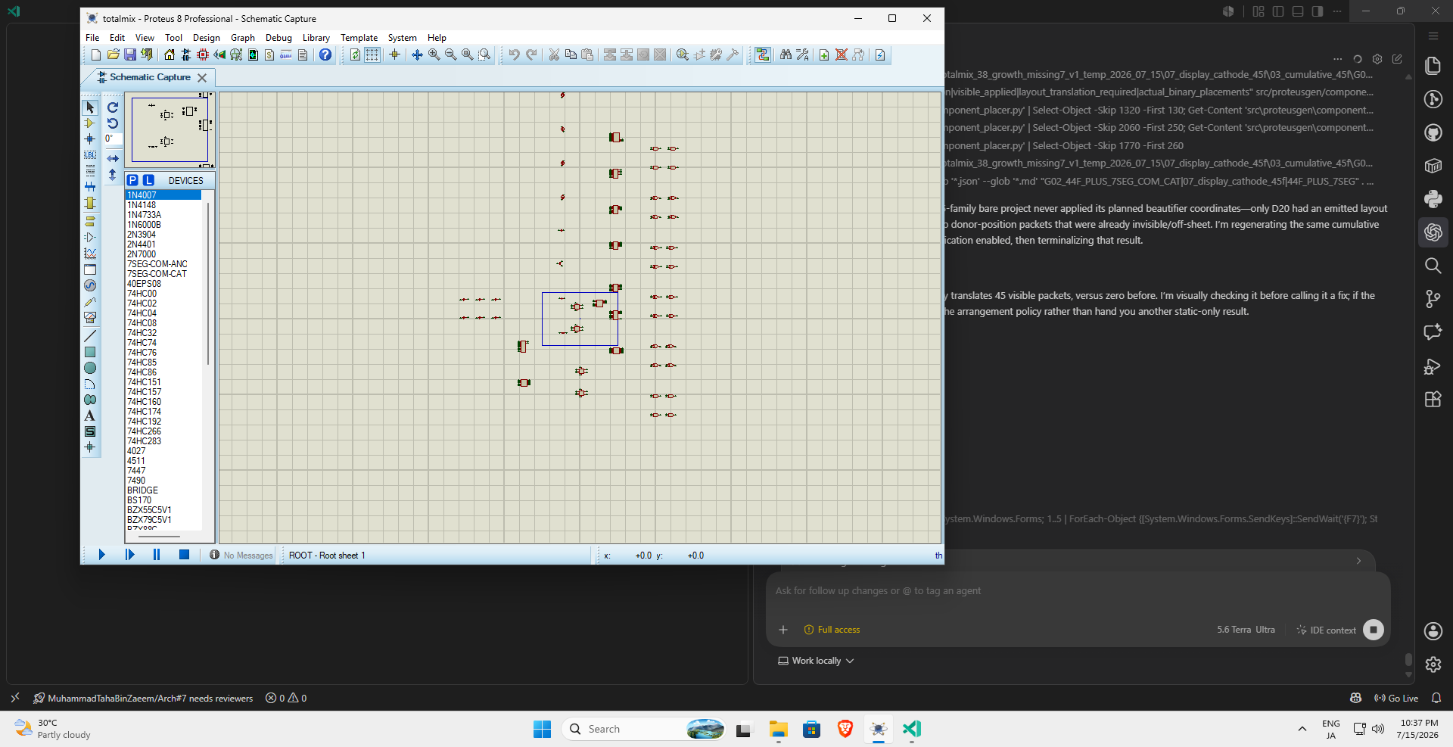
proteus/experiments/runs/totalmix_38_growth_missing7_v1_temp_2026_07_15/07_display_cathode_45f/04_visual_layout_repair/USER_TOTALMIX_ZOOMOUT.png
