ProGenEDA/ProGenEDA-DEV/proteus/experiments/runs/totalmix_38_growth_missing7_v1_temp_2026_07_15/07_display_cathode_45f/05_interleaved_slot_margin_fix/G07_CLICK_CANDIDATE_FUSE_SCREEN.png

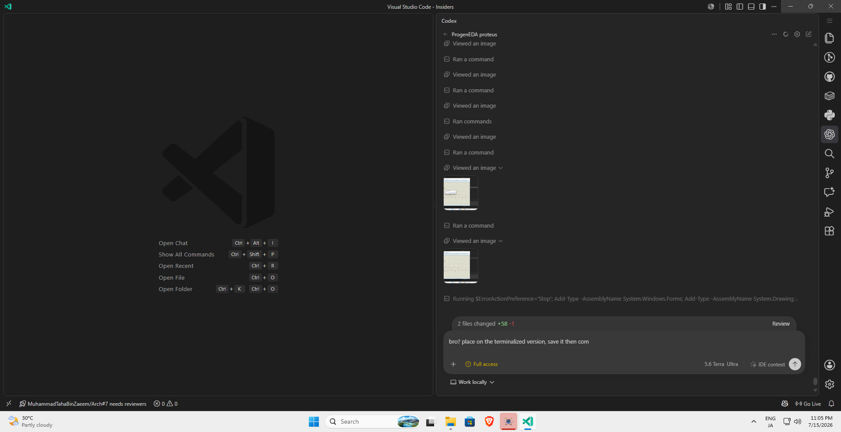
proteus/experiments/runs/totalmix_38_growth_missing7_v1_temp_2026_07_15/07_display_cathode_45f/05_interleaved_slot_margin_fix/G07_CLICK_CANDIDATE_FUSE_SCREEN.png
