ProGenEDA/ProGenEDA-DEV/proteus/experiments/runs/totalmix_38_growth_missing7_v1_temp_2026_07_15/07_display_cathode_45f/05_interleaved_slot_margin_fix/G07_LEFT_TOOLBAR_3X.png

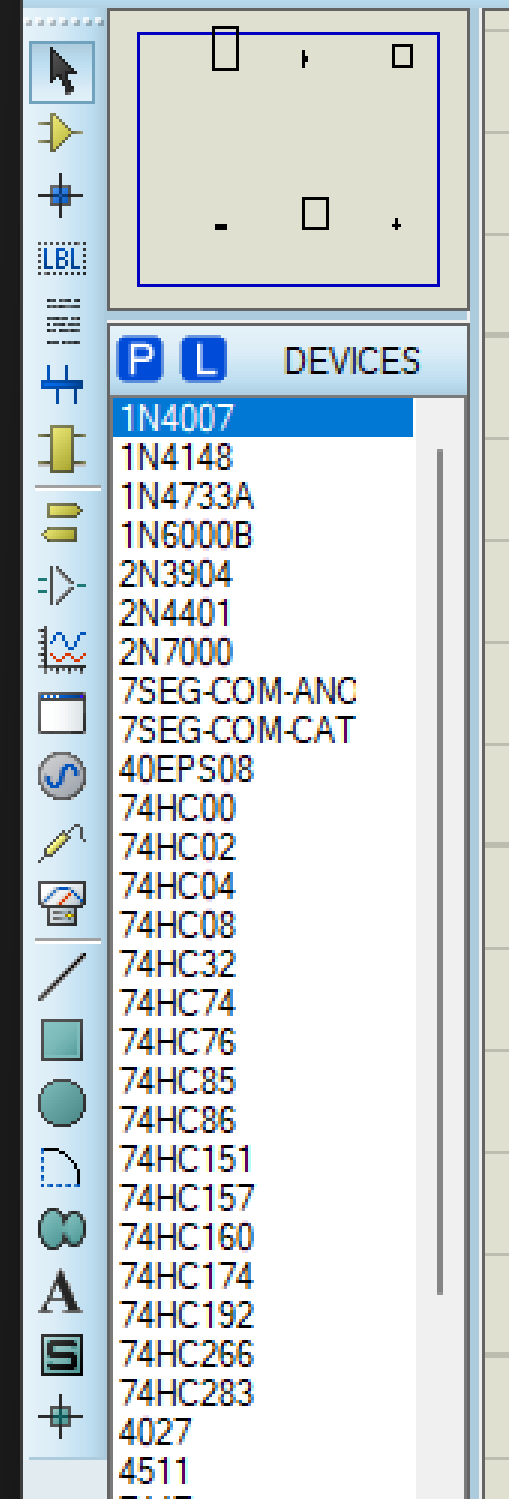
proteus/experiments/runs/totalmix_38_growth_missing7_v1_temp_2026_07_15/07_display_cathode_45f/05_interleaved_slot_margin_fix/G07_LEFT_TOOLBAR_3X.png
