ProGenEDA/ProGenEDA-DEV/proteus/experiments/runs/totalmix_38_growth_missing7_v1_temp_2026_07_15/07_display_cathode_45f/05_interleaved_slot_margin_fix/G08_45F_OPEN_REGION_3X.png

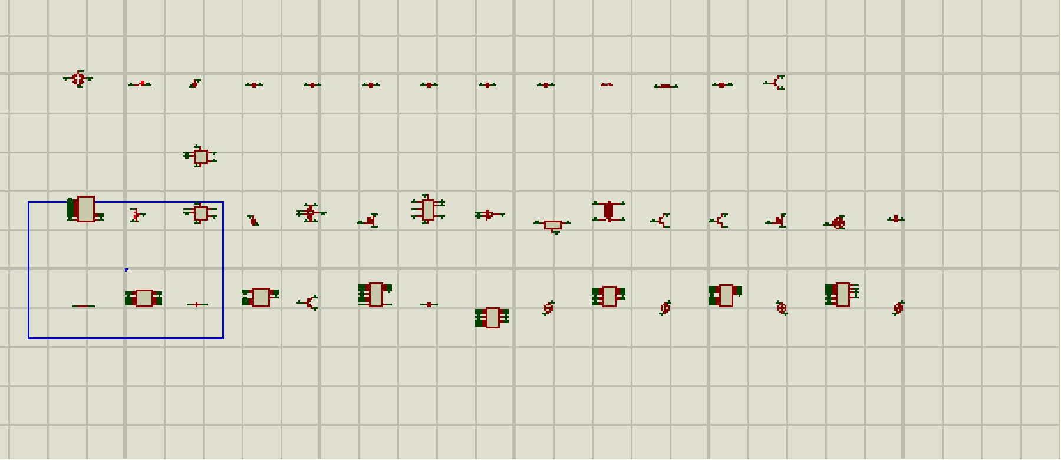
proteus/experiments/runs/totalmix_38_growth_missing7_v1_temp_2026_07_15/07_display_cathode_45f/05_interleaved_slot_margin_fix/G08_45F_OPEN_REGION_3X.png
