ProGenEDA/ProGenEDA-DEV/kicad/pipeline/kicad_wire_maker.py

"""KiCad-specific wire maker stage.

The wire planner stays EDA-agnostic and emits JSON. This module consumes that
JSON plus a KiCad placement plan and writes actual KiCad schematic wire/label
objects. It uses source-backed KiCad symbol pin geometry when the final JSON pin
names can be resolved, and records every fallback in the project manifest.
"""

from __future__ import annotations

import argparse
import datetime as dt
import json
import math
import re
import shutil
from copy import deepcopy
from dataclasses import dataclass
from pathlib import Path
from typing import Any

from kicad.generator.kicad_json_to_project import junction_obj, num, slugify, text_obj, uid, validate_schematic, wire_obj
from kicad.generator.orthogonal_router import Obstacle

from .arrangement_decider import decide_arrangement, extract_connection_nets
from .beautifier import apply_coordinate_edits
from .final_circuit_builder import STAGE_REPORT_WIRE_CONFIG, _final_json_files, placer_ready_circuit
from .kicad_symbol_library import KiCadSymbolLibrary, _balanced_block, _child_head, _direct_child_blocks
from .output_packager import package_generated_project
from .placement_catalog import CatalogPlacementPlan, PlacedCatalogComponent, resolve_placement_spec
from .placement_project_writer import MULTI_UNIT_VERTICAL_PITCH_MM, write_placement_project
from .placer_pipeline import run_placer_pipeline
from .wire_geometry_validator import AllowedTouch, ComponentBody, WireGeometrySegment, validate_wire_geometry
from .wire_planner import (
    LABEL_STRATEGIES,
    WIRE_MODE_TERMINAL_LABEL_STRATEGY,
    normalize_routing_mode,
    plan_partial_route_component_moves,
    plan_wire_routes,
    plan_wiring,
)


WIRE_MAKER_VERSION = "progen-kicad-wire-maker/v0.1"
POWER_LABEL_NETS = {"GND", "0", "VSS", "+5V", "5V", "+3V3", "3V3", "VCC", "VDD", "VIN", "VBUS"}
UNROUTED_STRATEGY_PREFIXES = ("unroutable", "deferred")
MAX_ACTUAL_PATH_CANDIDATES = 160
TERMINAL_LABEL_PIN_OFFSET_MM = 10.16
VISIBLE_TEXT_FONT_MM = 1.27
VISIBLE_TEXT_CLEARANCE_MM = 0.8
TERMINAL_LABEL_FONT_MM = 0.8
PIN_TO_FOREIGN_BODY_CLEARANCE_MM = 2.54
VARIATION_ARRANGEMENT_PROFILES: dict[str, dict[str, float]] = {
    "square_compact": {"column_gap": 0.9, "row_gap": 1.1, "component_clearance": 1.0},
    "square_loose": {"column_gap": 1.2, "row_gap": 1.2, "component_clearance": 1.25},
    "wide_bus": {"column_gap": 1.55, "row_gap": 0.95, "component_clearance": 1.15},
    "tall_bus": {"column_gap": 0.95, "row_gap": 1.55, "component_clearance": 1.15},
    "loose_channels": {"column_gap": 1.35, "row_gap": 1.7, "component_clearance": 1.45},
}


@dataclass(frozen=True)
class PinGeometry:
    unit: int
    number: str
    name: str
    x: float
    y: float
    rotation: float


@dataclass(frozen=True)
class BodyBounds:
    left: float
    top: float
    right: float
    bottom: float


@dataclass(frozen=True)
class WireMakerResult:
    schematic_objects: str
    report: dict[str, Any]


PIN_ALIAS_BY_KIND: dict[str, dict[str, tuple[str, ...]]] = {
    "LM7805": {"IN": ("VI", "1"), "OUT": ("VO", "3"), "GND": ("GND", "2")},
    "CP_100UF": {"POS": ("1",), "NEG": ("2",)},
    "OUTPUT_CAPACITOR_BUCK": {"POS": ("1",), "NEG": ("2",)},
    "INPUT_CAPACITOR_BUCK": {"POS": ("1",), "NEG": ("2",)},
    "BME280": {"VCC": ("VDD", "VDDIO", "8", "6"), "SDA": ("SDI", "3"), "SCL": ("SCK", "4")},
    "SSD1306_OLED": {"VCC": ("VCC", "VDD", "28", "9"), "SDA": ("D1", "19"), "SCL": ("D0", "18"), "GND": ("GND", "VSS", "1", "8")},
    "ESP32_WROOM": {"3V3": ("VDD", "2"), "U0RXD": ("RXD0", "IO3", "34"), "U0TXD": ("TXD0", "IO1", "35")},
    "ARDUINO_NANO": {
        "5V": ("+5V", "27"),
        "ADC1": ("A1", "20"),
        "ADC2": ("A2", "21"),
        "ADC3": ("A3", "22"),
        "ADC4": ("A4", "23"),
        "GPIO_BTN_1": ("D4", "7"),
        "GPIO_BTN_2": ("D5", "8"),
        "GPIO_BTN_3": ("D6", "9"),
        "GPIO_BTN_4": ("D7", "10"),
        "GPIO_BTN_5": ("D8", "11"),
        "GPIO_BTN_6": ("D9", "12"),
        "GPIO_PWM_1": ("D6", "9"),
        "GPIO_PWM_2": ("D7", "10"),
        "GPIO_PWM_3": ("D8", "11"),
        "GPIO_PWM_4": ("D9", "12"),
        "GPIO_RELAY_1": ("D10", "13"),
        "GPIO_RELAY_2": ("D11", "14"),
        "GPIO_RELAY_3": ("D12", "15"),
        "GPIO_RELAY_4": ("D13", "16"),
        "GPIO_CS1": ("D10", "13"),
        "GPIO_CS2": ("D9", "12"),
        "GPIO_CS_CAN": ("D8", "11"),
        "GPIO_CAN_INT": ("D7", "10"),
        "GPIO_LATCH": ("D6", "9"),
        "GPIO_RS485_RX": ("D2", "5"),
        "GPIO_RS485_TX": ("D3", "6"),
        "GPIO_RS485_DE": ("D4", "7"),
        "GPIO_EXT_1": ("A0", "19"),
        "GPIO_EXT_2": ("A1", "20"),
        "GPIO_EXT_3": ("A2", "21"),
        "GPIO_EXT_4": ("A3", "22"),
        "GPIO_EXT_5": ("A4", "23"),
        "GPIO_EXT_6": ("A5", "24"),
        "GPIO_EXT_7": ("A6", "25"),
        "GPIO_EXT_8": ("A7", "26"),
        "GPIO_MODE_1": ("D2", "5"),
        "GPIO_MODE_2": ("D3", "6"),
        "GPIO_MODE_3": ("D4", "7"),
        "GPIO_MODE_4": ("D5", "8"),
        "GPIO_MODE_5": ("D6", "9"),
        "GPIO_MODE_6": ("D7", "10"),
        "MOSI": ("D11", "14"),
        "MISO": ("D12", "15"),
        "SCK": ("D13", "16"),
        "SDA": ("A4", "23"),
        "SCL": ("A5", "24"),
        "RX0": ("D0/RX", "2"),
        "TX0": ("D1/TX", "1"),
    },
    "W25Q64": {"CS": ("CS", "1"), "DI": ("DI", "IO0", "5"), "DO": ("DO", "IO1", "2"), "WP": ("WP", "IO2", "3"), "HOLD": ("HOLD", "RESET", "IO3", "7")},
    "RELAY_5V": {"COIL_PLUS": ("A1",), "COIL_MINUS": ("A2",), "COM": ("11",), "NC": ("12",), "NO": ("14",)},
    "RELAY": {"COIL_PLUS": ("A1",), "COIL_MINUS": ("A2",), "COM": ("11",), "NC": ("12",), "NO": ("14",)},
    "COIN_CELL_HOLDER": {"POS": ("1",), "NEG": ("2",)},
    "CR2032_BATTERY": {"POS": ("1",), "NEG": ("2",)},
    "DC_BARREL_JACK": {"POS": ("1",), "NEG": ("2",)},
    "AUDIO_INPUT_JACK": {"LEFT": ("T",), "RIGHT": ("R",), "GND": ("S",)},
    "AUDIO_JACK": {"LEFT": ("T",), "RIGHT": ("R",), "GND": ("S",)},
    "PAM8403": {
        "LIN": ("INL", "7"),
        "RIN": ("INR", "10"),
        "LOUTPLUS": ("LOUT+", "1"),
        "LOUT_PLUS": ("LOUT+", "1"),
        "LOUTMINUS": ("LOUT-", "3"),
        "LOUT_MINUS": ("LOUT-", "3"),
        "ROUTPLUS": ("ROUT+", "16"),
        "ROUT_PLUS": ("ROUT+", "16"),
        "ROUTMINUS": ("ROUT-", "14"),
        "ROUT_MINUS": ("ROUT-", "14"),
        "VCC": ("VDD", "PVDD", "4", "6", "13"),
        "GND": ("GND", "PGND", "2", "11", "15"),
    },
    "74HC595_SHIFT_REGISTER": {
        "Q0": ("QA", "15"),
        "Q1": ("QB", "1"),
        "Q2": ("QC", "2"),
        "Q3": ("QD", "3"),
        "Q4": ("QE", "4"),
        "Q5": ("QF", "5"),
        "Q6": ("QG", "6"),
        "Q7": ("QH", "7"),
        "Q7S": ("QH'", "9"),
        "SHCP": ("SRCLK", "11"),
        "STCP": ("RCLK", "12"),
        "MR": ("SRCLR", "10"),
        "OE": ("OE", "13"),
    },
    "LM358": {"IN_PLUS": ("+", "3", "5"), "IN_MINUS": ("-", "2", "6"), "OUT": ("1", "7"), "VCC": ("V+", "8"), "GND": ("V-", "4")},
    "RESISTOR_NETWORK": {"COM": ("16", "common")},
    "CH340": {"DPLUS": ("UD+", "5"), "DMINUS": ("UD-", "6"), "VDD": ("VCC", "16"), "VBUS": ("VCC", "16")},
}


def _numbered_alias(prefix: str, count: int, *, start: int = 1) -> dict[str, tuple[str, ...]]:
    return {f"{prefix}{index}": (str(index + start - 1),) for index in range(1, count + 1)}


PIN_ALIAS_BY_KIND.update(
    {
        "TEST_POINT": {"TP": ("1",)},
        "VDC": {"PLUS": ("1",), "MINUS": ("2",), "+": ("1",), "-": ("2",), "POS": ("1",), "NEG": ("2",)},
        "VSOURCE": {"PLUS": ("1",), "MINUS": ("2",), "+": ("1",), "-": ("2",)},
        "PWR_5V": {"PLUS": ("1",), "+": ("1",)},
        "PWR_3V3": {"PLUS": ("1",), "+": ("1",)},
        "GROUND": {"GND": ("1",), "1": ("1",)},
        "TERMINAL_BLOCK": {"PLUS": ("1",), "MINUS": ("2",), "+": ("1",), "-": ("2",)},
        "TERMINAL_BLOCK_4": {"CANH": ("1",), "A": ("1",), "CANL": ("2",), "B": ("2",), "GND": ("3",), "SHIELD": ("4",)},
        "CAN_TERMINAL": {"CANH": ("1",), "CANL": ("2",), "GND": ("3",), "SHIELD": ("3",)},
        "RS485_TERMINAL": {"A": ("1",), "B": ("2",), "GND": ("3",), "SHIELD": ("3",)},
        "SCREW_TERMINAL_2": {"PLUS": ("1",), "MINUS": ("2",), "+": ("1",), "-": ("2",)},
        "DC_BARREL_JACK": {"CENTER": ("1",), "SLEEVE": ("2",), "POS": ("1",), "NEG": ("2",)},
        "DC_MOTOR": {"POSITIVE": ("1", "+"), "NEGATIVE": ("2", "-"), "POS": ("1", "+"), "NEG": ("2", "-")},
        "IRLZ44N": {"GATE": ("G", "1"), "DRAIN": ("D", "2"), "SOURCE": ("S", "3")},
        "MOSFET": {"GATE": ("G", "1"), "DRAIN": ("D", "2"), "SOURCE": ("S", "3")},
        "NMOS": {"GATE": ("G", "1"), "DRAIN": ("D", "2"), "SOURCE": ("S", "3")},
        "2N7000": {"GATE": ("G", "1"), "DRAIN": ("D", "2"), "SOURCE": ("S", "3")},
        "BS170": {"GATE": ("G", "1"), "DRAIN": ("D", "2"), "SOURCE": ("S", "3")},
        "BC547": {"COLLECTOR": ("C", "1"), "BASE": ("B", "2"), "EMITTER": ("E", "3")},
        "NPN": {"COLLECTOR": ("C", "1"), "BASE": ("B", "2"), "EMITTER": ("E", "3")},
        "PNP": {"COLLECTOR": ("C", "1"), "BASE": ("B", "2"), "EMITTER": ("E", "3")},
        "POTENTIOMETER": {"END_A": ("1",), "WIPER": ("2",), "END_B": ("3",)},
        "POT_HG": {"END_A": ("1",), "WIPER": ("2",), "END_B": ("3",)},
        "VOLUME_POTENTIOMETER": {"END_A": ("1",), "WIPER": ("2",), "END_B": ("3",)},
        "TRIMMER_POTENTIOMETER": {"END_A": ("1",), "WIPER": ("2",), "END_B": ("3",)},
        "AUDIO_INPUT_JACK": {"TIP": ("T", "1"), "RING": ("R", "2"), "SLEEVE": ("S", "3"), "LEFT": ("T", "1"), "RIGHT": ("R", "2"), "GND": ("S", "3")},
        "AUDIO_JACK": {"TIP": ("T", "1"), "RING": ("R", "2"), "SLEEVE": ("S", "3"), "LEFT": ("T", "1"), "RIGHT": ("R", "2"), "GND": ("S", "3")},
        "SPEAKER": {"POSITIVE": ("1", "+"), "NEGATIVE": ("2", "-"), "POS": ("1", "+"), "NEG": ("2", "-")},
        "LM317": {"IN": ("VI", "I", "3"), "OUT": ("VO", "O", "2"), "ADJ": ("ADJ", "1")},
        "NE555": {"GND": ("1",), "TRIG": ("2",), "OUT": ("3", "Q"), "RESET": ("4", "R"), "CTRL": ("5", "CV"), "THRESH": ("6", "THR"), "DISCH": ("7", "DIS"), "VCC": ("8", "VCC")},
        "LM393_COMPARATOR": {
            "OUT1": ("1",),
            "IN1-": ("2",),
            "IN1+": ("3",),
            "GND": ("4", "V-"),
            "IN2+": ("5",),
            "IN2-": ("6",),
            "OUT2": ("7",),
            "VCC": ("8", "V+"),
        },
        "LM358": {
            "OUT1": ("1",),
            "IN1-": ("2",),
            "IN1+": ("3",),
            "GND": ("4", "V-"),
            "IN2+": ("5",),
            "IN2-": ("6",),
            "OUT2": ("7",),
            "VCC": ("8", "V+"),
            "IN_PLUS": ("+", "3", "5"),
            "IN_MINUS": ("-", "2", "6"),
            "OUT": ("1", "7"),
        },
        "LEVEL_SHIFTER": {
            "LV": ("VCCA", "1"),
            "HV": ("VCCB", "20"),
            "GND": ("GND", "10"),
            "OE": ("OE",),
            **{f"L{index}": (f"A{index}",) for index in range(1, 9)},
            **{f"H{index}": (f"B{index}",) for index in range(1, 9)},
        },
        "MICRO_SD_SOCKET": {"VCC": ("VDD", "4"), "GND": ("VSS", "6"), "SCK": ("CLK", "5"), "MOSI": ("CMD", "3"), "MISO": ("DAT0", "7"), "CS": ("DAT3", "2"), "CD": ("DET", "9")},
        "I2C_HEADER": {"VCC": ("1",), "GND": ("2",), "SDA": ("3",), "SCL": ("4",)},
        "UART_HEADER": {"VCC": ("1",), "GND": ("2",), "RX": ("3",), "TX": ("4",), "RTS": ("5",), "CTS": ("5",)},
        "PWM_HEADER": {"VCC": ("1",), "GND": ("2",), "PWM1": ("3",), "PWM2": ("4",), "PWM3": ("5",), "PWM4": ("6",), "PWM5": ("7",)},
        "SPI_HEADER_FLASH": {"VCC": ("1",), "GND": ("2",), "SCK": ("3",), "MOSI": ("4",), "MISO": ("5",), "CS": ("6",)},
        "SPI_HEADER_SD": {"VCC": ("1",), "GND": ("2",), "SCK": ("3",), "MOSI": ("4",), "MISO": ("5",), "CS": ("6",)},
        "PROGRAMMING_HEADER": {
            **_numbered_alias("P", 14),
            "VCC": ("1",),
            "GND": ("2",),
            "RX": ("3",),
            "TX": ("4",),
            "RTS": ("5",),
            "CTS": ("6",),
            "PWM1": ("3",),
            "PWM2": ("4",),
            "PWM3": ("5",),
            "PWM4": ("6",),
            "PWM5": ("7",),
        },
        "PIN_HEADER": {**_numbered_alias("P", 14), "VCC": ("1",), "GND": ("2",), "RX": ("3",), "TX": ("4",)},
        "RX_HEADER": {"RX": ("1",)},
        "TX_HEADER": {"TX": ("1",)},
        "DIP_SWITCH": {f"S{index}{side}": (str((index - 1) * 2 + (1 if side == "A" else 2)),) for index in range(1, 9) for side in ("A", "B")},
        "LED_ARRAY": {
            **{f"LED{index}_ANODE": (str((index - 1) * 2 + 1),) for index in range(1, 9)},
            **{f"LED{index}_CATHODE": (str((index - 1) * 2 + 2),) for index in range(1, 9)},
            **{f"A{index}": (str(index + 1),) for index in range(0, 8)},
            **{f"K{index}": (str(index + 9),) for index in range(0, 8)},
            "COM_K": ("16",),
            "COM_A": ("1",),
        },
        "RESISTOR_NETWORK": {
            **{f"R{index}": (str((index - 1) * 2 + 1),) for index in range(1, 9)},
            **{f"C{index}": (str((index - 1) * 2 + 2),) for index in range(1, 9)},
            "COM": ("16",),
        },
        "4511": {"VCC": ("16", "VDD"), "GND": ("8", "VSS"), "A": ("7",), "B": ("1",), "C": ("2",), "D": ("6",), "LE": ("5",), "LT": ("3",), "BI": ("4",), "a": ("13",), "b": ("12",), "c": ("11",), "d": ("10",), "e": ("9",), "f": ("15",), "g": ("14",), "/LT": ("3",), "/BI": ("4",)},
        "7SEGCOMK": {"A": ("7",), "B": ("6",), "C": ("4",), "D": ("2",), "E": ("1",), "F": ("9",), "G": ("10",), "DP": ("5",), "COM1": ("3",), "COM2": ("8",)},
        "7SEGCOMA": {"A": ("7",), "B": ("6",), "C": ("4",), "D": ("2",), "E": ("1",), "F": ("9",), "G": ("10",), "DP": ("5",), "COM1": ("3",), "COM2": ("8",)},
        "74HC151": {"VCC": ("16",), "GND": ("8",), "D0": ("4",), "D1": ("3",), "D2": ("2",), "D3": ("1",), "D4": ("15",), "D5": ("14",), "D6": ("13",), "D7": ("12",), "A": ("11", "S0"), "B": ("10", "S1"), "C": ("9", "S2"), "/E": ("7", "E"), "Y": ("5",), "/Y": ("6",)},
        "74HC157": {"VCC": ("16",), "GND": ("8",), "/OE": ("15",), "SELECT": ("1",), "1A": ("2",), "1B": ("3",), "1Y": ("4",), "2A": ("5",), "2B": ("6",), "2Y": ("7",), "3Y": ("9",), "3B": ("10",), "3A": ("11",), "4Y": ("12",), "4B": ("13",), "4A": ("14",)},
        "74HC192": {"VCC": ("16",), "GND": ("8",), "A": ("15",), "B": ("1",), "C": ("10",), "D": ("9",), "QA": ("3",), "QB": ("2",), "QC": ("6",), "QD": ("7",), "UP_CLK": ("5",), "DOWN_CLK": ("4",), "/LOAD": ("11",), "CLR": ("14",), "CARRY": ("12",), "BORROW": ("13",)},
        "74HC283": {"VCC": ("16",), "GND": ("8",), "A1": ("5",), "B1": ("6",), "S1": ("4",), "A2": ("3",), "B2": ("2",), "S2": ("1",), "A3": ("14",), "B3": ("15",), "S3": ("13",), "A4": ("12",), "B4": ("11",), "S4": ("10",), "C0": ("7",), "C4": ("9",)},
        "74HC85": {"VCC": ("16",), "GND": ("8",), "A0": ("10",), "A1": ("12",), "A2": ("13",), "A3": ("15",), "B0": ("9",), "B1": ("11",), "B2": ("14",), "B3": ("1",), "I_A_LT_B": ("2",), "I_A_EQ_B": ("3",), "I_A_GT_B": ("4",), "O_A_GT_B": ("5",), "O_A_EQ_B": ("6",), "O_A_LT_B": ("7",)},
        "74HC174": {"VCC": ("16",), "GND": ("8",), "/CLR": ("1",), "CLK": ("9",), "D1": ("3",), "D2": ("4",), "D3": ("6",), "D4": ("11",), "D5": ("13",), "D6": ("14",), "Q1": ("2",), "Q2": ("5",), "Q3": ("7",), "Q4": ("10",), "Q5": ("12",), "Q6": ("15",)},
        "MCP2515": {"VCC": ("VDD", "18"), "GND": ("VSS", "9"), "TXCAN": ("TXCAN", "1"), "RXCAN": ("RXCAN", "2"), "SCK": ("SCK", "13"), "SI": ("SI", "14"), "SO": ("SO", "15"), "CS": ("CS", "16"), "RESET": ("RESET", "17"), "INT": ("INT", "12")},
        "TJA1050": {"VCC": ("VCC", "3"), "GND": ("GND", "2"), "TXD": ("D", "1"), "RXD": ("R", "4"), "CANL": ("CANL", "6"), "CANH": ("CANH", "7"), "RS": ("RS", "8")},
        "ACS712": {"VCC": ("VCC", "8"), "GND": ("GND", "5"), "OUT": ("VIOUT", "7"), "IP+": ("IP+", "1"), "IP-": ("IP-", "4")},
        "DS3231": {"VCC": ("VCC", "2"), "GND": ("GND", "13"), "SDA": ("SDA", "15"), "SCL": ("SCL", "16"), "SQW": ("~INT/SQW", "3"), "32K": ("32kHz", "1"), "BAT": ("VBAT", "14")},
        "LM2596": {"VIN": ("VIN", "1"), "SW": ("OUT", "2"), "GND": ("GND", "3"), "FB": ("FB", "4"), "EN": ("ON/OFF", "5")},
        "TP4056": {"IN+": ("VCC", "4"), "IN-": ("GND", "3"), "B+": ("BAT", "5"), "B-": ("GND", "3"), "OUT+": ("BAT", "5"), "OUT-": ("GND", "3"), "CHRG": ("~CHRG", "7")},
        "LI_ION_BATTERY_CONNECTOR": {"+": ("1",), "-": ("2",), "PLUS": ("1",), "MINUS": ("2",)},
        "BRIDGE_RECTIFIER": {"AC1": ("3", "~"), "AC2": ("4", "~"), "+": ("1",), "-": ("2",), "PLUS": ("1",), "MINUS": ("2",)},
        "4027": {"VDD": ("16",), "VSS": ("8",), "J1": ("6",), "K1": ("5",), "CLK1": ("3",), "SET1": ("7",), "RESET1": ("4",), "Q1": ("1",), "/Q1": ("2",), "J2": ("10",), "K2": ("11",), "CLK2": ("13",), "SET2": ("9",), "RESET2": ("12",), "Q2": ("15",), "/Q2": ("14",)},
        "74HC76": {"VCC": ("5",), "GND": ("13",), "1J": ("4",), "1K": ("16",), "1CLK": ("1",), "1/PRE": ("2",), "1/CLR": ("3",), "1Q": ("15",), "1/Q": ("14",), "2J": ("12",), "2K": ("9",), "2CLK": ("6",), "2/PRE": ("7",), "2/CLR": ("8",), "2Q": ("11",), "2/Q": ("10",)},
    }
)

for _kind in ("LED_INDICATOR", "POWER_LED", "RELAY_INDICATOR_LED", "CHARGING_LED", "LED"):
    PIN_ALIAS_BY_KIND.setdefault(_kind, {}).update({"ANODE": ("A", "2"), "CATHODE": ("K", "1")})

for _kind in ("DIODE", "D_1N4007", "1N4007", "1N4148", "1N60", "BZX55C5", "BZX79C5", "FLYBACK_DIODE", "RELAY_FLYBACK_DIODE", "SCHOTTKY_DIODE_BUCK", "TVS_DIODE_RS485"):
    PIN_ALIAS_BY_KIND.setdefault(_kind, {}).update({"ANODE": ("A", "1"), "CATHODE": ("K", "2"), "A": ("A", "1"), "K": ("K", "2")})

PIN_ALIAS_BY_KIND.setdefault("SCHOTTKY", {}).update({"ANODE": ("A", "1"), "CATHODE": ("K", "2"), "A": ("A", "1"), "K": ("K", "2")})

for _kind in ("VDC", "VSOURCE", "CSOURCE", "VSIN", "VPULSE", "VAC", "IDC"):
    PIN_ALIAS_BY_KIND.setdefault(_kind, {}).update(
        {"PLUS": ("1",), "MINUS": ("2",), "+": ("1",), "-": ("2",), "POS": ("1",), "NEG": ("2",)}
    )

for _kind in ("OPAMP", "LM741"):
    PIN_ALIAS_BY_KIND.setdefault(_kind, {}).update(
        {"IN+": ("3",), "IN_PLUS": ("3",), "+": ("3",), "IN-": ("2",), "IN_MINUS": ("2",), "-": ("2",), "OUT": ("6",), "VCC": ("7", "V+"), "GND": ("4", "V-")}
    )

PIN_ALIAS_BY_KIND.setdefault("PROTECTION_IC", {}).update({"B+": ("5", "VCC"), "B-": ("6", "GND"), "P+": ("3", "OC"), "P-": ("1", "OD")})
PIN_ALIAS_BY_KIND.setdefault("JST_CONNECTOR", {}).update({"+": ("1",), "PLUS": ("1",), "-": ("2",), "MINUS": ("2",), "VCC": ("1",), "GND": ("2",)})
PIN_ALIAS_BY_KIND.setdefault("PWM_HEADER", {}).update({"PWM": ("3",), "SIG": ("3",), "SIGNAL": ("3",)})
PIN_ALIAS_BY_KIND.setdefault("PROGRAMMING_HEADER", {}).update({"3V3": ("1",), "EN": ("5",), "BOOT": ("6",)})
PIN_ALIAS_BY_KIND.setdefault("HEADER_CONNECTOR", {}).update({**_numbered_alias("P", 14), "3V3": ("1",), "VCC": ("1",), "GND": ("2",)})
PIN_ALIAS_BY_KIND.setdefault("ARDUINO_NANO", {}).update({"GND": ("GND", "4", "29"), "GND1": ("4",), "GND2": ("29",), "VIN": ("30",)})
PIN_ALIAS_BY_KIND.setdefault("LM317", {}).update({"GND": ("ADJ", "1")})
PIN_ALIAS_BY_KIND.setdefault("7447", {}).update(
    {
        "VCC": ("16",),
        "GND": ("8",),
        "A": ("7",),
        "B": ("1",),
        "C": ("2",),
        "D": ("6",),
        "a": ("13", "~{a}"),
        "b": ("12", "~{b}"),
        "c": ("11", "~{c}"),
        "d": ("10", "~{d}"),
        "e": ("9", "~{e}"),
        "f": ("15", "~{f}"),
        "g": ("14", "~{g}"),
        "/BI_RBO": ("4",),
        "BI_RBO": ("4",),
        "RBI": ("5",),
        "LT": ("3",),
        "/LT": ("3",),
        "/BI": ("4",),
    }
)
PIN_ALIAS_BY_KIND.setdefault("7490", {}).update({"VCC": ("5",), "GND": ("10",), "CP0": ("14",), "CP1": ("1",), "CLK0": ("14",), "CLK1": ("1",)})
PIN_ALIAS_BY_KIND.setdefault("74HC160", {}).update(
    {"VCC": ("16",), "GND": ("8",), "ENP": ("7",), "ENT": ("10",), "LOAD": ("9",), "/LOAD": ("9",), "CLK": ("2",), "CLR": ("1",), "/CLR": ("1",), "RCO": ("15",)}
)
PIN_ALIAS_BY_KIND.setdefault("74HC74", {}).update(
    {
        "VCC": ("14",),
        "GND": ("7",),
        "1/PRE": ("4",),
        "1PRE": ("4",),
        "1CLK": ("3",),
        "1D": ("2",),
        "1/CLR": ("1",),
        "1CLR": ("1",),
        "1Q": ("5",),
        "1/Q": ("6",),
        "1NQ": ("6",),
        "2/PRE": ("10",),
        "2PRE": ("10",),
        "2CLK": ("11",),
        "2D": ("12",),
        "2/CLR": ("13",),
        "2CLR": ("13",),
        "2Q": ("9",),
        "2/Q": ("8",),
        "2NQ": ("8",),
    }
)

for _kind in ("74HC00", "74HC02", "74HC08", "74HC32", "74HC86", "74HC266"):
    PIN_ALIAS_BY_KIND.setdefault(_kind, {}).update(
        {
            "VCC": ("14",),
            "GND": ("7",),
            "1A": ("1",),
            "1B": ("2",),
            "1Y": ("3",),
            "2A": ("4",),
            "2B": ("5",),
            "2Y": ("6",),
            "3Y": ("8",),
            "3A": ("9",),
            "3B": ("10",),
            "4Y": ("11",),
            "4A": ("12",),
            "4B": ("13",),
        }
    )

PIN_ALIAS_BY_KIND.setdefault("74HC04", {}).update(
    {
        "VCC": ("14",),
        "GND": ("7",),
        "1A": ("1",),
        "1Y": ("2",),
        "2A": ("3",),
        "2Y": ("4",),
        "3A": ("5",),
        "3Y": ("6",),
        "4Y": ("8",),
        "4A": ("9",),
        "5Y": ("10",),
        "5A": ("11",),
        "6Y": ("12",),
        "6A": ("13",),
    }
)

PIN_ALIAS_BY_KIND.setdefault("ARDUINO_NANO", {}).update(
    {
        "RST": ("RESET", "28"),
        "D0_RX": ("D0/RX", "D0", "2"),
        "D1_TX": ("D1/TX", "D1", "1"),
        "D2": ("D2", "5"),
        "D3": ("D3", "6"),
        "D3_PWM": ("D3", "6"),
        "D4": ("D4", "7"),
        "D5": ("D5", "8"),
        "D5_PWM": ("D5", "8"),
        "D6": ("D6", "9"),
        "D6_PWM": ("D6", "9"),
        "D7": ("D7", "10"),
        "D8": ("D8", "11"),
        "D9": ("D9", "12"),
        "D9_PWM": ("D9", "12"),
        "D10": ("D10", "13"),
        "D10_CS": ("D10", "13"),
        "D11": ("D11", "14"),
        "D11_MOSI": ("D11", "14"),
        "D12": ("D12", "15"),
        "D12_MISO": ("D12", "15"),
        "D13": ("D13", "16"),
        "D13_SCK": ("D13", "16"),
        "A0": ("A0", "19"),
        "A1": ("A1", "20"),
        "A2": ("A2", "21"),
        "A3": ("A3", "22"),
        "A4_SDA": ("A4", "23"),
        "A5_SCL": ("A5", "24"),
        "A6": ("A6", "25"),
        "A7": ("A7", "26"),
    }
)

PIN_ALIAS_BY_KIND.setdefault("CP2102", {}).update({"VIO": ("VDD", "6")})
PIN_ALIAS_BY_KIND.setdefault("W25Q64", {}).update({"CLK": ("CLK", "SCK", "6"), "/HOLD_IO3": ("HOLD", "IO3", "7"), "/WP_IO2": ("WP", "IO2", "3")})
PIN_ALIAS_BY_KIND.setdefault("SSD1306_OLED", {}).update({"RESET": ("RES", "14")})
PIN_ALIAS_BY_KIND.setdefault("74HC595_SHIFT_REGISTER", {}).update({"SER": ("SER", "DS", "14"), "DS": ("SER", "14"), "VCC": ("VCC", "16"), "GND": ("GND", "8")})

PIN_ALIAS_BY_KIND.setdefault("ESP32_WROOM", {}).update(
    {
        **{f"GPIO{index}": (f"IO{index}",) for index in range(0, 40)},
        "GPIO0_BOOT": ("IO0",),
        "GPIO1_TX0": ("TXD0", "IO1"),
        "GPIO3_RX0": ("RXD0", "IO3"),
        "GPIO34": ("IO34",),
        "GPIO35": ("IO35",),
        "GPIO36": ("SENSOR_VP", "IO36"),
        "GPIO39": ("SENSOR_VN", "IO39"),
    }
)


def _norm_pin(value: str) -> str:
    text = str(value).upper()
    text = text.replace("+", "PLUS").replace("-", "MINUS").replace("'", "PRIME")
    text = text.replace("~", "")
    text = re.sub(r"\{|\}", "", text)
    return re.sub(r"[^A-Z0-9]+", "", text)


def _parse_pin_block(block: str, unit: int) -> PinGeometry | None:
    number = re.search(r'\(number\s+"([^"]*)"', block)
    at = re.search(r"\(at\s+([-0-9.]+)\s+([-0-9.]+)\s+([-0-9.]+)", block)
    if not number or not at:
        return None
    name = re.search(r'\(name\s+"([^"]*)"', block)
    return PinGeometry(
        unit=unit,
        number=number.group(1),
        name=name.group(1) if name else "",
        x=float(at.group(1)),
        y=float(at.group(2)),
        rotation=float(at.group(3)),
    )


def _pin_blocks(block: str) -> list[str]:
    pins: list[str] = []
    start = 0
    while True:
        index = block.find("(pin ", start)
        if index < 0:
            return pins
        pin_block = _balanced_block(block, index)
        if pin_block is None:
            start = index + 5
            continue
        pins.append(pin_block)
        start = index + len(pin_block)


def _pin_geometries(symbol_text: str) -> tuple[PinGeometry, ...]:
    geometries: list[PinGeometry] = []
    for child in _direct_child_blocks(symbol_text):
        if _child_head(child) != "symbol":
            continue
        match = re.match(r'\s*\(symbol\s+"[^"]+_(\d+)_[^"]+"', child)
        if not match:
            continue
        unit = int(match.group(1))
        for pin_block in _pin_blocks(child):
            geometry = _parse_pin_block(pin_block, unit)
            if geometry:
                geometries.append(geometry)
    if geometries:
        return tuple(geometries)
    return tuple(geometry for pin_block in _pin_blocks(symbol_text) if (geometry := _parse_pin_block(pin_block, 1)))


def _merge_bounds(left: BodyBounds | None, right: BodyBounds | None) -> BodyBounds | None:
    if left is None:
        return right
    if right is None:
        return left
    return BodyBounds(
        min(left.left, right.left),
        min(left.top, right.top),
        max(left.right, right.right),
        max(left.bottom, right.bottom),
    )


def _bounds_from_points(points: list[tuple[float, float]]) -> BodyBounds | None:
    if not points:
        return None
    xs = [point[0] for point in points]
    ys = [point[1] for point in points]
    return BodyBounds(min(xs), min(ys), max(xs), max(ys))


def _shape_bounds(block: str) -> BodyBounds | None:
    points: list[tuple[float, float]] = []
    head = _child_head(block)
    if head == "circle":
        center = re.search(r"\(center\s+([-0-9.]+)\s+([-0-9.]+)", block)
        radius = re.search(r"\(radius\s+([-0-9.]+)", block)
        if center and radius:
            cx = float(center.group(1))
            cy = float(center.group(2))
            r = float(radius.group(1))
            points.extend([(cx - r, cy - r), (cx + r, cy + r)])
    elif head in {"rectangle", "arc"}:
        for match in re.finditer(r"\((?:start|mid|end)\s+([-0-9.]+)\s+([-0-9.]+)", block):
            points.append((float(match.group(1)), float(match.group(2))))
    elif head in {"polyline", "bezier"}:
        for match in re.finditer(r"\(xy\s+([-0-9.]+)\s+([-0-9.]+)", block):
            points.append((float(match.group(1)), float(match.group(2))))
    return _bounds_from_points(points)


def _symbol_body_bounds(symbol_text: str) -> dict[int, BodyBounds]:
    raw: dict[int, BodyBounds] = {}
    for child in _direct_child_blocks(symbol_text):
        if _child_head(child) != "symbol":
            continue
        match = re.match(r'\s*\(symbol\s+"[^"]+_(\d+)_[^"]+"', child)
        if not match:
            continue
        unit = int(match.group(1))
        bounds: BodyBounds | None = None
        for grandchild in _direct_child_blocks(child):
            bounds = _merge_bounds(bounds, _shape_bounds(grandchild))
        if bounds is not None:
            raw[unit] = bounds
    if raw:
        return raw
    bounds = None
    for child in _direct_child_blocks(symbol_text):
        bounds = _merge_bounds(bounds, _shape_bounds(child))
    return {1: bounds} if bounds is not None else {}


def _geometry_aliases(geometry: PinGeometry) -> set[str]:
    aliases = {_norm_pin(geometry.number), _norm_pin(geometry.name)}
    for piece in re.split(r"[/\\\s]+", geometry.name):
        if piece:
            aliases.add(_norm_pin(piece))
    return {alias for alias in aliases if alias}


def _unit_hint(ref: str, pin: str, geometries: tuple[PinGeometry, ...]) -> int | None:
    units = sorted({geometry.unit for geometry in geometries})
    if len(units) <= 1:
        return units[0] if units else None
    upper_ref = ref.upper()
    if upper_ref.endswith("A"):
        return 1
    if upper_ref.endswith("B"):
        return 2
    match = re.search(r"CHANNEL_?(\d+)", upper_ref)
    if match:
        index = int(match.group(1))
        return 1 if index % 2 else 2
    upper_pin = pin.upper()
    if upper_pin.startswith("U1A") or upper_pin.startswith("A."):
        return 1
    if upper_pin.startswith("U1B") or upper_pin.startswith("B."):
        return 2
    return units[0]


def _pin_alias_candidates(kind: str, pin: str) -> list[str]:
    aliases_by_pin = PIN_ALIAS_BY_KIND.get(kind, {})
    raw_pin = str(pin)
    desired = _norm_pin(raw_pin)
    candidates: list[str] = []

    exact_aliases = aliases_by_pin.get(raw_pin)
    if exact_aliases is not None:
        candidates.extend(_norm_pin(alias) for alias in exact_aliases)
        candidates.append(desired)
        return [candidate for candidate in candidates if candidate]

    for raw_key, aliases in aliases_by_pin.items():
        if _norm_pin(raw_key) == desired:
            candidates.append(desired)
            candidates.extend(_norm_pin(alias) for alias in aliases)
            return [candidate for candidate in candidates if candidate]

    return [desired] if desired else []


def _resolve_pin_geometry(
    *,
    ref: str,
    kind: str,
    pin: str,
    geometries: tuple[PinGeometry, ...],
) -> tuple[PinGeometry | None, str]:
    candidates = _pin_alias_candidates(kind, pin)
    unit_hint = _unit_hint(ref, pin, geometries)
    scored: list[tuple[int, PinGeometry]] = []
    for geometry in geometries:
        aliases = _geometry_aliases(geometry)
        for index, candidate in enumerate(candidates):
            if candidate in aliases:
                unit_penalty = 0 if unit_hint is None or geometry.unit == unit_hint else 10
                scored.append((unit_penalty + index, geometry))
                break
    if not scored:
        return None, "unresolved"
    scored.sort(key=lambda item: (item[0], item[1].unit, item[1].number))
    return scored[0][1], "resolved"


def _component_lookup(placement: CatalogPlacementPlan) -> dict[str, PlacedCatalogComponent]:
    return {component.ref: component for component in placement.components}


def _resolve_component_pin_point(
    *,
    ref: str,
    pin: str,
    component: PlacedCatalogComponent | None,
    library: KiCadSymbolLibrary,
    pin_cache: dict[str, tuple[PinGeometry, ...]],
    unit_count_cache: dict[str, int],
) -> tuple[tuple[float, float] | None, str, PinGeometry | None]:
    if component is None or not component.spec.lib_id:
        return None, "component_or_lib_id_missing", None
    lib_id = component.spec.lib_id
    geometries = pin_cache.get(lib_id)
    if geometries is None:
        symbol = library.load(lib_id)
        geometries = _pin_geometries(symbol.text)
        pin_cache[lib_id] = geometries
        unit_pins = symbol.unit_pin_numbers
        unit_count_cache[lib_id] = len(unit_pins) if unit_pins else 1
    geometry, status = _resolve_pin_geometry(ref=ref, kind=component.kind, pin=pin, geometries=geometries)
    if geometry is None:
        return None, status, None
    return _pin_world(component, geometry, unit_count_cache.get(lib_id, 1)), "resolved", geometry


def _catalog_plan_from_placement_dict(circuit: dict[str, Any], placement: dict[str, Any]) -> CatalogPlacementPlan:
    requested: dict[str, dict[str, Any]] = {}
    for component in circuit.get("components", []):
        if isinstance(component, dict):
            ref = str(component.get("id") or component.get("ref") or "")
            if ref:
                requested[ref] = component

    placed_components: list[PlacedCatalogComponent] = []
    obstacles: list[Obstacle] = []
    raw_components = placement.get("components", {})
    if not isinstance(raw_components, dict):
        raise ValueError("placement.components must be an object")
    for ref, raw in raw_components.items():
        if not isinstance(raw, dict):
            continue
        kind = str(raw.get("kind") or requested.get(ref, {}).get("kind") or "")
        spec = resolve_placement_spec(kind)
        if spec is None:
            raise ValueError(f"{ref} uses unsupported placement kind {kind!r}")
        at = raw.get("at", [0.0, 0.0])
        x = float(at[0])
        y = float(at[1])
        component = PlacedCatalogComponent(
            ref=str(ref),
            kind=spec.kind,
            name=str(requested.get(ref, {}).get("value") or raw.get("name") or spec.name),
            at=(x, y),
            rotation=float(raw.get("rotation", 0.0)),
            manual_position=bool(raw.get("manual", False)),
            spec=spec,
        )
        placed_components.append(component)
        obstacles.append(
            Obstacle(
                str(ref),
                round(x - spec.width / 2, 3),
                round(y - spec.height / 2, 3),
                round(x + spec.width / 2, 3),
                round(y + spec.height / 2, 3),
            )
        )
    return CatalogPlacementPlan(tuple(placed_components), tuple(obstacles))


def _unit_origin(component: PlacedCatalogComponent, unit: int, unit_count: int) -> tuple[float, float]:
    x, y = component.at
    if unit_count <= 1:
        return x, y
    index = max(0, unit - 1)
    return x, round(y + index * MULTI_UNIT_VERTICAL_PITCH_MM, 3)


def _unit_position(component: PlacedCatalogComponent, geometry: PinGeometry, unit_count: int) -> tuple[float, float]:
    return _unit_origin(component, geometry.unit, unit_count)


def _local_point_to_world(
    component: PlacedCatalogComponent,
    origin: tuple[float, float],
    local: tuple[float, float],
) -> tuple[float, float]:
    angle = math.radians(component.rotation % 360)
    local_y = -local[1]
    x = local[0] * math.cos(angle) - local_y * math.sin(angle)
    y = local[0] * math.sin(angle) + local_y * math.cos(angle)
    return (round(origin[0] + x, 3), round(origin[1] + y, 3))


def _pin_world(component: PlacedCatalogComponent, geometry: PinGeometry, unit_count: int) -> tuple[float, float]:
    origin_x, origin_y = _unit_position(component, geometry, unit_count)
    return _local_point_to_world(component, (origin_x, origin_y), (geometry.x, geometry.y))


def _pin_side_from_rotation(rotation: float) -> str:
    angle = round(float(rotation)) % 360
    if angle == 0:
        return "left"
    if angle == 90:
        return "bottom"
    if angle == 180:
        return "right"
    if angle == 270:
        return "top"
    return ""


def _component_body_bounds_for_unit(raw_bounds: dict[int, BodyBounds], unit: int) -> BodyBounds | None:
    return _merge_bounds(raw_bounds.get(0), raw_bounds.get(unit))


def _fallback_component_body(component: PlacedCatalogComponent) -> ComponentBody:
    x, y = component.at
    width = max(2.54, min(component.spec.width, 25.4))
    height = max(2.54, min(component.spec.height, 25.4))
    return ComponentBody(
        component.ref,
        round(x - width / 2, 3),
        round(y - height / 2, 3),
        round(x + width / 2, 3),
        round(y + height / 2, 3),
        "fallback_placement_spec_body",
    )


def _world_component_body(
    component: PlacedCatalogComponent,
    bounds: BodyBounds,
    unit: int,
    unit_count: int,
    source: str,
) -> ComponentBody:
    origin = _unit_origin(component, unit, unit_count)
    corners = [
        _local_point_to_world(component, origin, (bounds.left, bounds.top)),
        _local_point_to_world(component, origin, (bounds.left, bounds.bottom)),
        _local_point_to_world(component, origin, (bounds.right, bounds.top)),
        _local_point_to_world(component, origin, (bounds.right, bounds.bottom)),
    ]
    xs = [point[0] for point in corners]
    ys = [point[1] for point in corners]
    return ComponentBody(
        component.ref,
        round(min(xs), 3),
        round(min(ys), 3),
        round(max(xs), 3),
        round(max(ys), 3),
        source,
    )


def _component_bodies(
    placement: CatalogPlacementPlan,
    library: KiCadSymbolLibrary,
) -> tuple[ComponentBody, ...]:
    bodies: list[ComponentBody] = []
    for component in placement.components:
        lib_id = component.spec.lib_id
        if not lib_id:
            bodies.append(_fallback_component_body(component))
            continue
        symbol = library.load(lib_id)
        raw_bounds = _symbol_body_bounds(symbol.text)
        units = tuple(sorted(symbol.unit_pin_numbers)) or (1,)
        unit_count = len(units)
        added = False
        for unit in units:
            bounds = _component_body_bounds_for_unit(raw_bounds, unit)
            if bounds is None:
                continue
            bodies.append(_world_component_body(component, bounds, unit, unit_count, f"{lib_id}:unit{unit}"))
            added = True
        if not added:
            bodies.append(_fallback_component_body(component))
    return tuple(bodies)


def _text_body(
    *,
    owner: str,
    text: str,
    at: tuple[float, float],
    justify: str,
    source: str,
    font_mm: float = VISIBLE_TEXT_FONT_MM,
) -> ComponentBody:
    """Conservative rectangle for visible KiCad text emitted at ``at``."""

    width = max(font_mm, len(text) * font_mm * 0.78)
    height = font_mm * 1.3
    x, y = at
    # All generated labels/reference/value fields use horizontal text.  KiCad
    # ``right`` justification extends text left from its anchor; otherwise it
    # extends right. Keep a small gap so a terminal stub can end at its anchor.
    justify_tokens = justify.split()
    if "right" in justify_tokens:
        left = x - width - VISIBLE_TEXT_CLEARANCE_MM
        right = x - VISIBLE_TEXT_CLEARANCE_MM
    else:
        left = x + VISIBLE_TEXT_CLEARANCE_MM
        right = x + width + VISIBLE_TEXT_CLEARANCE_MM
    if "top" in justify_tokens:
        top = y - VISIBLE_TEXT_CLEARANCE_MM
        bottom = y + height + VISIBLE_TEXT_CLEARANCE_MM
    else:
        top = y - height - VISIBLE_TEXT_CLEARANCE_MM
        bottom = y + VISIBLE_TEXT_CLEARANCE_MM
    return ComponentBody(
        owner,
        round(left, 3),
        round(top, 3),
        round(right, 3),
        round(bottom, 3),
        source,
    )


def _component_text_bodies(
    placement: CatalogPlacementPlan,
    library: KiCadSymbolLibrary,
) -> tuple[ComponentBody, ...]:
    """Match the visible reference/value positions written by ``symbol_instance``."""

    bodies: list[ComponentBody] = []
    for component in placement.components:
        units = (1,)
        if component.spec.lib_id:
            symbol = library.load(component.spec.lib_id)
            units = tuple(sorted(symbol.unit_pin_numbers)) or (1,)
        for unit in units:
            x, y = _unit_origin(component, unit, len(units))
            bodies.append(
                _text_body(
                    owner=f"__text__{component.ref}__unit{unit}__reference",
                    text=component.ref,
                    at=(x + 4.0, y - 5.0),
                    justify="left",
                    source="generated_visible_reference",
                )
            )
            bodies.append(
                _text_body(
                    owner=f"__text__{component.ref}__unit{unit}__value",
                    text=component.name,
                    at=(x + 4.0, y + 5.0),
                    justify="left",
                    source="generated_visible_value",
                )
            )
    return tuple(bodies)


def _bodies_overlap(left: ComponentBody, right: ComponentBody) -> bool:
    return not (
        left.right < right.left
        or right.right < left.left
        or left.bottom < right.top
        or right.bottom < left.top
    )


def _label_visual_layout_report(
    label_bodies: list[ComponentBody],
    static_obstacles: list[ComponentBody],
) -> dict[str, Any]:
    """Validate terminal text against symbols, visible fields, and peer labels."""

    overlaps: list[dict[str, str]] = []
    for index, label in enumerate(label_bodies):
        for obstacle in static_obstacles:
            if _bodies_overlap(label, obstacle):
                overlaps.append({"label": label.ref, "obstacle": obstacle.ref, "kind": "static"})
        for other in label_bodies[index + 1 :]:
            if _bodies_overlap(label, other):
                overlaps.append({"label": label.ref, "obstacle": other.ref, "kind": "label"})
    return {
        "ok": not overlaps,
        "overlap_count": len(overlaps),
        "overlaps": overlaps[:200],
        "overlaps_truncated": len(overlaps) > 200,
    }


def _catalog_plan_as_routing_placement(circuit: dict[str, Any], placement: CatalogPlacementPlan) -> dict[str, Any]:
    """Build a pure-JSON routing input with KiCad-resolved pins and bodies."""
    library = KiCadSymbolLibrary()
    components = _component_lookup(placement)
    pin_cache: dict[str, tuple[PinGeometry, ...]] = {}
    unit_count_cache: dict[str, int] = {}
    pin_points: dict[str, dict[str, dict[str, Any]]] = {}
    unresolved: list[dict[str, Any]] = []
    resolved_count = 0

    for _net, endpoints in extract_connection_nets(circuit).items():
        for endpoint in endpoints:
            ref = str(endpoint.ref)
            pin = str(endpoint.pin)
            point, status, geometry = _resolve_component_pin_point(
                ref=ref,
                pin=pin,
                component=components.get(ref),
                library=library,
                pin_cache=pin_cache,
                unit_count_cache=unit_count_cache,
            )
            if point is None:
                unresolved.append({"ref": ref, "pin": pin, "reason": status})
                continue
            component = components[ref]
            source = f"{component.spec.lib_id}:unit{geometry.unit}:pin{geometry.number}" if geometry else "kicad_symbol_pin"
            pin_points.setdefault(ref, {})[pin] = {
                "point": [round(point[0], 3), round(point[1], 3)],
                "source": source,
                "side": _pin_side_from_rotation(geometry.rotation) if geometry else "",
                "resolved_pin_number": geometry.number if geometry else "",
                "resolved_pin_name": geometry.name if geometry else "",
            }
            resolved_count += 1

    body_items = []
    for index, body in enumerate(_component_bodies(placement, library), 1):
        body_items.append(
            {
                "owner": f"{body.ref}::body{index}",
                "component_ref": body.ref,
                "left": body.left,
                "top": body.top,
                "right": body.right,
                "bottom": body.bottom,
                "source": body.source,
            }
        )
    overlap_report = component_body_overlap_report(body_items)
    layout_items = list(body_items)
    for component in placement.components:
        lib_id = component.spec.lib_id
        if not lib_id:
            continue
        symbol = library.load(lib_id)
        unit_count = len(symbol.unit_pin_numbers) if symbol.unit_pin_numbers else 1
        for geometry in _pin_geometries(symbol.text):
            point = _pin_world(component, geometry, unit_count)
            layout_items.append(
                {
                    "owner": f"{component.ref}::pin{geometry.unit}_{geometry.number}",
                    "component_ref": component.ref,
                    "left": point[0],
                    "top": point[1],
                    "right": point[0],
                    "bottom": point[1],
                    "source": f"{lib_id}:unit{geometry.unit}:pin{geometry.number}:layout_pin_tip",
                }
            )

    component_items = {
        component.ref: {
            "kind": component.kind,
            "name": component.name,
            "at": [component.at[0], component.at[1]],
            "rotation": component.rotation,
            "width": component.spec.width,
            "height": component.spec.height,
        }
        for component in placement.components
    }
    return {
        "schema": "progen-kicad-routing-placement/v0.1",
        "stage": "kicad_routing_input_builder",
        "components": component_items,
        "obstacles": body_items,
        "layout_obstacles": layout_items,
        "pin_points": pin_points,
        "routing_metadata": {
            "pin_point_source": "KiCad embedded/source symbol library pin coordinates",
            "body_source": "KiCad symbol graphics bounds with fallback placement specs",
            "pin_resolved_count": resolved_count,
            "unresolved_pin_count": len(unresolved),
            "unresolved_pins": unresolved[:200],
            "unresolved_pin_report_truncated": len(unresolved) > 200,
            "component_body_overlap_ok": bool(overlap_report["ok"]),
            "component_body_overlap_count": int(overlap_report["overlap_count"]),
            "component_body_overlaps": overlap_report["overlaps"],
        },
    }


def _orthogonal_points(start: tuple[float, float], end: tuple[float, float]) -> list[tuple[float, float]]:
    if start == end:
        return [start]
    if start[0] == end[0] or start[1] == end[1]:
        return [start, end]
    return [start, (end[0], start[1]), end]


def _segments_from_points(points: list[tuple[float, float]]) -> list[tuple[tuple[float, float], tuple[float, float]]]:
    return [(a, b) for a, b in zip(points, points[1:]) if a != b]


def _segment_axis(segment: WireGeometrySegment, eps: float = 0.001) -> tuple[str, float, float, float] | None:
    if abs(segment.start[1] - segment.end[1]) <= eps:
        low, high = sorted((segment.start[0], segment.end[0]))
        return ("h", round(segment.start[1], 3), round(low, 3), round(high, 3))
    if abs(segment.start[0] - segment.end[0]) <= eps:
        low, high = sorted((segment.start[1], segment.end[1]))
        return ("v", round(segment.start[0], 3), round(low, 3), round(high, 3))
    return None


def _unique_allowed_touches(items: list[AllowedTouch]) -> tuple[AllowedTouch, ...]:
    seen: set[tuple[str, tuple[float, float]]] = set()
    out: list[AllowedTouch] = []
    for item in items:
        key = (item.ref, (round(item.point[0], 3), round(item.point[1], 3)))
        if key in seen:
            continue
        seen.add(key)
        out.append(item)
    return tuple(out)


def _merged_segment(
    *,
    net: str,
    orientation: str,
    fixed: float,
    low: float,
    high: float,
    allowed_touches: tuple[AllowedTouch, ...],
    source: str,
) -> WireGeometrySegment:
    if orientation == "h":
        start = (round(low, 3), fixed)
        end = (round(high, 3), fixed)
    else:
        start = (fixed, round(low, 3))
        end = (fixed, round(high, 3))
    return WireGeometrySegment(net=net, start=start, end=end, allowed_touches=allowed_touches, source=source)


def _merge_same_net_collinear_segments(segments: list[WireGeometrySegment]) -> list[WireGeometrySegment]:
    buckets: dict[tuple[str, str, float], list[tuple[float, float, WireGeometrySegment]]] = {}
    passthrough: list[WireGeometrySegment] = []
    for segment in segments:
        axis = _segment_axis(segment)
        if axis is None:
            passthrough.append(segment)
            continue
        orientation, fixed, low, high = axis
        if abs(high - low) <= 0.001:
            continue
        buckets.setdefault((segment.net, orientation, fixed), []).append((low, high, segment))

    merged = list(passthrough)
    for (net, orientation, fixed), records in sorted(buckets.items(), key=lambda item: item[0]):
        records.sort(key=lambda item: (item[0], item[1], item[2].source))
        current_low: float | None = None
        current_high: float | None = None
        current_touches: list[AllowedTouch] = []
        current_sources: list[str] = []

        def flush() -> None:
            if current_low is None or current_high is None:
                return
            source = current_sources[0] if len(set(current_sources)) == 1 else "merged_same_net_collinear"
            merged.append(
                _merged_segment(
                    net=net,
                    orientation=orientation,
                    fixed=fixed,
                    low=current_low,
                    high=current_high,
                    allowed_touches=_unique_allowed_touches(current_touches),
                    source=source,
                )
            )

        for low, high, segment in records:
            if current_low is None or current_high is None:
                current_low = low
                current_high = high
                current_touches = list(segment.allowed_touches)
                current_sources = [segment.source]
                continue
            if low < current_high - 0.001:
                current_high = max(current_high, high)
                current_touches.extend(segment.allowed_touches)
                current_sources.append(segment.source)
                continue
            flush()
            current_low = low
            current_high = high
            current_touches = list(segment.allowed_touches)
            current_sources = [segment.source]
        flush()
    return sorted(merged, key=lambda item: (item.net, item.start[1], item.start[0], item.end[1], item.end[0], item.source))


def _point_on_wire_segment(point: tuple[float, float], segment: WireGeometrySegment, eps: float = 0.001) -> bool:
    if abs(segment.start[1] - segment.end[1]) <= eps:
        low, high = sorted((segment.start[0], segment.end[0]))
        return abs(point[1] - segment.start[1]) <= eps and low - eps <= point[0] <= high + eps
    if abs(segment.start[0] - segment.end[0]) <= eps:
        low, high = sorted((segment.start[1], segment.end[1]))
        return abs(point[0] - segment.start[0]) <= eps and low - eps <= point[1] <= high + eps
    return False


def _point_distance_on_segment(origin: tuple[float, float], point: tuple[float, float]) -> float:
    return abs(origin[0] - point[0]) + abs(origin[1] - point[1])


def _segment_endpoint(point: tuple[float, float], segment: WireGeometrySegment) -> bool:
    rounded = _round_wire_point(point)
    return rounded == _round_wire_point(segment.start) or rounded == _round_wire_point(segment.end)


def _segment_pin_touch(point: tuple[float, float], segment: WireGeometrySegment) -> bool:
    rounded = _round_wire_point(point)
    return any(rounded == _round_wire_point(allowed.point) for allowed in segment.allowed_touches)


def _cross_net_hard_contacts(
    left: WireGeometrySegment,
    right: WireGeometrySegment,
) -> list[tuple[float, float] | tuple[tuple[float, float], tuple[float, float]]]:
    if left.net == right.net:
        return []
    left_axis = _segment_axis(left)
    right_axis = _segment_axis(right)
    if left_axis is None or right_axis is None:
        return []

    left_orientation, left_fixed, left_low, left_high = left_axis
    right_orientation, right_fixed, right_low, right_high = right_axis
    if left_orientation == right_orientation:
        if abs(left_fixed - right_fixed) > 0.001:
            return []
        low = max(left_low, right_low)
        high = min(left_high, right_high)
        if low > high + 0.001:
            return []
        if abs(low - high) <= 0.001:
            point = (round(low, 3), left_fixed) if left_orientation == "h" else (left_fixed, round(low, 3))
            return [point]
        start = (round(low, 3), left_fixed) if left_orientation == "h" else (left_fixed, round(low, 3))
        end = (round(high, 3), left_fixed) if left_orientation == "h" else (left_fixed, round(high, 3))
        return [(start, end)]

    horizontal = left if left_orientation == "h" else right
    vertical = right if left_orientation == "h" else left
    point = (round(vertical.start[0], 3), round(horizontal.start[1], 3))
    if not _point_on_wire_segment(point, horizontal) or not _point_on_wire_segment(point, vertical):
        return []

    horizontal_interior = not _segment_endpoint(point, horizontal)
    vertical_interior = not _segment_endpoint(point, vertical)
    if horizontal_interior and vertical_interior and not (
        _segment_pin_touch(point, horizontal) or _segment_pin_touch(point, vertical)
    ):
        return []
    return [point]


def _candidate_creates_cross_net_endpoint_touch(
    candidate_segments: list[WireGeometrySegment],
    existing_segments: list[WireGeometrySegment],
) -> bool:
    for candidate in candidate_segments:
        for existing in existing_segments:
            if _cross_net_hard_contacts(candidate, existing):
                return True
    return False


def _trim_dangling_wire_tails(
    segments: list[WireGeometrySegment],
    protected_points: set[tuple[float, float]],
) -> tuple[list[WireGeometrySegment], int]:
    trimmed: list[WireGeometrySegment] = []
    trim_count = 0
    rounded_protected = {(round(point[0], 3), round(point[1], 3)) for point in protected_points}

    def is_protected(point: tuple[float, float]) -> bool:
        return (round(point[0], 3), round(point[1], 3)) in rounded_protected

    for index, segment in enumerate(segments):
        start = segment.start
        end = segment.end
        for endpoint_name in ("start", "end"):
            endpoint = start if endpoint_name == "start" else end
            if is_protected(endpoint):
                continue
            touches_other = any(
                other_index != index
                and other.net == segment.net
                and _point_on_wire_segment(endpoint, other)
                for other_index, other in enumerate(segments)
            )
            if touches_other:
                continue
            candidates: set[tuple[float, float]] = set()
            for other_index, other in enumerate(segments):
                if other_index == index or other.net != segment.net:
                    continue
                for point in (other.start, other.end):
                    rounded = (round(point[0], 3), round(point[1], 3))
                    if rounded != endpoint and _point_on_wire_segment(rounded, segment):
                        candidates.add(rounded)
            for point in rounded_protected:
                if point != endpoint and _point_on_wire_segment(point, segment):
                    candidates.add(point)
            if not candidates:
                continue
            replacement = min(candidates, key=lambda point: _point_distance_on_segment(endpoint, point))
            if endpoint_name == "start":
                start = replacement
            else:
                end = replacement
            trim_count += 1
        if start != end:
            trimmed.append(
                WireGeometrySegment(
                    net=segment.net,
                    start=start,
                    end=end,
                    allowed_touches=segment.allowed_touches,
                    source=segment.source,
                )
            )
    return trimmed, trim_count


def component_body_overlap_report(
    obstacles: list[dict[str, Any]] | tuple[dict[str, Any], ...],
    *,
    clearance: float = 0.0,
) -> dict[str, Any]:
    """Report cross-component body overlaps from placement/routing obstacle JSON."""
    pairs: list[dict[str, Any]] = []
    normalized: list[dict[str, Any]] = []
    for item in obstacles:
        if not isinstance(item, dict):
            continue
        owner = str(item.get("owner") or "")
        ref = str(item.get("component_ref") or owner)
        if "::" in ref:
            ref = ref.split("::", 1)[0]
        if not owner or not ref:
            continue
        normalized.append(
            {
                "owner": owner,
                "component_ref": ref,
                "left": float(item.get("left", 0.0)) - clearance,
                "top": float(item.get("top", 0.0)) - clearance,
                "right": float(item.get("right", 0.0)) + clearance,
                "bottom": float(item.get("bottom", 0.0)) + clearance,
            }
        )

    for index, left in enumerate(normalized):
        for right in normalized[index + 1 :]:
            if left["component_ref"] == right["component_ref"]:
                continue
            if (
                left["left"] < right["right"]
                and left["right"] > right["left"]
                and left["top"] < right["bottom"]
                and left["bottom"] > right["top"]
            ):
                pairs.append(
                    {
                        "left": left["owner"],
                        "right": right["owner"],
                        "left_component": left["component_ref"],
                        "right_component": right["component_ref"],
                    }
                )
    return {
        "schema": "progen-kicad-component-body-overlap-report/v0.1",
        "ok": not pairs,
        "clearance": clearance,
        "body_count": len(normalized),
        "overlap_count": len(pairs),
        "overlaps": pairs[:200],
        "overlaps_truncated": len(pairs) > 200,
    }


def _path_with_actual_ends(
    start: tuple[float, float],
    planned: list[list[float]],
    end: tuple[float, float],
) -> list[tuple[float, float]]:
    if not planned:
        return _orthogonal_points(start, end)
    planned_points = [(round(float(point[0]), 3), round(float(point[1]), 3)) for point in planned]
    out: list[tuple[float, float]] = []
    for point in _orthogonal_points(start, planned_points[0])[:-1]:
        out.append(point)
    out.extend(planned_points)
    for point in _orthogonal_points(planned_points[-1], end)[1:]:
        out.append(point)
    deduped: list[tuple[float, float]] = []
    for point in out:
        if not deduped or point != deduped[-1]:
            deduped.append(point)
    return deduped


def _compress_wire_path(points: list[tuple[float, float]]) -> list[tuple[float, float]]:
    deduped: list[tuple[float, float]] = []
    for point in points:
        rounded = _round_wire_point(point)
        if deduped and rounded == deduped[-1]:
            continue
        deduped.append(rounded)
    changed = True
    while changed:
        changed = False
        compressed: list[tuple[float, float]] = []
        for point in deduped:
            compressed.append(point)
            while len(compressed) >= 3:
                a, b, c = compressed[-3], compressed[-2], compressed[-1]
                if (a[0] == b[0] == c[0]) or (a[1] == b[1] == c[1]):
                    compressed.pop(-2)
                    changed = True
                else:
                    break
        deduped = compressed
    return deduped


def _dedupe_wire_path(points: list[tuple[float, float]]) -> list[tuple[float, float]]:
    out: list[tuple[float, float]] = []
    for point in points:
        rounded = _round_wire_point(point)
        if not out or out[-1] != rounded:
            out.append(rounded)
    return out


def _routing_axis_limits(
    *,
    axis: str,
    start: tuple[float, float],
    end: tuple[float, float],
    existing_segments: list[WireGeometrySegment],
    component_bodies: tuple[ComponentBody, ...],
    margin: float = 76.2,
) -> tuple[float, float]:
    values = [start[0], end[0]] if axis == "x" else [start[1], end[1]]
    for body in component_bodies:
        values.extend([body.left, body.right] if axis == "x" else [body.top, body.bottom])
    for segment in existing_segments:
        values.extend([segment.start[0], segment.end[0]] if axis == "x" else [segment.start[1], segment.end[1]])
    return min(values) - margin, max(values) + margin


def _exact_lane_values(
    *,
    axis: str,
    start: tuple[float, float],
    end: tuple[float, float],
    existing_segments: list[WireGeometrySegment],
    component_bodies: tuple[ComponentBody, ...],
) -> list[float]:
    base = start[0] if axis == "x" else start[1]
    target = end[0] if axis == "x" else end[1]
    values: set[float] = {base, target, (base + target) / 2}
    for delta in (2.54, 5.08, 7.62, 10.16, 15.24, -2.54, -5.08, -7.62, -10.16, -15.24):
        values.add(base + delta)
        values.add(target + delta)
    for body in component_bodies:
        if axis == "x":
            for value in (body.left - 5.08, body.right + 5.08, body.left - 10.16, body.right + 10.16):
                values.add(value)
        else:
            for value in (body.top - 5.08, body.bottom + 5.08, body.top - 10.16, body.bottom + 10.16):
                values.add(value)
    for segment in existing_segments:
        value = segment.start[0] if axis == "x" else segment.start[1]
        for delta in (2.54, -2.54, 5.08, -5.08):
            values.add(value + delta)
    low_limit, high_limit = _routing_axis_limits(
        axis=axis,
        start=start,
        end=end,
        existing_segments=existing_segments,
        component_bodies=component_bodies,
    )
    return sorted(
        {round(round(value / 2.54) * 2.54, 3) for value in values if low_limit <= value <= high_limit},
        key=lambda item: (abs(item - (base + target) / 2), item),
    )


def _touch_body_candidates(touch: AllowedTouch, component_bodies: tuple[ComponentBody, ...]) -> list[ComponentBody]:
    point = _round_wire_point(touch.point)
    bodies = [body for body in component_bodies if body.ref == touch.ref]
    if not bodies:
        return []
    containing = [
        body
        for body in bodies
        if body.left - 2.54 <= point[0] <= body.right + 2.54 and body.top - 2.54 <= point[1] <= body.bottom + 2.54
    ]
    return containing or bodies


def _escape_points_for_touch(
    touch: AllowedTouch,
    target: tuple[float, float],
    component_bodies: tuple[ComponentBody, ...],
) -> list[tuple[float, float]]:
    point = _round_wire_point(touch.point)
    out: list[tuple[float, float]] = [point]
    for body in _touch_body_candidates(touch, component_bodies):
        body_center = ((body.left + body.right) / 2, (body.top + body.bottom) / 2)
        preferred = [
            (body.right + 5.08, point[1]) if point[0] >= body_center[0] else (body.left - 5.08, point[1]),
            (point[0], body.bottom + 5.08) if point[1] >= body_center[1] else (point[0], body.top - 5.08),
        ]
        candidates = preferred + [
            (body.left - 5.08, point[1]),
            (body.right + 5.08, point[1]),
            (point[0], body.top - 5.08),
            (point[0], body.bottom + 5.08),
        ]
        candidates.sort(key=lambda candidate: (abs(candidate[0] - target[0]) + abs(candidate[1] - target[1]), candidate[1], candidate[0]))
        for candidate in candidates:
            rounded = _round_wire_point(candidate)
            if rounded not in out:
                out.append(rounded)
    return out[:5]


def _core_candidate_actual_paths(
    start: tuple[float, float],
    end: tuple[float, float],
    existing_segments: list[WireGeometrySegment],
    component_bodies: tuple[ComponentBody, ...],
) -> list[list[tuple[float, float]]]:
    candidates: list[list[tuple[float, float]]] = [
        _compress_wire_path(_orthogonal_points(start, end)),
        _compress_wire_path([start, (end[0], start[1]), end]),
        _compress_wire_path([start, (start[0], end[1]), end]),
    ]
    x_lanes = _exact_lane_values(axis="x", start=start, end=end, existing_segments=existing_segments, component_bodies=component_bodies)
    y_lanes = _exact_lane_values(axis="y", start=start, end=end, existing_segments=existing_segments, component_bodies=component_bodies)
    for lane_y in y_lanes[:32]:
        candidates.append(_compress_wire_path([start, (start[0], lane_y), (end[0], lane_y), end]))
    for lane_x in x_lanes[:32]:
        candidates.append(_compress_wire_path([start, (lane_x, start[1]), (lane_x, end[1]), end]))
    for lane_x in x_lanes[:12]:
        for lane_y in y_lanes[:12]:
            candidates.append(_compress_wire_path([start, (lane_x, start[1]), (lane_x, lane_y), (end[0], lane_y), end]))
            candidates.append(_compress_wire_path([start, (start[0], lane_y), (lane_x, lane_y), (lane_x, end[1]), end]))
    return candidates


def _candidate_actual_paths(
    original: list[tuple[float, float]],
    start: tuple[float, float],
    end: tuple[float, float],
    allowed_touches: tuple[AllowedTouch, ...],
    existing_segments: list[WireGeometrySegment],
    component_bodies: tuple[ComponentBody, ...],
) -> list[list[tuple[float, float]]]:
    candidates: list[list[tuple[float, float]]] = [_compress_wire_path(original)]
    start_touch = allowed_touches[0] if allowed_touches else AllowedTouch("", start)
    end_touch = allowed_touches[1] if len(allowed_touches) > 1 else AllowedTouch("", end)
    start_exits = _escape_points_for_touch(start_touch, end, component_bodies)[:3]
    end_exits = _escape_points_for_touch(end_touch, start, component_bodies)[:3]
    for start_exit in start_exits:
        for end_exit in end_exits:
            for core in _core_candidate_actual_paths(start_exit, end_exit, existing_segments, component_bodies):
                prefix = [start] if start_exit == start else [start, start_exit]
                suffix = [end] if end_exit == end else [end_exit, end]
                candidates.append(_dedupe_wire_path(prefix + core[1:-1] + suffix))
                if len(candidates) >= MAX_ACTUAL_PATH_CANDIDATES:
                    break
            if len(candidates) >= MAX_ACTUAL_PATH_CANDIDATES:
                break
        if len(candidates) >= MAX_ACTUAL_PATH_CANDIDATES:
            break

    seen: set[tuple[tuple[float, float], ...]] = set()
    out: list[list[tuple[float, float]]] = []
    for candidate in candidates:
        key = tuple(candidate)
        if len(candidate) < 2 or key in seen:
            continue
        seen.add(key)
        out.append(candidate)
        if len(out) >= MAX_ACTUAL_PATH_CANDIDATES:
            break
    return out


def _validated_actual_path(
    *,
    net: str,
    original: list[tuple[float, float]],
    start: tuple[float, float],
    end: tuple[float, float],
    allowed_touches: tuple[AllowedTouch, ...],
    existing_segments: list[WireGeometrySegment],
    component_bodies: tuple[ComponentBody, ...],
    protected_pin_points: dict[tuple[float, float], set[str]],
    source: str,
) -> tuple[list[tuple[float, float]], bool, bool]:
    best_path = _compress_wire_path(original)
    best_violation_count: int | None = None
    best_length = float("inf")
    for candidate in _candidate_actual_paths(best_path, start, end, allowed_touches, existing_segments, component_bodies):
        candidate_allowed_points = {(round(allowed.point[0], 3), round(allowed.point[1], 3)) for allowed in allowed_touches}
        touches_wrong_pin = False
        for a, b in _segments_from_points(candidate):
            probe_segment = WireGeometrySegment(net=net, start=a, end=b, allowed_touches=allowed_touches, source=source)
            for pin_point, pin_nets in protected_pin_points.items():
                if net in pin_nets or pin_point in candidate_allowed_points:
                    continue
                if _point_on_wire_segment(pin_point, probe_segment):
                    touches_wrong_pin = True
                    break
            if touches_wrong_pin:
                break
        if touches_wrong_pin:
            continue
        candidate_segments = [
            WireGeometrySegment(net=net, start=a, end=b, allowed_touches=allowed_touches, source=source)
            for a, b in _segments_from_points(candidate)
        ]
        if _candidate_creates_cross_net_endpoint_touch(candidate_segments, existing_segments):
            continue
        report = validate_wire_geometry(candidate_segments, component_bodies)
        length = sum(abs(a[0] - b[0]) + abs(a[1] - b[1]) for a, b in _segments_from_points(candidate))
        violation_count = int(report.get("violation_count", 0))
        if report["ok"]:
            return candidate, candidate != best_path, True
        if best_violation_count is None or (violation_count, length) < (best_violation_count, best_length):
            best_path = candidate
            best_violation_count = violation_count
            best_length = length
    return best_path, best_path != _compress_wire_path(original), False


def _label_justify(anchor: tuple[float, float], label: tuple[float, float], side: str = "") -> str:
    """Keep a terminal label extending away from its pin whenever possible."""

    delta_x = round(label[0] - anchor[0], 3)
    if delta_x < 0:
        horizontal = "right"
    elif delta_x > 0:
        horizontal = "left"
    else:
        # A label that has only moved vertically still needs a horizontal
        # direction.  Use the pin's exposed side, rather than defaulting right
        # into the symbol for a left-facing pin.
        horizontal = "right" if side.lower().strip() == "left" else "left"
    delta_y = round(label[1] - anchor[1], 3)
    if delta_y > 0 or (delta_y == 0.0 and side.lower().strip() == "bottom"):
        vertical = "top"
    else:
        vertical = "bottom"
    return f"{horizontal} {vertical}"


def _side_vector(side: str) -> tuple[float, float]:
    normalized = side.lower().strip()
    if normalized == "left":
        return (-1.0, 0.0)
    if normalized == "right":
        return (1.0, 0.0)
    if normalized == "top":
        return (0.0, -1.0)
    if normalized == "bottom":
        return (0.0, 1.0)
    return (1.0, 0.0)


def _label_direction(
    pin_point: tuple[float, float],
    label_point: tuple[float, float],
    side: str,
) -> tuple[float, float]:
    dx = round(label_point[0] - pin_point[0], 3)
    dy = round(label_point[1] - pin_point[1], 3)
    if dx == 0.0 and dy == 0.0:
        return _side_vector(side)
    if abs(dx) >= abs(dy) and dx != 0.0:
        return (1.0 if dx > 0 else -1.0, 0.0)
    if dy != 0.0:
        return (0.0, 1.0 if dy > 0 else -1.0)
    return _side_vector(side)


def _terminal_label_point(
    pin_point: tuple[float, float],
    side: str,
    offset_mm: float = TERMINAL_LABEL_PIN_OFFSET_MM,
) -> tuple[float, float]:
    dx, dy = _side_vector(side)
    return (round(pin_point[0] + dx * offset_mm, 3), round(pin_point[1] + dy * offset_mm, 3))


def _reserved_label_point(
    *,
    net: str,
    ref: str,
    pin_point: tuple[float, float],
    raw_label: tuple[float, float],
    side: str,
    used_label_points: dict[tuple[float, float], str],
    existing_segments: list[WireGeometrySegment],
    component_bodies: tuple[ComponentBody, ...],
    protected_pin_points: dict[tuple[float, float], set[str]],
    visual_obstacle_bodies: list[ComponentBody],
) -> tuple[tuple[float, float], bool, list[tuple[float, float]]]:
    def touches_wrong_protected_pin(segment: WireGeometrySegment) -> bool:
        own_pin = _round_wire_point(pin_point)
        for protected_point, protected_nets in protected_pin_points.items():
            rounded = _round_wire_point(protected_point)
            if rounded == own_pin:
                continue
            if net in protected_nets:
                continue
            if _point_on_wire_segment(rounded, segment):
                return True
        return False

    def label_text_body(candidate: tuple[float, float]) -> ComponentBody:
        return _text_body(
            owner=f"__label_text__{net}__{ref}__{pin_point[0]}__{pin_point[1]}",
            text=net,
            at=candidate,
            justify=_label_justify(pin_point, candidate, side),
            source="generated_terminal_label",
            font_mm=TERMINAL_LABEL_FONT_MM,
        )

    def text_is_clear(candidate: tuple[float, float]) -> bool:
        proposed = label_text_body(candidate)
        return not any(_bodies_overlap(proposed, body) for body in visual_obstacle_bodies)

    def candidate_paths(candidate: tuple[float, float]) -> list[list[tuple[float, float]]]:
        if candidate == pin_point:
            return [[pin_point]]
        paths: list[list[tuple[float, float]]] = []
        if candidate[0] == pin_point[0] or candidate[1] == pin_point[1]:
            paths.append([pin_point, candidate])
        else:
            horizontal_first = [pin_point, (candidate[0], pin_point[1]), candidate]
            vertical_first = [pin_point, (pin_point[0], candidate[1]), candidate]
            primary = _label_direction(pin_point, raw_label, side)
            paths.extend([horizontal_first, vertical_first] if primary[0] else [vertical_first, horizontal_first])

        # Dense connector and IC pin rows need a genuine escape before they
        # fan into a parallel label lane.  A simple L-shape can otherwise run
        # through the endpoint of its neighbouring terminal stub and become an
        # unintended electrical contact.
        escape_dx, escape_dy = _side_vector(side)
        # Try several short egress offsets.  The first adjacent terminal may
        # already occupy one of them, so a single hard-coded escape distance
        # is not enough for closely-spaced connector rows.
        for escape_mm in (1.27, 2.54, 3.81, 5.08):
            escape = (
                round(pin_point[0] + escape_dx * escape_mm, 3),
                round(pin_point[1] + escape_dy * escape_mm, 3),
            )
            if escape == pin_point:
                continue
            if escape_dx:
                lane_turn = (escape[0], candidate[1])
            else:
                lane_turn = (candidate[0], escape[1])
            lane_path = [pin_point, escape, lane_turn, candidate]
            deduped_lane: list[tuple[float, float]] = []
            for point in lane_path:
                if not deduped_lane or point != deduped_lane[-1]:
                    deduped_lane.append(point)
            if len(deduped_lane) > 1 and deduped_lane not in paths:
                paths.append(deduped_lane)
        return paths

    # A terminal stub must never cross a symbol body or another protected pin.
    # Visible reference/value text is deliberately *not* a wire obstacle: it
    # may cross a short stub, but treating it as one can leave no valid lane
    # and force the label itself back onto its pin.  The label text remains
    # checked against every visible obstacle by ``text_is_clear`` above.
    validation_bodies = component_bodies

    def try_candidate(candidate: tuple[float, float]) -> list[tuple[float, float]] | None:
        if used_label_points.get(candidate) not in (None, net) or not text_is_clear(candidate):
            return None
        for path in candidate_paths(candidate):
            candidate_segments = [
                WireGeometrySegment(
                    net=net,
                    start=start,
                    end=end,
                    allowed_touches=(AllowedTouch(ref, pin_point),),
                    source=f"{net}:reserved_label_candidate:{ref}",
                )
                for start, end in _segments_from_points(path)
            ]
            if any(touches_wrong_protected_pin(segment) for segment in candidate_segments):
                continue
            if _candidate_creates_cross_net_endpoint_touch(candidate_segments, existing_segments):
                continue
            if validate_wire_geometry(candidate_segments, validation_bodies)["ok"]:
                used_label_points[candidate] = net
                return path
        return None

    path = try_candidate(raw_label)
    if path is not None:
        return raw_label, False, path

    primary = _label_direction(pin_point, raw_label, side)
    directions = [primary, (1.0, 0.0), (-1.0, 0.0), (0.0, -1.0), (0.0, 1.0)]
    unique_directions: list[tuple[float, float]] = []
    for direction in directions:
        if direction not in unique_directions:
            unique_directions.append(direction)

    for step in range(2, 17):
        for direction in unique_directions:
            candidate = (
                round(pin_point[0] + direction[0] * 5.08 * step, 3),
                round(pin_point[1] + direction[1] * 5.08 * step, 3),
            )
            path = try_candidate(candidate)
            if path is not None:
                return candidate, True, path

    # A diagonal label lane lets a crowded pin escape without overlapping its
    # own reference/value text or a neighbouring terminal name.
    for step in range(1, 17):
        for scale_x, scale_y in ((1, 1), (2, 1), (1, 2)):
            for sign_x, sign_y in ((1, 1), (1, -1), (-1, 1), (-1, -1)):
                candidate = (
                    round(pin_point[0] + sign_x * 5.08 * step * scale_x, 3),
                    round(pin_point[1] + sign_y * 5.08 * step * scale_y, 3),
                )
                path = try_candidate(candidate)
                if path is not None:
                    return candidate, True, path

    for step in range(17, 65):
        for direction in unique_directions:
            candidate = (
                round(pin_point[0] + direction[0] * 5.08 * step, 3),
                round(pin_point[1] + direction[1] * 5.08 * step, 3),
            )
            path = try_candidate(candidate)
            if path is not None:
                return candidate, True, path

    # This should be unreachable for normal sheets. Keep the electrical label
    # anchored at its pin as the only final fallback; the visual report makes
    # that condition explicit and blocks release acceptance.
    return pin_point, True, [pin_point]


def _point_on_visual_segment(point: tuple[float, float], segment: tuple[tuple[float, float], tuple[float, float]]) -> bool:
    a, b = segment
    if abs(a[1] - b[1]) <= 0.001:
        low, high = sorted((a[0], b[0]))
        return abs(point[1] - a[1]) <= 0.001 and low - 0.001 <= point[0] <= high + 0.001
    if abs(a[0] - b[0]) <= 0.001:
        low, high = sorted((a[1], b[1]))
        return abs(point[0] - a[0]) <= 0.001 and low - 0.001 <= point[1] <= high + 0.001
    return False


def _insert_junctions(segments: list[WireGeometrySegment]) -> list[tuple[float, float]]:
    junctions: set[tuple[float, float]] = set()
    segments_by_net: dict[str, list[WireGeometrySegment]] = {}
    for segment in segments:
        segments_by_net.setdefault(segment.net, []).append(segment)

    for net_segments in segments_by_net.values():
        endpoint_counts: dict[tuple[float, float], int] = {}
        endpoints: set[tuple[float, float]] = set()
        visual_segments = [(segment.start, segment.end) for segment in net_segments]
        for segment in net_segments:
            endpoint_counts[segment.start] = endpoint_counts.get(segment.start, 0) + 1
            endpoint_counts[segment.end] = endpoint_counts.get(segment.end, 0) + 1
            endpoints.add(segment.start)
            endpoints.add(segment.end)

        for point in endpoints:
            touching_count = 0
            interior_touch = False
            for visual_segment in visual_segments:
                if not _point_on_visual_segment(point, visual_segment):
                    continue
                touching_count += 1
                a, b = visual_segment
                if point != a and point != b:
                    interior_touch = True
            if endpoint_counts.get(point, 0) >= 3 or touching_count >= 3 or interior_touch:
                if not any(
                    other.net != net_segments[0].net and _point_on_wire_segment(point, other)
                    for other in segments
                ):
                    junctions.add(point)
    return sorted(junctions, key=lambda item: (item[1], item[0]))


class _PointUnionFind:
    def __init__(self) -> None:
        self.parent: dict[tuple[float, float], tuple[float, float]] = {}

    def make(self, point: tuple[float, float]) -> None:
        rounded = _round_wire_point(point)
        if rounded not in self.parent:
            self.parent[rounded] = rounded

    def find(self, point: tuple[float, float]) -> tuple[float, float]:
        rounded = _round_wire_point(point)
        self.make(rounded)
        parent = self.parent[rounded]
        if parent != rounded:
            self.parent[rounded] = self.find(parent)
        return self.parent[rounded]

    def union(self, left: tuple[float, float], right: tuple[float, float]) -> None:
        left_root = self.find(left)
        right_root = self.find(right)
        if left_root != right_root:
            self.parent[right_root] = left_root


def _round_wire_point(point: tuple[float, float]) -> tuple[float, float]:
    return (round(point[0], 3), round(point[1], 3))


def _wire_plan_routing_mode(wire_plan: dict[str, Any]) -> str:
    raw = wire_plan.get("routing_mode")
    if raw is None:
        raw = wire_plan.get("decision", {}).get("routing_mode") if isinstance(wire_plan.get("decision"), dict) else None
    return normalize_routing_mode(raw or "wire")


def _wire_mode_terminal_policy_nets(wire_plan: dict[str, Any]) -> set[str]:
    policy = wire_plan.get("wire_mode_terminal_policy")
    if not isinstance(policy, dict) or not policy.get("enabled"):
        return set()
    raw = policy.get("terminal_nets") or ()
    if isinstance(raw, str):
        raw = [raw]
    if not isinstance(raw, (list, tuple, set)):
        return set()
    return {str(net).strip().upper() for net in raw if str(net).strip()}


def _wire_mode_terminal_label_allowed(wire_plan: dict[str, Any], net: str, strategy: str) -> bool:
    return (
        _wire_plan_routing_mode(wire_plan) == "wire"
        and strategy == WIRE_MODE_TERMINAL_LABEL_STRATEGY
        and net.strip().upper() in _wire_mode_terminal_policy_nets(wire_plan)
    )


def _generation_variation(circuit: dict[str, Any]) -> dict[str, Any]:
    raw = circuit.get("generation_variation")
    if isinstance(raw, dict) and raw.get("enabled"):
        return raw
    return {}


def _apply_generation_variation_config(arrangement_cfg: dict[str, Any], circuit: dict[str, Any]) -> dict[str, Any]:
    variation = _generation_variation(circuit)
    if not variation:
        return arrangement_cfg
    profile = str(variation.get("profile") or "square_loose")
    multipliers = VARIATION_ARRANGEMENT_PROFILES.get(profile, VARIATION_ARRANGEMENT_PROFILES["square_loose"])
    out = dict(arrangement_cfg)
    for key, multiplier in multipliers.items():
        if isinstance(out.get(key), (int, float)):
            out[key] = round(float(out[key]) * float(multiplier), 3)
    out["variation_mode"] = 1.0
    out["variation_index"] = float(variation.get("variation_index") or 0)
    if bool(variation.get("disable_adaptive_cap", True)):
        out["variation_disable_adaptive_cap"] = 1.0
    return out


def _strict_wire_connectivity_report(
    wire_plan: dict[str, Any],
    geometry_segments: list[WireGeometrySegment],
    endpoint_point: Any,
) -> dict[str, Any]:
    violations: list[dict[str, Any]] = []
    checked_nets = 0
    connected_nets = 0
    routing_mode = _wire_plan_routing_mode(wire_plan)
    label_strategy_count = 0
    unrouted_net_count = 0
    partial_wire_net_count = 0

    segments_by_net: dict[str, list[WireGeometrySegment]] = {}
    for segment in geometry_segments:
        segments_by_net.setdefault(segment.net, []).append(segment)

    for net, net_data in wire_plan.get("nets", {}).items():
        if not isinstance(net_data, dict):
            continue
        net_name = str(net)
        strategy = str(net_data.get("strategy") or "")
        endpoints = [item for item in net_data.get("endpoints", []) if isinstance(item, dict)]
        allowed_wire_terminal_label = _wire_mode_terminal_label_allowed(wire_plan, net_name, strategy)
        if strategy in LABEL_STRATEGIES:
            label_strategy_count += 1
            if routing_mode == "wire" and not allowed_wire_terminal_label:
                violations.append(
                    {
                        "rule": "wire_mode_forbids_terminal_label_strategy",
                        "net": net_name,
                        "strategy": strategy,
                    }
                )
        if strategy.startswith(UNROUTED_STRATEGY_PREFIXES):
            unrouted_net_count += 1
            violations.append(
                {
                    "rule": "expected_net_has_no_complete_wire_route",
                    "net": net_name,
                    "strategy": strategy,
                    "failure_warnings": net_data.get("failure_warnings", []),
                }
            )
            continue
        if len(endpoints) < 2:
            violations.append({"rule": "expected_net_has_fewer_than_two_endpoints", "net": net_name, "strategy": strategy})
            continue
        if strategy == "partial_wire":
            partial_wire_net_count += 1
            violations.append(
                {
                    "rule": "expected_net_has_partial_wire_route",
                    "net": net_name,
                    "strategy": strategy,
                    "unrouted_endpoint_count": net_data.get("unrouted_endpoint_count"),
                    "failure_warnings": net_data.get("failure_warnings", []),
                }
            )
        elif strategy != "wire":
            if routing_mode == "wire" and not allowed_wire_terminal_label:
                violations.append({"rule": "wire_mode_requires_wire_strategy", "net": net_name, "strategy": strategy})
            continue

        checked_nets += 1
        net_segments = segments_by_net.get(net_name, [])
        if not net_segments:
            violations.append({"rule": "expected_net_has_no_wire_segments", "net": net_name})
            continue

        uf = _PointUnionFind()
        for segment in net_segments:
            uf.union(segment.start, segment.end)
        for index, left in enumerate(net_segments):
            for right in net_segments[index + 1 :]:
                for point in _same_net_touch_points(left, right):
                    uf.union(point, left.start)
                    uf.union(point, left.end)
                    uf.union(point, right.start)
                    uf.union(point, right.end)

        endpoint_points: list[tuple[str, tuple[float, float]]] = []
        for endpoint in endpoints:
            point = endpoint_point(endpoint)
            rounded = _round_wire_point(point)
            endpoint_points.append((f"{endpoint.get('ref')}.{endpoint.get('pin')}", rounded))
            touches = [segment for segment in net_segments if _point_on_wire_segment(rounded, segment)]
            if not touches:
                violations.append(
                    {
                        "rule": "endpoint_pin_not_on_any_wire_segment",
                        "net": net_name,
                        "endpoint": endpoint_points[-1][0],
                        "point": [rounded[0], rounded[1]],
                    }
                )
                continue
            for segment in touches:
                uf.union(rounded, segment.start)
                uf.union(rounded, segment.end)

        if endpoint_points:
            roots = {uf.find(point) for _name, point in endpoint_points}
            if len(roots) == 1:
                connected_nets += 1
            else:
                violations.append(
                    {
                        "rule": "net_endpoints_not_connected_by_wire_graph",
                        "net": net_name,
                        "strategy": strategy,
                        "endpoint_count": len(endpoint_points),
                        "component_groups": len(roots),
                        "endpoints": [{"endpoint": name, "point": [point[0], point[1]]} for name, point in endpoint_points[:24]],
                        "endpoints_truncated": len(endpoint_points) > 24,
                    }
                )

    return {
        "schema": "progen-kicad-strict-wire-connectivity-validation/v0.1",
        "stage": "strict_wire_connectivity_validator",
        "routing_mode": routing_mode,
        "ok": not violations,
        "checked_net_count": checked_nets,
        "connected_net_count": connected_nets,
        "label_strategy_count": label_strategy_count,
        "unrouted_net_count": unrouted_net_count,
        "partial_wire_net_count": partial_wire_net_count,
        "violation_count": len(violations),
        "violations": violations[:200],
        "violations_truncated": len(violations) > 200,
    }


def _same_net_touch_points(left: WireGeometrySegment, right: WireGeometrySegment) -> list[tuple[float, float]]:
    points: set[tuple[float, float]] = set()
    for point in (left.start, left.end):
        if _point_on_wire_segment(point, right):
            points.add(_round_wire_point(point))
    for point in (right.start, right.end):
        if _point_on_wire_segment(point, left):
            points.add(_round_wire_point(point))

    left_horizontal = abs(left.start[1] - left.end[1]) <= 0.001
    right_horizontal = abs(right.start[1] - right.end[1]) <= 0.001
    if left_horizontal != right_horizontal:
        horizontal = left if left_horizontal else right
        vertical = right if left_horizontal else left
        candidate = (round(vertical.start[0], 3), round(horizontal.start[1], 3))
        if _point_on_wire_segment(candidate, horizontal) and _point_on_wire_segment(candidate, vertical):
            points.add(candidate)
    return sorted(points, key=lambda item: (item[1], item[0]))


def make_kicad_wires(
    circuit: dict[str, Any],
    placement: CatalogPlacementPlan,
    wire_plan: dict[str, Any],
) -> WireMakerResult:
    routing_mode = _wire_plan_routing_mode(wire_plan)
    library = KiCadSymbolLibrary()
    components = _component_lookup(placement)
    pin_cache: dict[str, tuple[PinGeometry, ...]] = {}
    unit_count_cache: dict[str, int] = {}
    unresolved: list[dict[str, Any]] = []
    endpoint_point_cache: dict[tuple[str, str], tuple[float, float]] = {}
    endpoint_geometry_cache: dict[tuple[str, str], PinGeometry | None] = {}
    resolved_count = 0

    def endpoint_point(endpoint: dict[str, Any]) -> tuple[float, float]:
        nonlocal resolved_count
        ref = str(endpoint.get("ref") or "")
        pin = str(endpoint.get("pin") or "")
        key = (ref, pin)
        if key in endpoint_point_cache:
            return endpoint_point_cache[key]
        point, status, geometry = _resolve_component_pin_point(
            ref=ref,
            pin=pin,
            component=components.get(ref),
            library=library,
            pin_cache=pin_cache,
            unit_count_cache=unit_count_cache,
        )
        if point is None:
            unresolved.append({"ref": ref, "pin": pin, "reason": "component_or_lib_id_missing", "fallback_point": endpoint.get("point")})
            if status != "component_or_lib_id_missing":
                unresolved[-1]["reason"] = status
                component = components.get(ref)
                if component is not None:
                    unresolved[-1]["kind"] = component.kind
            raw_point = endpoint.get("point", [0.0, 0.0])
            fallback = (round(float(raw_point[0]), 3), round(float(raw_point[1]), 3))
            endpoint_geometry_cache[key] = None
            endpoint_point_cache[key] = fallback
            return fallback
        resolved_count += 1
        endpoint_geometry_cache[key] = geometry
        endpoint_point_cache[key] = point
        return point

    def endpoint_side(endpoint: dict[str, Any]) -> str:
        ref = str(endpoint.get("ref") or "")
        pin = str(endpoint.get("pin") or "")
        key = (ref, pin)
        endpoint_point(endpoint)
        geometry = endpoint_geometry_cache.get(key)
        component = components.get(ref)
        if geometry is not None and component is not None:
            side = _pin_side_from_rotation(float(geometry.rotation) + float(component.rotation))
            if side:
                return side
        raw_side = str(endpoint.get("side") or "").lower()
        if raw_side in {"left", "right", "top", "bottom"}:
            return raw_side
        return ""

    segments: list[tuple[tuple[float, float], tuple[float, float]]] = []
    geometry_segments: list[WireGeometrySegment] = []
    labels: list[dict[str, Any]] = []
    used_label_points: dict[tuple[float, float], str] = {}
    route_count = 0
    fallback_route_count = 0
    exact_path_repair_count = 0
    invalid_actual_routes: list[dict[str, Any]] = []
    label_collision_avoidance_count = 0
    deferred_nets: list[str] = []
    unrouted_nets: list[str] = []
    forbidden_label_strategy_nets: list[dict[str, str]] = []

    def add_segments(
        *,
        net: str,
        points: list[tuple[float, float]],
        allowed_touches: tuple[AllowedTouch, ...],
        source: str,
    ) -> None:
        for a, b in _segments_from_points(points):
            segments.append((a, b))
            geometry_segments.append(
                WireGeometrySegment(
                    net=net,
                    start=a,
                    end=b,
                    allowed_touches=allowed_touches,
                    source=source,
                )
            )

    component_bodies = _component_bodies(placement, library)
    visible_text_bodies: list[ComponentBody] = list(_component_text_bodies(placement, library))
    static_visual_obstacles: list[ComponentBody] = [*component_bodies, *visible_text_bodies]
    visual_label_obstacles: list[ComponentBody] = list(static_visual_obstacles)
    label_text_bodies: list[ComponentBody] = []
    protected_pin_points: dict[tuple[float, float], set[str]] = {}
    for net, net_data in wire_plan.get("nets", {}).items():
        if not isinstance(net_data, dict):
            continue
        for endpoint in net_data.get("endpoints", []):
            if not isinstance(endpoint, dict):
                continue
            point = endpoint_point(endpoint)
            protected_pin_points.setdefault((round(point[0], 3), round(point[1], 3)), set()).add(str(net))

    for net, net_data in wire_plan.get("nets", {}).items():
        if not isinstance(net_data, dict):
            continue
        net_name = str(net)
        strategy = str(net_data.get("strategy") or "")
        endpoints = [item for item in net_data.get("endpoints", []) if isinstance(item, dict)]
        if strategy == "deferred_after_route_limit":
            deferred_nets.append(net_name)
            continue
        if strategy.startswith(UNROUTED_STRATEGY_PREFIXES):
            unrouted_nets.append(net_name)
            continue
        if strategy in LABEL_STRATEGIES:
            if routing_mode == "wire" and not _wire_mode_terminal_label_allowed(wire_plan, net_name, strategy):
                forbidden_label_strategy_nets.append({"net": net_name, "strategy": strategy})
                continue
            for endpoint in endpoints:
                pin_point = endpoint_point(endpoint)
                ref = str(endpoint.get("ref") or "")
                side = endpoint_side(endpoint)
                raw_label = _terminal_label_point(pin_point, side)
                label_point, label_moved, label_path = _reserved_label_point(
                    net=net_name,
                    ref=ref,
                    pin_point=pin_point,
                    raw_label=raw_label,
                    side=side,
                    used_label_points=used_label_points,
                    existing_segments=geometry_segments,
                    component_bodies=component_bodies,
                    protected_pin_points=protected_pin_points,
                    visual_obstacle_bodies=visual_label_obstacles,
                )
                if label_moved:
                    label_collision_avoidance_count += 1
                if label_point != pin_point:
                    add_segments(
                        net=net_name,
                        points=label_path,
                        allowed_touches=(AllowedTouch(str(endpoint.get("ref") or ""), pin_point),),
                        source=f"{net_name}:local_label:{endpoint.get('ref')}.{endpoint.get('pin')}",
                    )
                label_justify = _label_justify(pin_point, label_point, side)
                labels.append({"net": net_name, "at": label_point, "justify": label_justify})
                label_body = _text_body(
                    owner=f"__label_text__{net_name}__{ref}__{endpoint.get('pin')}",
                    text=net_name,
                    at=label_point,
                    justify=label_justify,
                    source="generated_terminal_label",
                    font_mm=TERMINAL_LABEL_FONT_MM,
                )
                label_text_bodies.append(label_body)
                visual_label_obstacles.append(label_body)
            continue
        for route in net_data.get("routes", []):
            if not isinstance(route, dict):
                continue
            raw_from = route.get("from", {})
            raw_to = route.get("to", {})
            start = endpoint_point(raw_from)
            end = endpoint_point(raw_to)
            path = _path_with_actual_ends(start, route.get("path", []), end)
            from_ref = str(raw_from.get("ref") or "") if isinstance(raw_from, dict) else ""
            to_ref = str(raw_to.get("ref") or "") if isinstance(raw_to, dict) else ""
            allowed_touches = (AllowedTouch(from_ref, start), AllowedTouch(to_ref, end))
            path, path_repaired, path_valid = _validated_actual_path(
                net=net_name,
                original=path,
                start=start,
                end=end,
                allowed_touches=allowed_touches,
                existing_segments=geometry_segments,
                component_bodies=component_bodies,
                protected_pin_points=protected_pin_points,
                source=f"{net_name}:{from_ref}->{to_ref}",
            )
            if not path_valid:
                invalid_actual_routes.append(
                    {
                        "net": net_name,
                        "from": f"{from_ref}.{raw_from.get('pin')}" if isinstance(raw_from, dict) else from_ref,
                        "to": f"{to_ref}.{raw_to.get('pin')}" if isinstance(raw_to, dict) else to_ref,
                        "reason": "no_geometry_clean_actual_path_candidate",
                    }
                )
                continue
            if path_repaired:
                exact_path_repair_count += 1
            add_segments(
                net=net_name,
                points=path,
                allowed_touches=allowed_touches,
                source=f"{net_name}:{from_ref}->{to_ref}",
            )
            route_count += 1
            if len(path) >= 3 and route.get("path"):
                planned_start = tuple(route["path"][0])
                planned_end = tuple(route["path"][-1])
                if start != planned_start or end != planned_end:
                    fallback_route_count += 1

    raw_segment_count = len(geometry_segments)
    # Do not collapse same-net collinear pieces yet. A naive merge can create a
    # long span through component bodies or across other nets even when the
    # original routed pieces were valid.
    protected_points = {
        (round(allowed.point[0], 3), round(allowed.point[1], 3))
        for segment in geometry_segments
        for allowed in segment.allowed_touches
    }
    protected_points.update((round(float(label["at"][0]), 3), round(float(label["at"][1]), 3)) for label in labels)
    geometry_segments, trimmed_wire_tail_count = _trim_dangling_wire_tails(geometry_segments, protected_points)
    segments = [(segment.start, segment.end) for segment in geometry_segments]
    merged_segment_count = 0
    junctions = _insert_junctions(geometry_segments)
    geometry_report = validate_wire_geometry(geometry_segments, component_bodies)
    label_visual_layout = _label_visual_layout_report(label_text_bodies, static_visual_obstacles)
    strict_wire_report = _strict_wire_connectivity_report(wire_plan, geometry_segments, endpoint_point)
    if invalid_actual_routes:
        strict_wire_report = dict(strict_wire_report)
        violations = list(strict_wire_report.get("violations", []))
        violations.extend(
            {
                "rule": "wire_maker_rejected_invalid_actual_route",
                "net": item["net"],
                "from": item["from"],
                "to": item["to"],
                "reason": item["reason"],
            }
            for item in invalid_actual_routes[: max(0, 200 - len(violations))]
        )
        strict_wire_report["ok"] = False
        strict_wire_report["violation_count"] = int(strict_wire_report.get("violation_count", 0)) + len(invalid_actual_routes)
        strict_wire_report["violations"] = violations[:200]
        strict_wire_report["violations_truncated"] = bool(strict_wire_report.get("violations_truncated")) or len(violations) > 200
    project_name = str(circuit.get("project", {}).get("name") or circuit.get("circuit_id") or "wired")
    objects: list[str] = []
    for index, (a, b) in enumerate(segments, 1):
        objects.append(wire_obj(a, b, project_name, index))
    for index, point in enumerate(junctions, 1):
        objects.append(junction_obj(point, project_name, index))
    for index, label in enumerate(labels, 1):
        objects.append(
            text_obj(
                str(label["net"]),
                label["at"],
                project_name,
                index,
                "label",
                str(label["justify"]),
                font_size=TERMINAL_LABEL_FONT_MM,
            )
        )

    report = {
        "schema": "progen-kicad-wire-maker-report/v0.1",
        "stage": "kicad_wire_maker",
        "version": WIRE_MAKER_VERSION,
        "routing_mode": routing_mode,
        "terminal_label_pin_offset_mm": TERMINAL_LABEL_PIN_OFFSET_MM,
        "terminal_label_font_mm": TERMINAL_LABEL_FONT_MM,
        "wire_object_count": len(segments),
        "raw_wire_segment_count": raw_segment_count,
        "merged_wire_segment_count": merged_segment_count,
        "trimmed_wire_tail_count": trimmed_wire_tail_count,
        "label_count": len(labels),
        "junction_count": len(junctions),
        "routed_connection_count": route_count,
        "pin_resolved_count": resolved_count,
        "unresolved_pin_count": len(unresolved),
        "unresolved_pins": unresolved[:200],
        "unresolved_pin_report_truncated": len(unresolved) > 200,
        "fallback_route_count": fallback_route_count,
        "exact_path_repair_count": exact_path_repair_count,
        "invalid_actual_route_count": len(invalid_actual_routes),
        "invalid_actual_routes": invalid_actual_routes[:200],
        "invalid_actual_routes_truncated": len(invalid_actual_routes) > 200,
        "forbidden_label_strategy_count": len(forbidden_label_strategy_nets),
        "forbidden_label_strategy_nets": forbidden_label_strategy_nets[:200],
        "forbidden_label_strategy_report_truncated": len(forbidden_label_strategy_nets) > 200,
        "wire_mode_terminal_policy": wire_plan.get("wire_mode_terminal_policy", {}),
        "wire_mode_terminal_label_count": sum(
            1
            for net, net_data in wire_plan.get("nets", {}).items()
            if isinstance(net_data, dict)
            and _wire_mode_terminal_label_allowed(wire_plan, str(net), str(net_data.get("strategy") or ""))
        ),
        "label_collision_avoidance_count": label_collision_avoidance_count,
        "label_visual_layout": label_visual_layout,
        "deferred_net_count": len(deferred_nets),
        "deferred_nets": deferred_nets,
        "unrouted_net_count": len(unrouted_nets),
        "unrouted_nets": unrouted_nets,
        "partial_wire_net_count": int(strict_wire_report.get("partial_wire_net_count", 0)),
        "geometry_ok": bool(geometry_report["ok"]),
        "geometry_violation_count": int(geometry_report["violation_count"]),
        "wire_geometry_validator": geometry_report,
        "strict_wire_ok": bool(strict_wire_report["ok"]) if routing_mode == "wire" else True,
        "strict_wire_violation_count": int(strict_wire_report["violation_count"]),
        "strict_wire_validator": strict_wire_report,
        "partial_route_motion_repair": wire_plan.get("partial_route_motion_repair", {}),
        "wire_planner_metrics": wire_plan.get("metrics", {}),
        "wire_planner_warning_count": len(wire_plan.get("warnings", [])),
    }
    return WireMakerResult("".join(objects), report)


def _geometry_violation_net_sets(report: dict[str, Any]) -> list[set[str]]:
    groups: list[set[str]] = []
    for violation in report.get("wire_geometry_validator", {}).get("violations", []):
        if not isinstance(violation, dict):
            continue
        nets: set[str] = set()
        for key in ("segment", "left", "right", "left_segment", "right_segment"):
            segment = violation.get(key)
            if isinstance(segment, dict) and segment.get("net"):
                nets.add(str(segment["net"]))
        if nets:
            groups.append(nets)
    return groups


def _geometry_violation_nets(report: dict[str, Any]) -> set[str]:
    remaining = _geometry_violation_net_sets(report)
    chosen: set[str] = set()
    while remaining:
        counts: dict[str, int] = {}
        for group in remaining:
            for net in group:
                counts[net] = counts.get(net, 0) + 1
        if not counts:
            break
        best = sorted(counts, key=lambda net: (-counts[net], net))[0]
        chosen.add(best)
        remaining = [group for group in remaining if best not in group]
    return chosen


def _invalid_actual_route_nets(report: dict[str, Any]) -> set[str]:
    nets: set[str] = set()
    for item in report.get("invalid_actual_routes", []):
        if isinstance(item, dict) and item.get("net"):
            nets.add(str(item["net"]))
    return nets


def _wire_plan_with_geometry_fallbacks(wire_plan: dict[str, Any], fallback_nets: set[str]) -> dict[str, Any]:
    repaired = deepcopy(wire_plan)
    nets = repaired.get("nets", {})
    if not isinstance(nets, dict):
        return repaired
    for net in sorted(fallback_nets):
        net_data = nets.get(net)
        if not isinstance(net_data, dict):
            continue
        endpoints = net_data.get("endpoints", [])
        failure_warnings = list(net_data.get("failure_warnings", [])) if isinstance(net_data.get("failure_warnings"), list) else []
        failure_warnings.append("combination_terminal_fallback: net converted to local labels after route geometry or emitter validation failure.")
        nets[net] = {
            "strategy": "local_labels_after_geometry_violation",
            "endpoints": endpoints if isinstance(endpoints, list) else [],
            "routes": [],
            "failure_warnings": failure_warnings[:20],
        }

    routes = [route for route in repaired.get("routes", []) if isinstance(route, dict) and str(route.get("net")) not in fallback_nets]
    repaired["routes"] = routes
    repaired.setdefault("warnings", [])
    if isinstance(repaired["warnings"], list):
        repaired["warnings"].append(
            "geometry_repair_fallback: converted nets to local labels: " + ", ".join(sorted(fallback_nets))
        )
    metrics = repaired.setdefault("metrics", {})
    if isinstance(metrics, dict):
        metrics["wired_route_count"] = len(routes)
        metrics["segment_count"] = sum(len(route.get("segments", [])) for route in routes if isinstance(route, dict))
        metrics["combination_terminal_fallback_net_count"] = len(fallback_nets)
        metrics["label_strategy_count"] = sum(
            1 for item in nets.values() if isinstance(item, dict) and item.get("strategy") in LABEL_STRATEGIES
        )
    return repaired


def repair_wire_plan_geometry(
    circuit: dict[str, Any],
    placement: CatalogPlacementPlan,
    wire_plan: dict[str, Any],
    *,
    max_passes: int = 6,
) -> tuple[dict[str, Any], WireMakerResult]:
    repaired_plan = deepcopy(wire_plan)
    repair_passes: list[dict[str, Any]] = []
    already_fallback: set[str] = set()
    result = make_kicad_wires(circuit, placement, repaired_plan)
    if _wire_plan_routing_mode(wire_plan) == "wire":
        result.report["geometry_repair_pass_count"] = 0
        result.report["geometry_repair_passes"] = []
        result.report["geometry_repair_fallback_nets"] = []
        result.report["geometry_repair_fallback_disabled"] = "strict wire mode forbids conversion of failed wires to terminal/local-label strategy"
        return repaired_plan, result
    for pass_index in range(1, max_passes + 1):
        if result.report["geometry_ok"] and int(result.report.get("invalid_actual_route_count", 0)) == 0:
            break
        fallback_nets = (_geometry_violation_nets(result.report) | _invalid_actual_route_nets(result.report)) - already_fallback
        if not fallback_nets:
            break
        repair_passes.append(
            {
                "pass": pass_index,
                "fallback_nets": sorted(fallback_nets),
                "geometry_violation_count_before": result.report["geometry_violation_count"],
                "invalid_actual_route_count_before": result.report.get("invalid_actual_route_count", 0),
            }
        )
        already_fallback.update(fallback_nets)
        repaired_plan = _wire_plan_with_geometry_fallbacks(repaired_plan, fallback_nets)
        result = make_kicad_wires(circuit, placement, repaired_plan)
    result.report["geometry_repair_pass_count"] = len(repair_passes)
    result.report["geometry_repair_passes"] = repair_passes
    result.report["geometry_repair_fallback_nets"] = sorted(already_fallback)
    return repaired_plan, result


def _pin_coordinate_overlap_report(
    placement: CatalogPlacementPlan,
    library: KiCadSymbolLibrary,
) -> dict[str, Any]:
    """Detect coincident endpoints across every source-backed symbol pin."""

    by_point: dict[tuple[float, float], list[dict[str, str]]] = {}
    for component in placement.components:
        lib_id = component.spec.lib_id
        if not lib_id:
            continue
        symbol = library.load(lib_id)
        geometries = _pin_geometries(symbol.text)
        unit_count = len(symbol.unit_pin_numbers) if symbol.unit_pin_numbers else 1
        for geometry in geometries:
            point = _pin_world(component, geometry, unit_count)
            key = (round(point[0], 3), round(point[1], 3))
            pin_id = geometry.name or geometry.number
            by_point.setdefault(key, []).append(
                {"ref": component.ref, "pin": pin_id, "number": geometry.number, "unit": str(geometry.unit)}
            )
    overlaps: list[dict[str, Any]] = []
    for point, members in by_point.items():
        refs = {member["ref"] for member in members}
        if len(refs) <= 1:
            continue
        overlaps.append({"point": [point[0], point[1]], "members": members})
    return {
        "schema": "progen-kicad-pin-coordinate-overlap-report/v0.1",
        "ok": not overlaps,
        "overlap_count": len(overlaps),
        "overlaps": overlaps[:200],
        "overlaps_truncated": len(overlaps) > 200,
    }


def _pin_body_clearance_report(
    placement: CatalogPlacementPlan,
    library: KiCadSymbolLibrary,
    *,
    clearance_mm: float = PIN_TO_FOREIGN_BODY_CLEARANCE_MM,
) -> dict[str, Any]:
    """Reject a source pin that is inside or too close to another symbol body.

    Body-to-body checks alone are insufficient for multi-unit symbols: a
    supply pin may extend beyond its unit body and end inside a neighbouring
    connector even when the two body rectangles have a gap.  Such a pin has
    no legal path for either a wire or a terminal stub, so placement must
    repair it before routing begins.
    """

    bodies = _component_bodies(placement, library)
    conflicts: list[dict[str, Any]] = []
    for component in placement.components:
        lib_id = component.spec.lib_id
        if not lib_id:
            continue
        symbol = library.load(lib_id)
        geometries = _pin_geometries(symbol.text)
        unit_count = len(symbol.unit_pin_numbers) if symbol.unit_pin_numbers else 1
        for geometry in geometries:
            point = _pin_world(component, geometry, unit_count)
            for body in bodies:
                if body.ref == component.ref:
                    continue
                if not (
                    body.left - clearance_mm < point[0] < body.right + clearance_mm
                    and body.top - clearance_mm < point[1] < body.bottom + clearance_mm
                ):
                    continue
                inside_body = (
                    body.left <= point[0] <= body.right
                    and body.top <= point[1] <= body.bottom
                )
                conflicts.append(
                    {
                        "pin_ref": component.ref,
                        "pin_number": geometry.number,
                        "pin_name": geometry.name,
                        "pin_unit": geometry.unit,
                        "point": [round(point[0], 3), round(point[1], 3)],
                        "body_ref": body.ref,
                        "body_source": body.source,
                        "body": {
                            "left": body.left,
                            "top": body.top,
                            "right": body.right,
                            "bottom": body.bottom,
                        },
                        "inside_body": inside_body,
                    }
                )
    return {
        "schema": "progen-kicad-pin-foreign-body-clearance-report/v0.1",
        "ok": not conflicts,
        "clearance_mm": clearance_mm,
        "conflict_count": len(conflicts),
        "conflicts": conflicts[:200],
        "conflicts_truncated": len(conflicts) > 200,
    }


def _nudge_actual_pin_overlap(
    placement_dict: dict[str, Any],
    routing_placement: dict[str, Any],
    pin_report: dict[str, Any],
) -> tuple[dict[str, Any] | None, dict[str, Any] | None]:
    """Separate one coincident pair of source-derived pin endpoints."""

    overlaps = pin_report.get("overlaps", [])
    components = placement_dict.get("components", {})
    obstacles = routing_placement.get("obstacles", [])
    if not isinstance(overlaps, list) or not overlaps or not isinstance(components, dict) or not isinstance(obstacles, list):
        return None, None
    members = overlaps[0].get("members", []) if isinstance(overlaps[0], dict) else []
    if not isinstance(members, list) or len(members) < 2:
        return None, None
    refs = sorted({str(member.get("ref") or "") for member in members if isinstance(member, dict)})
    if len(refs) < 2 or any(ref not in components for ref in refs[:2]):
        return None, None
    bodies_per_ref: dict[str, int] = {}
    for item in obstacles:
        if isinstance(item, dict):
            ref = str(item.get("component_ref") or "")
            bodies_per_ref[ref] = bodies_per_ref.get(ref, 0) + 1
    move_ref = min(refs[:2], key=lambda ref: (bodies_per_ref.get(ref, 1), ref))
    fixed_ref = refs[1] if move_ref == refs[0] else refs[0]
    moving_raw = components.get(move_ref)
    fixed_raw = components.get(fixed_ref)
    if not isinstance(moving_raw, dict) or not isinstance(fixed_raw, dict):
        return None, None
    if bool(moving_raw.get("manual", False)):
        if bool(fixed_raw.get("manual", False)):
            return None, None
        move_ref, fixed_ref = fixed_ref, move_ref
        moving_raw, fixed_raw = fixed_raw, moving_raw
    moving_at = moving_raw.get("at")
    fixed_at = fixed_raw.get("at")
    if not isinstance(moving_at, list) or not isinstance(fixed_at, list) or len(moving_at) < 2 or len(fixed_at) < 2:
        return None, None
    dx = float(moving_at[0]) - float(fixed_at[0])
    dy = float(moving_at[1]) - float(fixed_at[1])
    if abs(dy) >= abs(dx):
        delta = (0.0, 10.16 if dy >= 0 else -10.16)
    else:
        delta = (10.16 if dx >= 0 else -10.16, 0.0)
    repaired = deepcopy(placement_dict)
    repaired["components"][move_ref]["at"] = [
        round(float(moving_at[0]) + delta[0], 3),
        round(float(moving_at[1]) + delta[1], 3),
    ]
    return repaired, {
        "status": "source_pin_coordinate_nudge",
        "moved_ref": move_ref,
        "delta": [delta[0], delta[1]],
        "conflict_members": members,
    }
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
