ProGenEDA/ProGenEDA-DEV/Easyeda/native.py

"""Native EasyEDA Pro SQLite project emitter."""

from __future__ import annotations

from concurrent.futures import ThreadPoolExecutor
from dataclasses import dataclass
from datetime import datetime, timezone
from itertools import chain
import json
from pathlib import Path
import shutil
import sqlite3
from typing import Any, Iterable
import uuid

from .donor_source import DonorPacket, EasyedaDonorSource
from .geometry import (
    PlacedComponent,
    Point,
    Rect,
    RoutedNet,
    WireSpanIndex,
    _candidate_paths,
    _path_is_compact,
    _visibility_route,
    inflate,
    points_to_segments,
    rects_overlap,
    rotate_point,
    segment_hits_rect,
    simplify_points,
)
from .ir import Circuit


NATIVE_SCHEMA = "progen-easyeda-native-project/v1"


class NativeProjectError(RuntimeError):
    """A donor-native project cannot be emitted without unsupported guessing."""


@dataclass(frozen=True)
class TerminalInstance:
    net: str
    endpoint: str
    packet: DonorPacket
    x: float
    y: float
    rotation: int
    wire_points: tuple[Point, ...]


@dataclass(frozen=True)
class PcbResult:
    ready: bool
    reason: str
    document_data: str | None
    component_count: int
    track_count: int
    placements: dict[str, tuple[float, float]]
    pad_points: dict[str, Point]
    variations: tuple[dict[str, Any], ...] = ()


@dataclass(frozen=True)
class NativeWriteResult:
    project_path: Path
    schematic_document_uuid: str
    pcb_document_uuid: str | None
    terminal_instances: tuple[TerminalInstance, ...]
    pcb: PcbResult
    donor_manifest: dict[str, Any]


class _Ids:
    def __init__(self) -> None:
        self.value = 0

    def next(self, prefix: str = "e") -> str:
        self.value += 1
        return f"{prefix}{self.value}"


def _record(row: list[Any]) -> str:
    return json.dumps(row, ensure_ascii=False, separators=(",", ":"))


def _records(text: str) -> list[list[Any]]:
    result: list[list[Any]] = []
    for line in text.splitlines():
        if not line.strip():
            continue
        value = json.loads(line)
        if isinstance(value, list) and value:
            result.append(value)
    return result


def _base_records(template_path: Path, doc_type: int) -> list[list[Any]]:
    with sqlite3.connect(template_path) as connection:
        row = connection.execute(
            "SELECT dataStr FROM documents WHERE docType = ? ORDER BY length(dataStr) DESC LIMIT 1",
            (doc_type,),
        ).fetchone()
    if row is None:
        raise NativeProjectError(f"Donor template contains no document type {doc_type}.")
    return _records(str(row[0]))


def _schematic_prelude(template_path: Path) -> list[list[Any]]:
    source = _base_records(template_path, 1)
    prelude: list[list[Any]] = []
    seen_styles: set[str] = set()
    for row in source:
        if row[0] in {"DOCTYPE", "HEAD"}:
            prelude.append(row)
        elif row[0] in {"LINESTYLE", "FONTSTYLE"}:
            identifier = str(row[1])
            if identifier not in seen_styles:
                prelude.append(row)
                seen_styles.add(identifier)
        if len(prelude) >= 14:
            break
    if not prelude or prelude[0][0] != "DOCTYPE":
        raise NativeProjectError("Donor schematic has no native document prelude.")
    return prelude


def _pcb_prelude(template_path: Path) -> list[list[Any]]:
    source = _base_records(template_path, 3)
    prelude: list[list[Any]] = []
    for row in source:
        if row[0] == "NET":
            break
        if row[0] in {"DOCTYPE", "CANVAS", "LAYER"}:
            prelude.append(row)
    if not prelude or prelude[0][0] != "DOCTYPE":
        raise NativeProjectError("Donor PCB has no native document prelude.")
    return prelude


def _style(prelude: Iterable[list[Any]], kind: str, fallback: str) -> str:
    for row in prelude:
        if row[0] == kind and len(row) > 1:
            return str(row[1])
    return fallback


def _endpoint_map(placed: tuple[PlacedComponent, ...]) -> dict[str, tuple[PlacedComponent, str, Point]]:
    result: dict[str, tuple[PlacedComponent, str, Point]] = {}
    for item in placed:
        for requested, point in item.pins.items():
            result[f"{item.component.reference}.{requested}"] = (item, requested, point)
    return result


def _terminal_orientation(item: PlacedComponent, point: Point) -> tuple[str, int, Point]:
    left, top, right, bottom = item.body
    outside = {
        "left": left - point[0],
        "right": point[0] - right,
        "top": top - point[1],
        "bottom": point[1] - bottom,
    }
    outside = {
        side: amount
        for side, amount in outside.items()
        if amount > 0
    }
    distances = {
        "left": abs(point[0] - left),
        "right": abs(point[0] - right),
        "top": abs(point[1] - top),
        "bottom": abs(point[1] - bottom),
    }
    side = max(outside, key=outside.get) if outside else min(distances, key=distances.get)
    if side == "left":
        return "in", 0, (min(point[0], left) - 96.0, point[1])
    if side == "right":
        return "out", 0, (max(point[0], right) + 96.0, point[1])
    if side == "top":
        return "out", 270, (point[0], min(point[1], top) - 96.0)
    return "out", 90, (point[0], max(point[1], bottom) + 96.0)


def _build_terminals(
    source: EasyedaDonorSource,
    routed: tuple[RoutedNet, ...],
    placed: tuple[PlacedComponent, ...],
) -> tuple[TerminalInstance, ...]:
    endpoints = _endpoint_map(placed)
    packets: dict[str, DonorPacket] = {}
    result: list[TerminalInstance] = []
    component_obstacles: list[Rect] = [inflate(item.body, 8.0) for item in placed]
    terminal_rects: list[Rect] = []
    terminal_wires: list[tuple[str, Point, Point]] = []
    pin_keepouts = {
        endpoint: (point[0] - 5.0, point[1] - 5.0, point[0] + 5.0, point[1] + 5.0)
        for endpoint, (_, _, point) in endpoints.items()
    }
    route_segments = [
        (net.name, start, end)
        for net in routed
        for start, end in net.segments
    ]
    wire_spans = WireSpanIndex()
    for route_net, start, end in route_segments:
        wire_spans.add(route_net, start, end)
    component_envelope = (
        min(rect[0] for rect in component_obstacles),
        min(rect[1] for rect in component_obstacles),
        max(rect[2] for rect in component_obstacles),
        max(rect[3] for rect in component_obstacles),
    )
    component_pin_envelopes: dict[str, Rect] = {}
    for item, body in zip(placed, component_obstacles):
        related = [
            keepout
            for endpoint, keepout in pin_keepouts.items()
            if endpoint.startswith(f"{item.component.reference}.")
        ]
        component_pin_envelopes[item.component.reference] = (
            min([body[0], *(rect[0] for rect in related)]),
            min([body[1], *(rect[1] for rect in related)]),
            max([body[2], *(rect[2] for rect in related)]),
            max([body[3], *(rect[3] for rect in related)]),
        )

    def terminal_rect(packet: DonorPacket, point: Point, rotation: int) -> Rect:
        body_left, body_top, body_right, body_bottom = packet.body_bbox
        local = [
            rotate_point((body_left, body_top), rotation),
            rotate_point((body_right, body_top), rotation),
            rotate_point((body_right, body_bottom), rotation),
            rotate_point((body_left, body_bottom), rotation),
        ]
        return (
            min(point[0] + value[0] for value in local),
            min(point[1] + value[1] for value in local),
            max(point[0] + value[0] for value in local),
            max(point[1] + value[1] for value in local),
        )

    def segment_enters_terminal_rect(
        start: Point,
        end: Point,
        rect: Rect,
    ) -> bool:
        interior = (
            rect[0] + 1e-6,
            rect[1] + 1e-6,
            rect[2] - 1e-6,
            rect[3] - 1e-6,
        )
        return (
            interior[0] < interior[2]
            and interior[1] < interior[3]
            and segment_hits_rect(start, end, interior)
        )

    def placement_candidates(
        point: Point,
        target: Point,
        rotation: int,
    ) -> Iterable[tuple[Point, tuple[Point, ...]]]:
        horizontal = rotation in {0, 180}
        outward_sign = (
            1.0
            if (horizontal and target[0] >= point[0])
            or (not horizontal and target[1] >= point[1])
            else -1.0
        )
        if horizontal:
            pivot = (point[0] + 8.0 * outward_sign, point[1])
            assigned_points = (
                point,
                pivot,
                (pivot[0], target[1]),
                target,
            )
        else:
            pivot = (point[0], point[1] + 8.0 * outward_sign)
            assigned_points = (
                point,
                pivot,
                (target[0], pivot[1]),
                target,
            )
        yield target, assigned_points
        if horizontal:
            alternate_assigned_points = (
                point,
                pivot,
                (target[0], pivot[1]),
                target,
            )
        else:
            alternate_assigned_points = (
                point,
                pivot,
                (pivot[0], target[1]),
                target,
            )
        yield target, alternate_assigned_points
        for lane_offset in (12.0, -12.0, 24.0, -24.0):
            if horizontal:
                lane = target[1] + lane_offset
                approach = target[0] - outward_sign * 6.0
                lane_points = (
                    point,
                    pivot,
                    (pivot[0], lane),
                    (approach, lane),
                    (approach, target[1]),
                    target,
                )
            else:
                lane = target[0] + lane_offset
                approach = target[1] - outward_sign * 6.0
                lane_points = (
                    point,
                    pivot,
                    (lane, pivot[1]),
                    (lane, approach),
                    (target[0], approach),
                    target,
                )
            yield target, lane_points
        for shift in (
            12.0,
            -12.0,
            18.0,
            -18.0,
            24.0,
            -24.0,
            36.0,
            -36.0,
            48.0,
            -48.0,
            60.0,
            -60.0,
            72.0,
            -72.0,
            96.0,
            -96.0,
            120.0,
            -120.0,
            144.0,
            -144.0,
            180.0,
            -180.0,
            216.0,
            -216.0,
            240.0,
            -240.0,
        ):
            for distance in (
                32.0,
                40.0,
                48.0,
                56.0,
                72.0,
                88.0,
                104.0,
                120.0,
                152.0,
                184.0,
                216.0,
                248.0,
            ):
                if horizontal:
                    pivot = (point[0] + 8.0 * outward_sign, point[1])
                    candidate = (
                        point[0] + distance * outward_sign,
                        point[1] + shift,
                    )
                    points = (
                        point,
                        pivot,
                        (pivot[0], candidate[1]),
                        candidate,
                    )
                else:
                    pivot = (point[0], point[1] + 8.0 * outward_sign)
                    candidate = (
                        point[0] + shift,
                        point[1] + distance * outward_sign,
                    )
                    points = (
                        point,
                        pivot,
                        (candidate[0], pivot[1]),
                        candidate,
                    )
                yield candidate, points
        for distance in (24.0, 32.0, 40.0, 48.0):
            candidate = (
                (point[0] + distance * outward_sign, point[1])
                if horizontal
                else (point[0], point[1] + distance * outward_sign)
            )
            yield candidate, (point, candidate)
        for radial_step in range(80):
            radial = radial_step * 30.0 * outward_sign
            if horizontal:
                candidate = (target[0] + radial, target[1])
                escape = (
                    candidate[0] - outward_sign * 16.0,
                    point[1],
                )
                points = (point, escape, (escape[0], candidate[1]), candidate)
            else:
                candidate = (target[0], target[1] + radial)
                escape = (
                    point[0],
                    candidate[1] - outward_sign * 16.0,
                )
                points = (point, escape, (candidate[0], escape[1]), candidate)
            yield candidate, points
        for shift_step in range(1, 41):
            for shift_sign in (1.0, -1.0):
                shift = shift_step * 18.0 * shift_sign
                for radial_step in range(24):
                    radial = radial_step * 30.0 * outward_sign
                    if horizontal:
                        candidate = (
                            target[0] + radial,
                            target[1] + shift,
                        )
                        escape = (
                            candidate[0] - outward_sign * 16.0,
                            point[1],
                        )
                        points = (
                            point,
                            escape,
                            (escape[0], candidate[1]),
                            candidate,
                        )
                    else:
                        candidate = (
                            target[0] + shift,
                            target[1] + radial,
                        )
                        escape = (
                            point[0],
                            candidate[1] - outward_sign * 16.0,
                        )
                        points = (
                            point,
                            escape,
                            (candidate[0], escape[1]),
                            candidate,
                        )
                    yield candidate, points

    def point_in_rect(point: Point, rect: Rect) -> bool:
        return rect[0] <= point[0] <= rect[2] and rect[1] <= point[1] <= rect[3]

    def path_is_clear(points: tuple[Point, ...], obstacles: list[Rect]) -> bool:
        for start, end in points_to_segments(points):
            for obstacle in obstacles:
                if not segment_hits_rect(start, end, obstacle):
                    continue
                if start == point and point_in_rect(point, obstacle):
                    continue
                return False
        return True

    def path_reuses_other_net(points: tuple[Point, ...], net_name: str) -> bool:
        return wire_spans.overlaps(points_to_segments(points), net_name)

    def terminal_body_hits_wire(
        rect: Rect,
        candidate: Point,
        net_name: str,
    ) -> bool:
        return any(
            segment_enters_terminal_rect(start, end, rect)
            for wire_net, start, end in (*route_segments, *terminal_wires)
            if wire_net != net_name
            or not (start == candidate or end == candidate)
        )

    def path_enters_own_terminal_body(
        points: tuple[Point, ...],
        rect: Rect,
        candidate: Point,
    ) -> bool:
        return any(
            segment_enters_terminal_rect(start, end, rect)
            and start != candidate
            and end != candidate
            for start, end in points_to_segments(points)
        )

    def normalize_terminal_approach(
        points: tuple[Point, ...],
        rect: Rect,
        candidate: Point,
    ) -> tuple[Point, ...] | None:
        if not path_enters_own_terminal_body(points, rect, candidate):
            return points
        anchor_index = next(
            (
                index
                for index in range(len(points) - 2, -1, -1)
                if not point_in_rect(points[index], rect)
            ),
            None,
        )
        if anchor_index is None:
            return None
        anchor = points[anchor_index]
        left, top, right, bottom = rect
        if anchor[0] < left:
            corner = (anchor[0], candidate[1])
            approach = (left - 6.0, candidate[1])
        elif anchor[0] > right:
            corner = (anchor[0], candidate[1])
            approach = (right + 6.0, candidate[1])
        elif anchor[1] < top:
            corner = (candidate[0], anchor[1])
            approach = (candidate[0], top - 6.0)
        elif anchor[1] > bottom:
            corner = (candidate[0], anchor[1])
            approach = (candidate[0], bottom + 6.0)
        else:
            return None
        normalized = simplify_points(
            (*points[: anchor_index + 1], corner, approach, candidate)
        )
        if path_enters_own_terminal_body(normalized, rect, candidate):
            return None
        return normalized

    component_order = {
        item.component.reference: index
        for index, item in enumerate(placed)
    }
    requests: list[tuple[RoutedNet, str, PlacedComponent, Point, str, int, Point]] = []
    for net in routed:
        if not net.terminalized:
            continue
        terminal_endpoints = (
            net.endpoints[:1]
            if net.reason == "shared_power_terminal"
            else net.endpoints
        )
        for endpoint in terminal_endpoints:
            binding = endpoints.get(endpoint)
            if binding is None:
                continue
            item, _, point = binding
            direction, rotation, target = _terminal_orientation(item, point)
            requests.append((net, endpoint, item, point, direction, rotation, target))

    grouped: dict[
        tuple[str, str, int, int],
        list[tuple[RoutedNet, str, PlacedComponent, Point, str, int, Point]],
    ] = {}
    for request in requests:
        _, _, item, point, direction, rotation, target = request
        sign = 1 if (
            (rotation in {0, 180} and target[0] >= point[0])
            or (rotation not in {0, 180} and target[1] >= point[1])
        ) else -1
        grouped.setdefault(
            (item.component.reference, direction, rotation, sign),
            [],
        ).append(request)

    assigned_targets: dict[tuple[str, str], Point] = {}
    for (_, _, rotation, sign), group in grouped.items():
        horizontal = rotation in {0, 180}
        ordered = sorted(
            group,
            key=lambda request: (
                request[3][1] if horizontal else request[3][0],
                request[1],
            ),
        )
        coordinates = [
            request[3][1] if horizontal else request[3][0]
            for request in ordered
        ]
        center = sum(coordinates) / len(coordinates)
        spacing = 18.0
        slots = [
            center + (index - (len(ordered) - 1) / 2.0) * spacing
            for index in range(len(ordered))
        ]
        outward = (
            (max(request[6][0] for request in ordered) if sign > 0 else min(request[6][0] for request in ordered))
            if horizontal
            else (max(request[6][1] for request in ordered) if sign > 0 else min(request[6][1] for request in ordered))
        )
        for request, slot in zip(ordered, slots):
            assigned_targets[(request[0].name, request[1])] = (
                (outward, slot) if horizontal else (slot, outward)
            )

    reserved_terminal_zones: dict[str, Rect] = {}
    for net, endpoint, _, _, direction, rotation, _ in requests:
        terminal_packet = packets.setdefault(
            direction,
            source.resolve_terminal_port(direction=direction),
        )
        reserved_terminal_zones[endpoint] = terminal_rect(
            terminal_packet,
            assigned_targets[(net.name, endpoint)],
            rotation,
        )
    terminal_group_sizes = {
        request[1]: len(group)
        for group in grouped.values()
        for request in group
    }
    endpoint_group_keys = {
        request[1]: group_key
        for group_key, group in grouped.items()
        for request in group
    }
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
