ProGenEDA/ProGenEDA-DEV/kicad/pipeline/wire_planner.py

"""Pure JSON wire planner.

The wire planner is EDA-agnostic. It consumes:

1. placement JSON with component centers and obstacle boxes
2. CircuitIR-style JSON with component pins / net connections

It emits two JSON contracts:

1. coordinate-plan JSON for the beautifier
2. wire-plan JSON for a later KiCad/Proteus-specific wire maker
"""

from __future__ import annotations

import heapq
import json
import os
import time
from concurrent.futures import ThreadPoolExecutor, as_completed
from collections import Counter, defaultdict
from dataclasses import dataclass
from pathlib import Path
from typing import Any

from .arrangement_decider import DEFAULT_ARRANGEMENT_CONFIG, GROUND_NETS, POWER_NETS, decide_arrangement, extract_connection_nets
from .beautifier import apply_coordinate_edits


Point = tuple[float, float]
GridPoint = tuple[int, int]


@dataclass(frozen=True)
class Body:
    ref: str
    left: float
    top: float
    right: float
    bottom: float
    component_ref: str | None = None

    @property
    def center(self) -> Point:
        return ((self.left + self.right) / 2, (self.top + self.bottom) / 2)

    def contains(self, point: Point, clearance: float = 0.0) -> bool:
        x, y = point
        return self.left - clearance <= x <= self.right + clearance and self.top - clearance <= y <= self.bottom + clearance


ROUTING_MODES = {"wire", "terminal", "combination"}
WIRE_MODE_TERMINAL_LABEL_STRATEGY = "wire_mode_terminal_label"
LABEL_STRATEGIES = {
    "local_labels",
    "single_endpoint_label",
    "local_labels_after_router_failure",
    "local_labels_after_geometry_violation",
    WIRE_MODE_TERMINAL_LABEL_STRATEGY,
}

DEFAULT_WIRE_CONFIG: dict[str, Any] = {
    "routing_mode": "wire",
    "grid": 2.54,
    "sheet_width": 420.0,
    "sheet_height": 297.0,
    "margin": 15.24,
    "clearance": 2.54,
    "pin_stub": 5.08,
    "wire_spacing": 2.54,
    "turn_penalty": 0.15,
    "near_wire_penalty": 0.0,
    "occupied_wire_penalty": 50.0,
    "strict_occupied_wire_penalty": 2000.0,
    "perpendicular_crossing_step_penalty": 0.0,
    "block_collinear_existing_wires": 0.0,
    "forbid_wire_turn_on_occupied": 0.0,
    "block_existing_wires": 0.0,
    "max_astar_expansions": 50_000.0,
    "strict_fallback_max_astar_expansions": 50_000.0,
    "max_wired_routes": 10_000.0,
    "lane_router": 1.0,
    "lane_step": 7.62,
    "max_lane_candidates": 256.0,
    "crossing_penalty": 0.0,
    "forbidden_contact_penalty": 250_000.0,
    "strict_forbidden_contact_filter": 0.0,
    "density_tile_size": 25.4,
    "max_crossings_per_tile_soft": 6.0,
    "same_net_reuse_penalty": 0.05,
    "body_crossing_penalty": 100_000.0,
    "component_shadow_penalty": 80.0,
    "component_shadow_clearance": 12.7,
    "long_lane_threshold": 80.0,
    "long_lane_outer_penalty": 12.0,
    "exact_crossing_score_segment_limit": 5000.0,
    "exact_contact_score_operation_limit": 60000.0,
    "body_grid_score_component_limit": 80.0,
    "dense_design_component_limit": 90.0,
    "dense_max_lane_candidates": 256.0,
    "dense_max_astar_expansions": 1500.0,
    "max_failed_endpoints_per_net": 1000.0,
    "dense_max_failed_endpoints_per_net": 1000.0,
    "dense_force_grid_contact_scoring": 0.0,
    "dense_skip_astar_when_lane_candidate": 1.0,
    "crossing_risk_astar": 0.0,
    "lane_zero_crossing_fast_accept": 1.0,
    "arrangement_variant_search": 1.0,
    "max_arrangement_variants": 5.0,
    "arrangement_variant_workers": 0.0,
    "arrangement_variant_parallel_min_components": 40.0,
    "arrangement_variant_max_astar_expansions": 600.0,
    "arrangement_variant_max_lane_candidates": 32.0,
    "arrangement_variant_max_failed_endpoints_per_net": 1.0,
    "arrangement_variant_max_root_candidates": 1.0,
    "arrangement_final_wire_route": 1.0,
    "max_root_candidates_per_endpoint": 3.0,
    "max_endpoint_retry_attempts": 4.0,
    "salvage_astar_expansions": 200_000.0,
    "max_salvage_astar_attempts": 12.0,
    "max_partial_route_component_moves": 8.0,
    "partial_route_move_search_steps": 14.0,
    "partial_route_move_body_clearance": 0.0,
    "partial_route_move_min_pin_gap": 10.16,
    "partial_route_move_include_unroutable": 1.0,
    "partial_route_motion_moves_per_pass": 1.0,
    "strict_partial_route_repair_passes": 8.0,
    "priority_nets": (),
    "terminal_nets": (),
    "wire_mode_terminal_power_ground": 0.0,
    "wire_mode_terminal_high_fanout_threshold": 0.0,
    "combination_terminal_high_fanout_threshold": 6.0,
}


def normalize_routing_mode(value: object) -> str:
    mode = str(value or "wire").strip().lower().replace("-", "_")
    if mode not in ROUTING_MODES:
        raise ValueError(f"Unsupported routing_mode {value!r}; expected one of: {', '.join(sorted(ROUTING_MODES))}")
    return mode


def _wire_config(config: dict[str, Any] | None, circuit: dict[str, Any] | None = None) -> dict[str, Any]:
    cfg = dict(DEFAULT_WIRE_CONFIG)
    explicit_strict_fallback_budget = False
    circuit_mode = None
    if isinstance(circuit, dict):
        raw_routing = circuit.get("routing")
        if isinstance(raw_routing, dict):
            circuit_mode = raw_routing.get("mode")
    if circuit_mode:
        cfg["routing_mode"] = circuit_mode
    if config:
        explicit_strict_fallback_budget = "strict_fallback_max_astar_expansions" in config
        for key, value in config.items():
            if key in {"routing_mode", "priority_nets", "terminal_nets", "wire_mode_terminal_policy"}:
                cfg[key] = value
            else:
                cfg[key] = float(value)
    cfg["routing_mode"] = normalize_routing_mode(cfg.get("routing_mode"))
    if not explicit_strict_fallback_budget:
        cfg["strict_fallback_max_astar_expansions"] = float(cfg.get("max_astar_expansions", 50_000.0))
    return cfg


def _snap(value: float, grid: float) -> float:
    return round(round(value / grid) * grid, 3)


def _round_point(point: Point) -> Point:
    return (round(point[0], 3), round(point[1], 3))


def _bodies(placement: dict[str, Any]) -> dict[str, Body]:
    bodies: dict[str, Body] = {}
    for item in placement.get("obstacles", []):
        if isinstance(item, dict) and item.get("owner"):
            owner = str(item["owner"])
            bodies[owner] = Body(
                owner,
                float(item.get("left", 0.0)),
                float(item.get("top", 0.0)),
                float(item.get("right", 0.0)),
                float(item.get("bottom", 0.0)),
                str(item.get("component_ref") or owner),
            )
    components = placement.get("components", {})
    if isinstance(components, dict):
        for ref, component in components.items():
            if not isinstance(component, dict):
                continue
            if ref in bodies or any(body.component_ref == str(ref) for body in bodies.values()):
                continue
            at = component.get("at", [0.0, 0.0])
            if not isinstance(at, (list, tuple)) or len(at) < 2:
                at = [0.0, 0.0]
            width = float(component.get("width", 10.0))
            height = float(component.get("height", 8.0))
            x = float(at[0])
            y = float(at[1])
            bodies[str(ref)] = Body(str(ref), x - width / 2, y - height / 2, x + width / 2, y + height / 2, str(ref))
    return bodies


def _sheet_bounds(bodies: dict[str, Body], cfg: dict[str, float]) -> tuple[float, float]:
    max_right = max((body.right for body in bodies.values()), default=cfg["sheet_width"])
    max_bottom = max((body.bottom for body in bodies.values()), default=cfg["sheet_height"])
    return (max(cfg["sheet_width"], max_right + cfg["margin"]), max(cfg["sheet_height"], max_bottom + cfg["margin"]))


def _body_for_component(ref: str, bodies: dict[str, Body], point: Point | None = None) -> Body | None:
    candidates = [body for body in bodies.values() if body.ref == ref or body.component_ref == ref]
    if not candidates:
        return None
    if point is None:
        return candidates[0]
    return min(
        candidates,
        key=lambda body: (
            0 if body.contains(point, 0.001) else 1,
            abs(body.center[0] - point[0]) + abs(body.center[1] - point[1]),
        ),
    )


def _body_center_x(ref: str, bodies: dict[str, Body]) -> float | None:
    body = _body_for_component(ref, bodies)
    return body.center[0] if body else None


def _side_from_pin_point(point: Point, body: Body | None, net: str) -> str:
    if body is None:
        return "right"
    if point[0] < body.left:
        return "left"
    if point[0] > body.right:
        return "right"
    if point[1] < body.top:
        return "top"
    if point[1] > body.bottom:
        return "bottom"
    distances = {
        "left": abs(point[0] - body.left),
        "right": abs(point[0] - body.right),
        "top": abs(point[1] - body.top),
        "bottom": abs(point[1] - body.bottom),
    }
    return min(distances.items(), key=lambda item: item[1])[0]


def _pin_point_lookup(placement: dict[str, Any]) -> dict[tuple[str, str], dict[str, Any]]:
    raw = placement.get("pin_points") or {}
    out: dict[tuple[str, str], dict[str, Any]] = {}
    if isinstance(raw, dict):
        for ref, pins in raw.items():
            if not isinstance(pins, dict):
                continue
            for pin, data in pins.items():
                if not isinstance(data, dict):
                    continue
                point = data.get("point")
                if isinstance(point, (list, tuple)) and len(point) >= 2:
                    key = (str(ref), str(pin))
                    item = dict(data)
                    item["point"] = [float(point[0]), float(point[1])]
                    out[key] = item
                    out[(key[0], key[1].upper())] = item
    elif isinstance(raw, list):
        for data in raw:
            if not isinstance(data, dict):
                continue
            ref = str(data.get("ref") or "")
            pin = str(data.get("pin") or "")
            point = data.get("point")
            if ref and pin and isinstance(point, (list, tuple)) and len(point) >= 2:
                item = dict(data)
                item["point"] = [float(point[0]), float(point[1])]
                out[(ref, pin)] = item
                out[(ref, pin.upper())] = item
    return out


def _side_for_endpoint(net: str, ref: str, refs: list[str], bodies: dict[str, Body]) -> str:
    upper = net.upper()
    if upper in POWER_NETS:
        return "top"
    if upper in GROUND_NETS:
        return "bottom"
    body = _body_for_component(ref, bodies)
    if body is None:
        return "right"
    others = [center_x for other in refs if other != ref and (center_x := _body_center_x(other, bodies)) is not None]
    if not others:
        return "right"
    return "right" if sum(others) / len(others) >= body.center[0] else "left"
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
