ProGenEDA/ProGenEDA-DEV/Easyeda/pipeline.py

"""End-to-end donor-native EasyEDA generation pipeline."""

from __future__ import annotations

from concurrent.futures import ThreadPoolExecutor
from dataclasses import asdict
from datetime import datetime
import json
from pathlib import Path
from typing import Any, Callable, Mapping
import zipfile

from .catalogue import CATALOGUE_VERSION, get_entry
from .donor_source import DonorPacket, EasyedaDonorSource, bundled_source_pack
from .geometry import place_components, route_nets
from .input_fixer import repair_circuit_input
from .ir import Circuit, load_circuit
from .native import NativeWriteResult, write_project
from .validator import ValidationResult, validate_native_project
from .value_editor import normalize_circuit_values


PIPELINE_SCHEMA = "progen-easyeda-pipeline/v1"
ProgressCallback = Callable[[dict[str, Any]], None]


class PipelineError(RuntimeError):
    """Generation did not satisfy the selected mode's release contract."""


def _json(path: Path, value: object) -> None:
    path.write_text(
        json.dumps(value, ensure_ascii=False, indent=2, sort_keys=True) + "\n",
        encoding="utf-8",
    )


def _new_run_directory(output_root: Path, name: str) -> Path:
    timestamp = datetime.now().strftime("%Y_%m_%d_%H%M%S_%f")
    candidate = output_root / f"{timestamp}_{name}"
    suffix = 1
    while candidate.exists():
        candidate = output_root / f"{timestamp}_{name}_v{suffix}"
        suffix += 1
    candidate.mkdir(parents=True)
    return candidate


def _resolve_packets(
    source: EasyedaDonorSource,
    circuit: Circuit,
) -> dict[str, DonorPacket]:
    unique = {component.kind: get_entry(component.kind) for component in circuit.components}
    workers = min(8, max(1, len(unique)))
    with ThreadPoolExecutor(max_workers=workers, thread_name_prefix="easyeda-donor") as executor:
        futures = {
            kind: executor.submit(source.resolve, entry)
            for kind, entry in unique.items()
        }
        by_kind = {kind: future.result() for kind, future in futures.items()}
    return {
        component.identifier: by_kind[component.kind]
        for component in circuit.components
    }
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
